CollectiveOpenSourceHardware/LibreSolarBox/batterycase/celltypes/CALB_CAM72/cam72_calb3.png

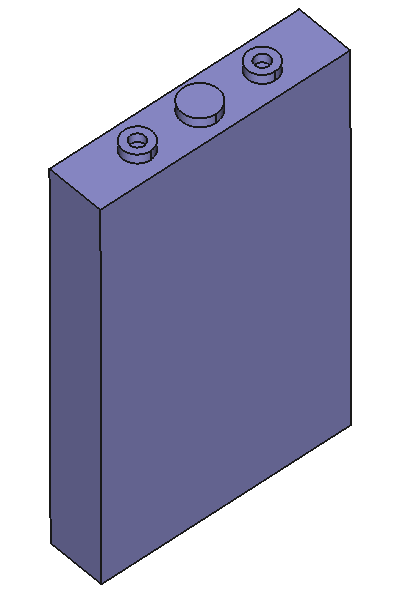
batterycase/celltypes/CALB_CAM72/cam72_calb3.png
