CollectiveOpenSourceHardware/LibreSolarBox/batterycase/celltypes/CALB_CAM72/cam72_calb3_dimensions.png

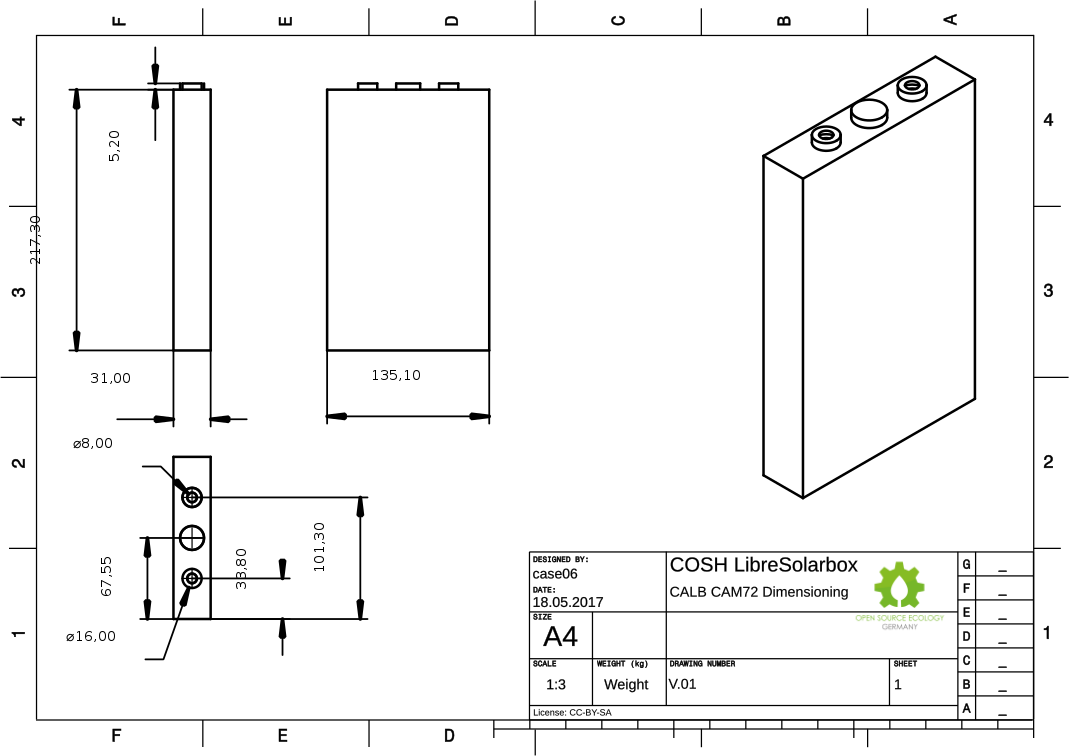
batterycase/celltypes/CALB_CAM72/cam72_calb3_dimensions.png
