CollectiveOpenSourceHardware/LibreSolarBox/batterycase/drawingtemplates/A4_LandscapeTD_cosh.png

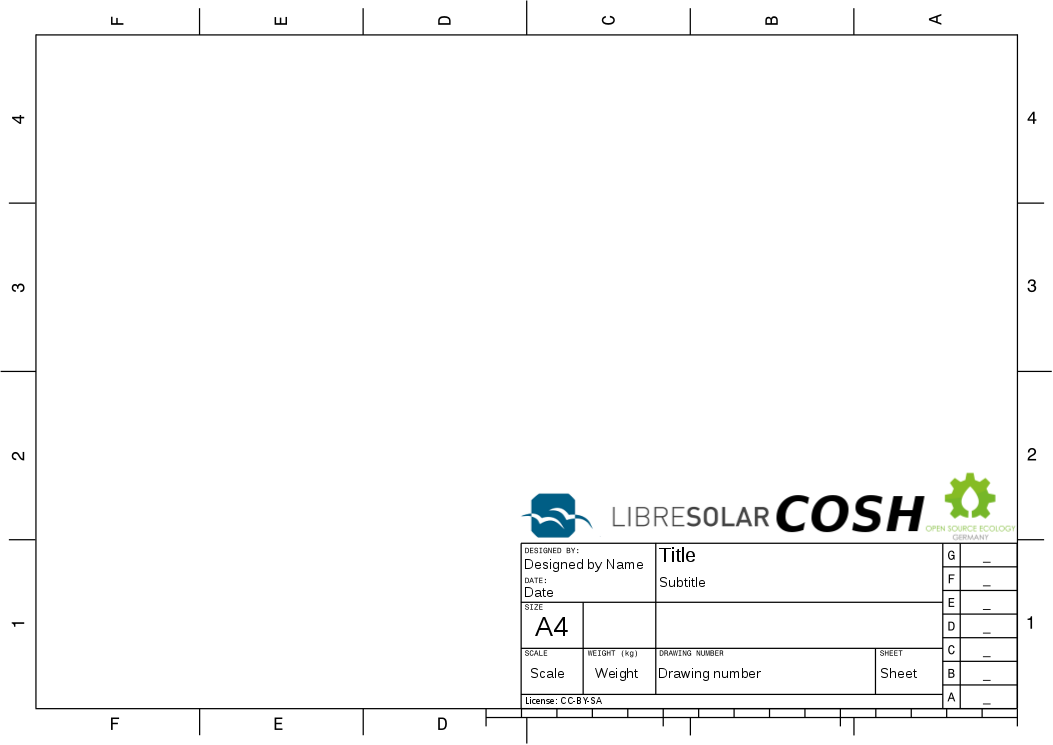
batterycase/drawingtemplates/A4_LandscapeTD_cosh.png
