CollectiveOpenSourceHardware/LibreSolarBox/boxframe/images/IMG_20170920_190103.jpg

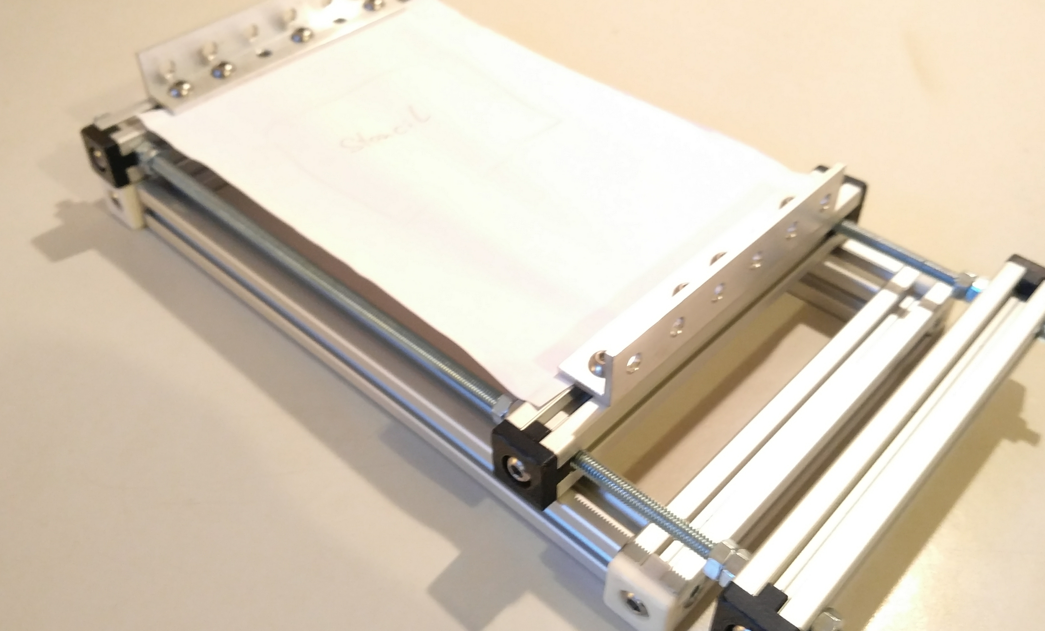
boxframe/images/IMG_20170920_190103.jpg
