CollectiveOpenSourceHardware/LibreSolarBox/boxframe/images/IMG_20170920_190120.jpg

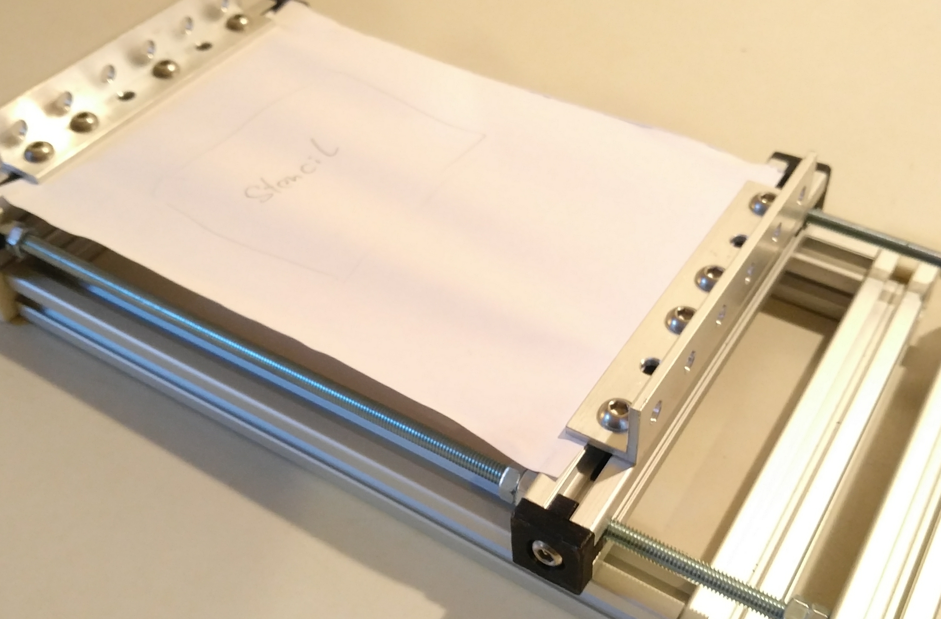
boxframe/images/IMG_20170920_190120.jpg
