CollectiveOpenSourceHardware/LibreSolarBox/boxframe/images/IMG_20170920_190156.jpg

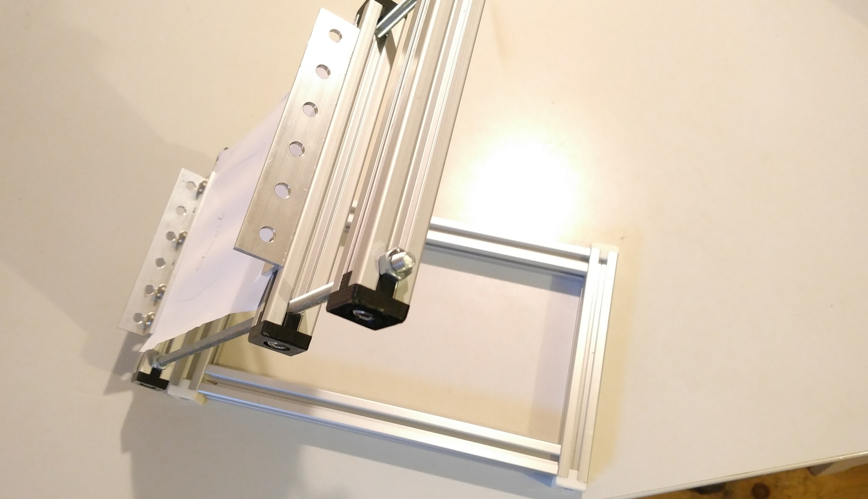
boxframe/images/IMG_20170920_190156.jpg
