CollectiveOpenSourceHardware/LibreSolarBox/boxframe/images/IMG_20170920_190223.jpg

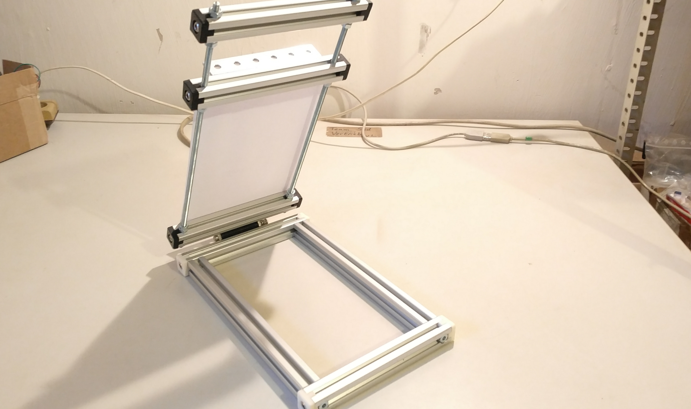
boxframe/images/IMG_20170920_190223.jpg
