CollectiveOpenSourceHardware/LibreSolarBox/boxframe/images/IMG_20170920_190235.jpg

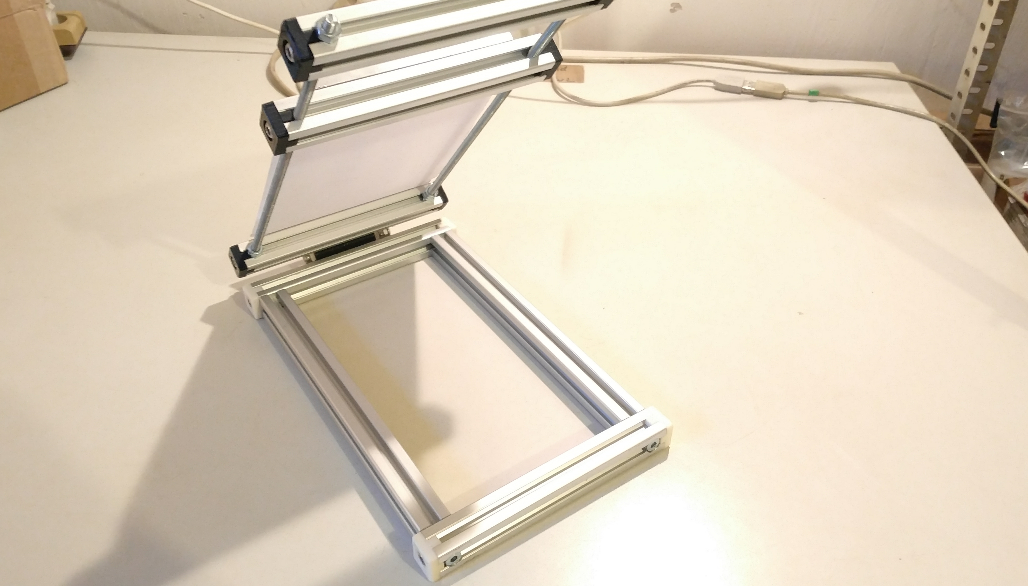
boxframe/images/IMG_20170920_190235.jpg
