CollectiveOpenSourceHardware/LibreSolarBox/boxframe/images/IMG_20170920_190249.jpg

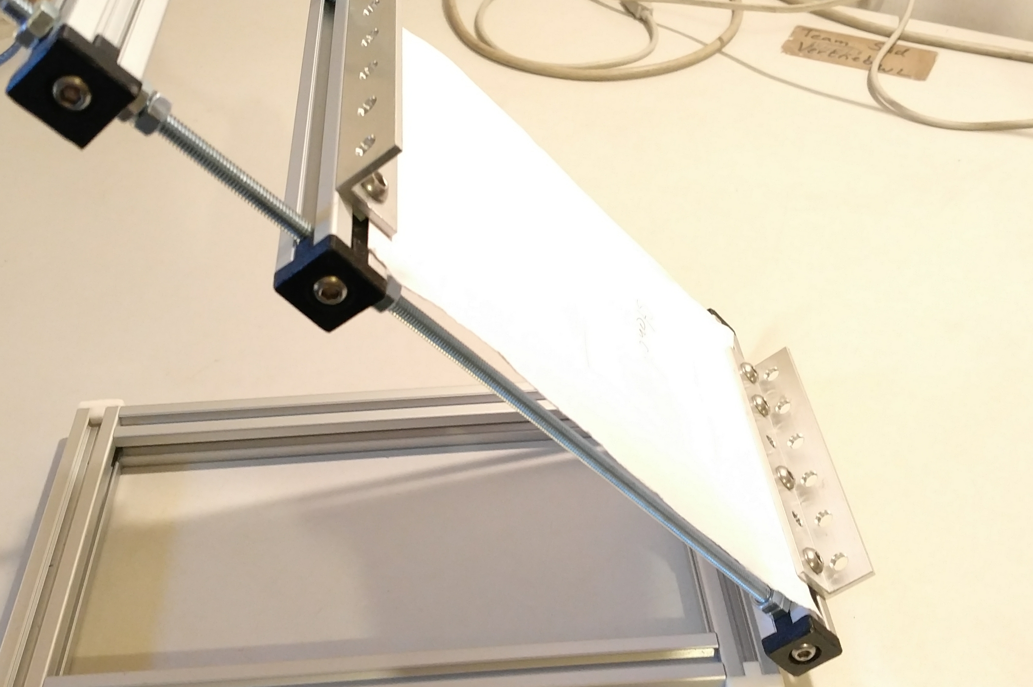
boxframe/images/IMG_20170920_190249.jpg
