CollectiveOpenSourceHardware/LibreSolarBox/boxframe/images/IMG_20170920_190312.jpg

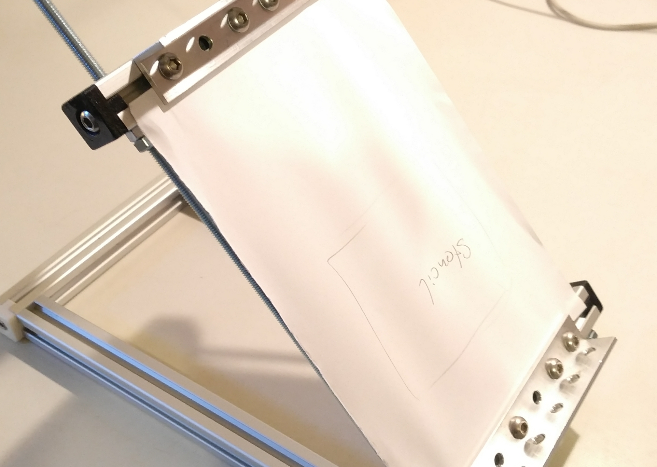
boxframe/images/IMG_20170920_190312.jpg
