CollectiveOpenSourceHardware/LibreSolarBox/boxframe/images/IMG_20170920_190359.jpg

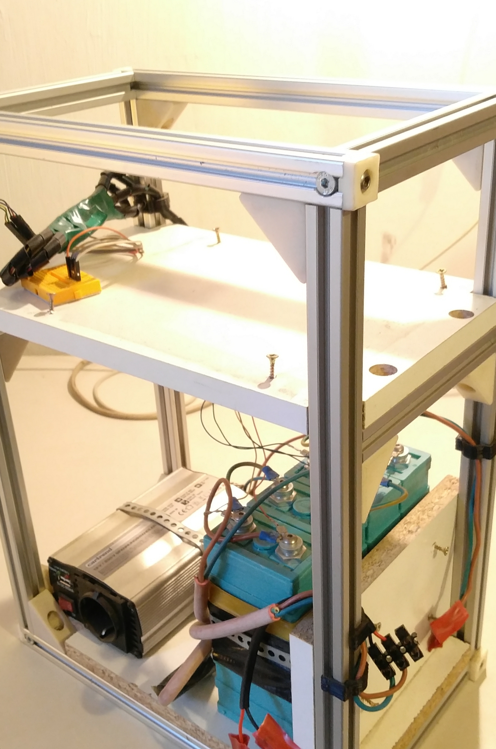
boxframe/images/IMG_20170920_190359.jpg
