CollectiveOpenSourceHardware/LibreSolarBox/boxframe/images/IMG_20170920_190408.jpg

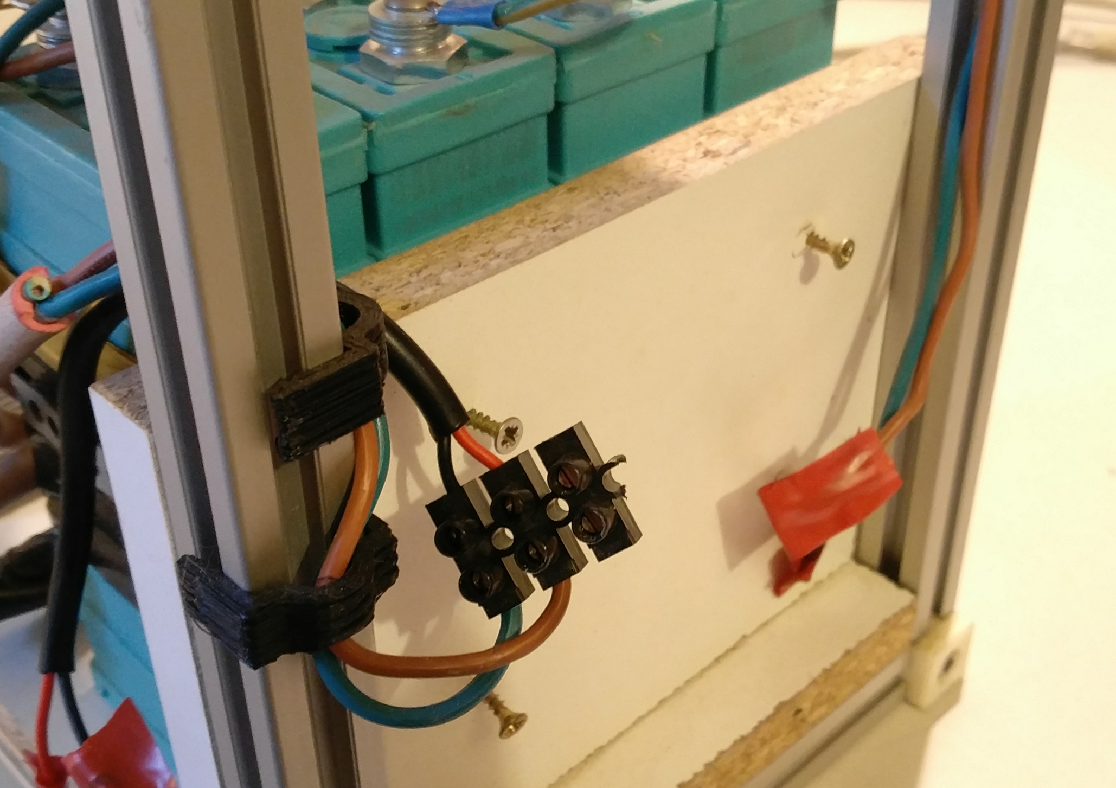
boxframe/images/IMG_20170920_190408.jpg
