CollectiveOpenSourceHardware/LibreSolarBox/boxframe/images/IMG_20170920_190428.jpg

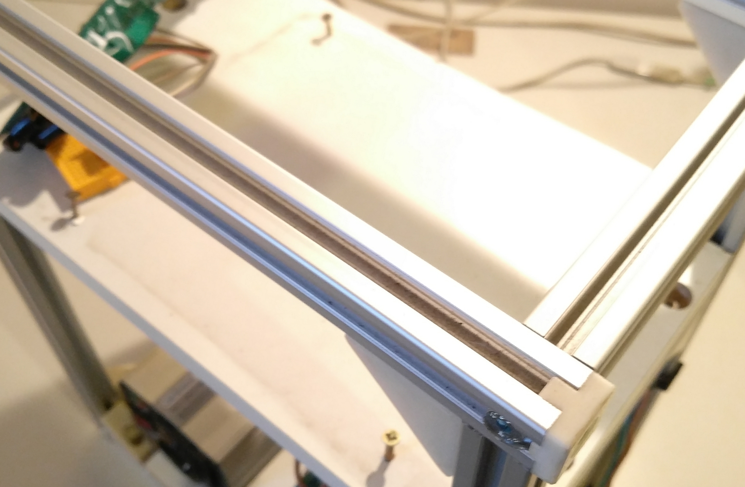
boxframe/images/IMG_20170920_190428.jpg
