CollectiveOpenSourceHardware/LibreSolarBox/boxframe/images/IMG_20170920_190441.jpg

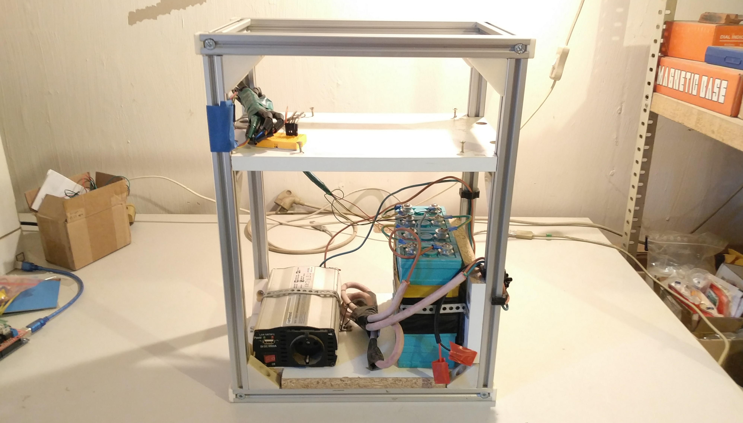
boxframe/images/IMG_20170920_190441.jpg
