CollectiveOpenSourceHardware/LibreSolarBox/boxframe/panelsupport/screw_tslot2.png

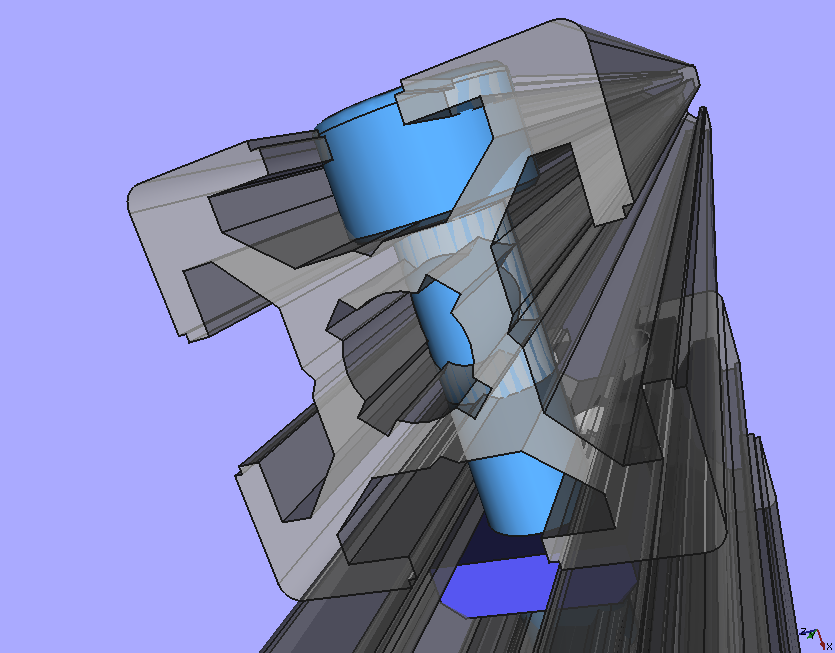
boxframe/panelsupport/screw_tslot2.png
