CollectiveOpenSourceHardware/LibreSolarBox/boxframe/panelsupport/screw_tslot3.png

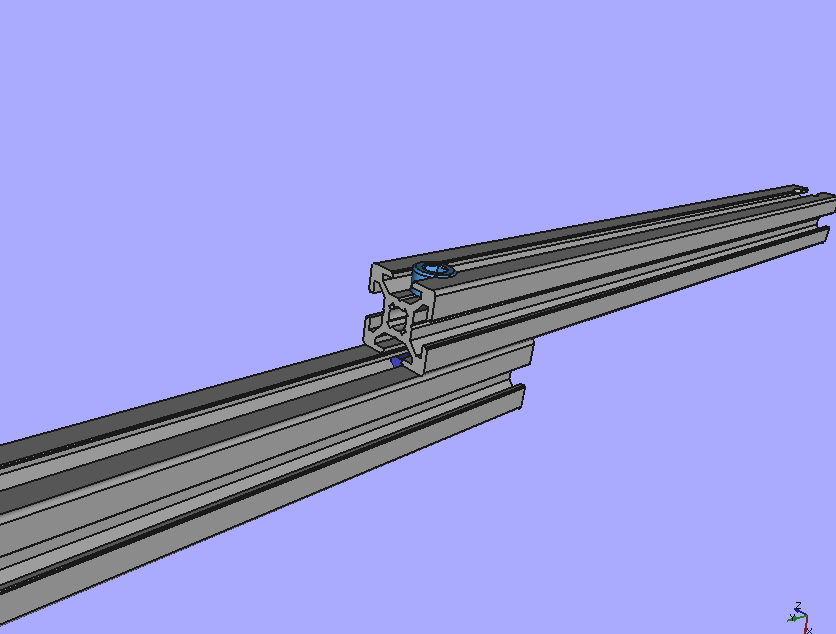
boxframe/panelsupport/screw_tslot3.png
