CollectiveOpenSourceHardware/LibreSolarBox/boxframe/panelsupport/screw_tslot.png

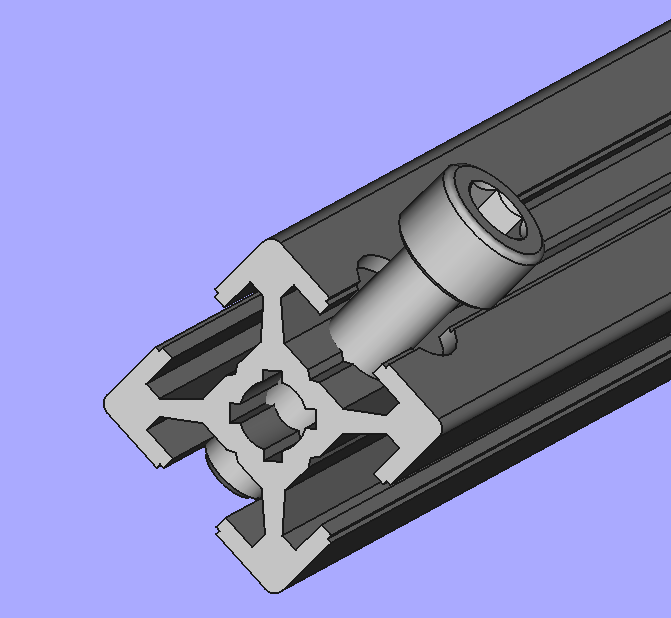
boxframe/panelsupport/screw_tslot.png
