CollectiveOpenSourceHardware/LibreSolarBox/boxframe/upkframe_v6/images/batterymount1c.png

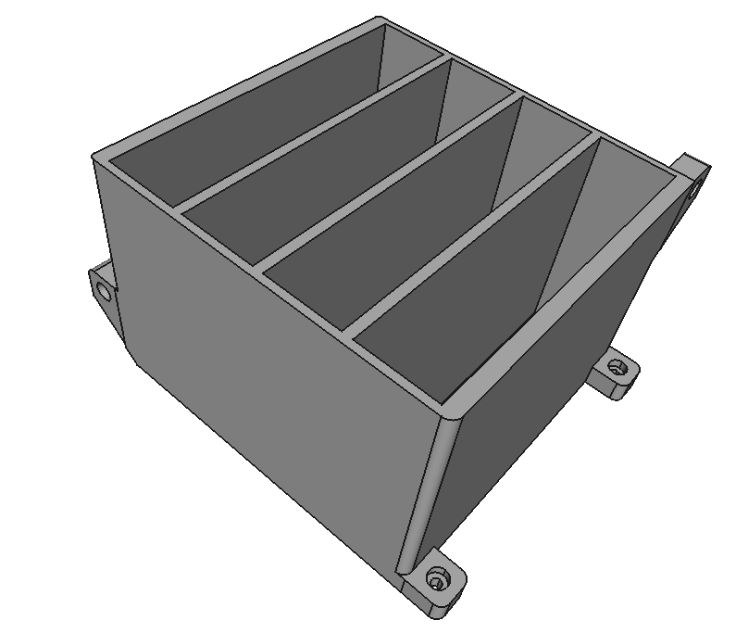
boxframe/upkframe_v6/images/batterymount1c.png
