CollectiveOpenSourceHardware/LibreSolarBox/boxframe/upkframe_v6/images/batterymount_top_0.1.PNG

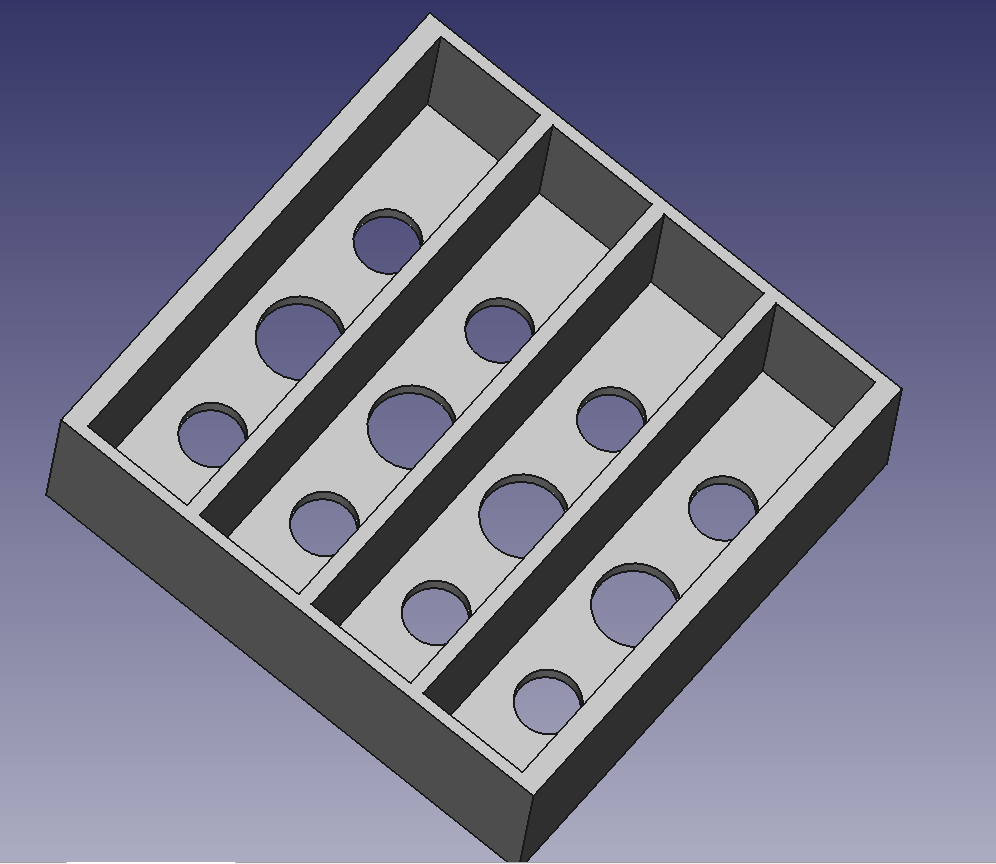
boxframe/upkframe_v6/images/batterymount_top_0.1.PNG
