CollectiveOpenSourceHardware/LibreSolarBox/boxframe/upkframe_v6/images/frontback_dim.png

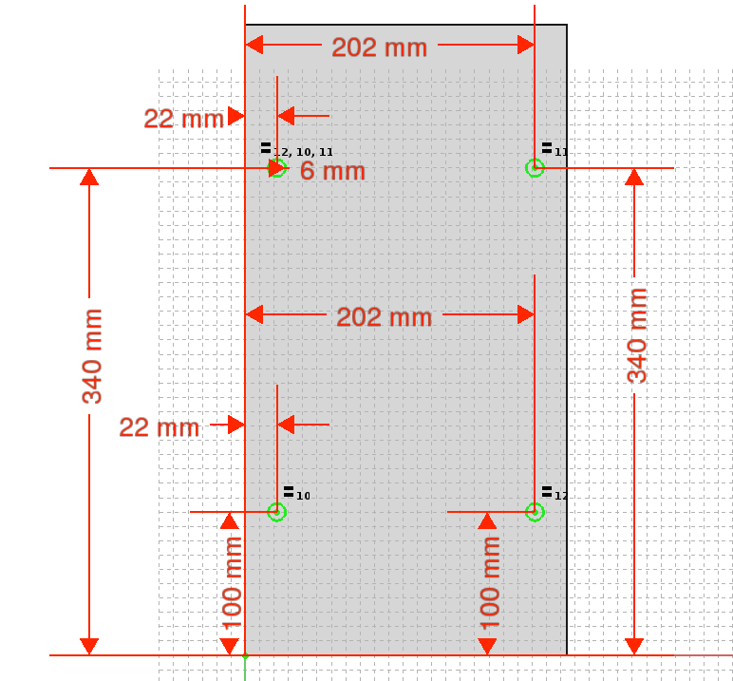
boxframe/upkframe_v6/images/frontback_dim.png
