CollectiveOpenSourceHardware/LibreSolarBox/boxframe/upkframe_v6/images/frontback_ifmount_closeup.png

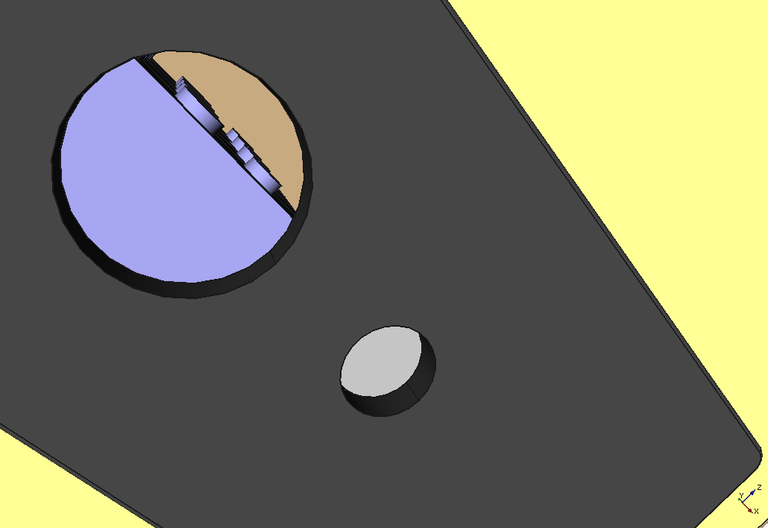
boxframe/upkframe_v6/images/frontback_ifmount_closeup.png
