CollectiveOpenSourceHardware/LibreSolarBox/boxframe/upkframe_v6/images/frontback_ifmount_front.png

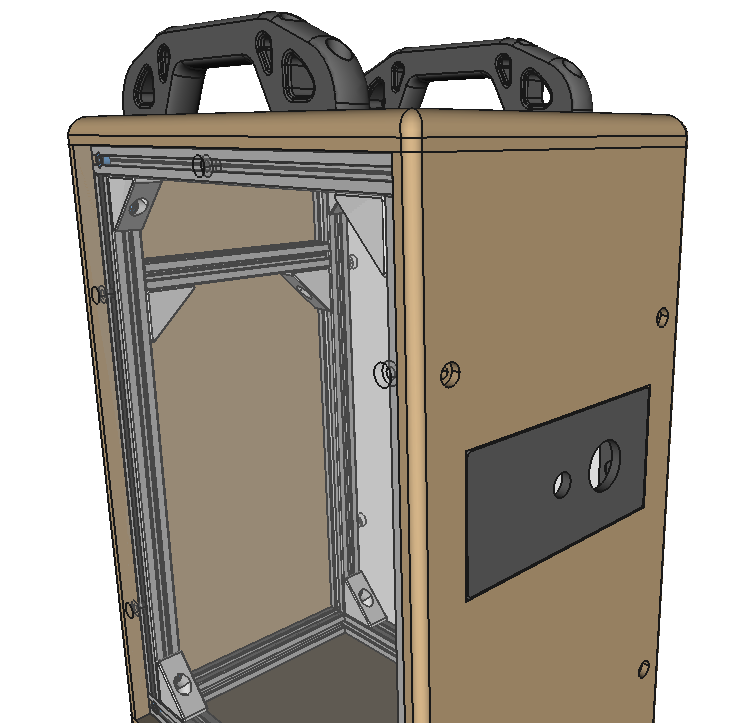
boxframe/upkframe_v6/images/frontback_ifmount_front.png
