CollectiveOpenSourceHardware/LibreSolarBox/boxframe/upkframe_v6/images/frontback_ifmount_plate.png

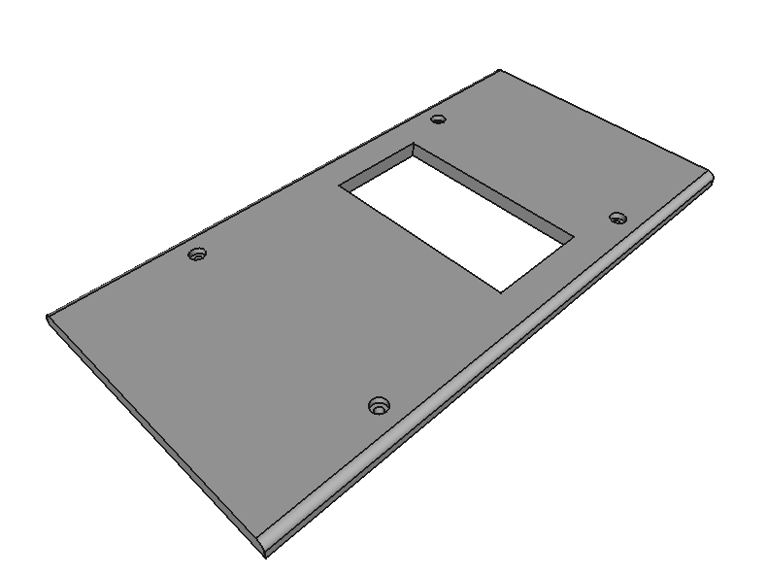
boxframe/upkframe_v6/images/frontback_ifmount_plate.png
