CollectiveOpenSourceHardware/LibreSolarBox/boxframe/upkframe_v6/images/frontbackNG2_dim.png

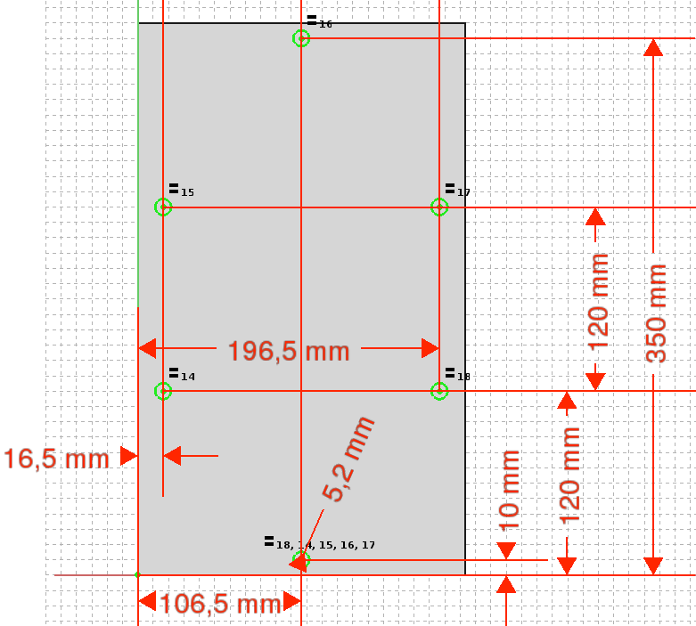
boxframe/upkframe_v6/images/frontbackNG2_dim.png
