CollectiveOpenSourceHardware/LibreSolarBox/boxframe/upkframe_v6/images/gateway_case_buttom_0.1.PNG

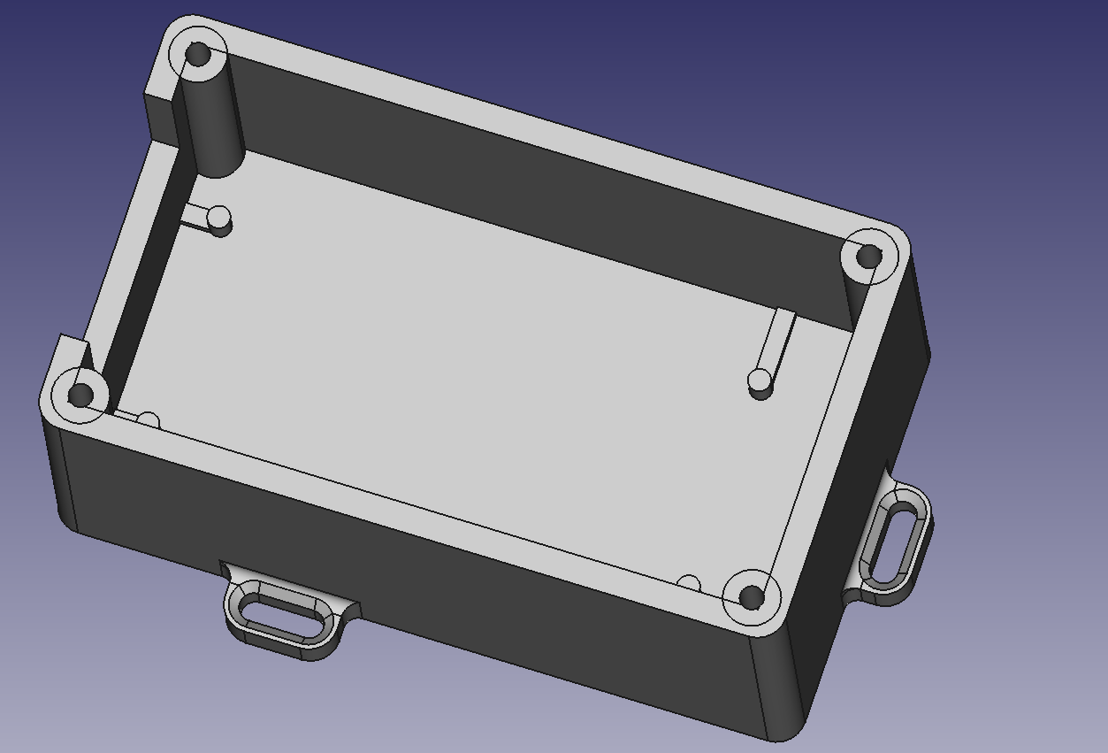
boxframe/upkframe_v6/images/gateway_case_buttom_0.1.PNG
