CollectiveOpenSourceHardware/LibreSolarBox/boxframe/upkframe_v6/images/gateway_case_top_0.1.PNG

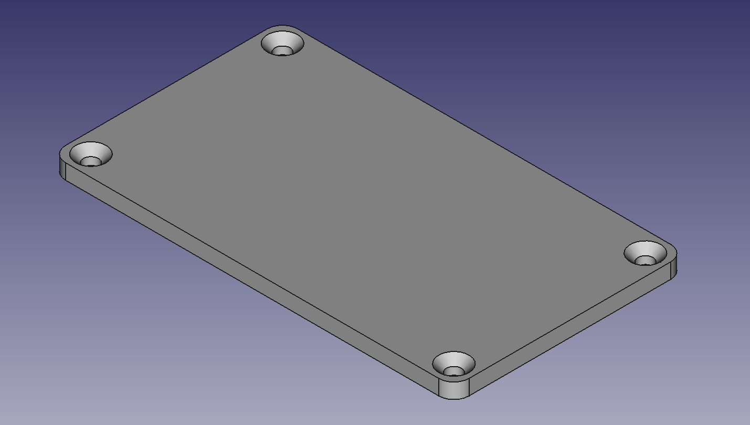
boxframe/upkframe_v6/images/gateway_case_top_0.1.PNG
