CollectiveOpenSourceHardware/LibreSolarBox/boxframe/upkframe_v6/images/ifmount1f_back_dim.png

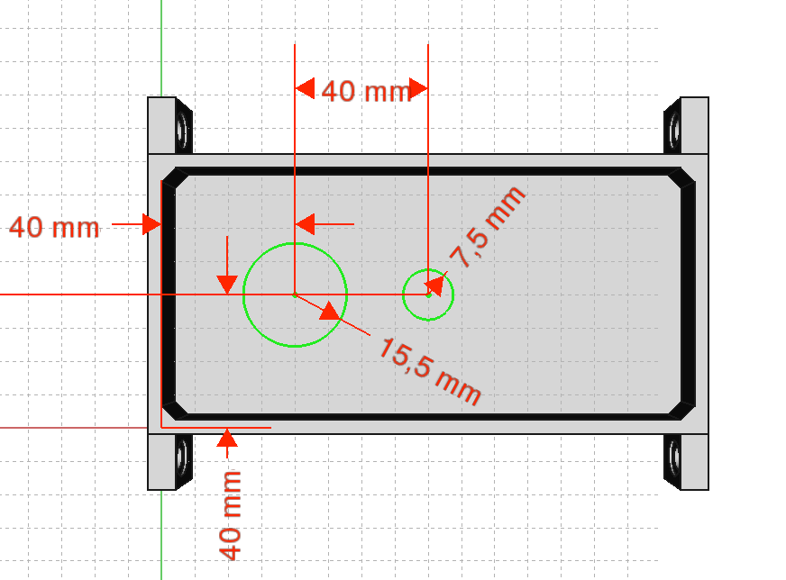
boxframe/upkframe_v6/images/ifmount1f_back_dim.png
