CollectiveOpenSourceHardware/LibreSolarBox/boxframe/upkframe_v6/images/ifmount1f_dim.png

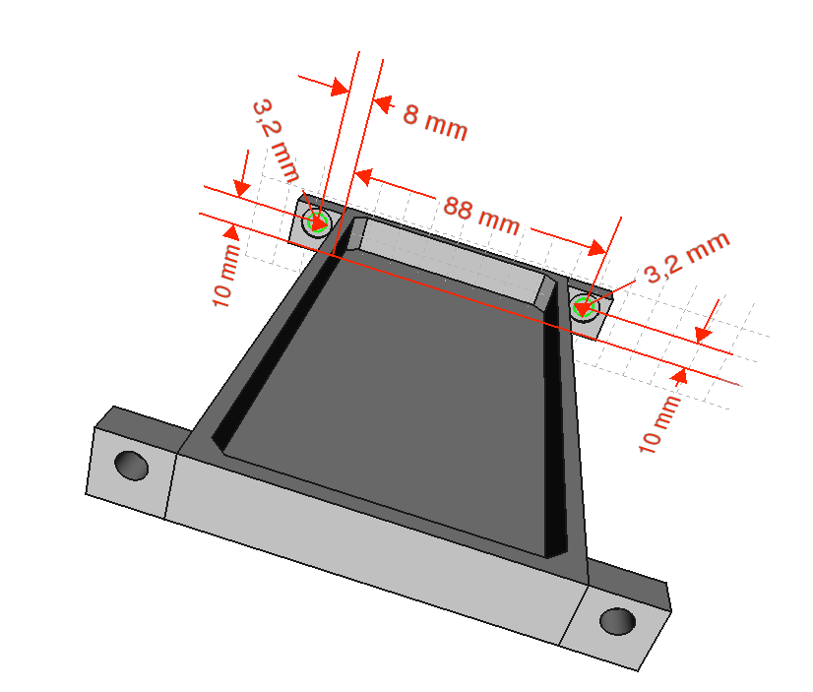
boxframe/upkframe_v6/images/ifmount1f_dim.png
