CollectiveOpenSourceHardware/LibreSolarBox/boxframe/upkframe_v6/images/ifmountNG1b.png

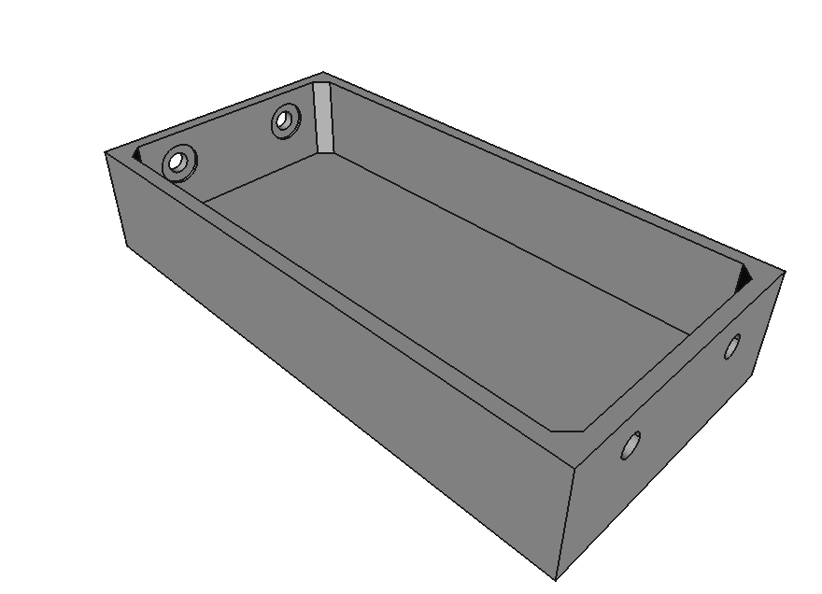
boxframe/upkframe_v6/images/ifmountNG1b.png
