CollectiveOpenSourceHardware/LibreSolarBox/boxframe/upkframe_v6/images/ifmountNG1b_front.png

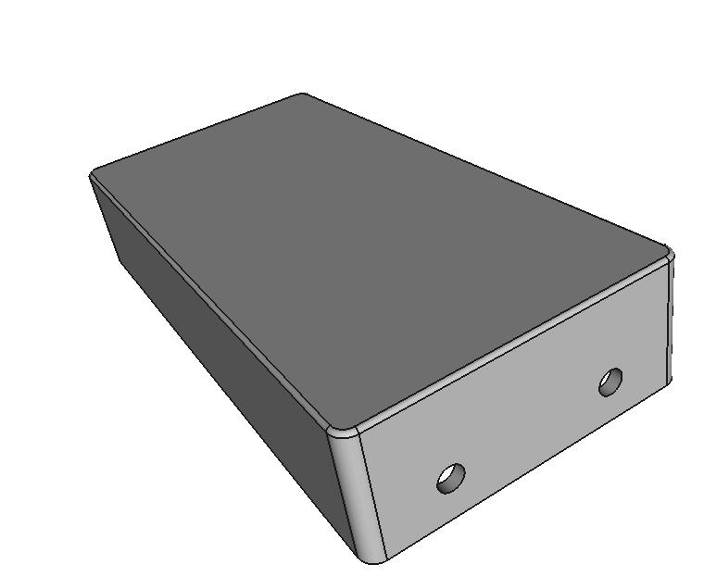
boxframe/upkframe_v6/images/ifmountNG1b_front.png
