CollectiveOpenSourceHardware/LibreSolarBox/boxframe/upkframe_v6/images/ifmountNG1c.png

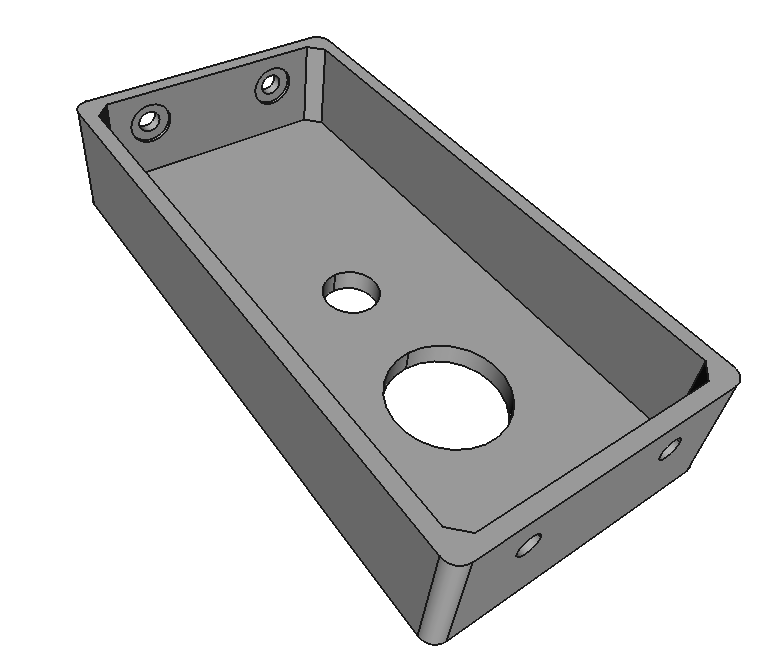
boxframe/upkframe_v6/images/ifmountNG1c.png
