CollectiveOpenSourceHardware/LibreSolarBox/boxframe/upkframe_v6/images/ifmountNG1c_front.png

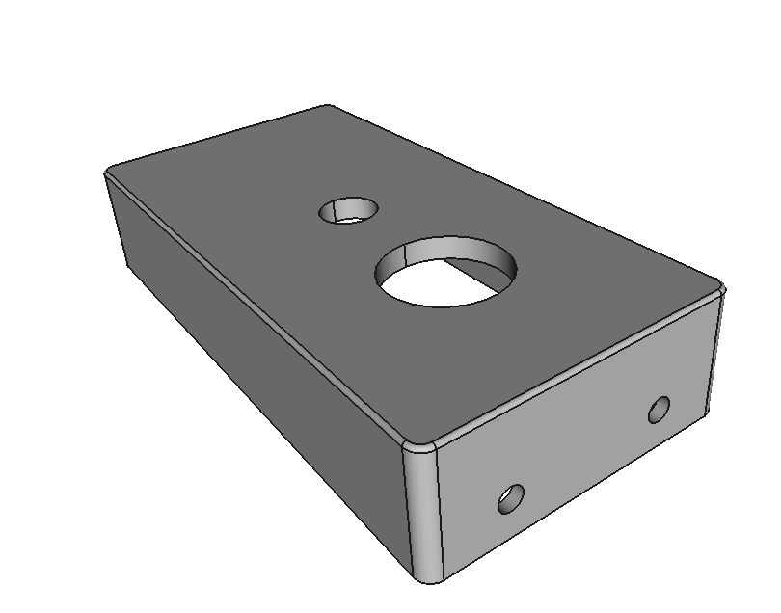
boxframe/upkframe_v6/images/ifmountNG1c_front.png
