CollectiveOpenSourceHardware/LibreSolarBox/boxframe/upkframe_v6/images/seitenwand1c.png

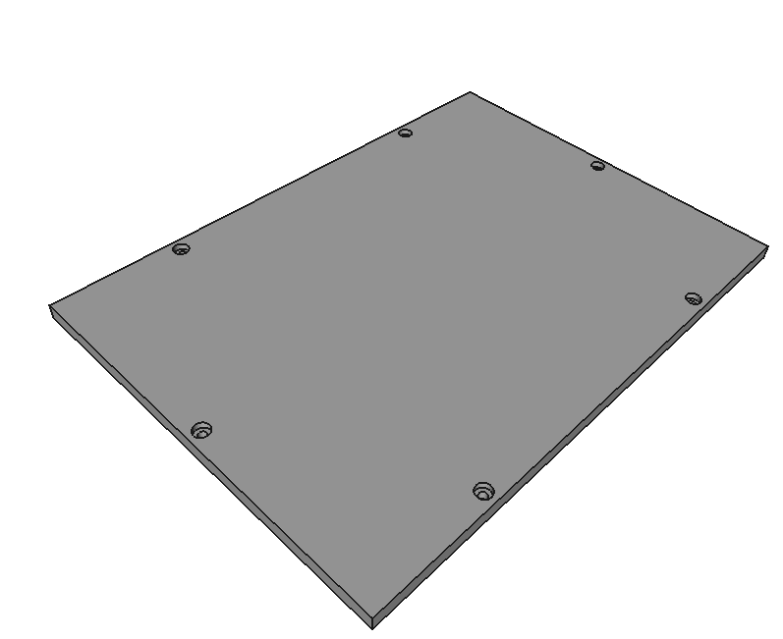
boxframe/upkframe_v6/images/seitenwand1c.png
