CollectiveOpenSourceHardware/LibreSolarBox/boxframe/upkframe_v6/images/seitenwand1c_dim.png

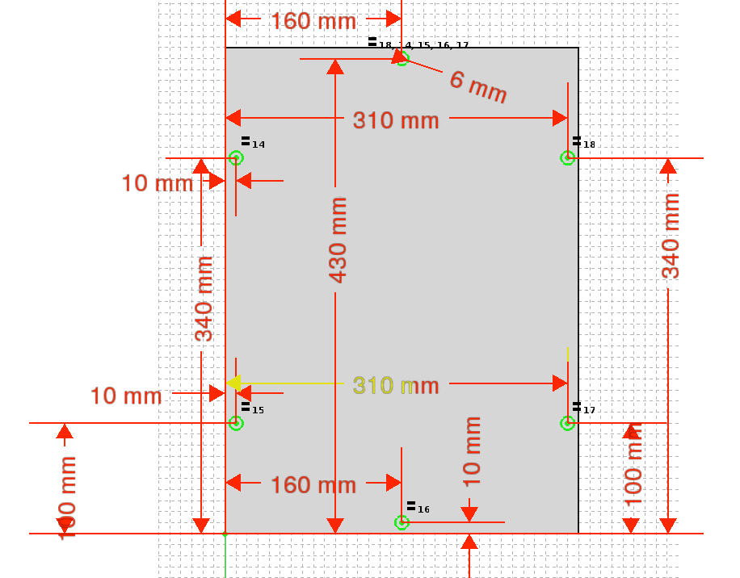
boxframe/upkframe_v6/images/seitenwand1c_dim.png
