CollectiveOpenSourceHardware/LibreSolarBox/boxframe/upkframe_v6/images/seitenwand_dim.png

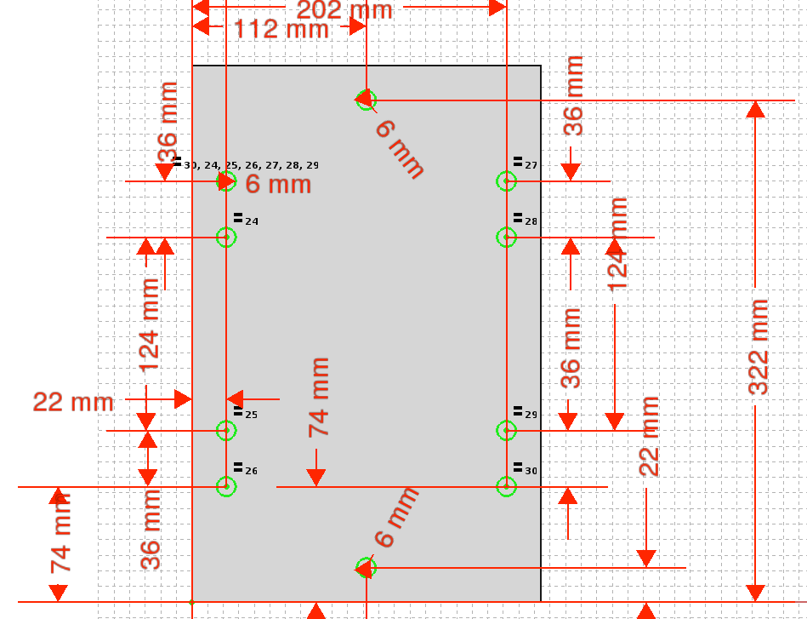
boxframe/upkframe_v6/images/seitenwand_dim.png
