CollectiveOpenSourceHardware/LibreSolarBox/boxframe/upkframe_v6/images/sideCoverNG2.png

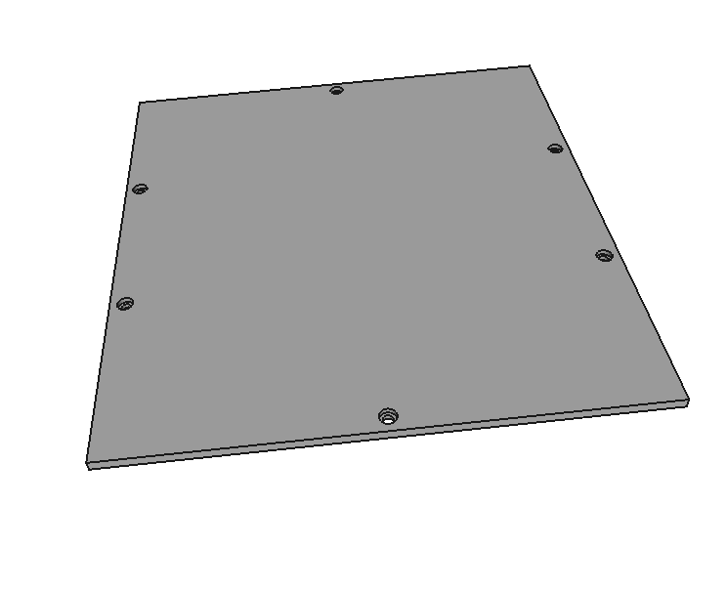
boxframe/upkframe_v6/images/sideCoverNG2.png
