CollectiveOpenSourceHardware/LibreSolarBox/boxframe/upkframe_v6/images/sideCoverNG2_dim.png

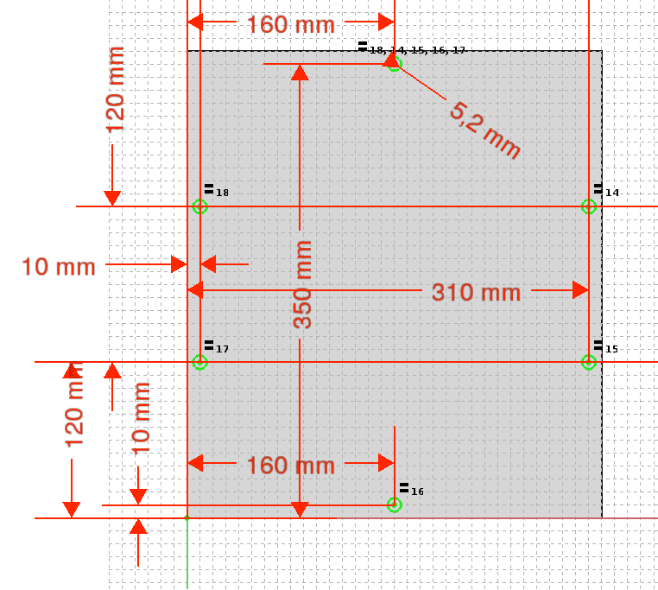
boxframe/upkframe_v6/images/sideCoverNG2_dim.png
