CollectiveOpenSourceHardware/LibreSolarBox/boxframe/upkframe_v6/images/topbottom.png

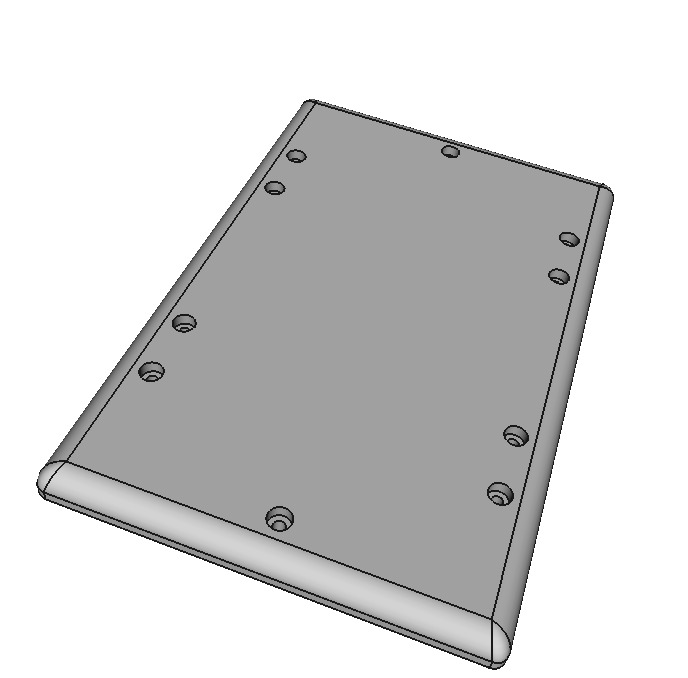
boxframe/upkframe_v6/images/topbottom.png
