CollectiveOpenSourceHardware/LibreSolarBox/boxframe/upkframe_v6/images/topbottomNG2_dim.png

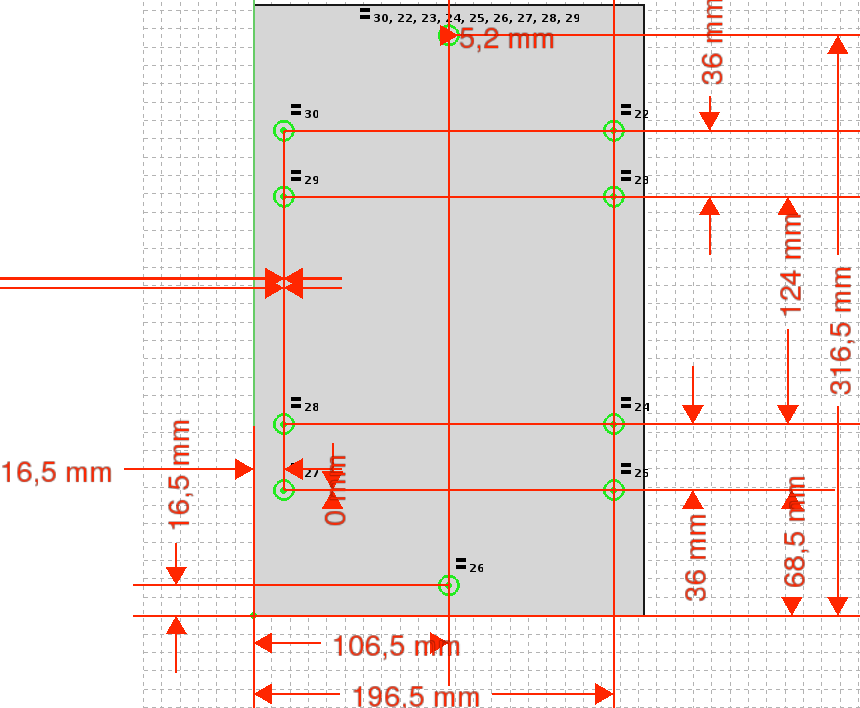
boxframe/upkframe_v6/images/topbottomNG2_dim.png
