CollectiveOpenSourceHardware/LibreSolarBox/boxframe/upkframe_v6/images/topbottomNG2b.png

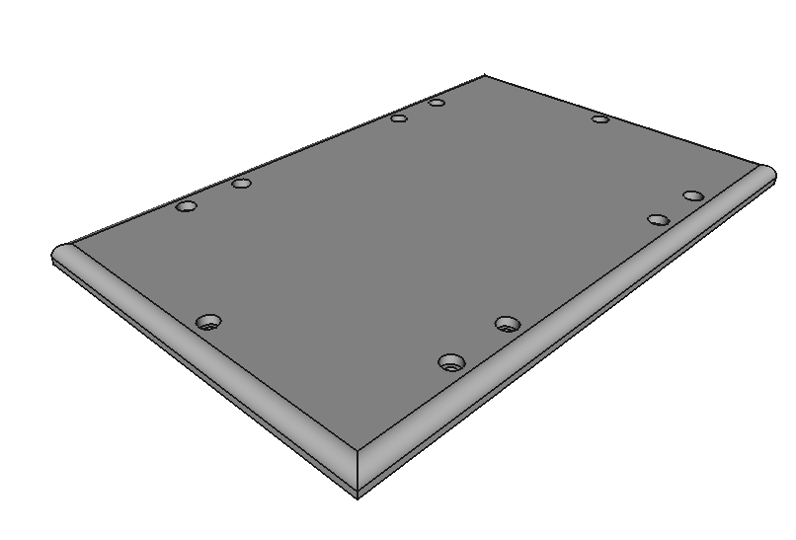
boxframe/upkframe_v6/images/topbottomNG2b.png
