CollectiveOpenSourceHardware/LibreSolarBox/boxframe/upkframe_v6/images/UPKframe5.png

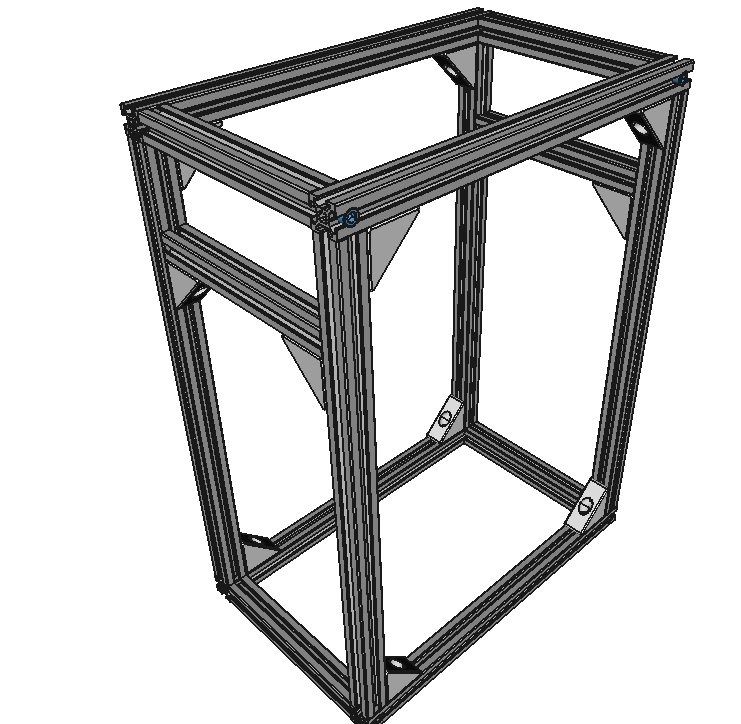
boxframe/upkframe_v6/images/UPKframe5.png
