CollectiveOpenSourceHardware/LibreSolarBox/boxframe/upkframe_v6/images/UPKframeNG1b.png

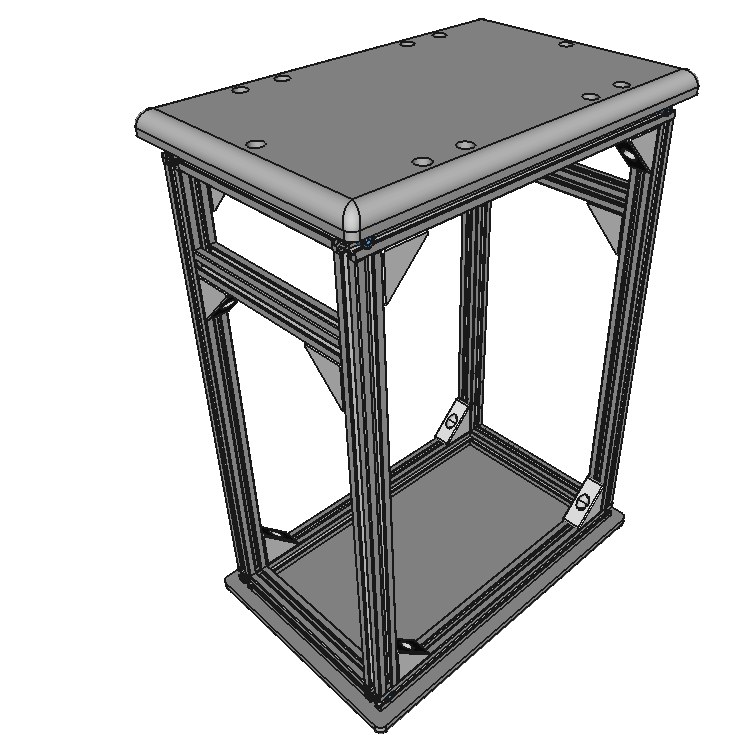
boxframe/upkframe_v6/images/UPKframeNG1b.png
