CollectiveOpenSourceHardware/LibreSolarBox/boxframe/upkframe_v6/images/UPKframeNG1c.png

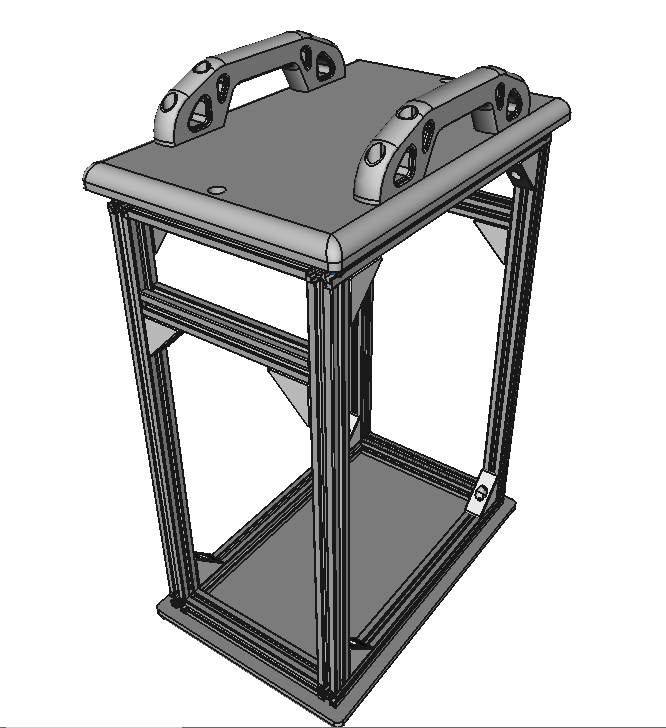
boxframe/upkframe_v6/images/UPKframeNG1c.png
