CollectiveOpenSourceHardware/LibreSolarBox/boxframe/upkframe_v6/images/UPKframeNG1e.png

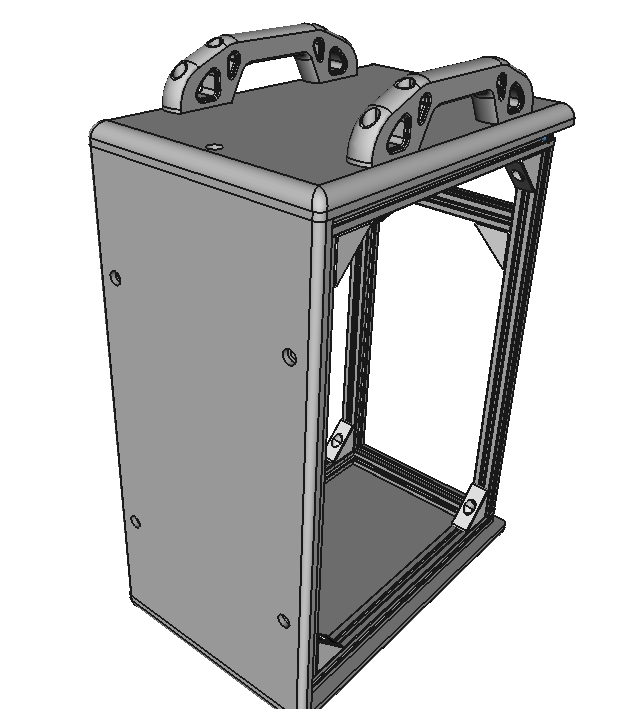
boxframe/upkframe_v6/images/UPKframeNG1e.png
