CollectiveOpenSourceHardware/LibreSolarBox/boxframe/upkframe_v6/images/UPKframeNG1e_flip.png

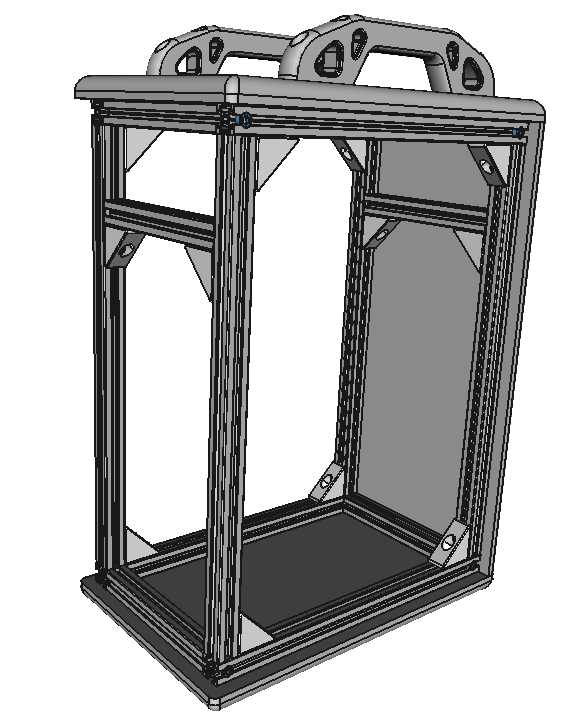
boxframe/upkframe_v6/images/UPKframeNG1e_flip.png
