CollectiveOpenSourceHardware/LibreSolarBox/boxframe/upkframe_v6/images/UPKframeNG1f.png

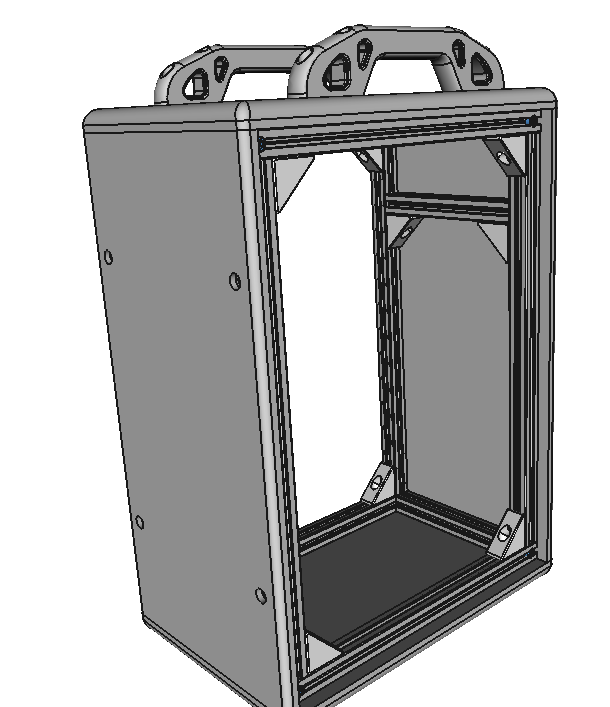
boxframe/upkframe_v6/images/UPKframeNG1f.png
