CollectiveOpenSourceHardware/LibreSolarBox/boxframe/upkframe_v6/images/UPKframeNG1f_back.png

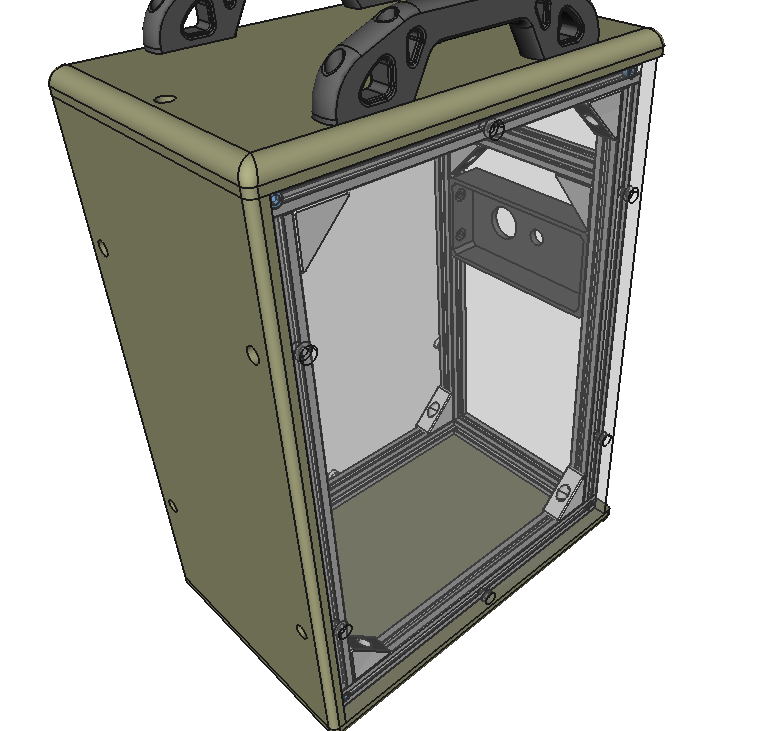
boxframe/upkframe_v6/images/UPKframeNG1f_back.png
