CollectiveOpenSourceHardware/LibreSolarBox/boxframe/upkframe_v6/images/UPKframeNG2b.png

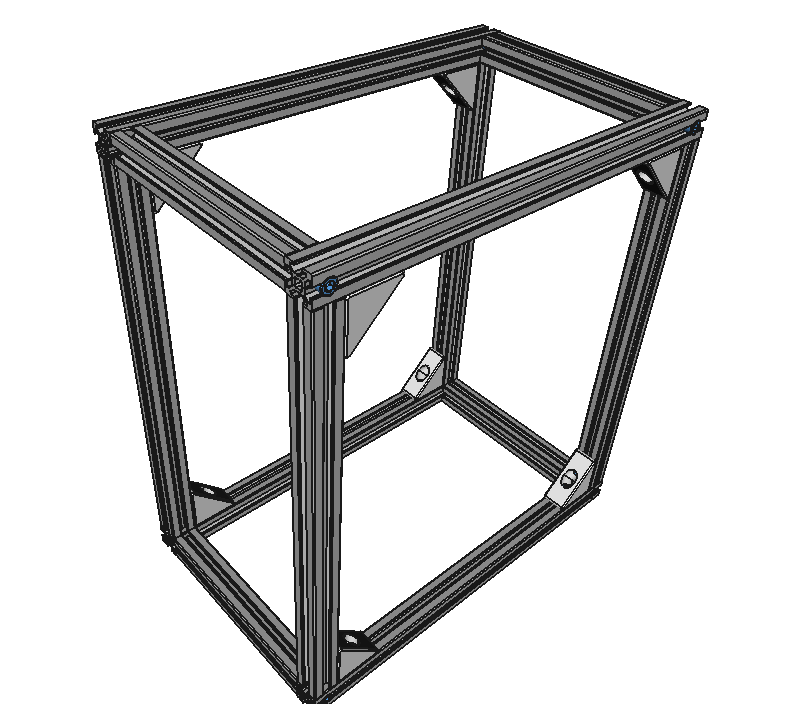
boxframe/upkframe_v6/images/UPKframeNG2b.png
