CollectiveOpenSourceHardware/LibreSolarBox/boxframe/upkframe_v6/images/UPKframeNG2d.png

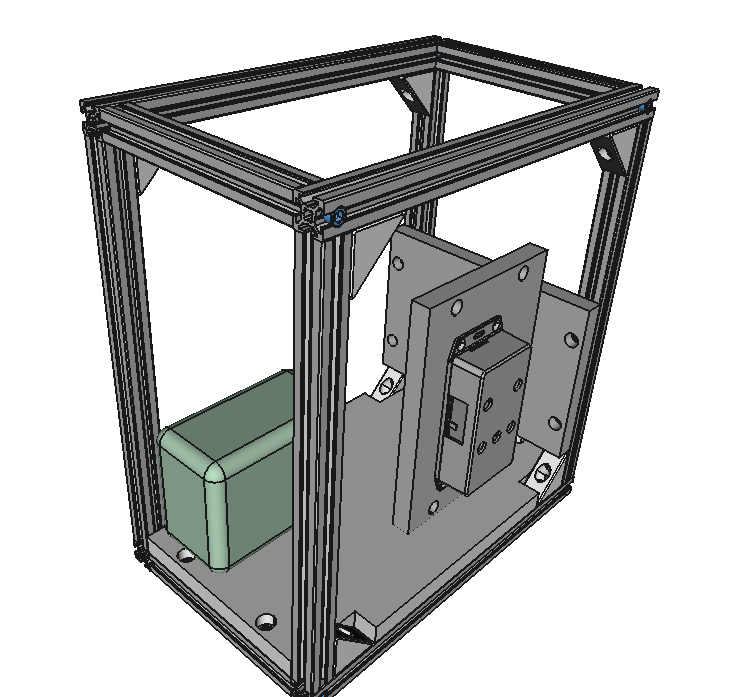
boxframe/upkframe_v6/images/UPKframeNG2d.png
