CollectiveOpenSourceHardware/LibreSolarBox/boxframe/upkframe_v6/images/UPKframeNG2e.png

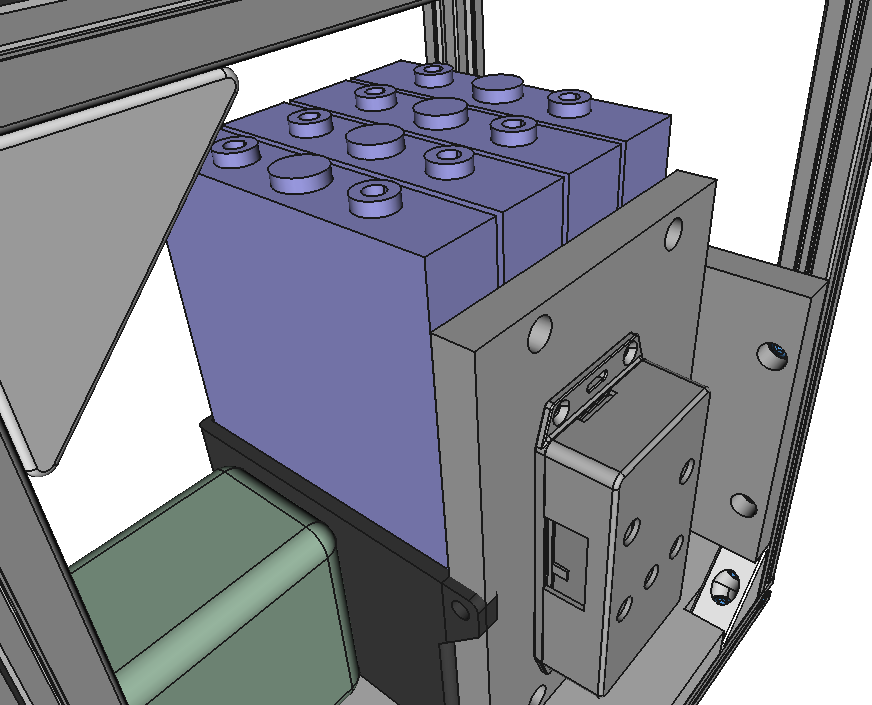
boxframe/upkframe_v6/images/UPKframeNG2e.png
