CollectiveOpenSourceHardware/LibreSolarBox/boxframe/upkframe_v6/images/UPKframeNG2e_closeup2.png

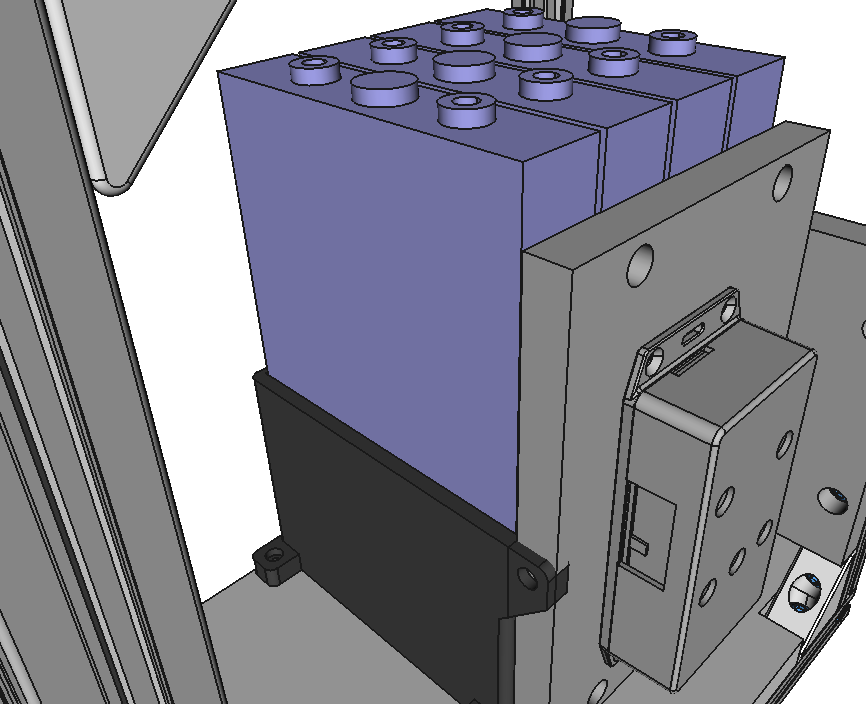
boxframe/upkframe_v6/images/UPKframeNG2e_closeup2.png
