CollectiveOpenSourceHardware/LibreSolarBox/boxframe/upkframe_v6/images/UPKframeNG2e_closeup.png

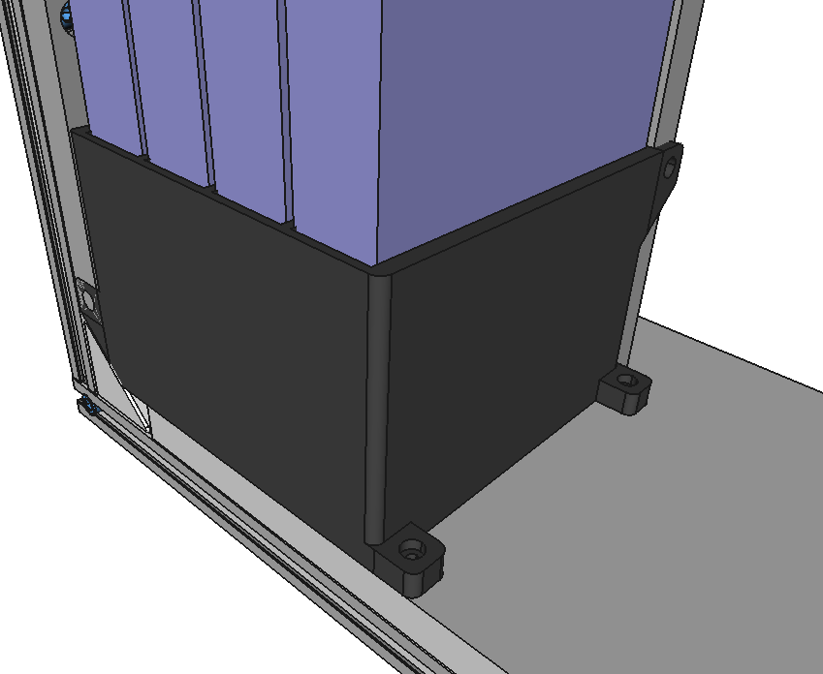
boxframe/upkframe_v6/images/UPKframeNG2e_closeup.png
