CollectiveOpenSourceHardware/LibreSolarBox/boxframe/upkframe_v6/images/UPKframeNG2h_closeup.png

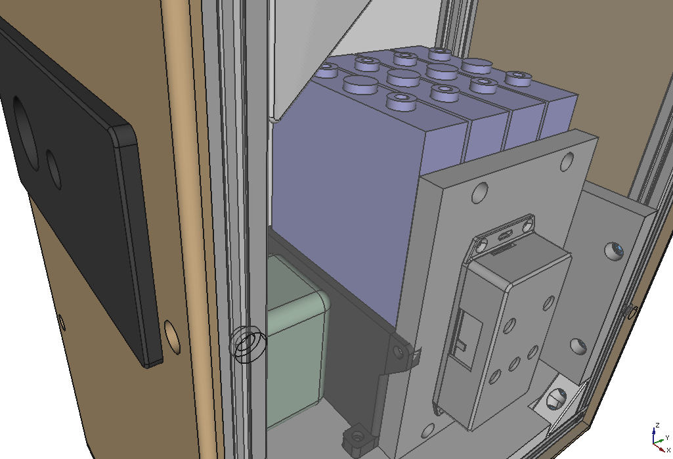
boxframe/upkframe_v6/images/UPKframeNG2h_closeup.png
