CollectiveOpenSourceHardware/LibreSolarBox/boxframe/upkframe_v6/images/UPKframeNG2j.png

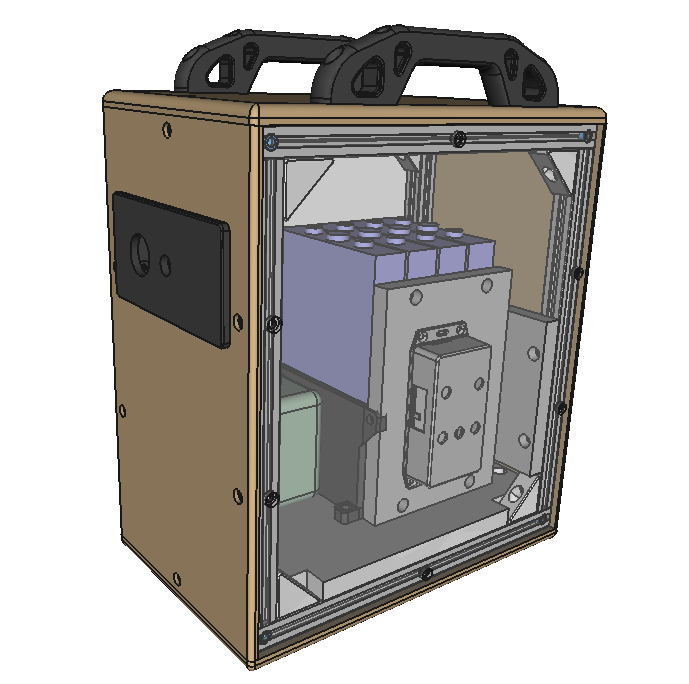
boxframe/upkframe_v6/images/UPKframeNG2j.png
