CollectiveOpenSourceHardware/LibreSolarBox/boxframe/upkframe_v6/images/UPKframeNG2j_back.png

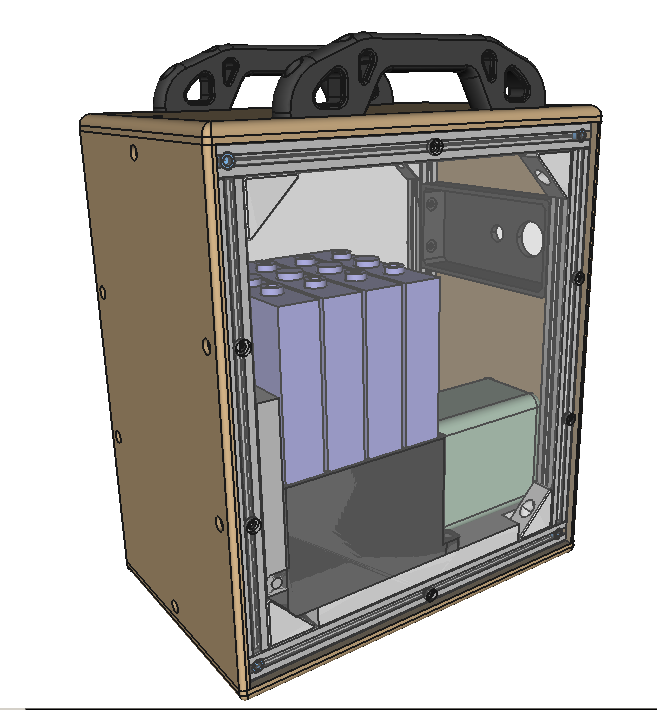
boxframe/upkframe_v6/images/UPKframeNG2j_back.png
