CollectiveOpenSourceHardware/LibreSolarBox/boxframe/upkframe_v6/images/UPKframeNGg.png

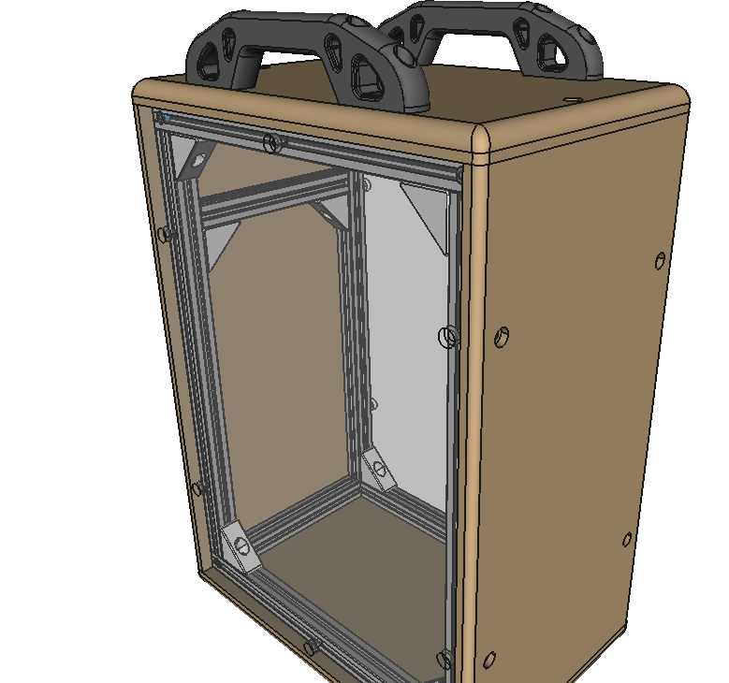
boxframe/upkframe_v6/images/UPKframeNGg.png
