CollectiveOpenSourceHardware/LibreSolarBox/boxframe/upkframe_v6/images/UPKframeNGh.png

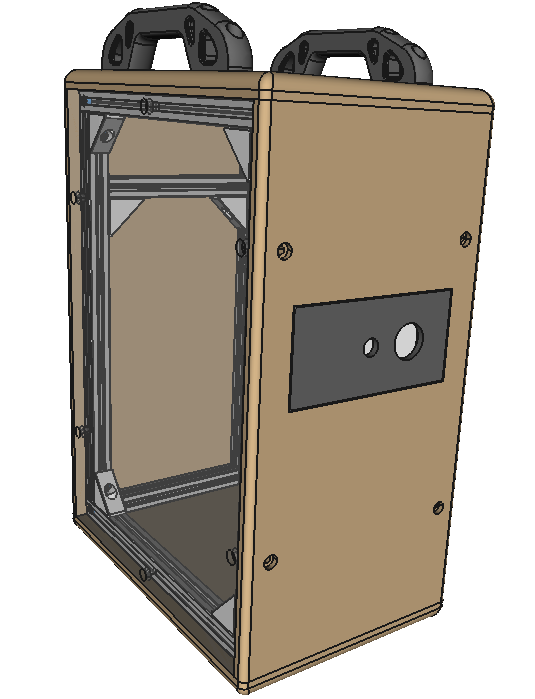
boxframe/upkframe_v6/images/UPKframeNGh.png
