CollectiveOpenSourceHardware/LibreSolarBox/boxframe/upkframe_v6/images/UPKframeNGh_closeup.png

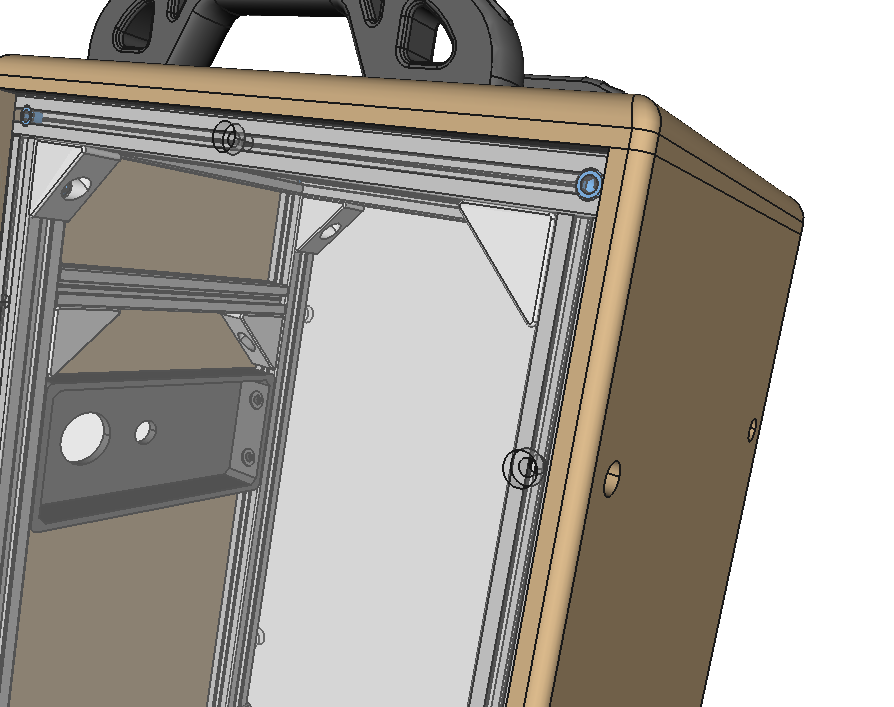
boxframe/upkframe_v6/images/UPKframeNGh_closeup.png
