CollectiveOpenSourceHardware/LibreSolarBox/boxframe/upkframe_v6/images/UPKframeNGh_noplexi.png

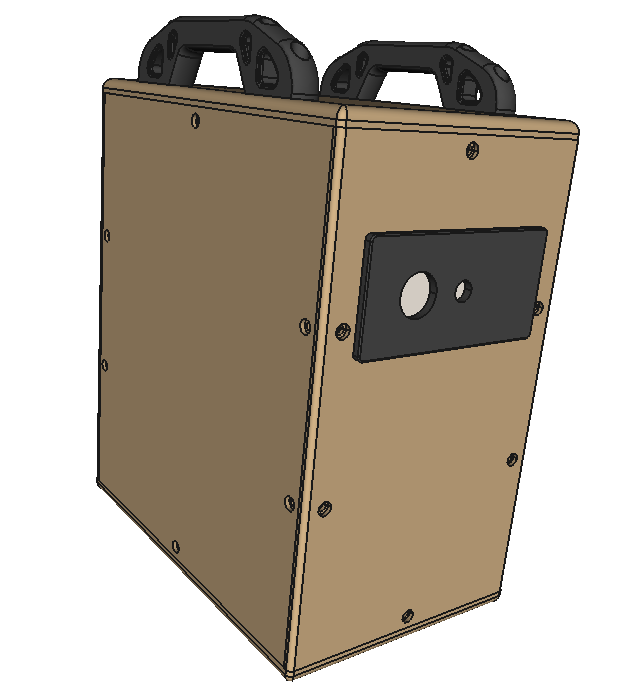
boxframe/upkframe_v6/images/UPKframeNGh_noplexi.png
