CollectiveOpenSourceHardware/LibreSolarBox/boxframe/upkframe_v6/images/UPKframeNGi.png

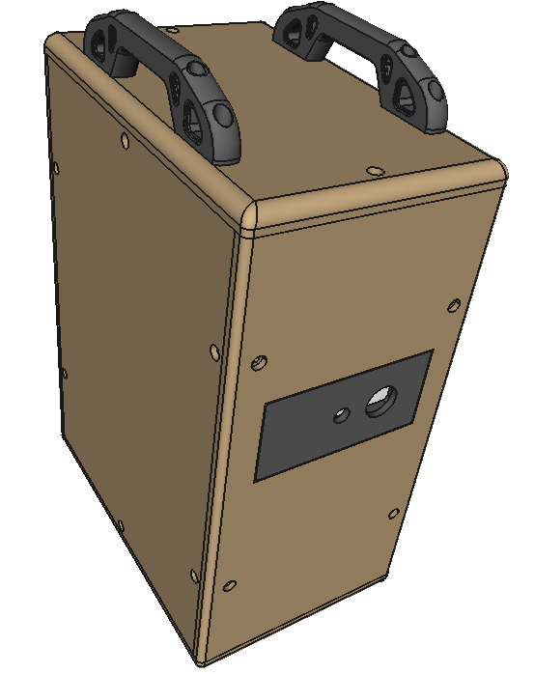
boxframe/upkframe_v6/images/UPKframeNGi.png
