CollectiveOpenSourceHardware/LibreSolarBox/Solar Box_FreeCAD Design/Battery_Case_Holder_FreeCAD_Design/Capture_Battery Case_Holder_v_4_.PNG

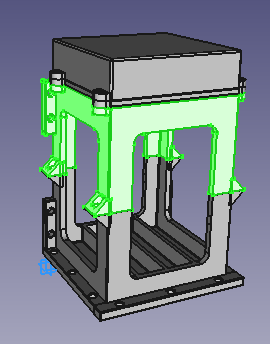
Solar Box_FreeCAD Design/Battery_Case_Holder_FreeCAD_Design/Capture_Battery Case_Holder_v_4_.PNG
