CollectiveOpenSourceHardware/LibreSolarBox/Solar Box_FreeCAD Design/Battery_Case_Holder_FreeCAD_Design/Capture_Cover_part_slot.PNG

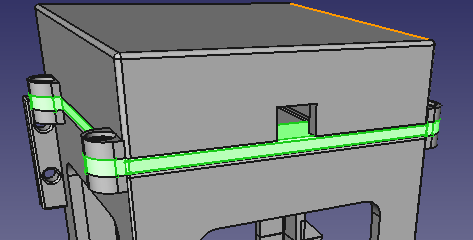
Solar Box_FreeCAD Design/Battery_Case_Holder_FreeCAD_Design/Capture_Cover_part_slot.PNG
