CollectiveOpenSourceHardware/LibreSolarBox/Solar Box_FreeCAD Design/Battery_Case_Holder_FreeCAD_Design/Capture_Lower_part.PNG

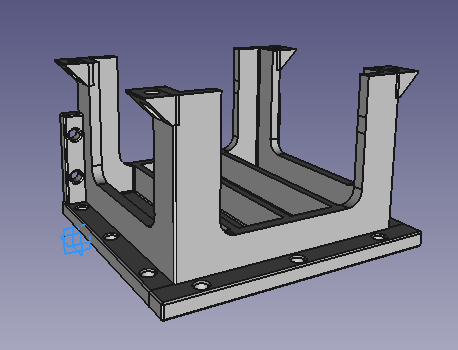
Solar Box_FreeCAD Design/Battery_Case_Holder_FreeCAD_Design/Capture_Lower_part.PNG
