CollectiveOpenSourceHardware/LibreSolarBox/Solar Box_FreeCAD Design/Solar Box v_3/solar_box_v_03_photo3.PNG

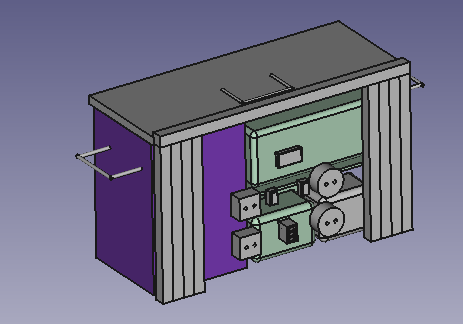
Solar Box_FreeCAD Design/Solar Box v_3/solar_box_v_03_photo3.PNG
