CollectiveOpenSourceHardware/LibreSolarBox/Solar Box_FreeCAD Design/Solar Box v_3/solar_box_v_03_photo8.PNG

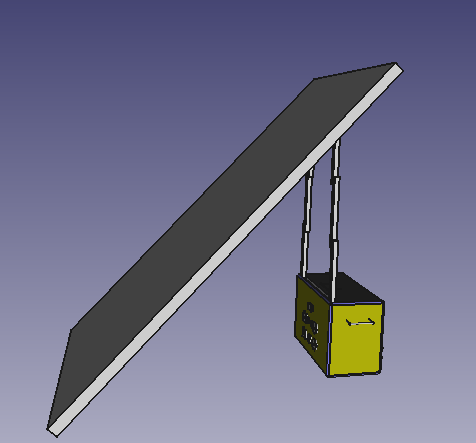
Solar Box_FreeCAD Design/Solar Box v_3/solar_box_v_03_photo8.PNG
