CollectiveOpenSourceHardware/LibreSolarBox/Solar Box_FreeCAD Design/Solar Box v_4_ boxframe/Solarbox_v_04_boxframe_photo_6.PNG

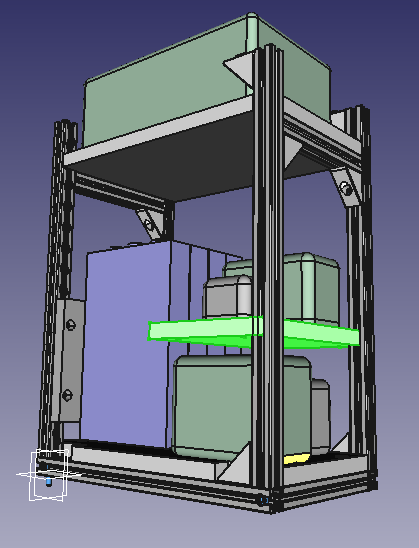
Solar Box_FreeCAD Design/Solar Box v_4_ boxframe/Solarbox_v_04_boxframe_photo_6.PNG
