CollectiveOpenSourceHardware/LibreSolarBox/upklib_v2/flachprofile/all_flatplates.png

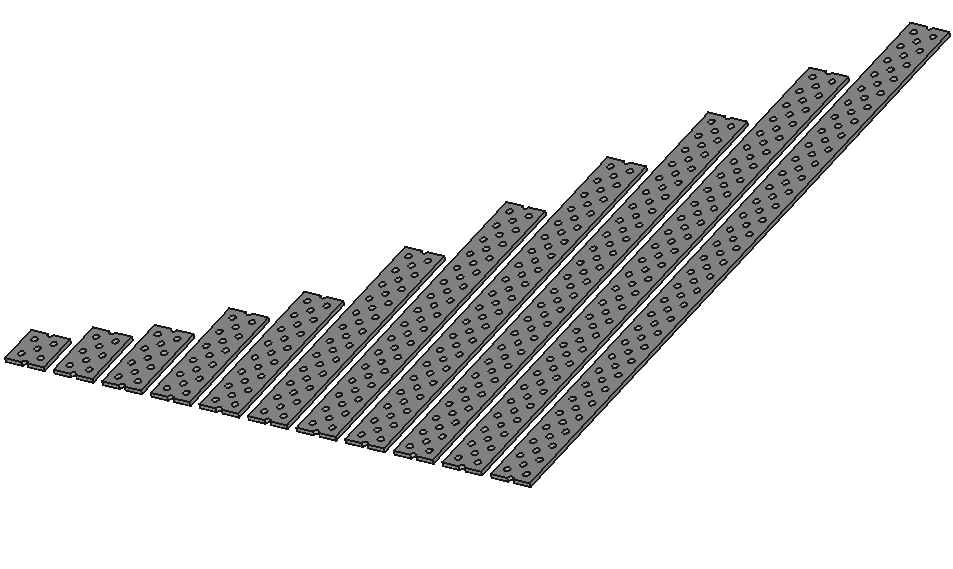
upklib_v2/flachprofile/all_flatplates.png
