CollectiveOpenSourceHardware/LibreSolarBox/upklib_v2/flachprofile/images/flatplate4.png

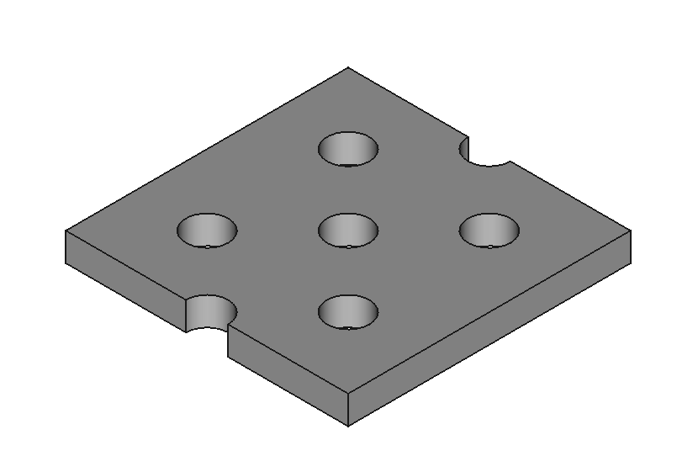
upklib_v2/flachprofile/images/flatplate4.png
