CollectiveOpenSourceHardware/LibreSolarBox/upklib_v2/flachprofile/images/flatplate6.png

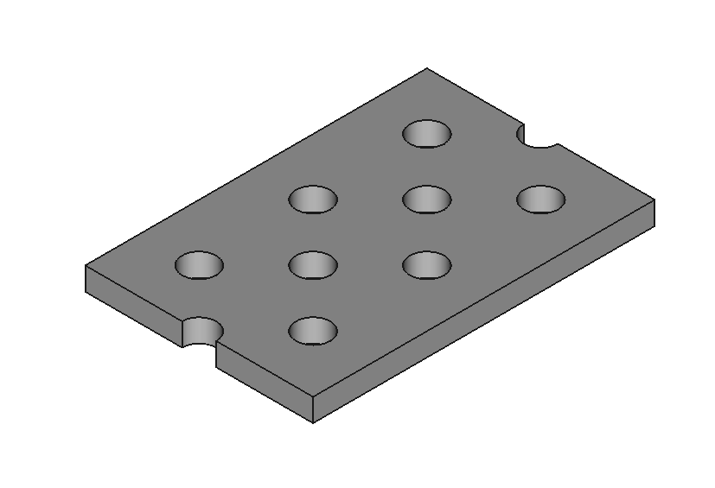
upklib_v2/flachprofile/images/flatplate6.png
