CollectiveOpenSourceHardware/LibreSolarBox/upklib_v2/flachprofile/images/flatplate8.png

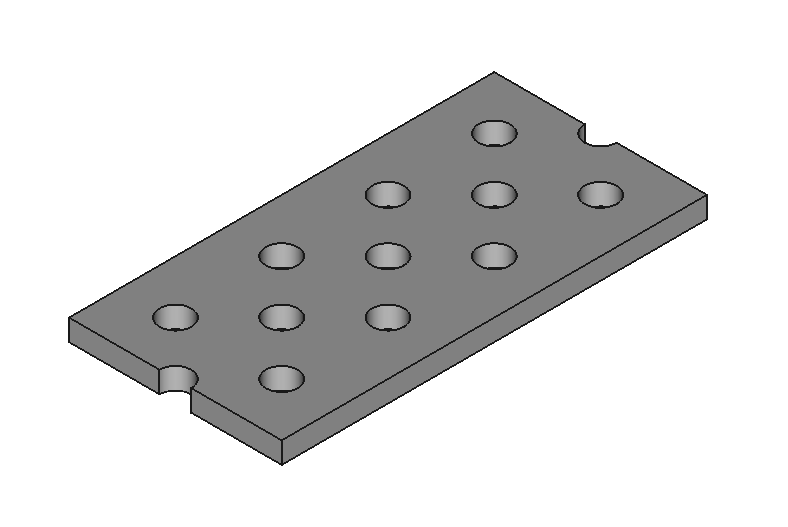
upklib_v2/flachprofile/images/flatplate8.png
