CollectiveOpenSourceHardware/LibreSolarBox/upklib_v2/flachprofile/images/flatplate12.png

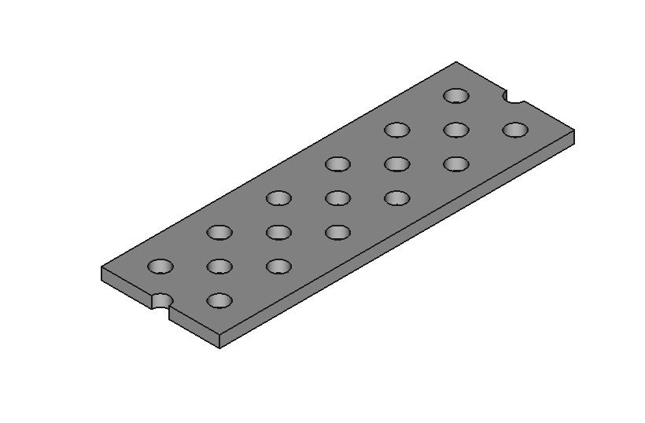
upklib_v2/flachprofile/images/flatplate12.png
