CollectiveOpenSourceHardware/LibreSolarBox/upklib_v2/flachprofile/images/flatplate16.png

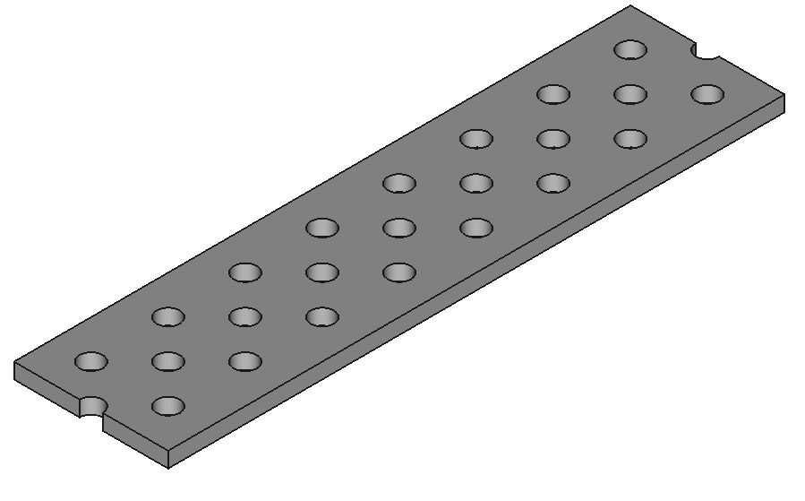
upklib_v2/flachprofile/images/flatplate16.png
