CollectiveOpenSourceHardware/LibreSolarBox/upklib_v2/flachprofile/images/flatplate24.png

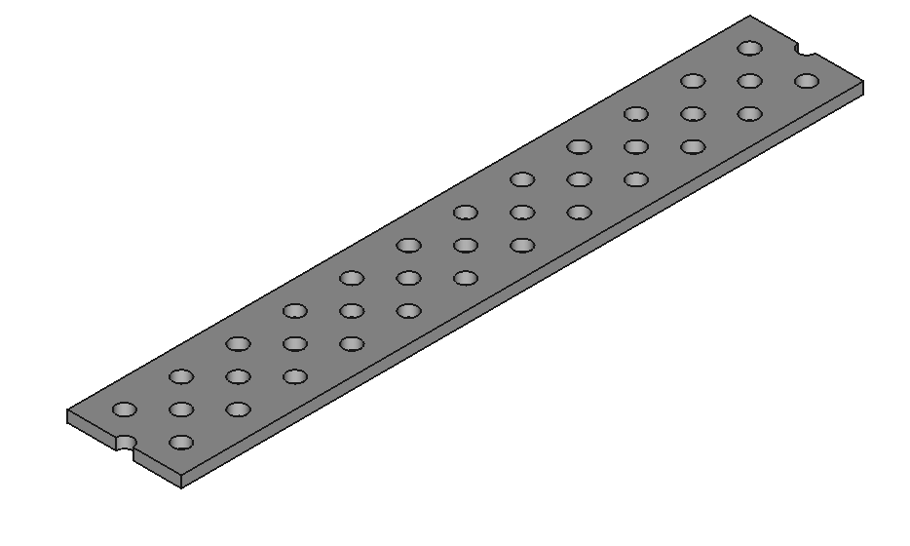
upklib_v2/flachprofile/images/flatplate24.png
