CollectiveOpenSourceHardware/LibreSolarBox/upklib_v2/flachprofile/images/flatplate32.png

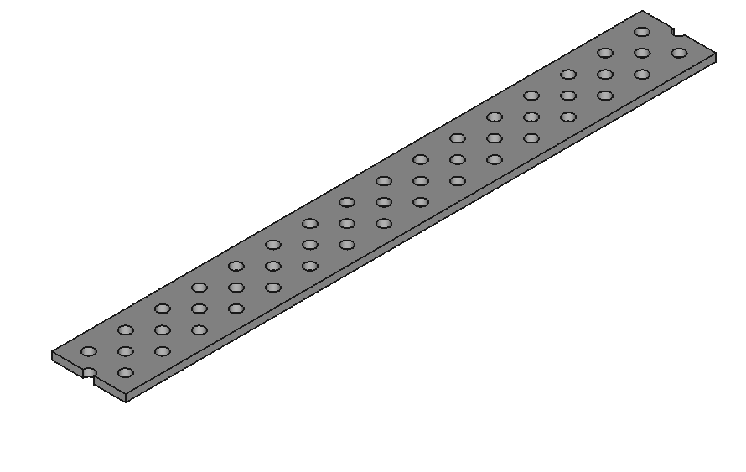
upklib_v2/flachprofile/images/flatplate32.png
