CollectiveOpenSourceHardware/LibreSolarBox/upklib_v2/flachprofile/images/flatplate56.png

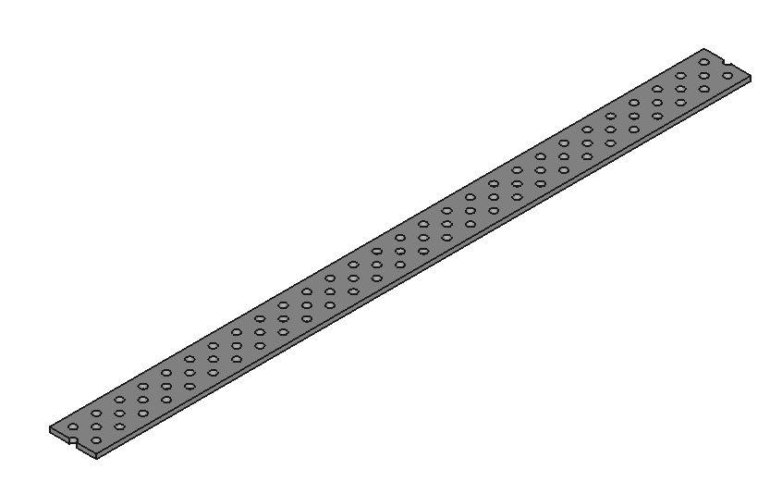
upklib_v2/flachprofile/images/flatplate56.png
