CollectiveOpenSourceHardware/LibreSolarBox/upklib_v2/flachprofile/images/flatplate64.png

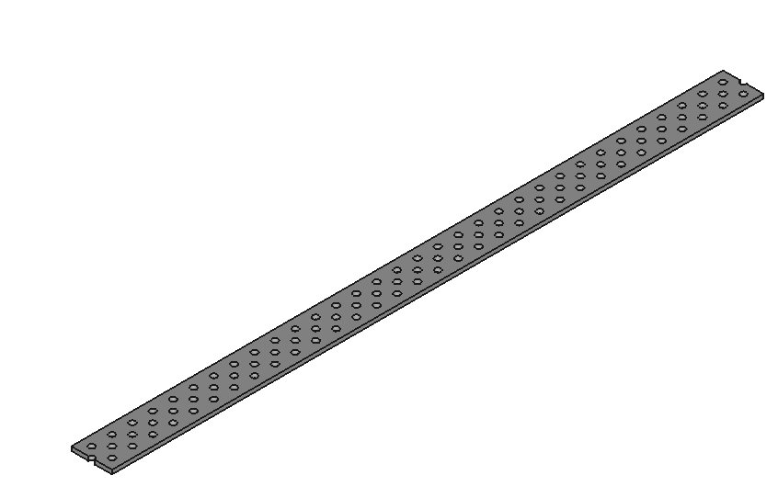
upklib_v2/flachprofile/images/flatplate64.png
