CollectiveOpenSourceHardware/LibreSolarBox/upklib_v2/frameset/images/Dreieck1h.png

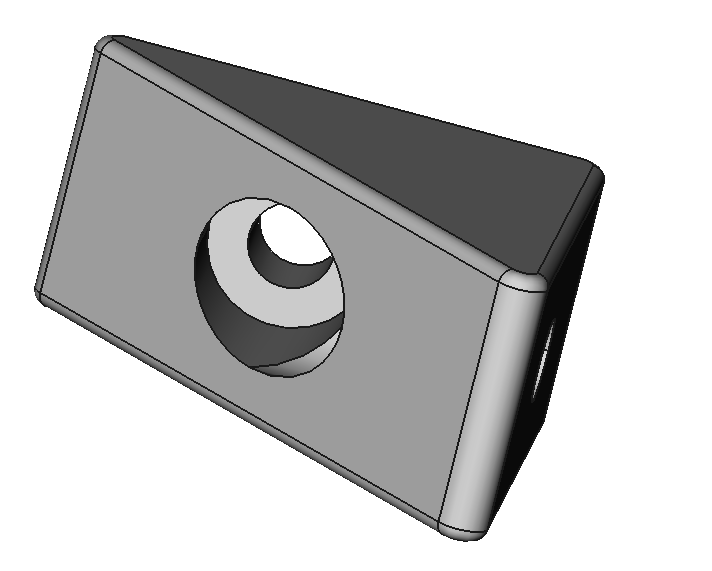
upklib_v2/frameset/images/Dreieck1h.png
