CollectiveOpenSourceHardware/LibreSolarBox/upklib_v2/frameset/images/endkappe1d.png

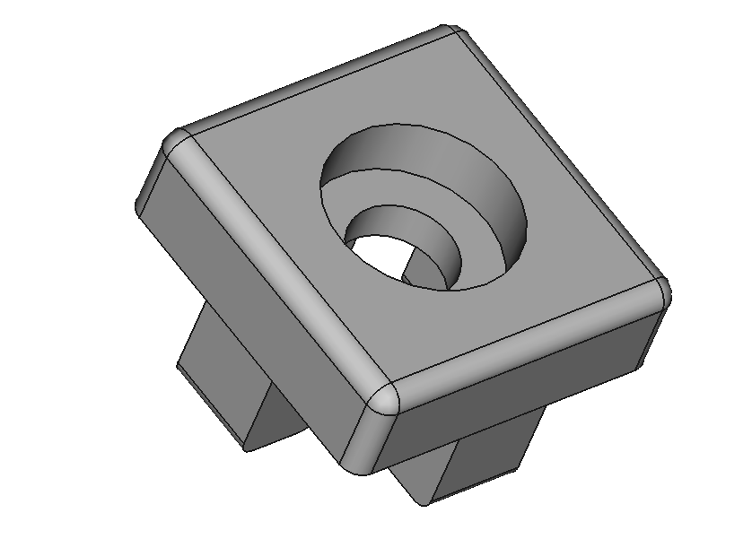
upklib_v2/frameset/images/endkappe1d.png
