CollectiveOpenSourceHardware/LibreSolarBox/upklib_v2/frameset/images/Myhinge5c.png

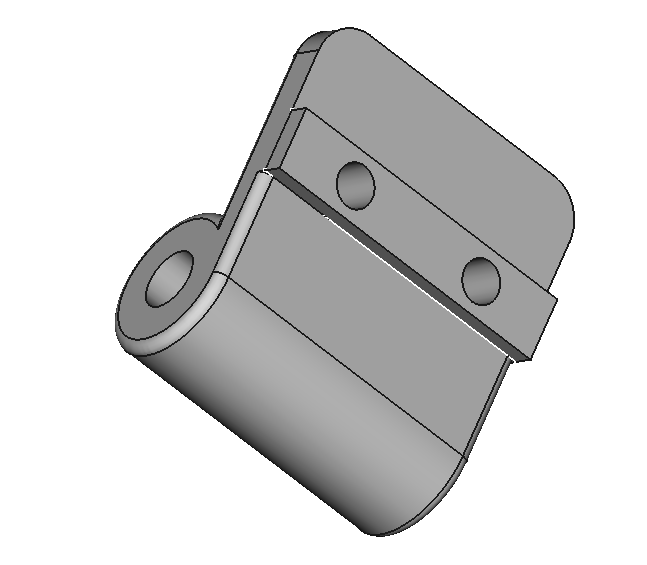
upklib_v2/frameset/images/Myhinge5c.png
