CollectiveOpenSourceHardware/LibreSolarBox/upklib_v2/frameset/images/Shell_3dcorner8g_side.png

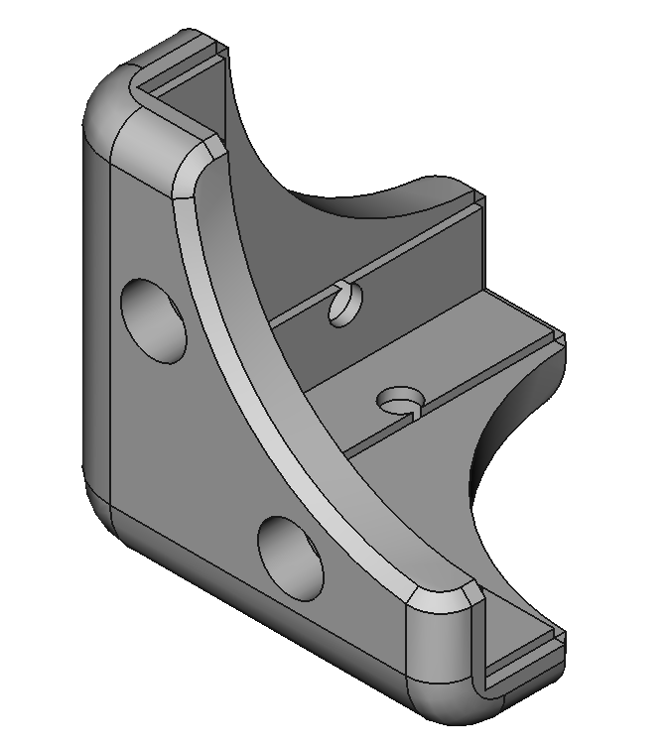
upklib_v2/frameset/images/Shell_3dcorner8g_side.png
