CollectiveOpenSourceHardware/LibreSolarBox/upklib_v2/frameset/images/Shell_corner10n_xrot.png

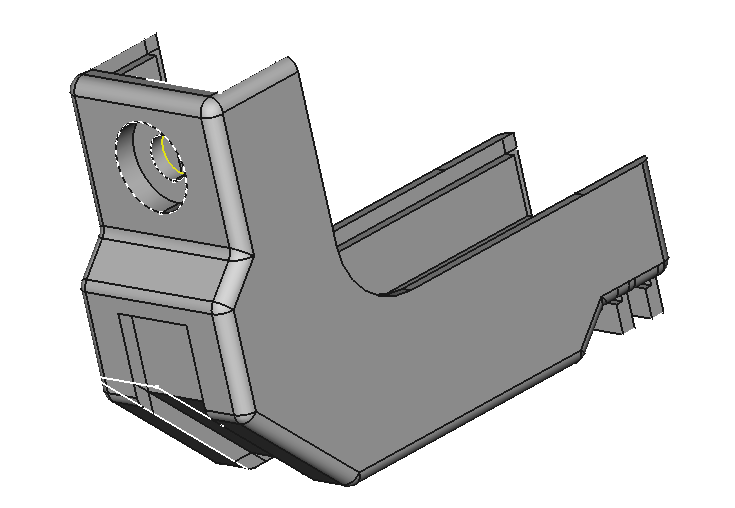
upklib_v2/frameset/images/Shell_corner10n_xrot.png
