CollectiveOpenSourceHardware/LibreSolarBox/upklib_v2/lineardrive/images/gt2pulley.png

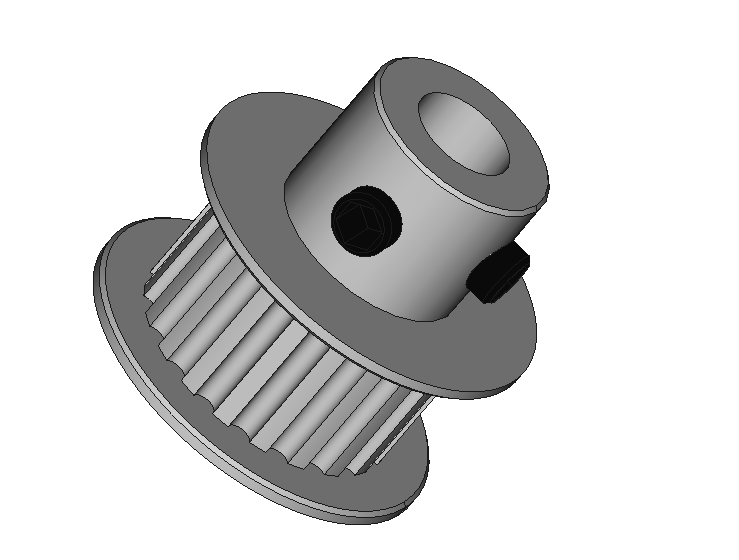
upklib_v2/lineardrive/images/gt2pulley.png
