CollectiveOpenSourceHardware/LibreSolarBox/upklib_v2/schraubenmuttern/images/m6nut.png

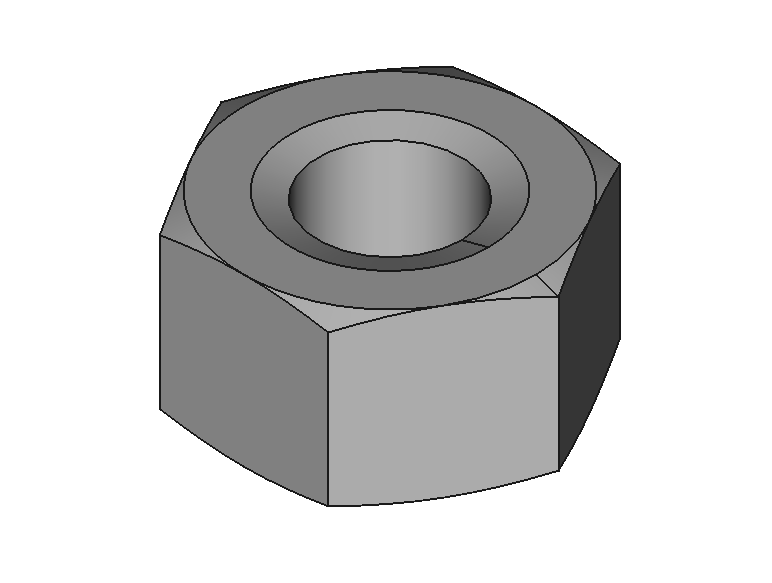
upklib_v2/schraubenmuttern/images/m6nut.png
