CollectiveOpenSourceHardware/LibreSolarBox/upklib_v2/schraubenmuttern/images/m6nutplate.png

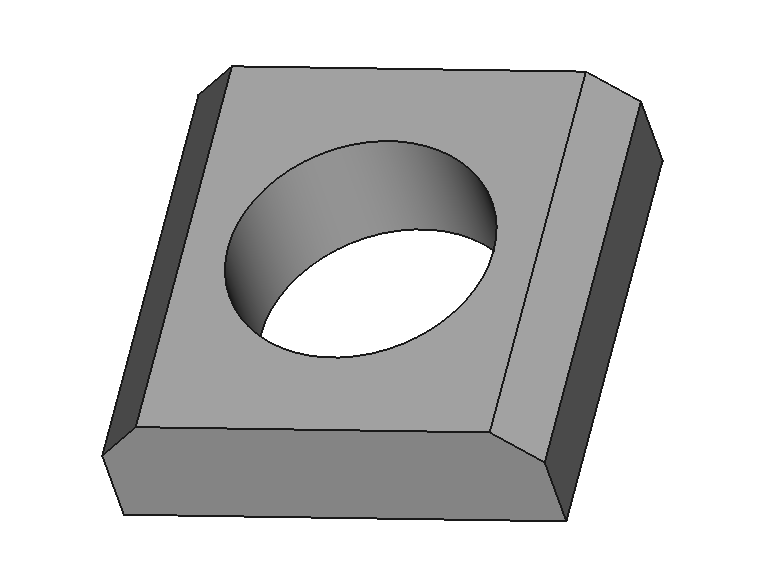
upklib_v2/schraubenmuttern/images/m6nutplate.png
