CollectiveOpenSourceHardware/LibreSolarBox/upklib_v2/schraubenmuttern/images/m6x8.png

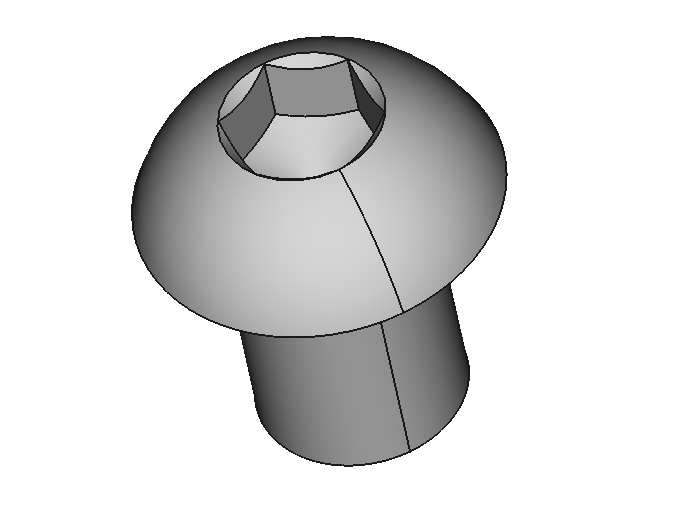
upklib_v2/schraubenmuttern/images/m6x8.png
