CollectiveOpenSourceHardware/LibreSolarBox/upklib_v2/schraubenmuttern/images/m6x12.png

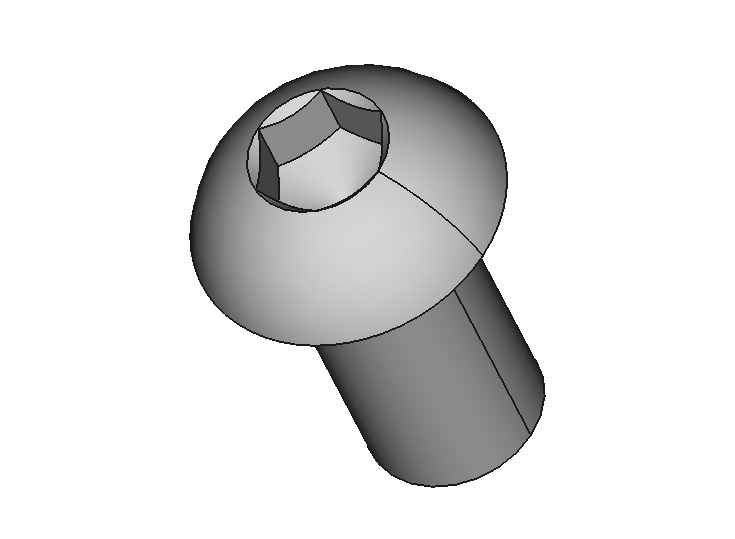
upklib_v2/schraubenmuttern/images/m6x12.png
