CollectiveOpenSourceHardware/LibreSolarBox/upklib_v2/schraubenmuttern/images/m6x16.png

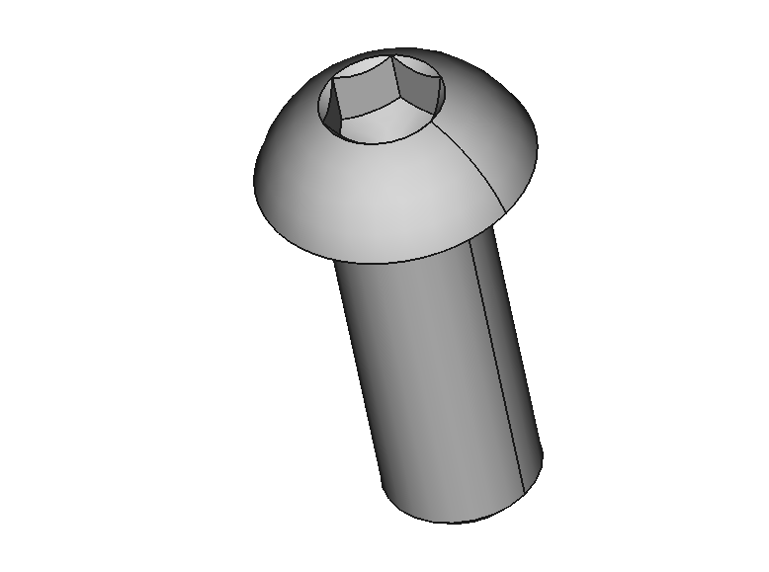
upklib_v2/schraubenmuttern/images/m6x16.png
