CollectiveOpenSourceHardware/LibreSolarBox/upklib_v2/schraubenmuttern/images/m6x20.png

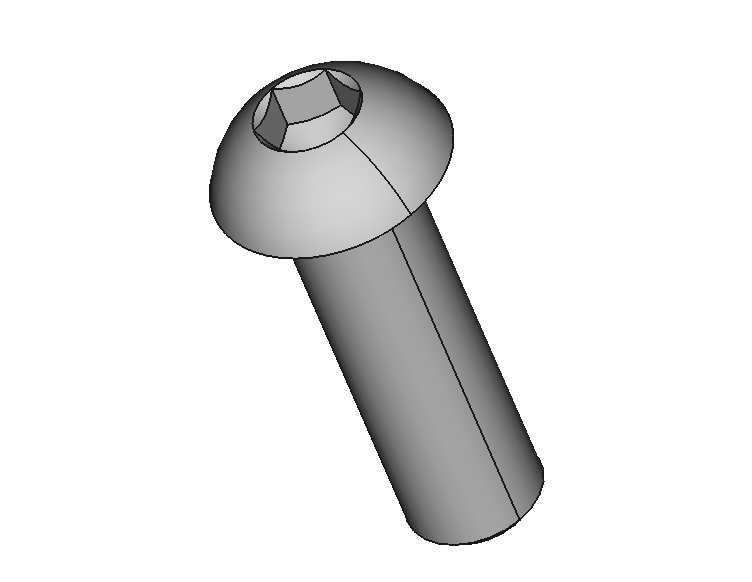
upklib_v2/schraubenmuttern/images/m6x20.png
