CollectiveOpenSourceHardware/LibreSolarBox/upklib_v2/schraubenmuttern/images/m6x25cyl.png

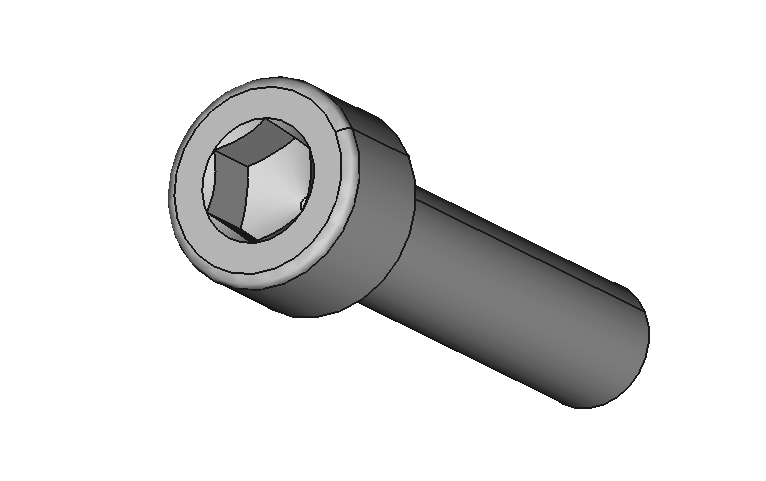
upklib_v2/schraubenmuttern/images/m6x25cyl.png
