CollectiveOpenSourceHardware/LibreSolarBox/upklib_v2/schraubenmuttern/images/wash6.4x12x1.6.png

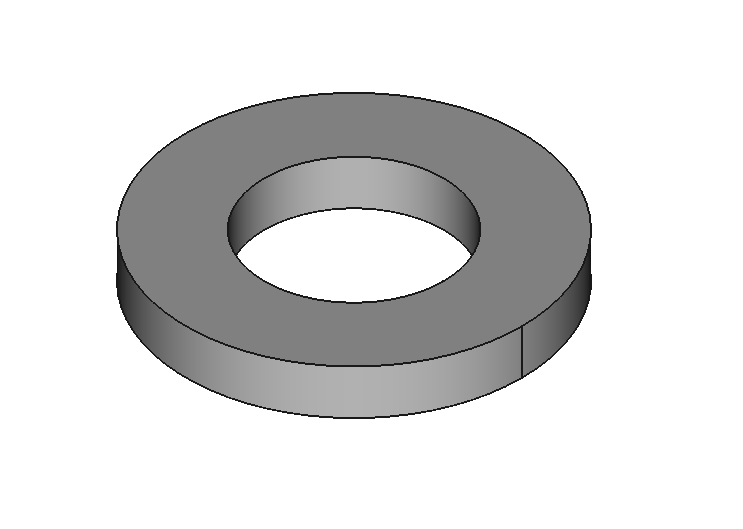
upklib_v2/schraubenmuttern/images/wash6.4x12x1.6.png
