CollectiveOpenSourceHardware/LibreSolarBox/upklib_v2/tslotprofile/pics/tslot4.png

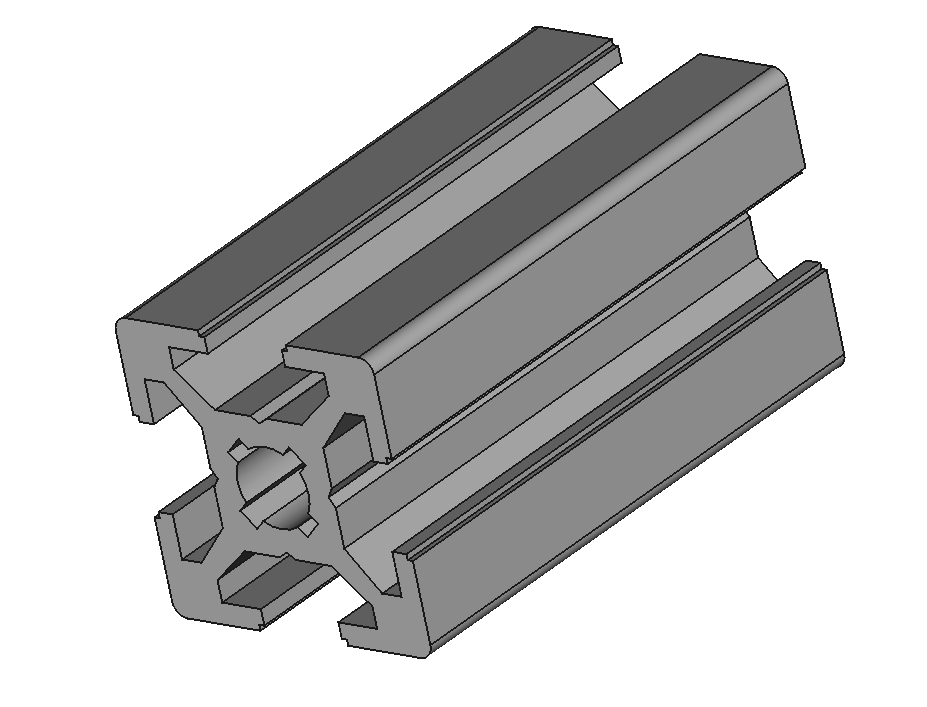
upklib_v2/tslotprofile/pics/tslot4.png
