CollectiveOpenSourceHardware/LibreSolarBox/upklib_v2/tslotprofile/pics/tslot4con.png

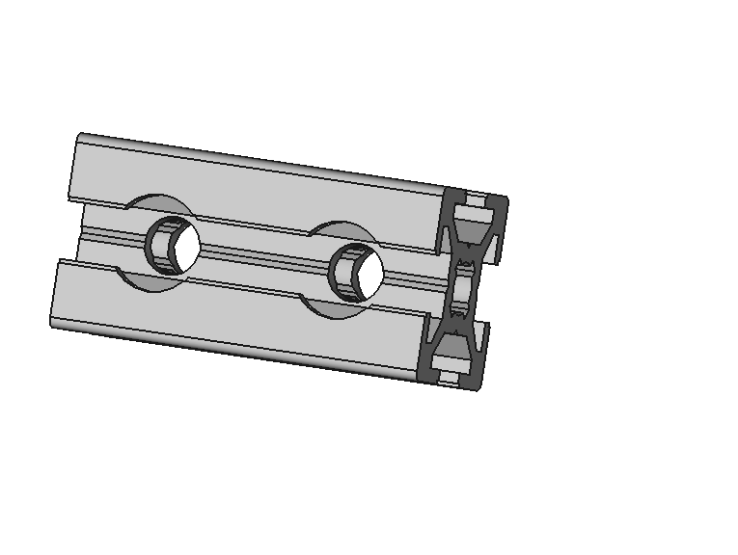
upklib_v2/tslotprofile/pics/tslot4con.png
