CollectiveOpenSourceHardware/LibreSolarBox/upklib_v2/tslotprofile/pics/tslot6.png

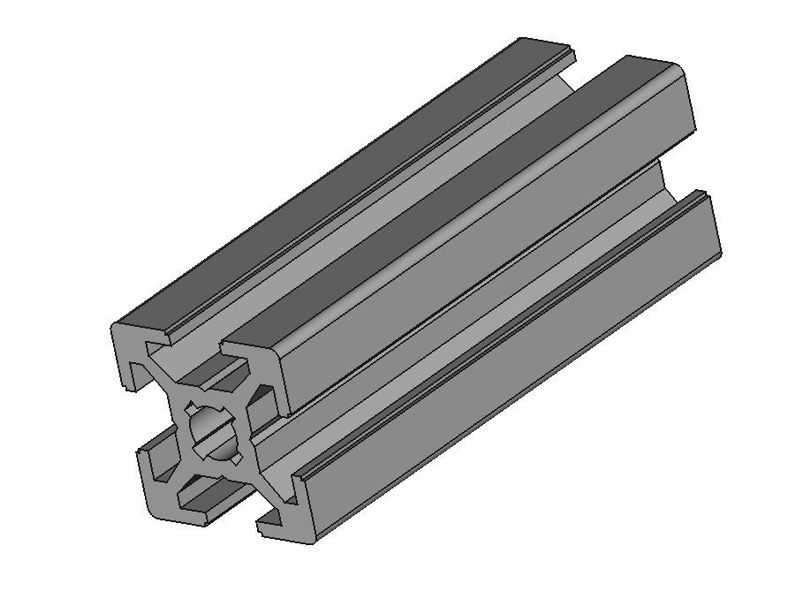
upklib_v2/tslotprofile/pics/tslot6.png
