CollectiveOpenSourceHardware/LibreSolarBox/upklib_v2/tslotprofile/pics/tslot6con.png

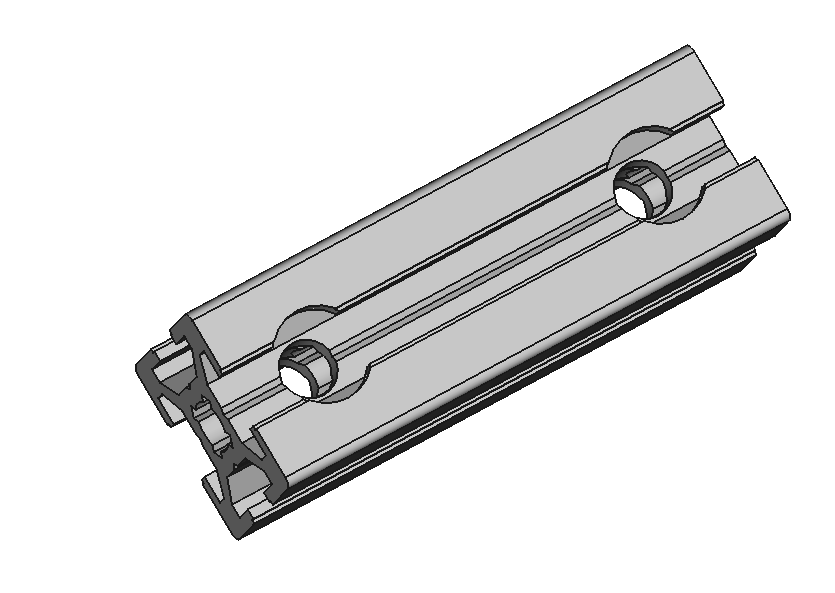
upklib_v2/tslotprofile/pics/tslot6con.png
