CollectiveOpenSourceHardware/LibreSolarBox/upklib_v2/tslotprofile/pics/tslot8.png

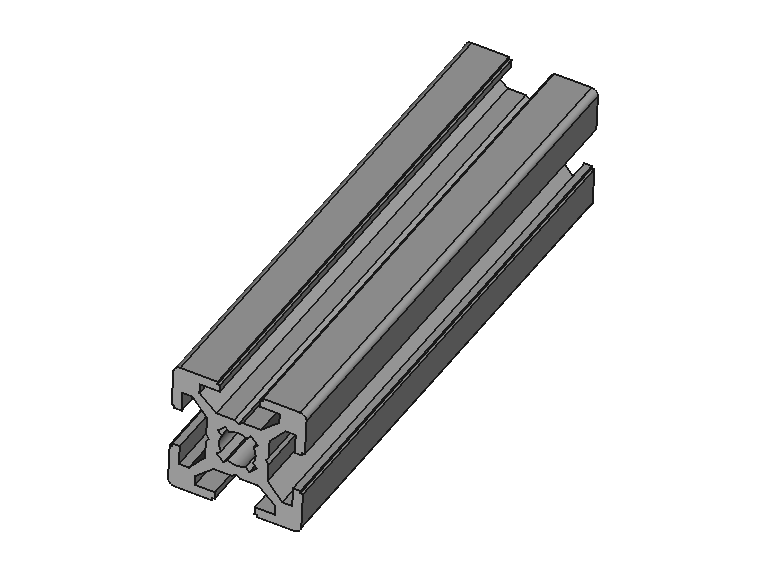
upklib_v2/tslotprofile/pics/tslot8.png
