CollectiveOpenSourceHardware/LibreSolarBox/upklib_v2/tslotprofile/pics/tslot8con.png

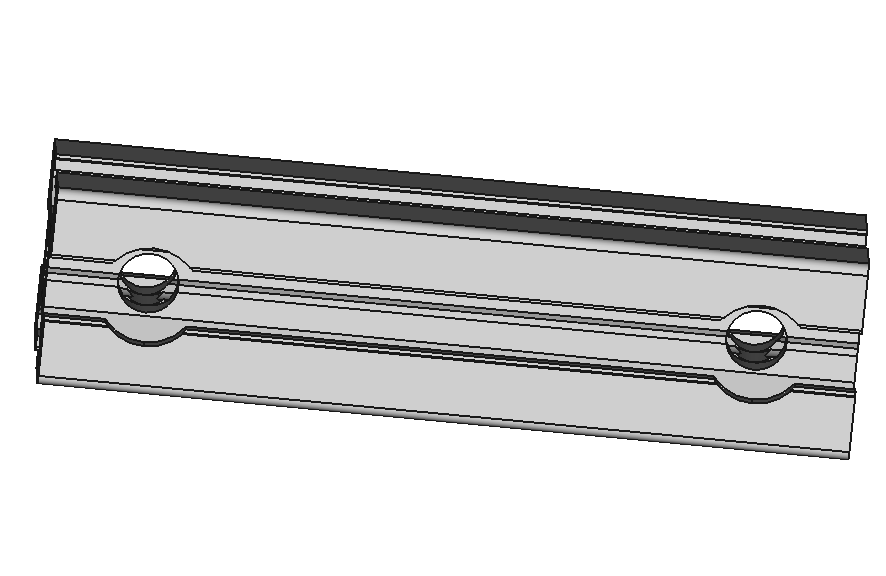
upklib_v2/tslotprofile/pics/tslot8con.png
