CollectiveOpenSourceHardware/LibreSolarBox/upklib_v2/tslotprofile/pics/tslot12.png

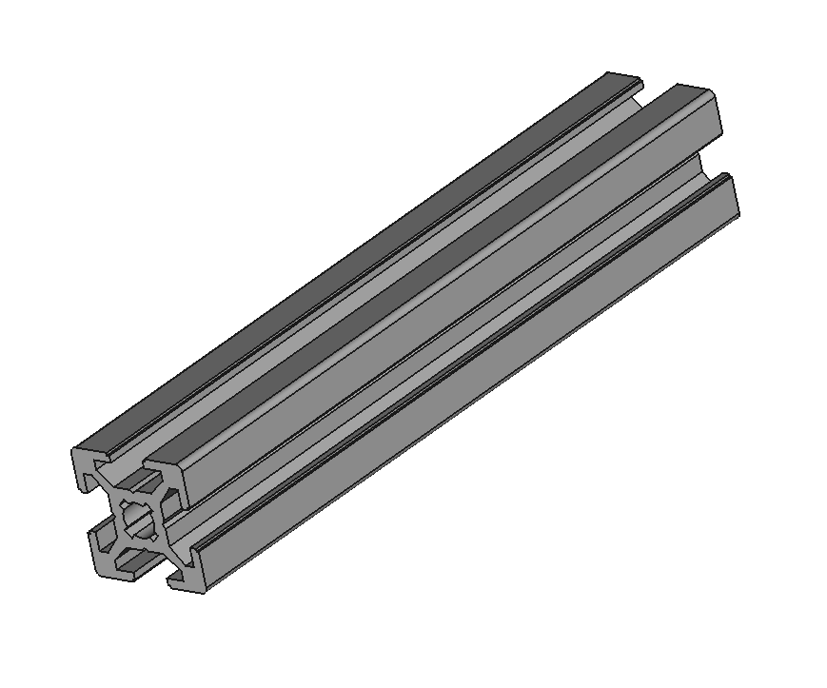
upklib_v2/tslotprofile/pics/tslot12.png
