CollectiveOpenSourceHardware/LibreSolarBox/upklib_v2/tslotprofile/pics/tslot12con.png

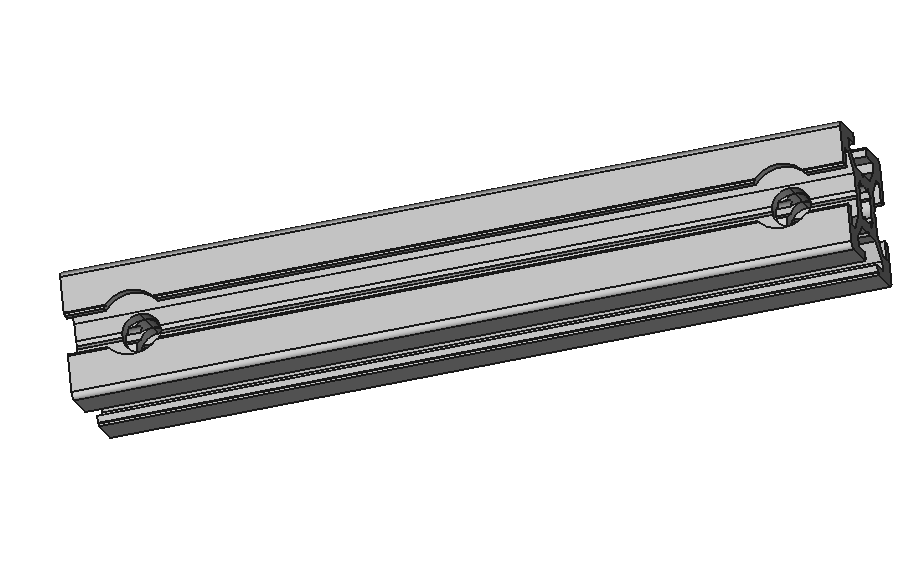
upklib_v2/tslotprofile/pics/tslot12con.png
