CollectiveOpenSourceHardware/LibreSolarBox/upklib_v2/tslotprofile/pics/tslot16con.png

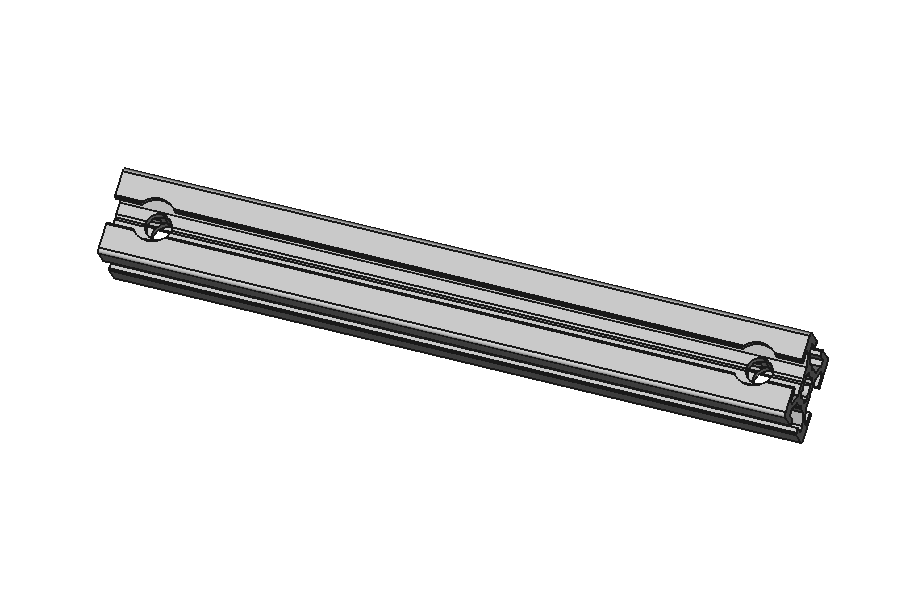
upklib_v2/tslotprofile/pics/tslot16con.png
