CollectiveOpenSourceHardware/LibreSolarBox/upklib_v2/tslotprofile/pics/tslot24.png

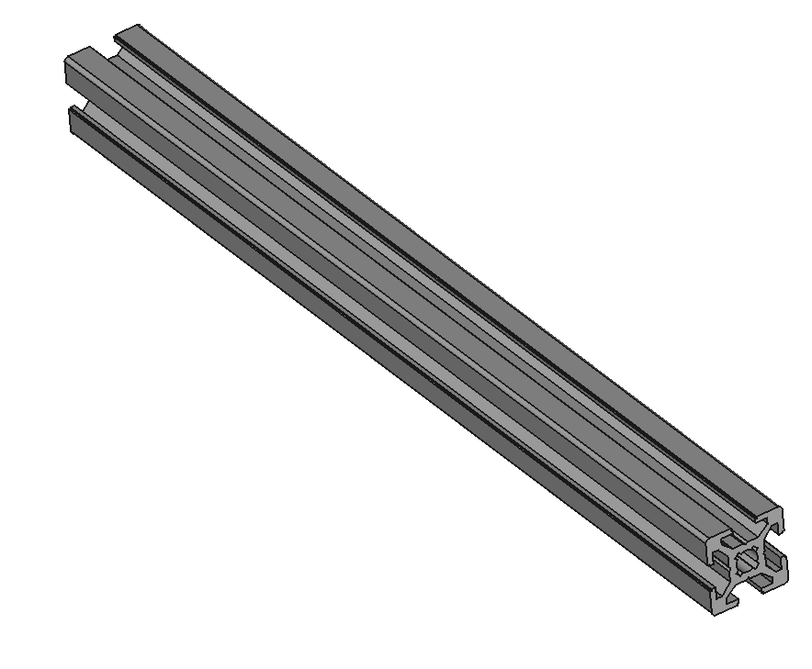
upklib_v2/tslotprofile/pics/tslot24.png
