CollectiveOpenSourceHardware/LibreSolarBox/upklib_v2/tslotprofile/pics/tslot24con.png

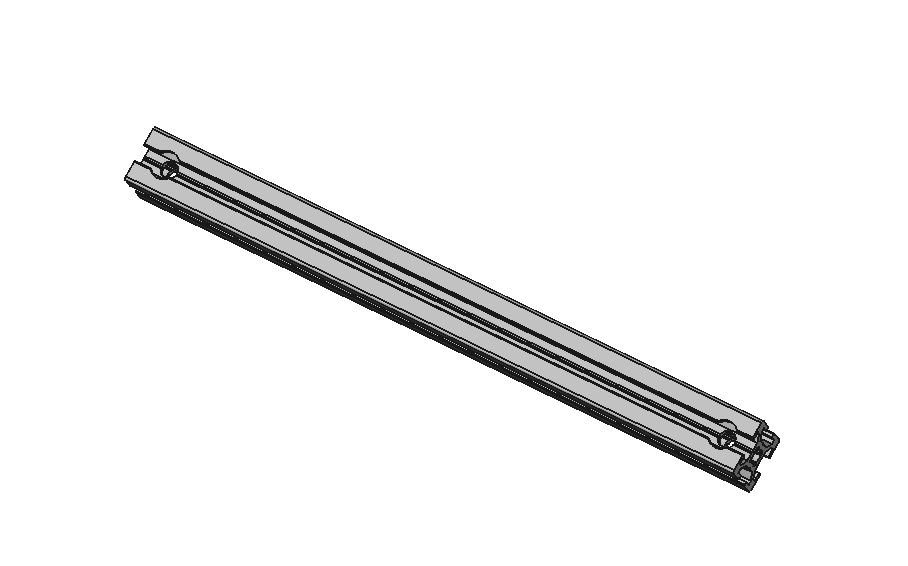
upklib_v2/tslotprofile/pics/tslot24con.png
