CollectiveOpenSourceHardware/LibreSolarBox/upklib_v2/tslotprofile/pics/tslot32con.png

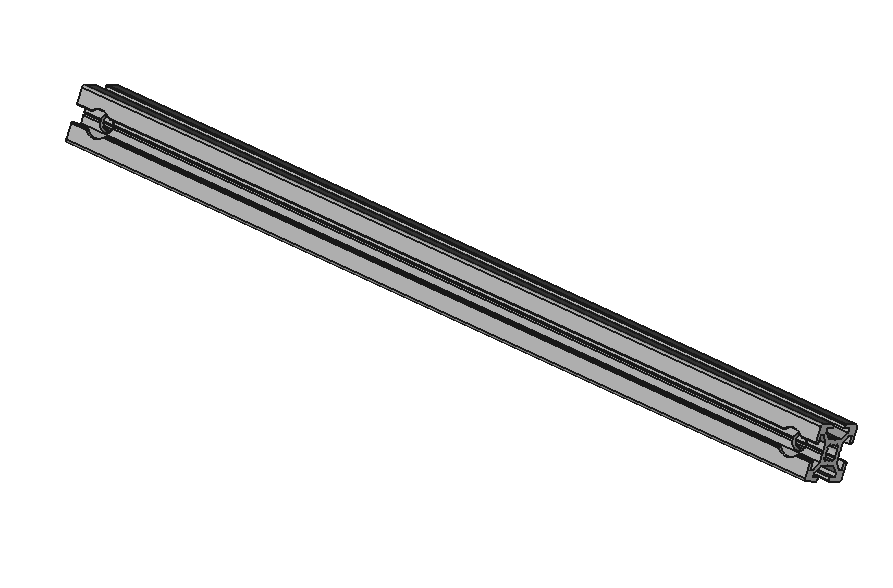
upklib_v2/tslotprofile/pics/tslot32con.png
