CollectiveOpenSourceHardware/LibreSolarBox/upklib_v2/tslotprofile/pics/tslot40con.png

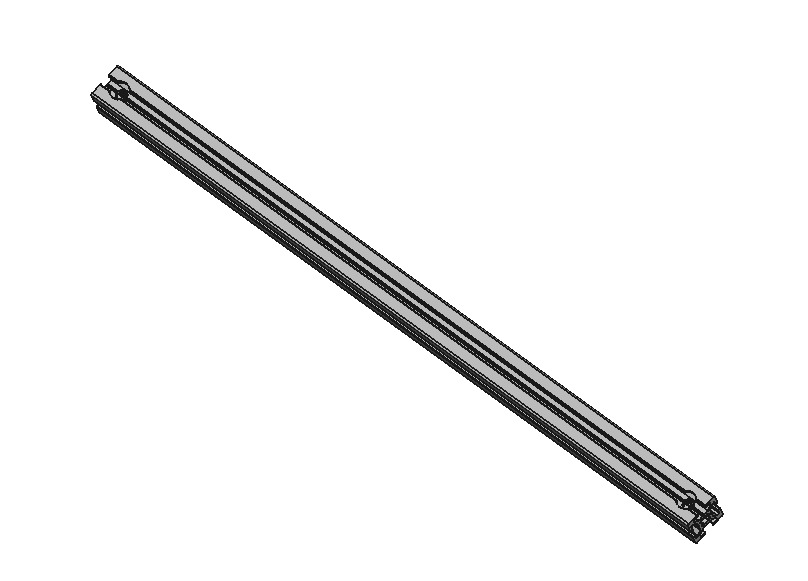
upklib_v2/tslotprofile/pics/tslot40con.png
