CollectiveOpenSourceHardware/LibreSolarBox/upklib_v2/tslotprofile/pics/tslot64.png

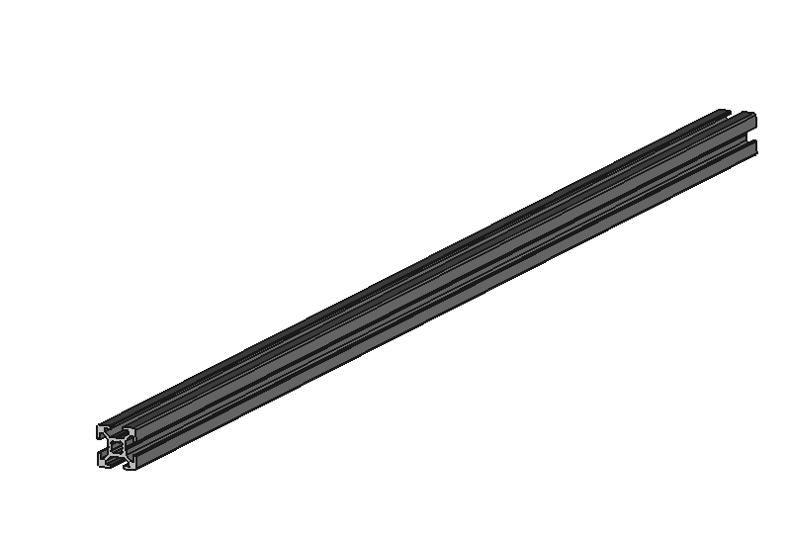
upklib_v2/tslotprofile/pics/tslot64.png
