CollectiveOpenSourceHardware/LibreSolarBox/upklib_v2/verbinder/images/lcon.png

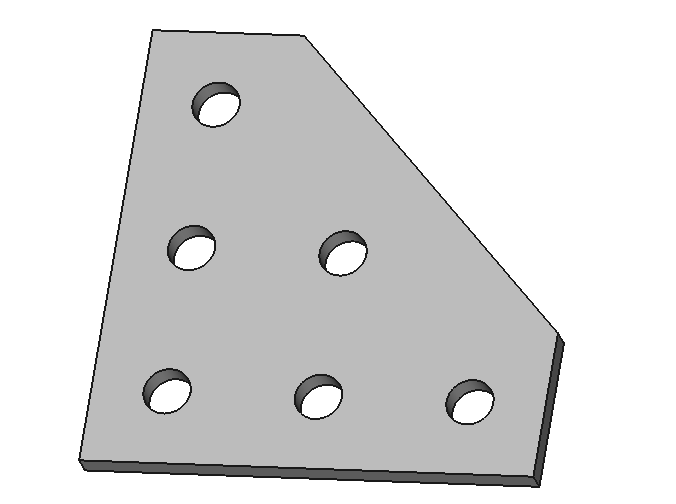
upklib_v2/verbinder/images/lcon.png
