CollectiveOpenSourceHardware/LibreSolarBox/upklib_v2/verbinder/images/tcon.png

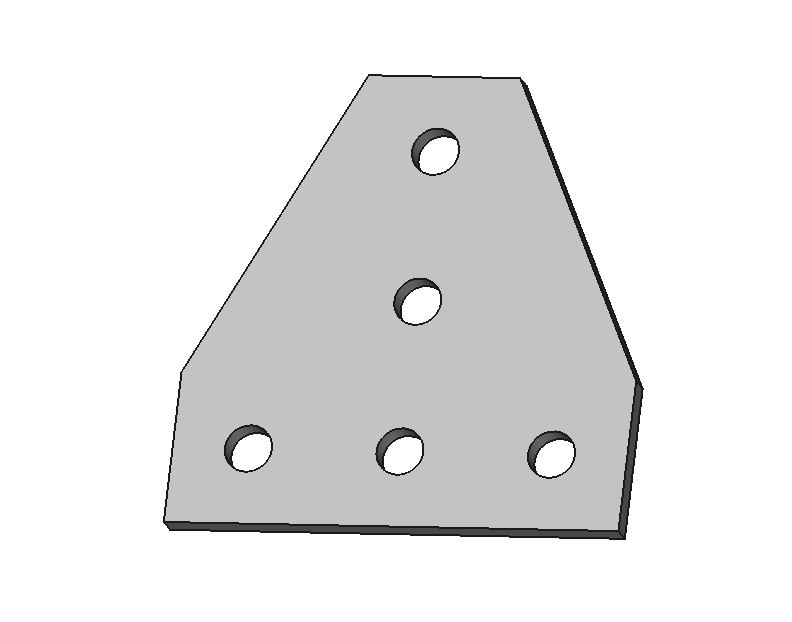
upklib_v2/verbinder/images/tcon.png
