CollectiveOpenSourceHardware/LibreSolarBox/upklib_v2/winkel/images/all_angles.png

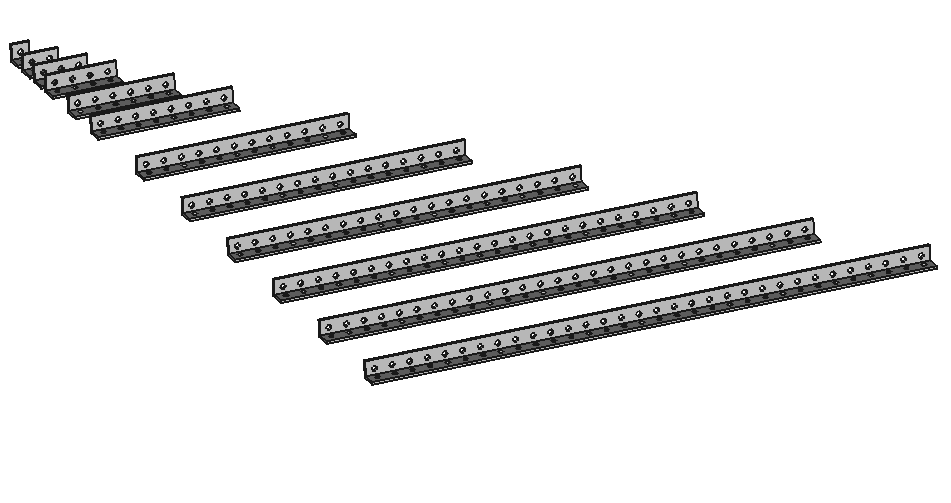
upklib_v2/winkel/images/all_angles.png
