CollectiveOpenSourceHardware/LibreSolarBox/upklib_v2/winkel/images/angle2.png

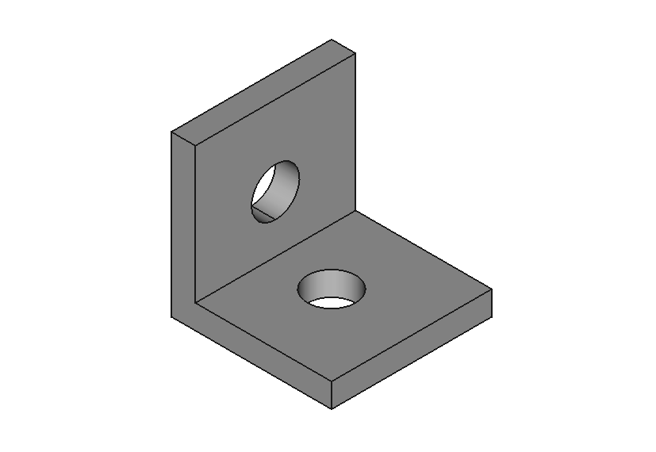
upklib_v2/winkel/images/angle2.png
