CollectiveOpenSourceHardware/LibreSolarBox/upklib_v2/winkel/images/angle4.png

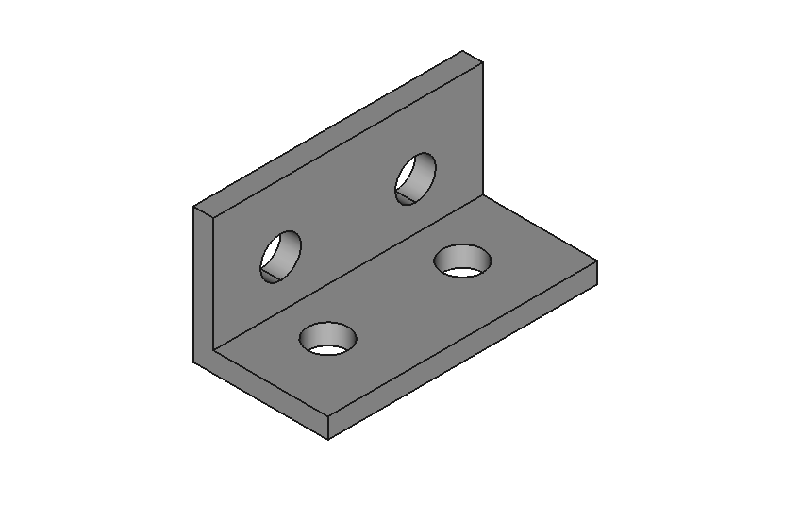
upklib_v2/winkel/images/angle4.png
