CollectiveOpenSourceHardware/LibreSolarBox/upklib_v2/winkel/images/angle6.png

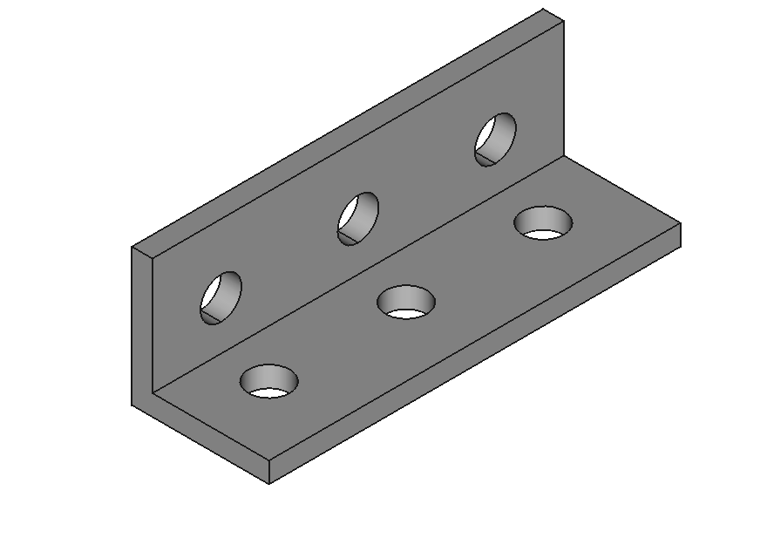
upklib_v2/winkel/images/angle6.png
