CollectiveOpenSourceHardware/LibreSolarBox/upklib_v2/winkel/images/angle8.png

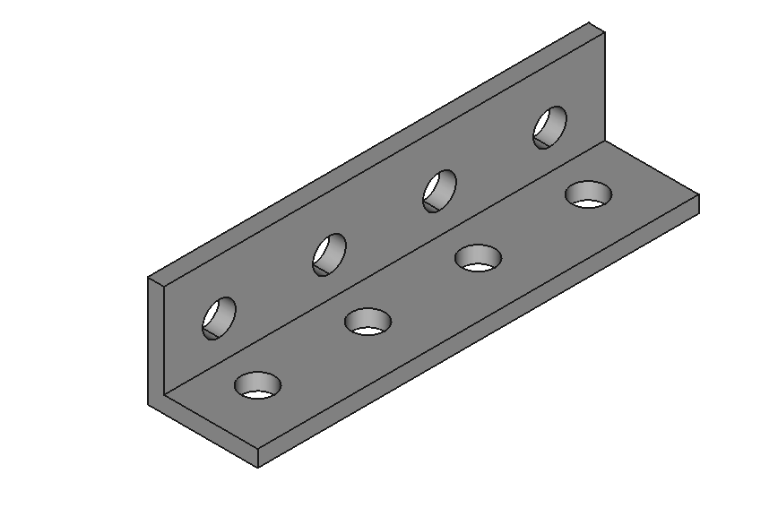
upklib_v2/winkel/images/angle8.png
