CollectiveOpenSourceHardware/LibreSolarBox/upklib_v2/winkel/images/angle12.png

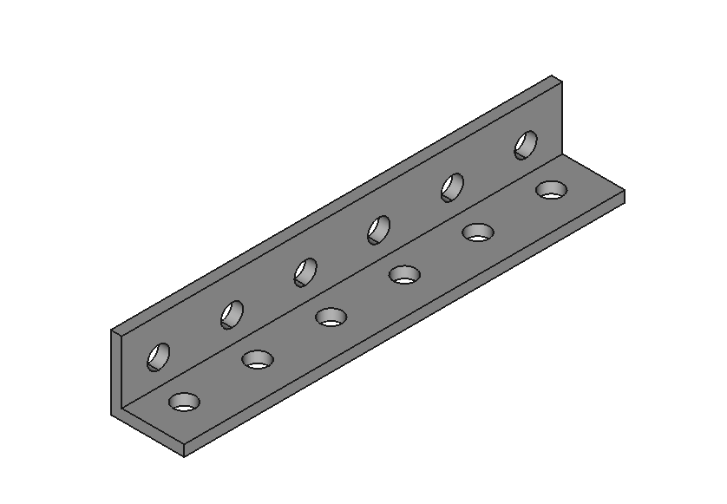
upklib_v2/winkel/images/angle12.png
