CollectiveOpenSourceHardware/LibreSolarBox/upklib_v2/winkel/images/angle24.png

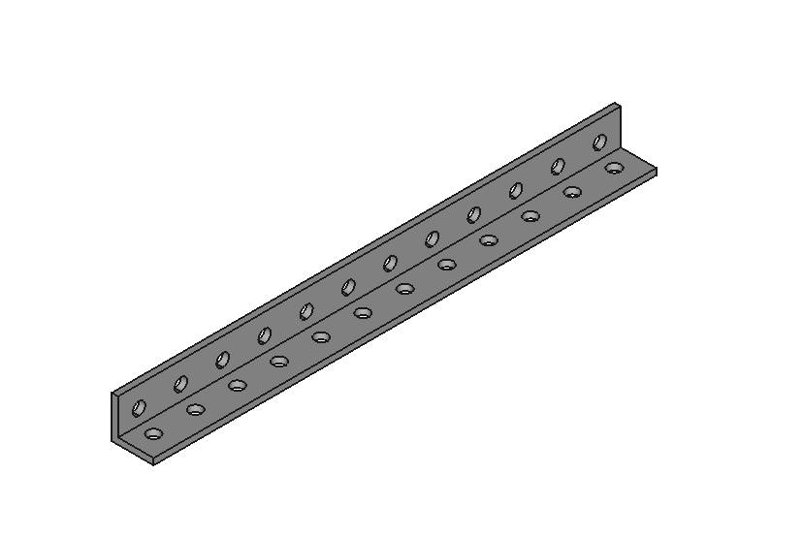
upklib_v2/winkel/images/angle24.png
