CollectiveOpenSourceHardware/LibreSolarBox/upklib_v2/winkel/images/angle32.png

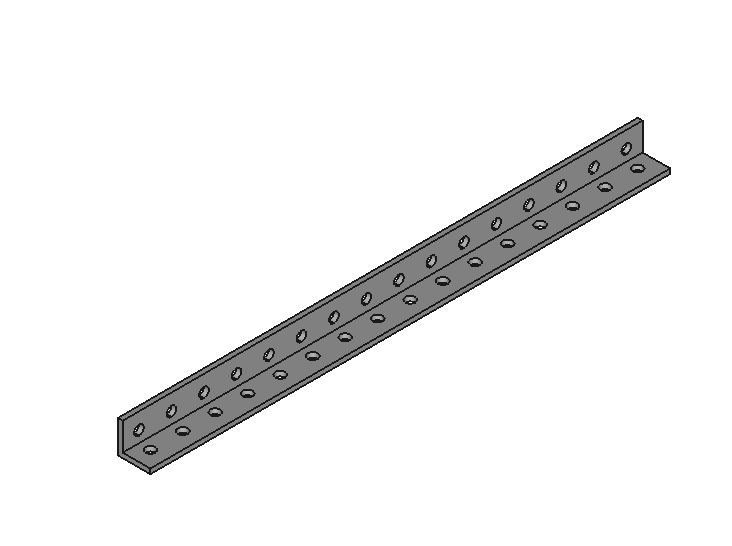
upklib_v2/winkel/images/angle32.png
