CollectiveOpenSourceHardware/LibreSolarBox/upklib_v2/winkel/images/angle48.png

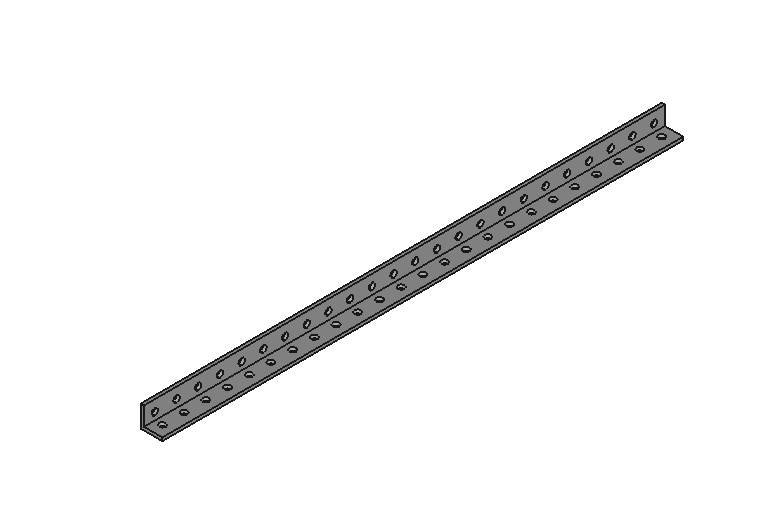
upklib_v2/winkel/images/angle48.png
