CollectiveOpenSourceHardware/LibreSolarBox/upklib_v2/frameset/3dprint-stls/shell_corner10n_xrot_x1.02.stl

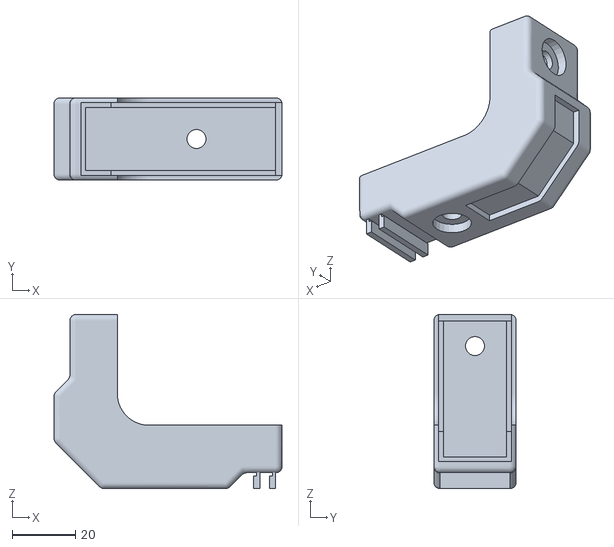
[picture p152: CAD file, 2017-09-25]
upklib_v2/frameset/3dprint-stls/shell_corner10n_xrot_x1.02.stl
72.0 x 26.0 x 55.0
