CollectiveOpenSourceHardware/LibreSolarBox/upklib_v2/frameset/shell_3dcorner8g.fcstd

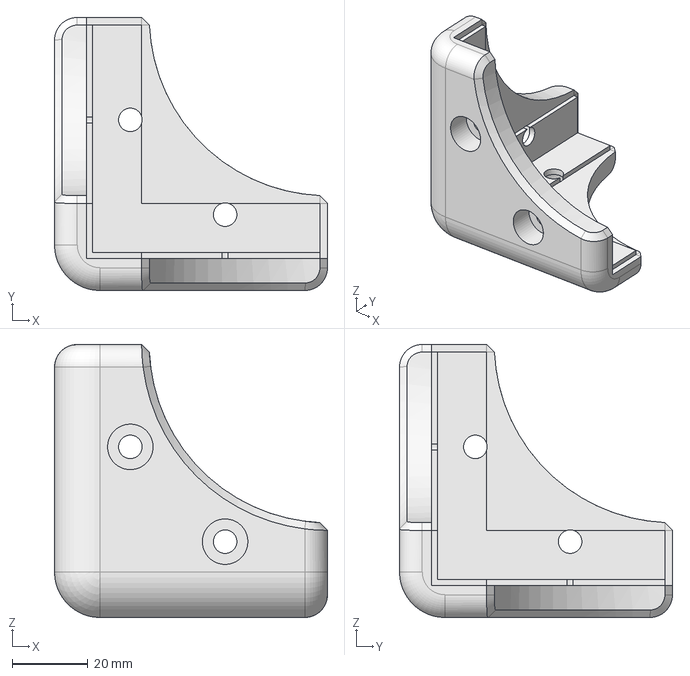
[picture p153: CAD file, 2017-09-25]
upklib_v2/frameset/shell_3dcorner8g.fcstd
72.0 x 72.0 x 72.0 mm
