CollectiveOpenSourceHardware/LibreSolarBox/upklib_v2/lineardrive/gt2pulley.fcstd

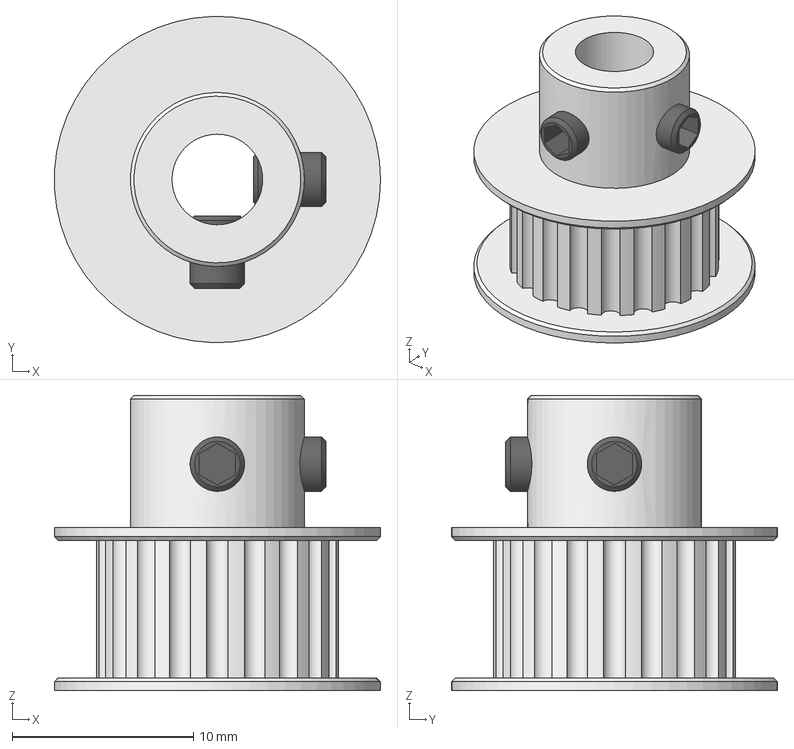
[picture p154: CAD file, 2017-09-25]
upklib_v2/lineardrive/gt2pulley.fcstd
18.0 x 18.0 x 16.3 mm
PoleaGT2
TornilloM3
TornilloM3-2
