CollectiveOpenSourceHardware/LibreSolarBox/upklib_v2/slider/universalaxis_belt/idlerSide_8mm_rods_v02.FCStd

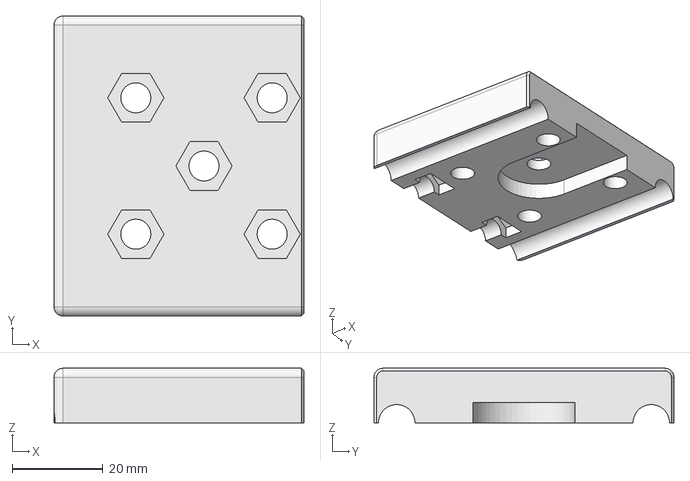
[picture p155: CAD file, 2017-10-14]
upklib_v2/slider/universalaxis_belt/idlerSide_8mm_rods_v02.FCStd
55.0 x 66.0 x 12.0 mm
