CollectiveOpenSourceHardware/LibreSolarBox/upklib_v2/tslotprofile/tslot12.fcstd

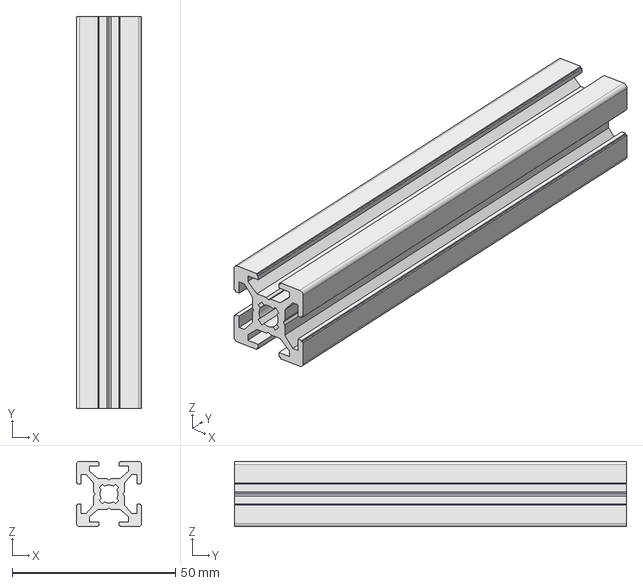
[picture p156: CAD file, 2017-09-25]
upklib_v2/tslotprofile/tslot12.fcstd
20.0 x 120.0 x 20.0 mm
