CollectiveOpenSourceHardware/LibreSolarBox/upklib_v2/verbinder/tcon.fcstd

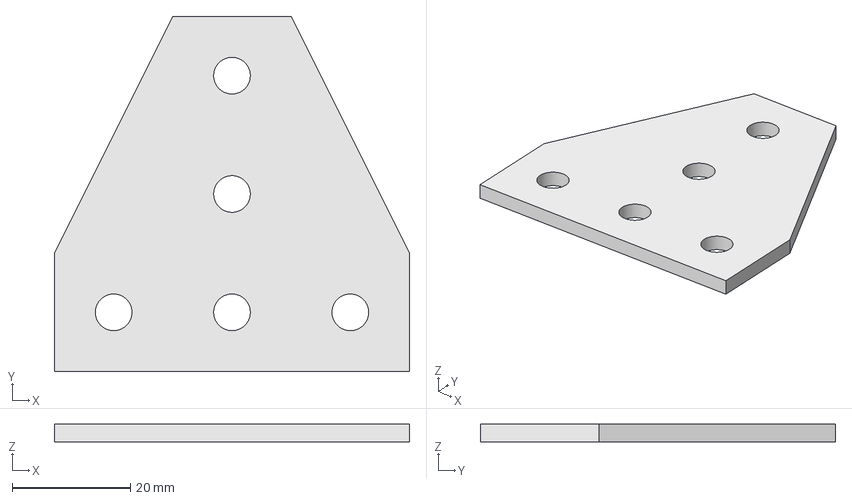
[picture p157: CAD file, 2017-09-25]
upklib_v2/verbinder/tcon.fcstd
60.0 x 60.0 x 3.00 mm
