CollectiveOpenSourceHardware/LibreSolarBox/upklib_v2/winkel/all_angles.fcstd

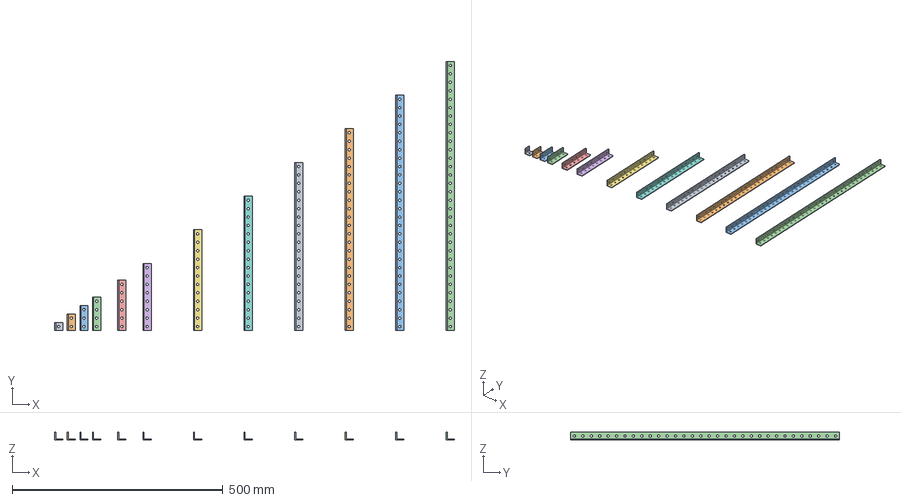
[picture p158: CAD file, 2017-09-25]
upklib_v2/winkel/all_angles.fcstd
950.0 x 640.0 x 20.0 mm
upk_angle20
upk_angle40
upk_angle60
upk_angle80
upk_angle120
upk_angle160
upk_angle240
upk_angle320
upk_angle400
upk_angle480
upk_angle560
upk_angle640
