CollectiveOpenSourceHardware/LibreSolarBox/boxframe/buildinstructional/upper_frame/upperframe1.fcstd

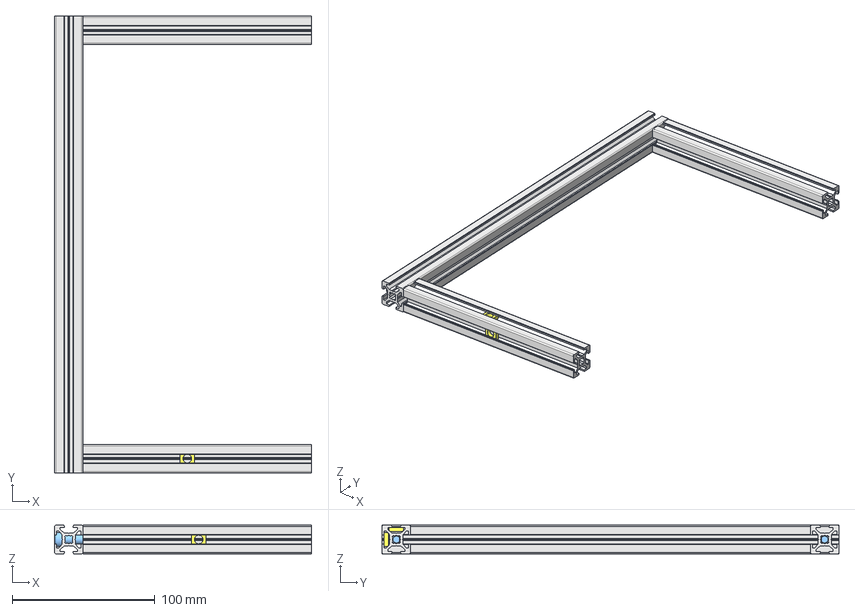
[picture p161: CAD file, 2018-08-25]
boxframe/buildinstructional/upper_frame/upperframe1.fcstd
180.0 x 320.0 x 20.0 mm
tslot32con001
tslot041
tslot16_002
M6x25-Screw007
M6x25-Screw008
m6nutplate020
m6nutplate021
