CollectiveOpenSourceHardware/LibreSolarBox/boxframe/buildinstructional/upright/upright4b.fcstd

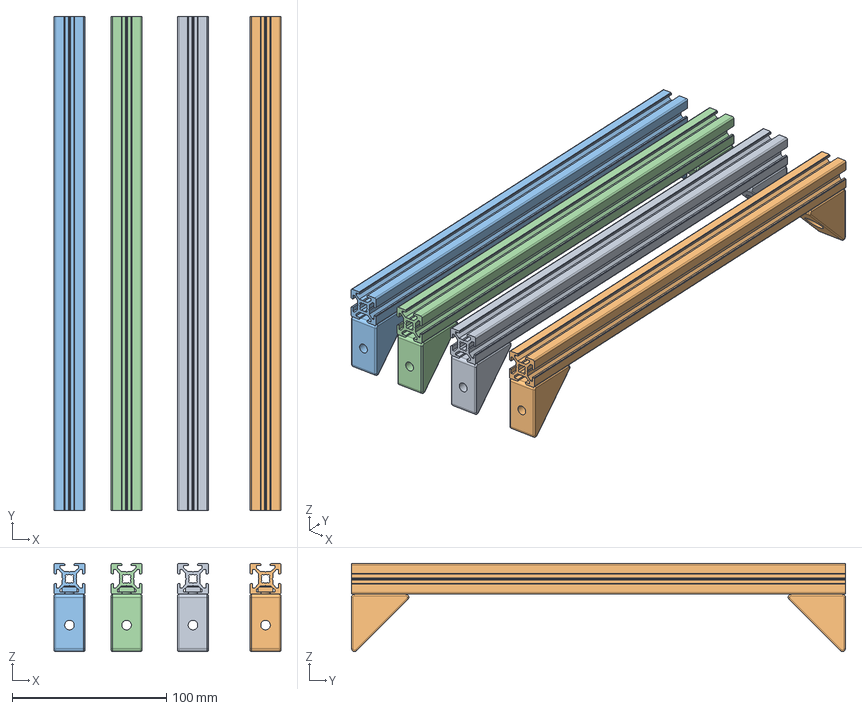
[picture p162: CAD file, 2018-08-25]
boxframe/buildinstructional/upright/upright4b.fcstd
147.0 x 320.0 x 57.2 mm
