CollectiveOpenSourceHardware/LibreSolarBox/upklib_v2/flachprofile/flatplate40.fcstd

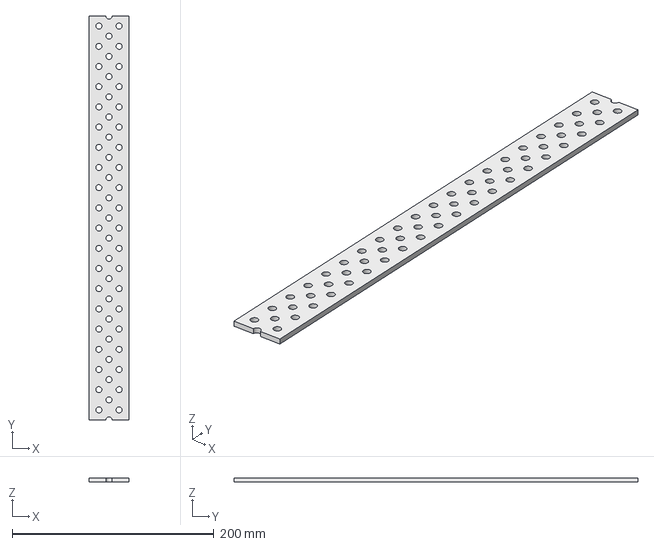
[picture p164: CAD file, 2017-09-25]
upklib_v2/flachprofile/flatplate40.fcstd
40.0 x 400.0 x 4.00 mm
