CollectiveOpenSourceHardware/LibreSolarBox/upklib_v2/frameset/3dprint-stls/myhinge5c_rotx.stl

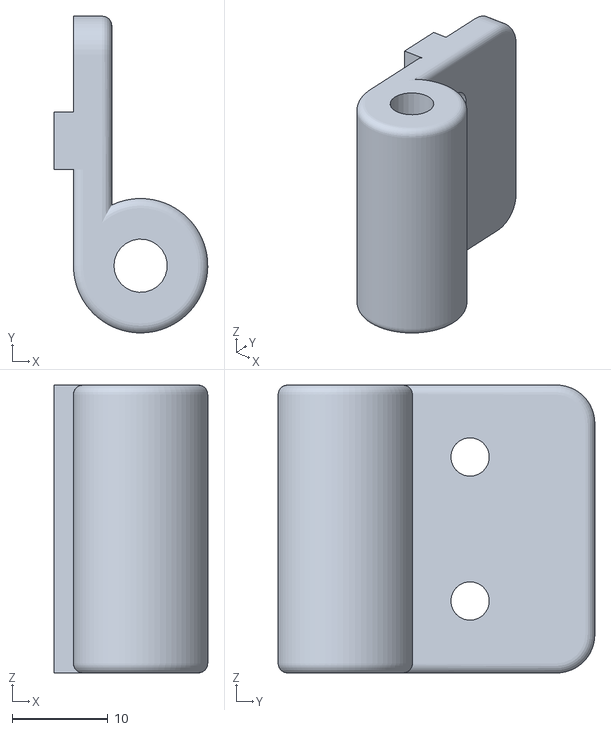
[picture p165: CAD file, 2017-09-25]
upklib_v2/frameset/3dprint-stls/myhinge5c_rotx.stl
16.0 x 33.0 x 30.0
