CollectiveOpenSourceHardware/LibreSolarBox/upklib_v2/frameset/dreieck1h.fcstd

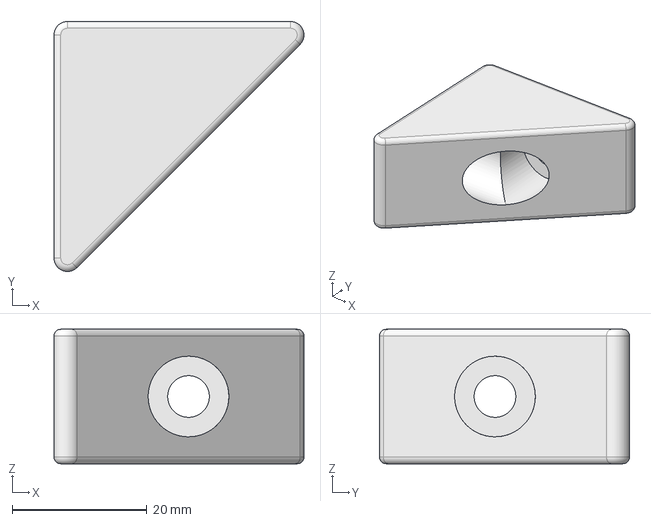
[picture p166: CAD file, 2017-09-25]
upklib_v2/frameset/dreieck1h.fcstd
37.2 x 37.2 x 20.0 mm
