CollectiveOpenSourceHardware/LibreSolarBox/upklib_v2/schraubenmuttern/m6nut.fcstd

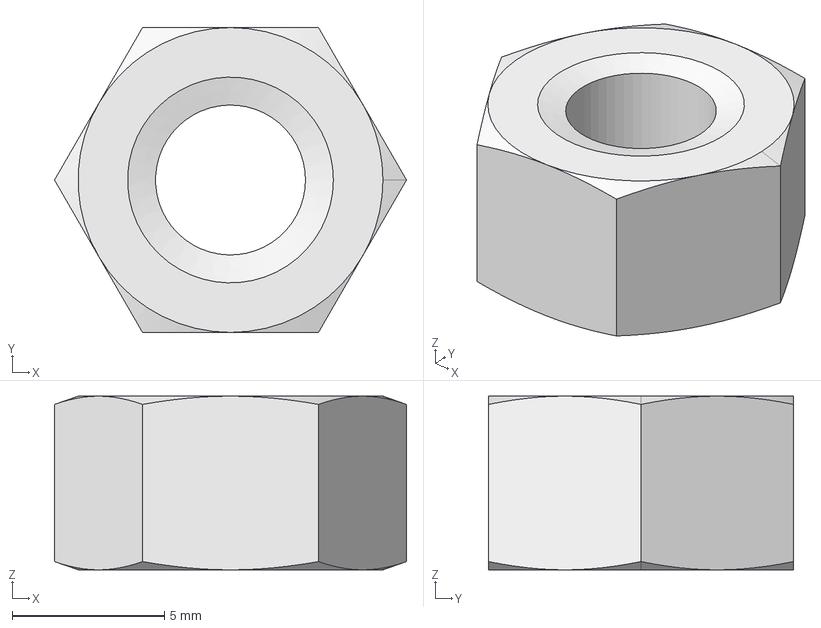
[picture p167: CAD file, 2017-09-25]
upklib_v2/schraubenmuttern/m6nut.fcstd
11.5 x 10.0 x 5.70 mm
