CollectiveOpenSourceHardware/LibreSolarBox/upklib_v2/slider/universalaxis_belt/motorSide_8mm_rods_v02.FCStd

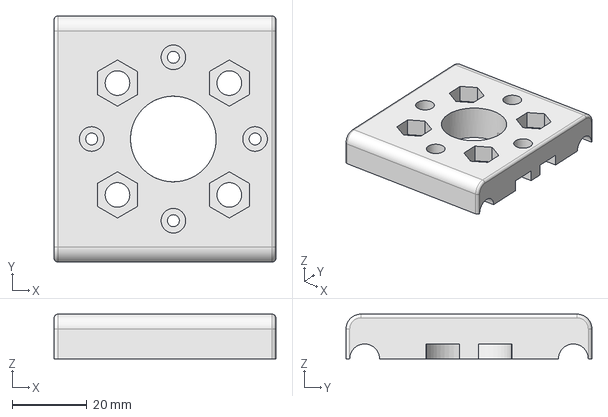
[picture p168: CAD file, 2017-10-14]
upklib_v2/slider/universalaxis_belt/motorSide_8mm_rods_v02.FCStd
59.5 x 66.0 x 12.0 mm
