CollectiveOpenSourceHardware/LibreSolarBox/upklib_v2/winkel/angle40.fcstd

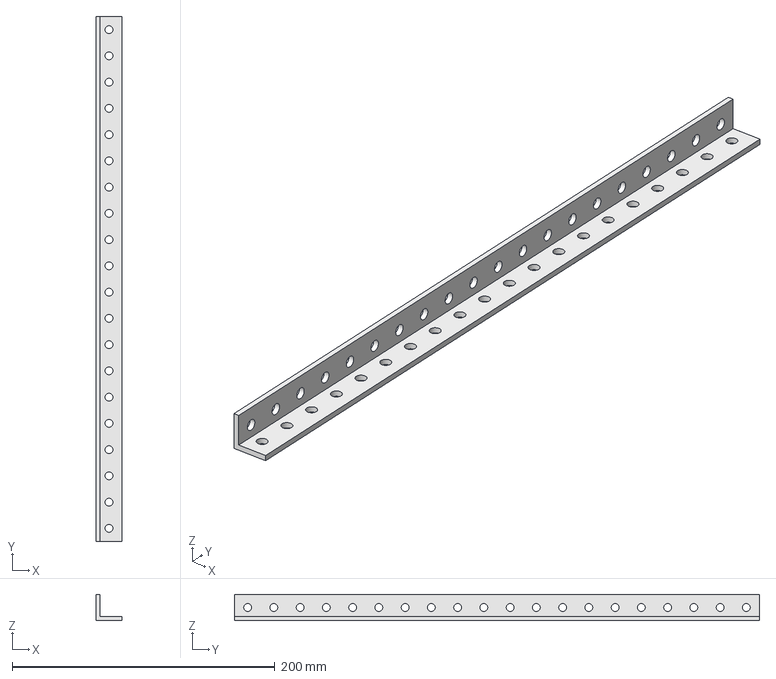
[picture p170: CAD file, 2017-09-25]
upklib_v2/winkel/angle40.fcstd
20.0 x 400.0 x 20.0 mm
