CollectiveOpenSourceHardware/LibreSolarBox/boxframe/buildinstructional/upright/upright2.fcstd

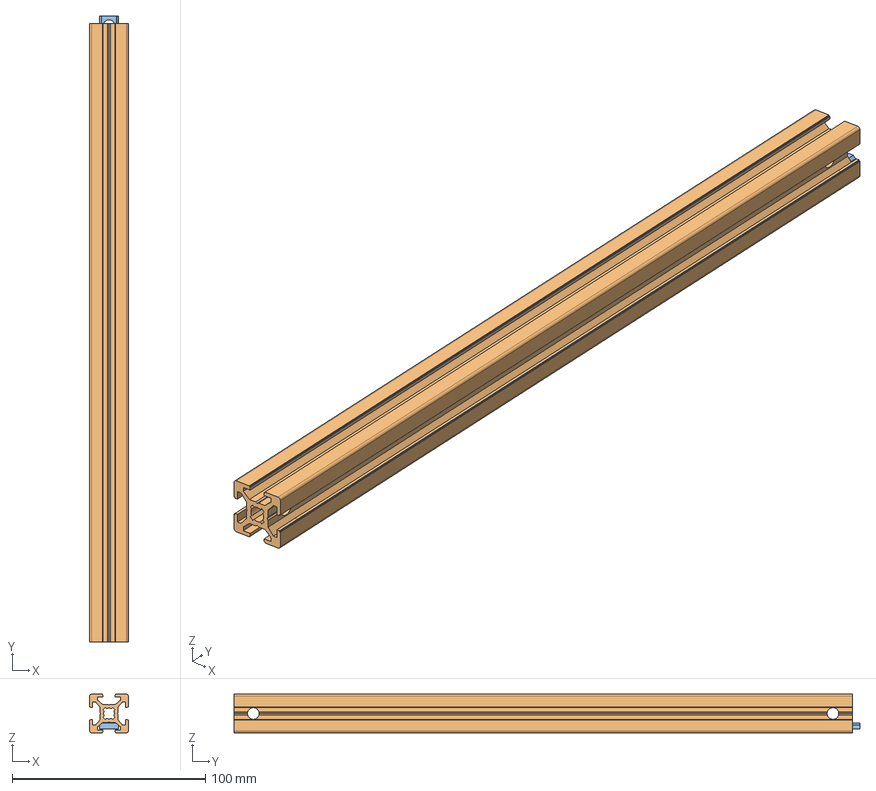
[picture p173: CAD file, 2018-08-25]
boxframe/buildinstructional/upright/upright2.fcstd
20.0 x 324.0 x 20.0 mm
m6nutplate
