CollectiveOpenSourceHardware/LibreSolarBox/upklib_v2/flachprofile/all_flatplates.fcstd

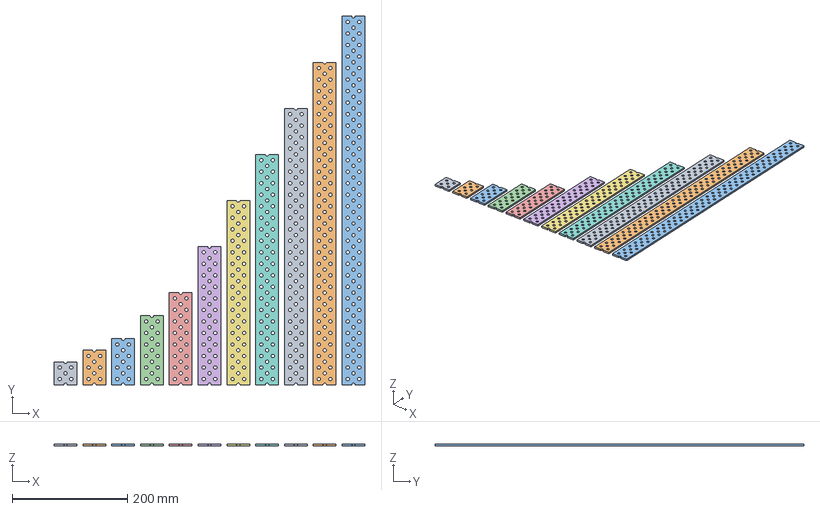
[picture p175: CAD file, 2017-09-25]
upklib_v2/flachprofile/all_flatplates.fcstd
540.0 x 640.0 x 4.00 mm
upk_flatplate40
upk_flatplate60
upk_flatplate80
upk_flatplate120
upk_flatplate160
upk_flatplate240
upk_flatplate320
upk_flatplate400
upk_flatplate480
upk_flatplate560
upk_flatplate640
