CollectiveOpenSourceHardware/LibreSolarBox/upklib_v2/frameset/myhinge5c.fcstd

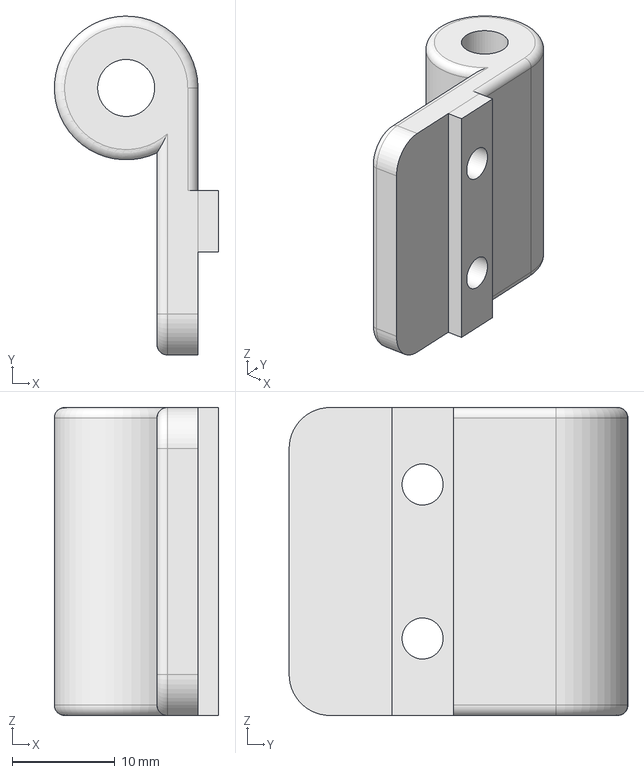
[picture p176: CAD file, 2017-09-25]
upklib_v2/frameset/myhinge5c.fcstd
16.0 x 33.0 x 30.0 mm
