CollectiveOpenSourceHardware/LibreSolarBox/upklib_v2/slider/universalaxis_belt/carriage_8mm_rods_v02.FCStd

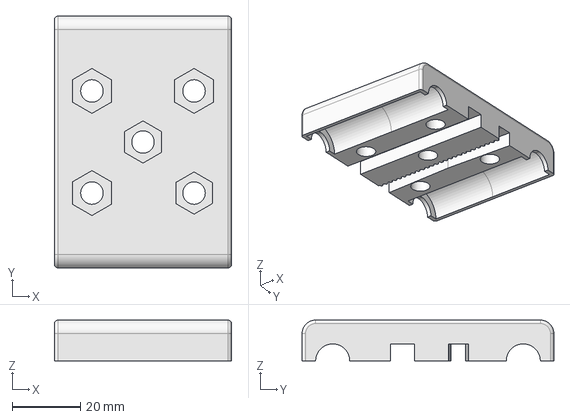
[picture p177: CAD file, 2017-10-14]
upklib_v2/slider/universalaxis_belt/carriage_8mm_rods_v02.FCStd
52.0 x 74.0 x 12.0 mm
