CollectiveOpenSourceHardware/LibreSolarBox/upklib_v2/winkel/angle6.fcstd

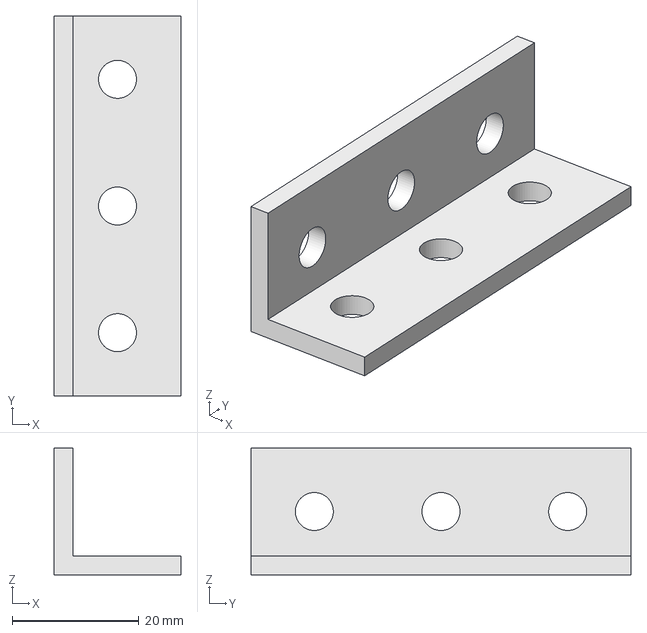
[picture p179: CAD file, 2017-09-25]
upklib_v2/winkel/angle6.fcstd
20.0 x 60.0 x 20.0 mm
