CollectiveOpenSourceHardware/LibreSolarBox/boxframe/buildinstructional/innerplates/innerplate3.fcstd

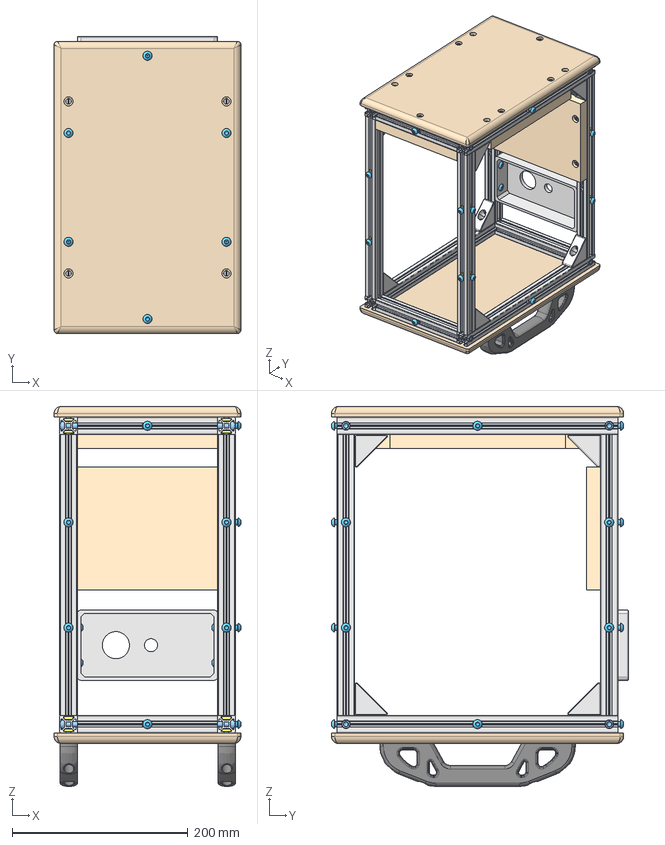
[picture p180: CAD file, 2018-08-29]
boxframe/buildinstructional/innerplates/innerplate3.fcstd
213.0 x 338.5 x 433.0 mm
tslot32con
tslot16
tslot16_001
tslot32con_001
M6x25-Screw
M6x25-Screw004
M6x25-Screw005
M6x25-Screw006
tslot32con001
tslot041
tslot16_002
tslot32con_002
M6x25-Screw012
M6x25-Screw015
M6x25-Screw017
M6x25-Screw016
m6nutplate020uf
m6nutplate021lf
m6nutplate022lf
m6nutplate023lf
m6nutplate024lf
m6nutplate025lf
m6nutplate026lf
m6nutplate027lf
m6nutplate028uf
m6nutplate029uf
m6nutplate030lf
m6nutplate031lf
m6nutplate032uf
m6nutplate033lf
m6nutplate023
upright4
m6nutplate025uf001
m6nutplate022uf001
m6nutplate031lf001
M6x12-Screw022
upright005
m6nutplate031lf002
M6x12-Screw025
upright006
m6nutplate031lf003
M6x12-Screw028
upright007
m6nutplate031lf004
M6x12-Screw031
m6nutplatesidecover
m6nutplatesidecover001
m6nutplatesidecover002
m6nutplatesidecover003
m6nutplatesidecover004
m6nutplatesidecover005
m6nutplatesidecover006
m6nutplatesidecover007
m6nutplatefrontcover
m6nutplatefrontcover001
m6nutplatefrontcover002
m6nutplatefrontcover003
m6nutplatefrontcover004
m6nutplatefrontcover005
m6nutplatefrontcover006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
