CollectiveOpenSourceHardware/LibreSolarBox/boxframe/buildinstructional/upright/upright3_ex.fcstd

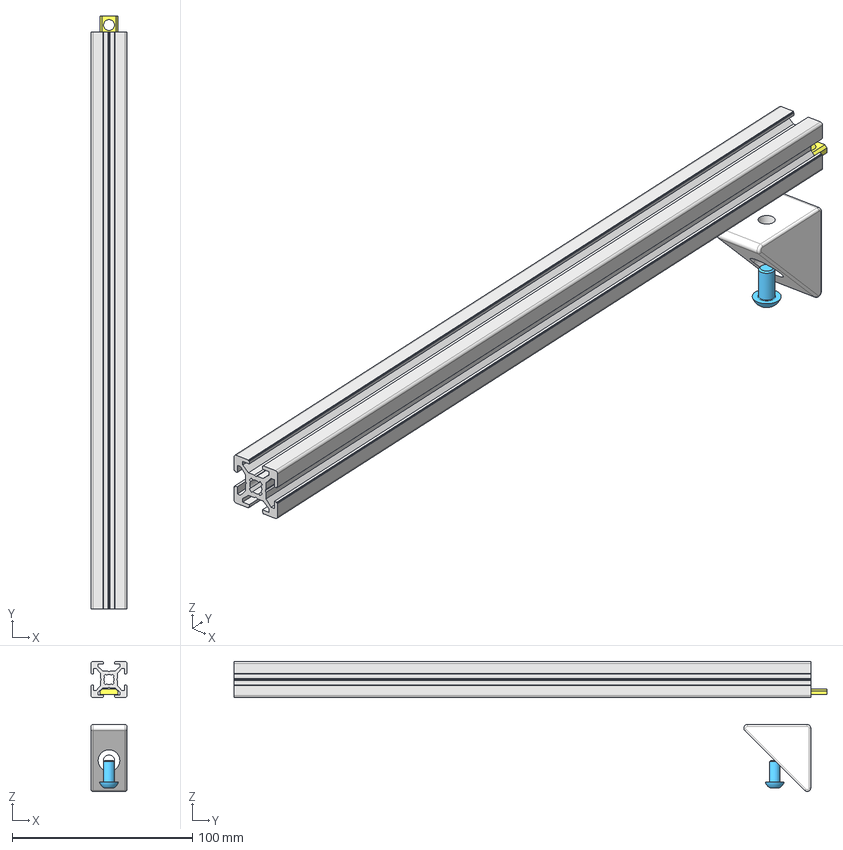
[picture p182: CAD file, 2018-08-25]
boxframe/buildinstructional/upright/upright3_ex.fcstd
20.0 x 329.0 x 72.2 mm
tslot32
m6nutplate
M6x12-Screw001
RAcorner
