CollectiveOpenSourceHardware/LibreSolarBox/boxframe/upkframe_v6/topbottomNG2b.fcstd

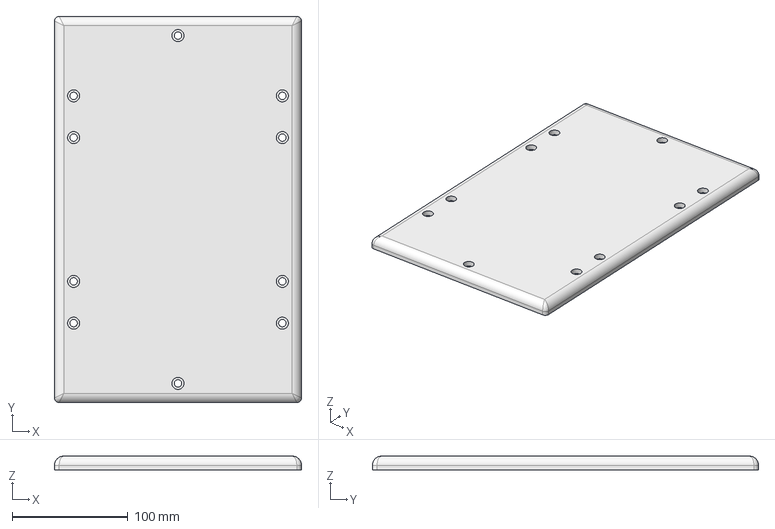
[picture p183: CAD file, 2018-02-01]
boxframe/upkframe_v6/topbottomNG2b.fcstd
213.0 x 333.0 x 12.0 mm
