CollectiveOpenSourceHardware/LibreSolarBox/upklib_v2/flachprofile/flatplate32.fcstd

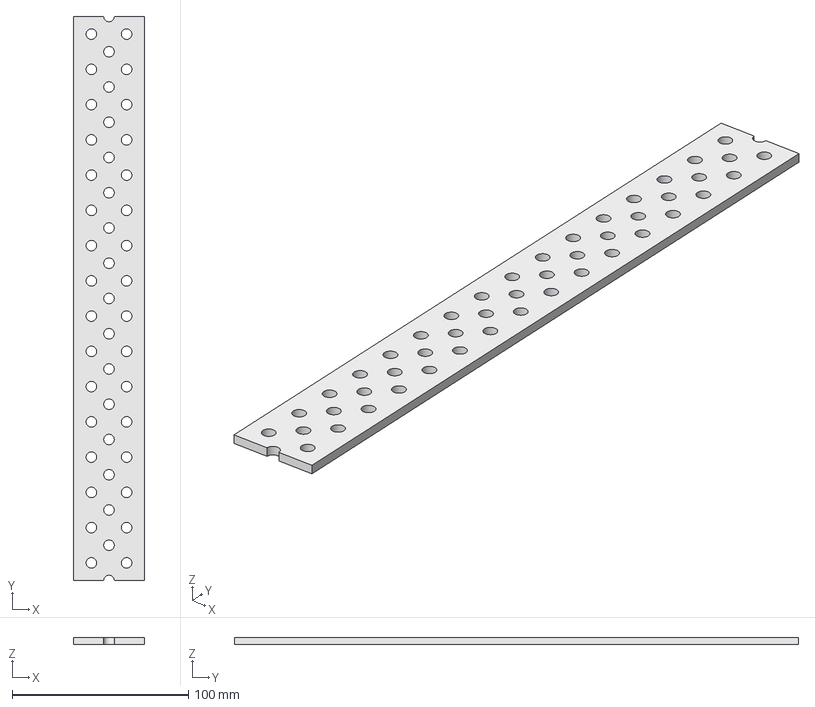
[picture p184: CAD file, 2017-09-25]
upklib_v2/flachprofile/flatplate32.fcstd
40.0 x 320.0 x 4.00 mm
