CollectiveOpenSourceHardware/LibreSolarBox/upklib_v2/frameset/endkappe1d.fcstd

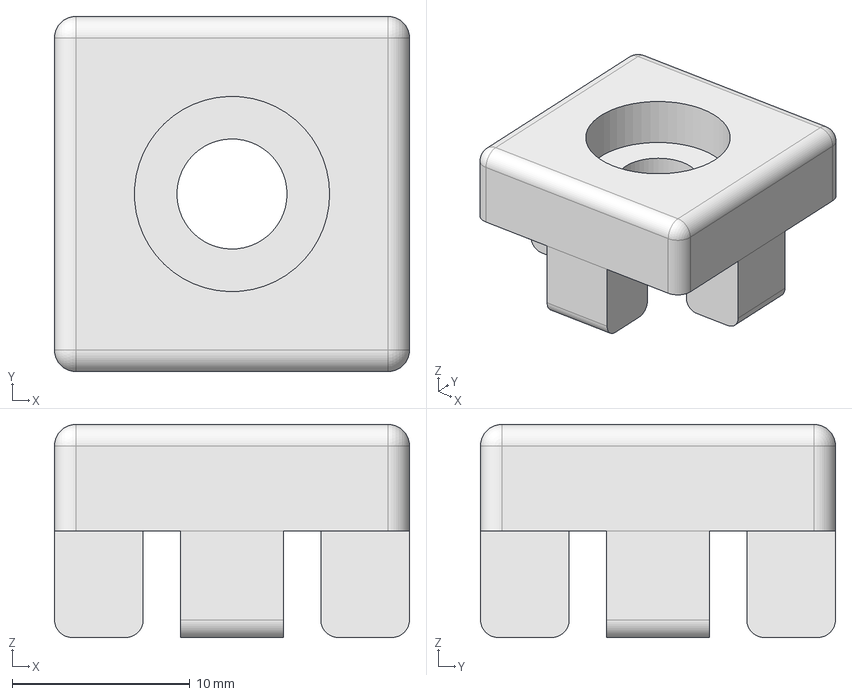
[picture p185: CAD file, 2017-09-25]
upklib_v2/frameset/endkappe1d.fcstd
20.0 x 20.0 x 12.0 mm
