CollectiveOpenSourceHardware/LibreSolarBox/upklib_v2/tslotprofile/tslot12con.fcstd

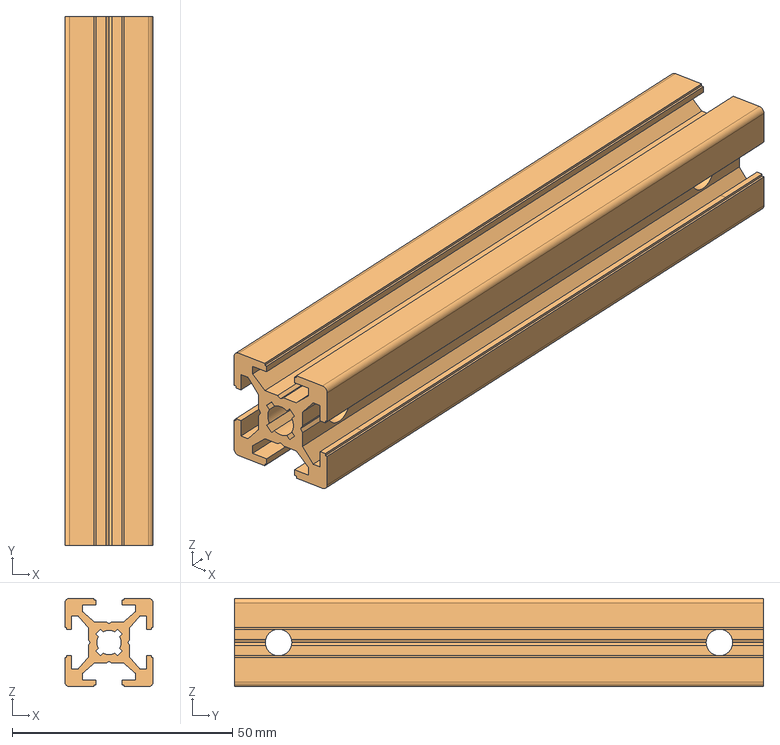
[picture p186: CAD file, 2017-09-25]
upklib_v2/tslotprofile/tslot12con.fcstd
20.0 x 120.0 x 20.0 mm
