CollectiveOpenSourceHardware/LibreSolarBox/boxframe/buildinstructional/upright/upright1.fcstd

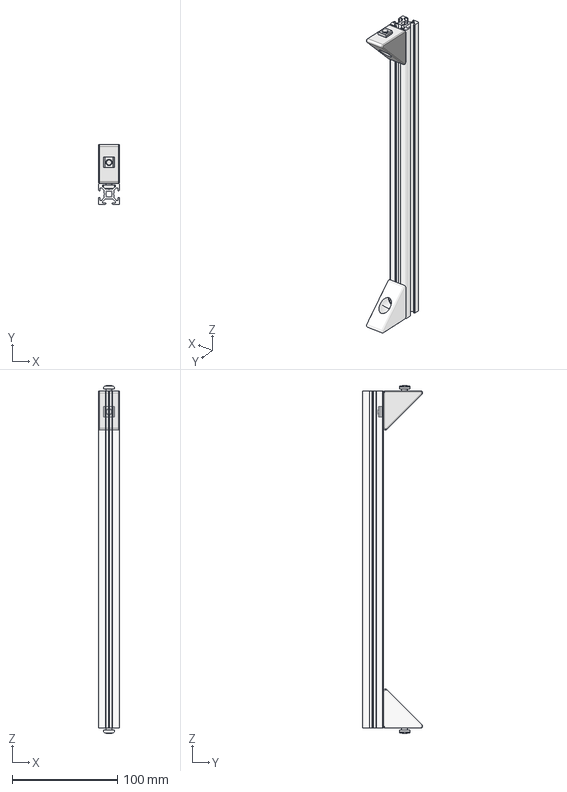
[picture p189: CAD file, 2018-08-25]
boxframe/buildinstructional/upright/upright1.fcstd
20.0 x 57.2 x 330.0 mm
tslot32_001
