CollectiveOpenSourceHardware/LibreSolarBox/boxframe/upkframe_v6/topbottomNG2.fcstd

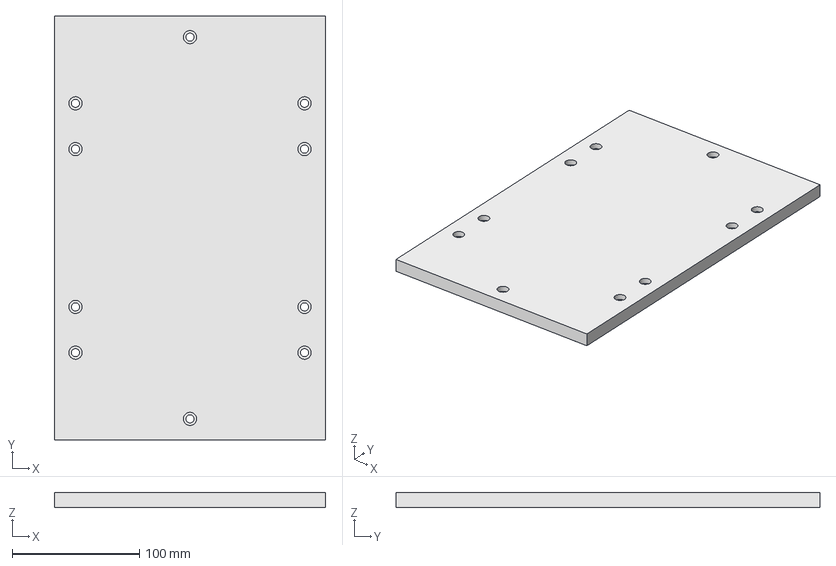
[picture p190: CAD file, 2018-02-01]
boxframe/upkframe_v6/topbottomNG2.fcstd
213.0 x 333.0 x 12.0 mm
