CollectiveOpenSourceHardware/LibreSolarBox/upklib_v2/flachprofile/flatplate6.fcstd

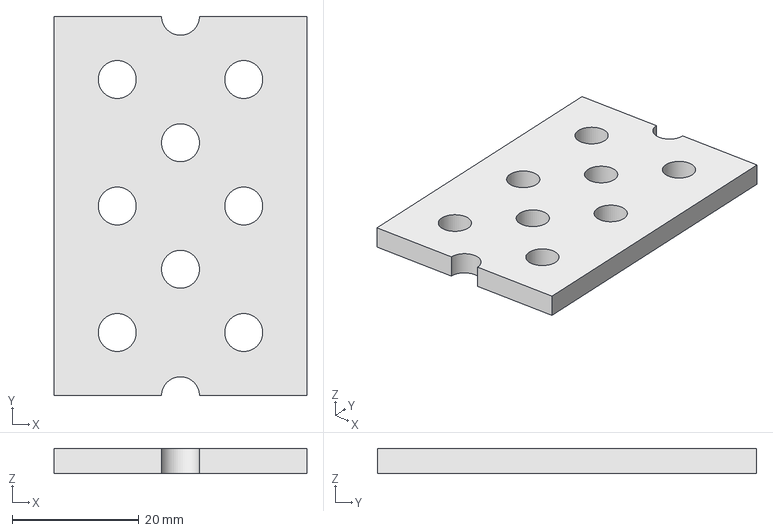
[picture p191: CAD file, 2017-09-25]
upklib_v2/flachprofile/flatplate6.fcstd
40.0 x 60.0 x 4.00 mm
