CollectiveOpenSourceHardware/LibreSolarBox/upklib_v2/schraubenmuttern/wash6.4x12x1.6.fcstd

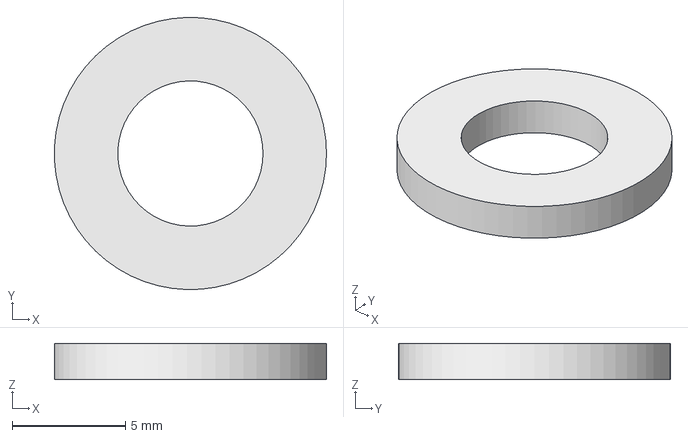
[picture p192: CAD file, 2017-09-25]
upklib_v2/schraubenmuttern/wash6.4x12x1.6.fcstd
12.0 x 12.0 x 1.60 mm
