CollectiveOpenSourceHardware/LibreSolarBox/upklib_v2/tslotprofile/tslot6con.fcstd

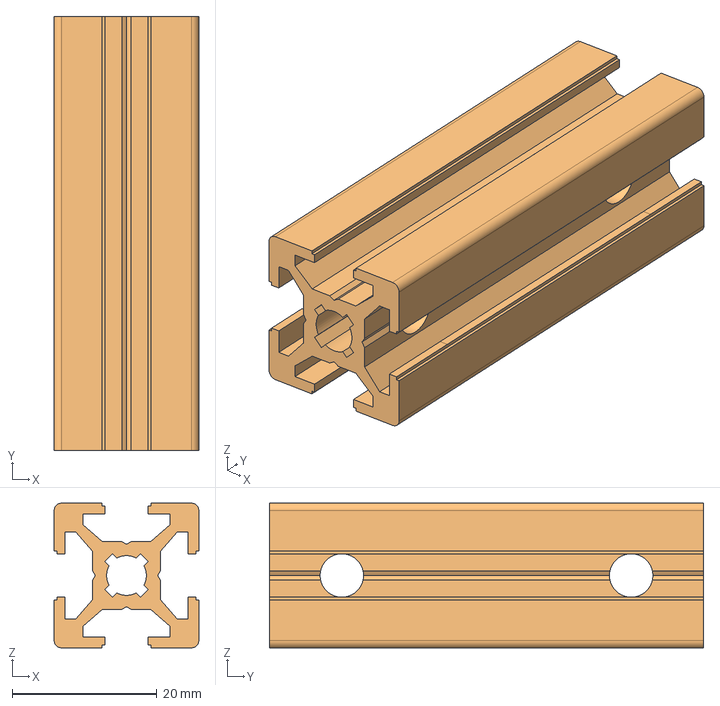
[picture p193: CAD file, 2017-09-25]
upklib_v2/tslotprofile/tslot6con.fcstd
20.0 x 60.0 x 20.0 mm
