CollectiveOpenSourceHardware/LibreSolarBox/upklib_v2/winkel/angle8.fcstd

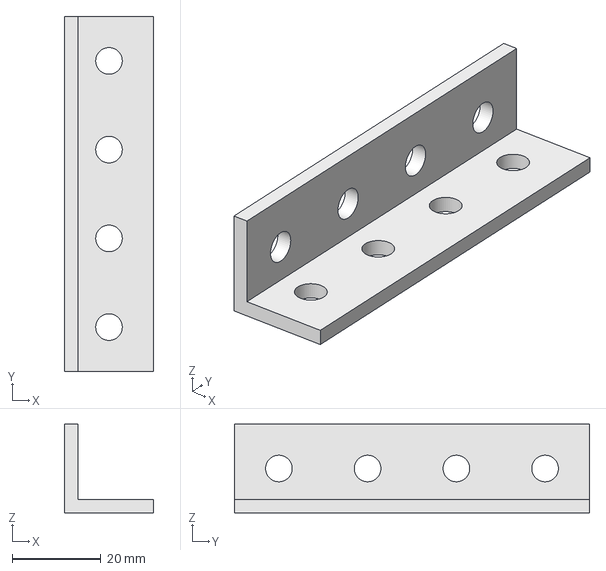
[picture p194: CAD file, 2017-09-25]
upklib_v2/winkel/angle8.fcstd
20.0 x 80.0 x 20.0 mm
