CollectiveOpenSourceHardware/LibreSolarBox/boxframe/buildinstructional/rawframe/rawframe3.fcstd

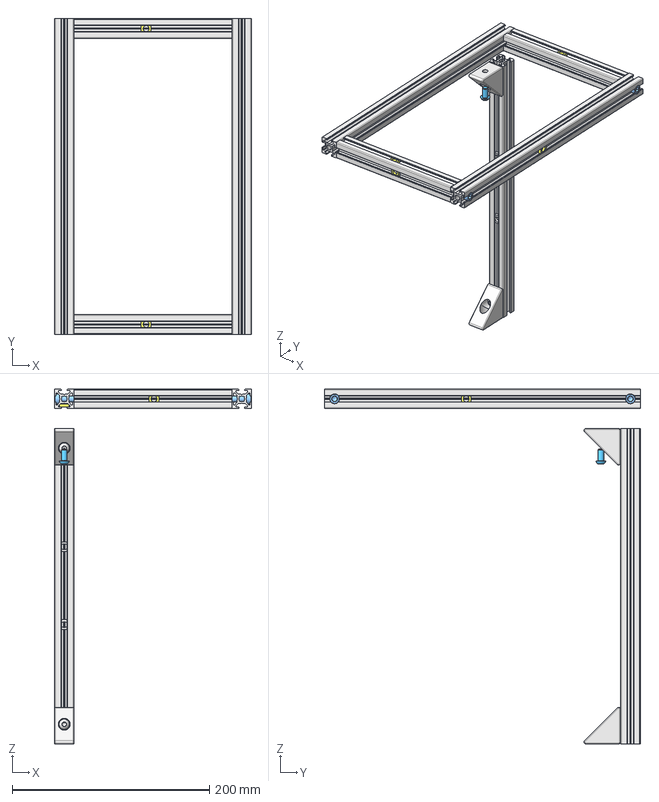
[picture p197: CAD file, 2018-08-25]
boxframe/buildinstructional/rawframe/rawframe3.fcstd
200.0 x 320.0 x 360.0 mm
tslot32con001
tslot041
tslot16_002
tslot32con_002
M6x25-Screw012
M6x25-Screw015
M6x25-Screw017
M6x25-Screw016
m6nutplate021lf
m6nutplate022lf
m6nutplate023lf
m6nutplate024lf
m6nutplate025lf
m6nutplate026lf
m6nutplate027lf
m6nutplate030lf
m6nutplate031lf
m6nutplate033lf
upright4
m6nutplate031lf001
M6x12-Screw022
