CollectiveOpenSourceHardware/LibreSolarBox/boxframe/buildinstructional/upright/upright4.fcstd

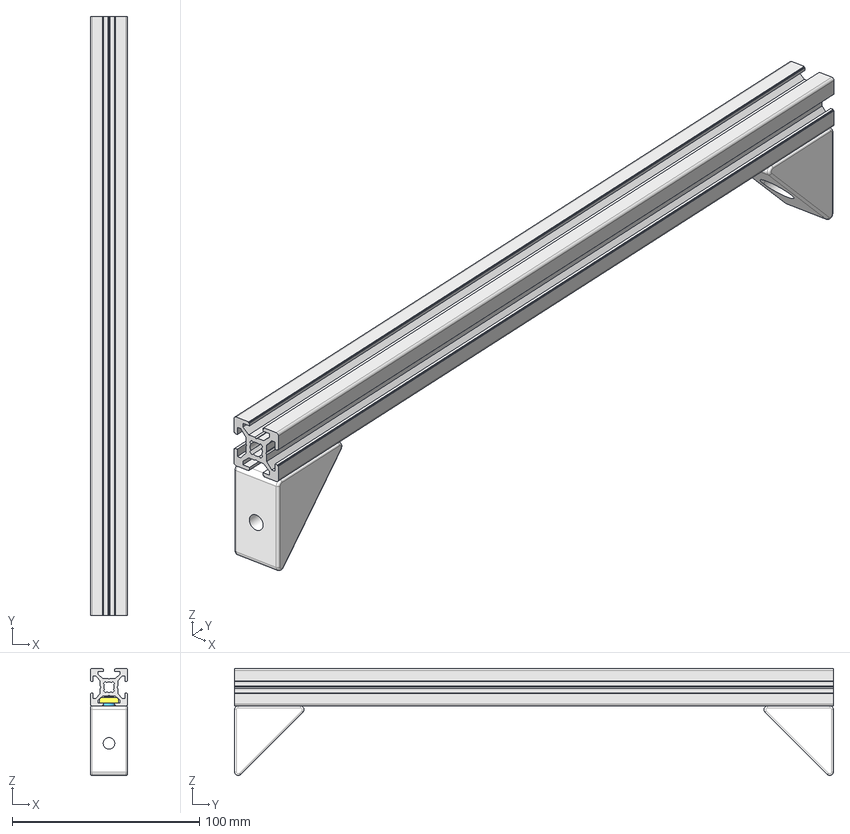
[picture p198: CAD file, 2018-08-25]
boxframe/buildinstructional/upright/upright4.fcstd
20.0 x 320.0 x 57.2 mm
tslot32
m6nutplate
M6x12-Screw001
RAcorner
m6nutplate001
M6x12-Screw002
RAcorner001
m6nutplate002
m6nutplate003
