CollectiveOpenSourceHardware/LibreSolarBox/boxframe/upkframe_v6/UPKframeNG2j.fcstd

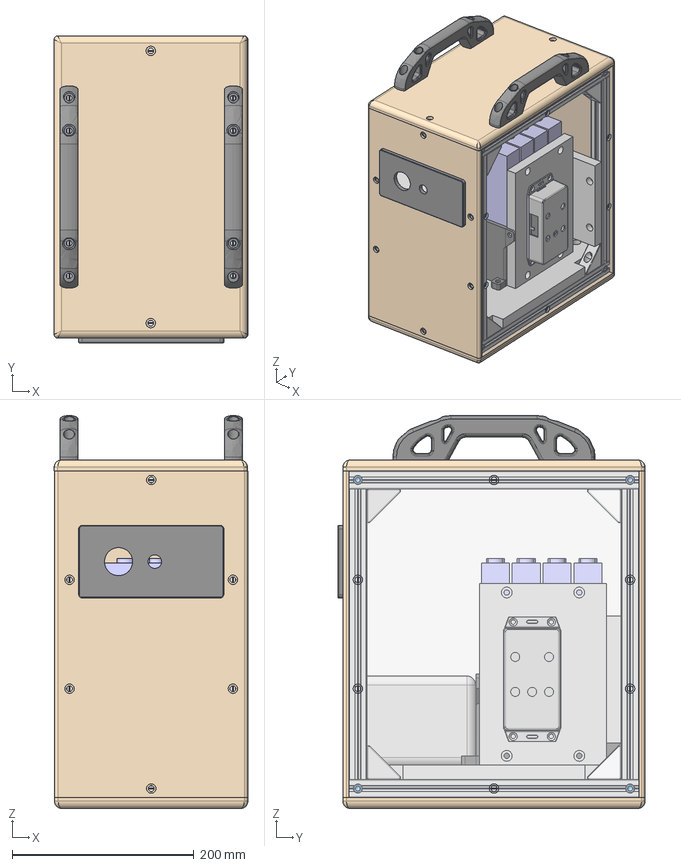
[picture p199: CAD file, 2018-02-01]
boxframe/upkframe_v6/UPKframeNG2j.fcstd
213.5 x 338.5 x 433.0 mm
tslot32con
tslot16
tslot16_001
tslot32con_001
M6x25-Screw
M6x25-Screw004
M6x25-Screw005
M6x25-Screw006
tslot32con001
tslot041
tslot16_002
tslot32con_002
M6x25-Screw007
M6x25-Screw008
M6x25-Screw009
M6x25-Screw010
m6nutplate002
M6x12-Screw002
M6x12-Screw003
m6nutplate003
m6nutplate
M6x12-Screw
M6x12-Screw001
m6nutplate001
m6nutplate004
M6x12-Screw004
M6x12-Screw005
m6nutplate005
m6nutplate006
M6x12-Screw006
M6x12-Screw007
m6nutplate007
tslot32
tslot32_001
tslot32_002
tslot32_003
front_plate
bottom_plate
MPPT
1591XXBF LID
bms-cover
bmsmounting_plate
batterymount
cam72
cam72_001
cam72_002
cam72_003
frontCover
topCover
bottomCover
sideCover
sideCover001
handle
handle001
backCover_ifmount
ifmount
