CollectiveOpenSourceHardware/LibreSolarBox/upklib_v2/flachprofile/flatplate12.fcstd

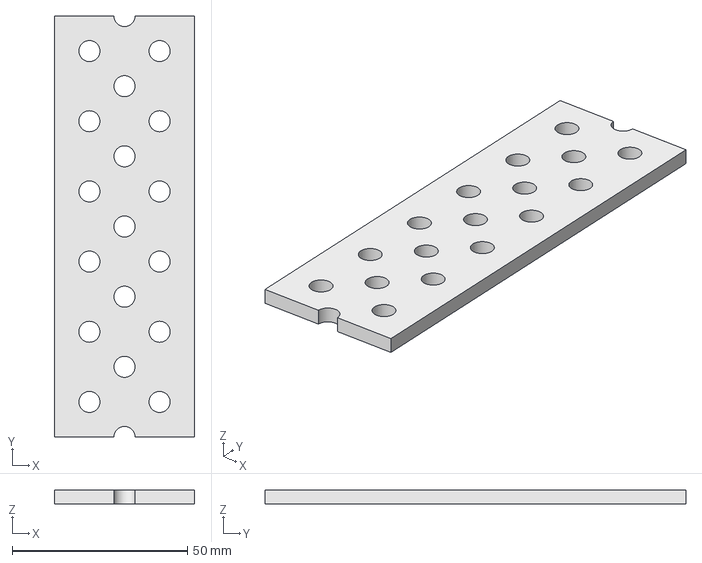
[picture p200: CAD file, 2017-09-25]
upklib_v2/flachprofile/flatplate12.fcstd
40.0 x 120.0 x 4.00 mm
