CollectiveOpenSourceHardware/LibreSolarBox/upklib_v2/tslotprofile/tslot16con.fcstd

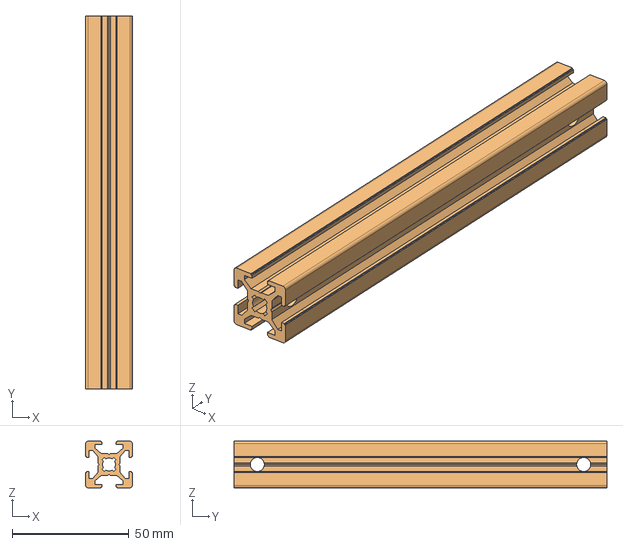
[picture p201: CAD file, 2017-09-25]
upklib_v2/tslotprofile/tslot16con.fcstd
20.0 x 160.0 x 20.0 mm
