CollectiveOpenSourceHardware/LibreSolarBox/upklib_v2/winkel/angle64.fcstd

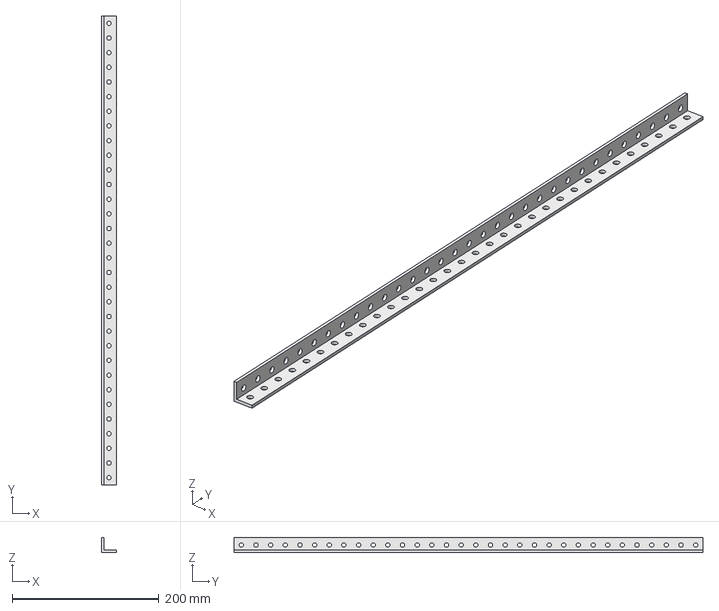
[picture p202: CAD file, 2017-09-25]
upklib_v2/winkel/angle64.fcstd
20.0 x 640.0 x 20.0 mm
