CollectiveOpenSourceHardware/LibreSolarBox/boxframe/buildinstructional/upright/upright3.fcstd

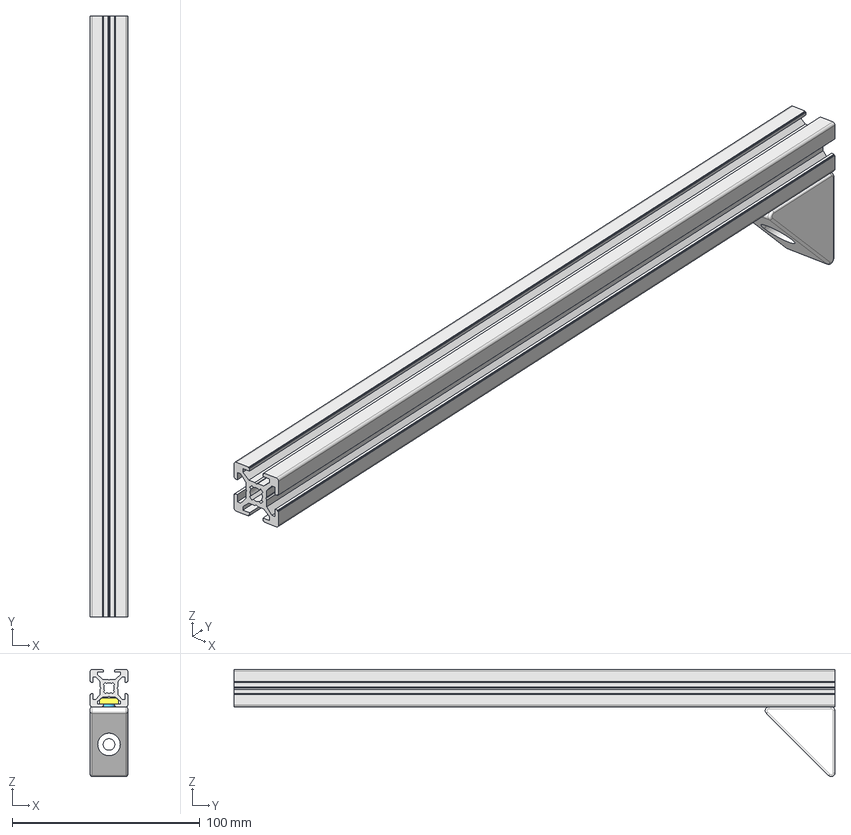
[picture p204: CAD file, 2018-08-25]
boxframe/buildinstructional/upright/upright3.fcstd
20.0 x 320.0 x 57.2 mm
tslot32
m6nutplate
M6x12-Screw001
RAcorner
