CollectiveOpenSourceHardware/LibreSolarBox/boxframe/upkframe_v6/sideCoverNG2.fcstd

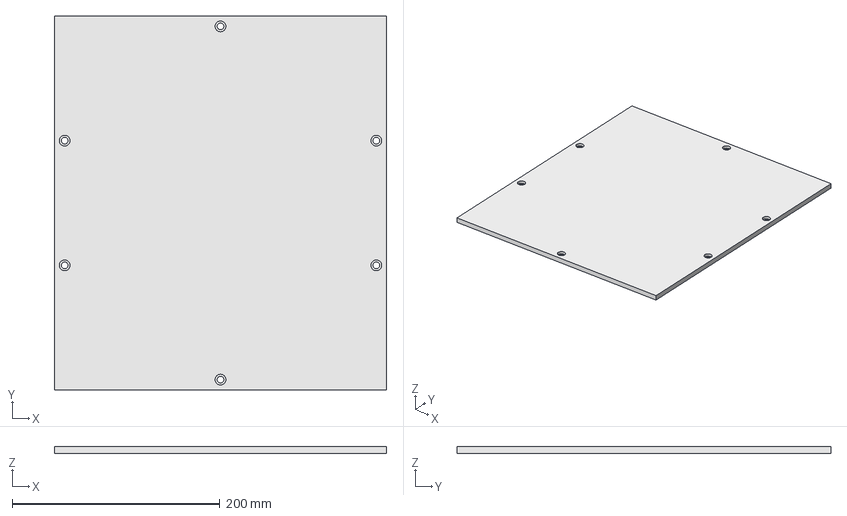
[picture p205: CAD file, 2018-02-01]
boxframe/upkframe_v6/sideCoverNG2.fcstd
320.0 x 360.0 x 6.50 mm
