CollectiveOpenSourceHardware/LibreSolarBox/upklib_v2/flachprofile/flatplate24.fcstd

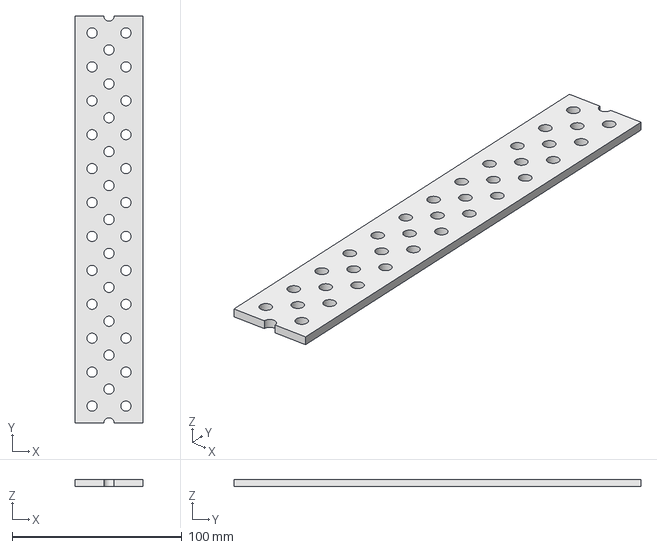
[picture p206: CAD file, 2017-09-25]
upklib_v2/flachprofile/flatplate24.fcstd
40.0 x 240.0 x 4.00 mm
