CollectiveOpenSourceHardware/LibreSolarBox/upklib_v2/tslotprofile/tslot24con.fcstd

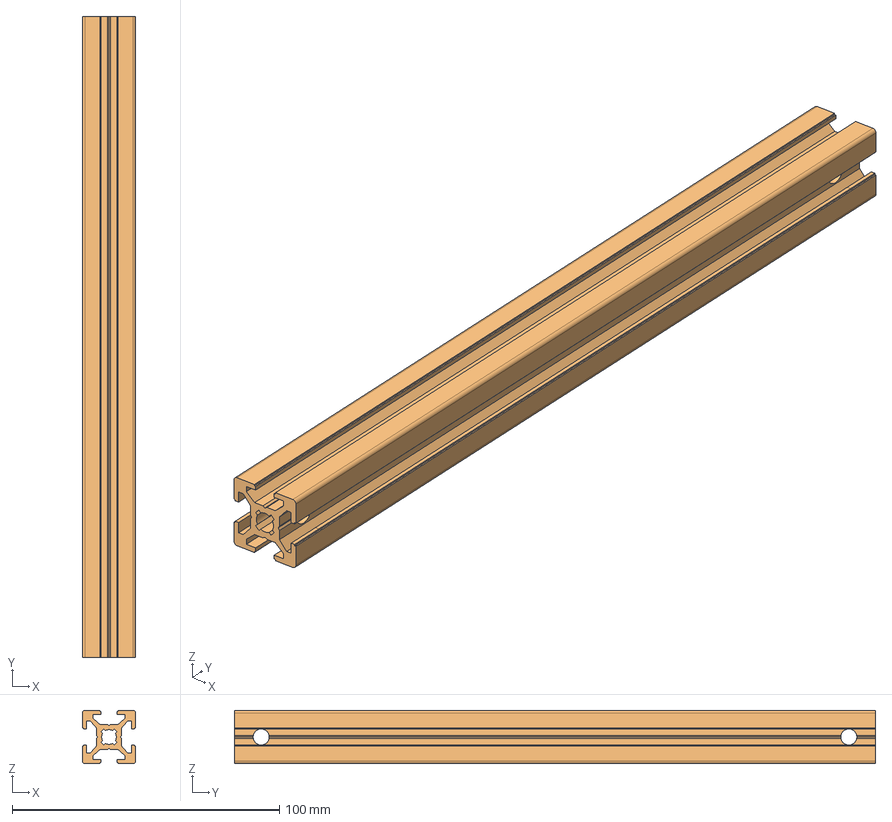
[picture p207: CAD file, 2017-09-25]
upklib_v2/tslotprofile/tslot24con.fcstd
20.0 x 240.0 x 20.0 mm
