CollectiveOpenSourceHardware/LibreSolarBox/upklib_v2/winkel/angle16.fcstd

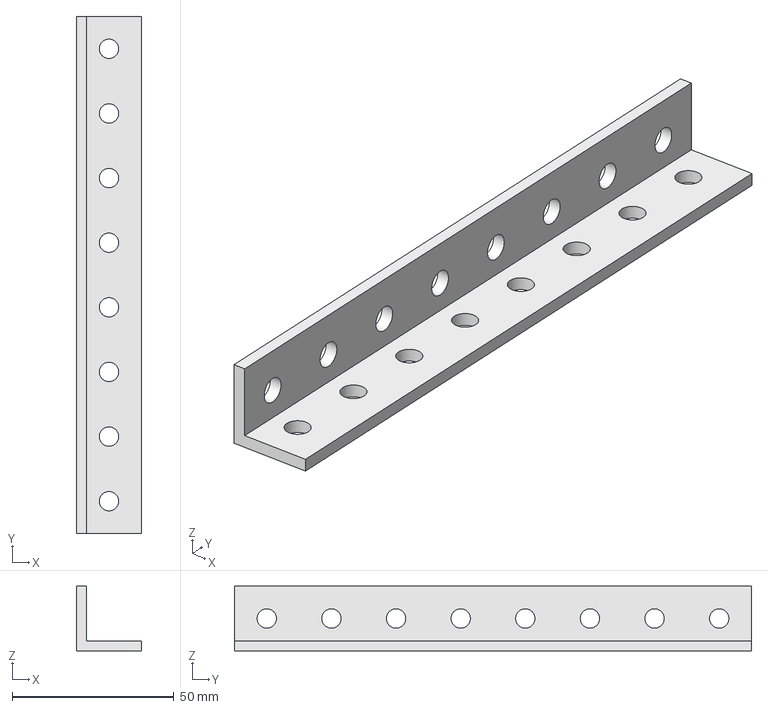
[picture p208: CAD file, 2017-09-25]
upklib_v2/winkel/angle16.fcstd
20.0 x 160.0 x 20.0 mm
