CollectiveOpenSourceHardware/LibreSolarBox/boxframe/upkframe_v6/frontbackNG2c_ifmount.fcstd

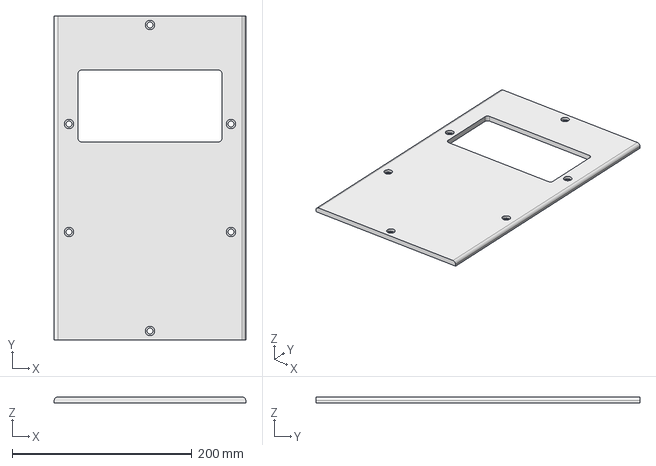
[picture p210: CAD file, 2018-02-01]
boxframe/upkframe_v6/frontbackNG2c_ifmount.fcstd
213.0 x 360.0 x 6.50 mm
