CollectiveOpenSourceHardware/LibreSolarBox/upklib_v2/flachprofile/flatplate56.fcstd

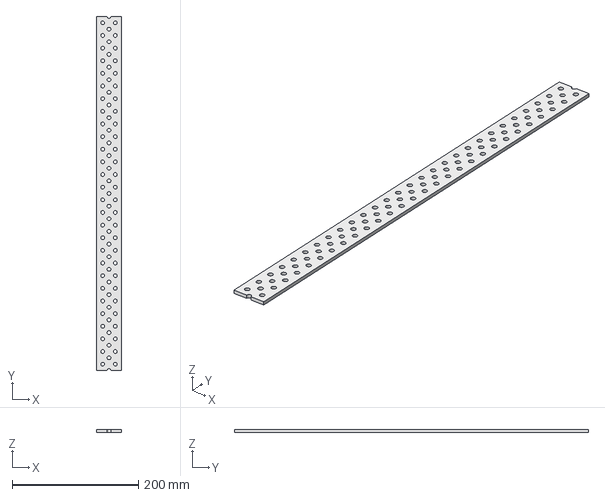
[picture p211: CAD file, 2017-09-25]
upklib_v2/flachprofile/flatplate56.fcstd
40.0 x 560.0 x 4.00 mm
