CollectiveOpenSourceHardware/LibreSolarBox/upklib_v2/winkel/angle56.fcstd

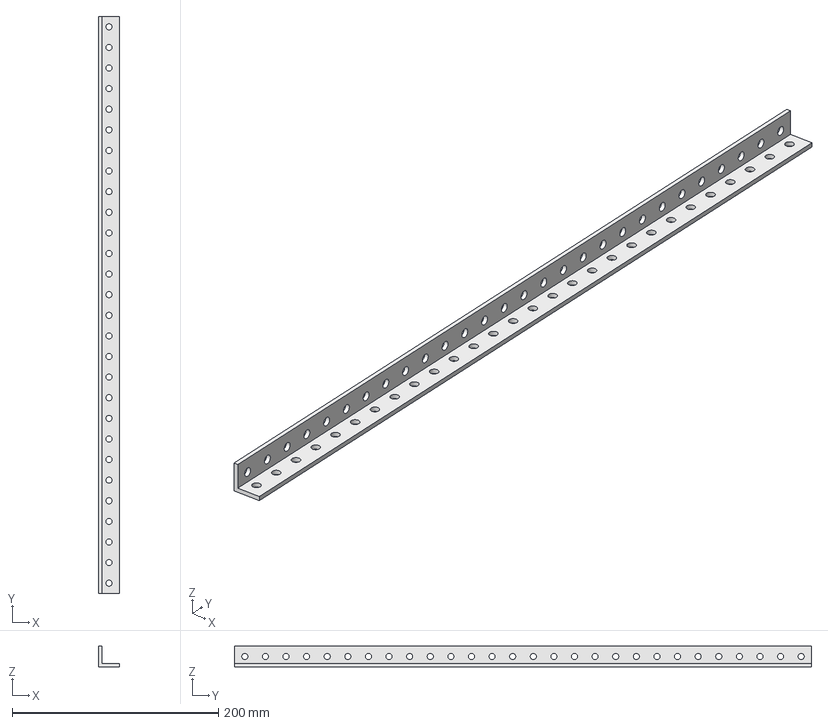
[picture p213: CAD file, 2017-09-25]
upklib_v2/winkel/angle56.fcstd
20.0 x 560.0 x 20.0 mm
