CollectiveOpenSourceHardware/LibreSolarBox/upklib_v2/flachprofile/flatplate8.fcstd

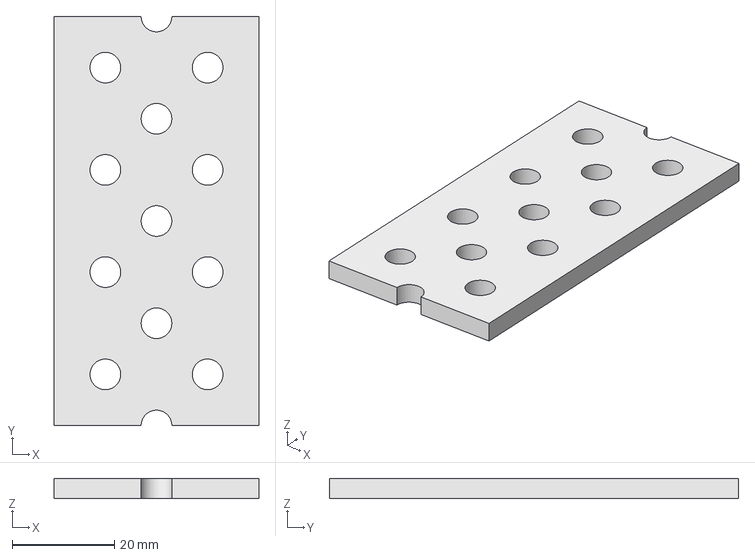
[picture p216: CAD file, 2017-09-25]
upklib_v2/flachprofile/flatplate8.fcstd
40.0 x 80.0 x 4.00 mm
