CollectiveOpenSourceHardware/LibreSolarBox/upklib_v2/schraubenmuttern/m6nutplate.fcstd

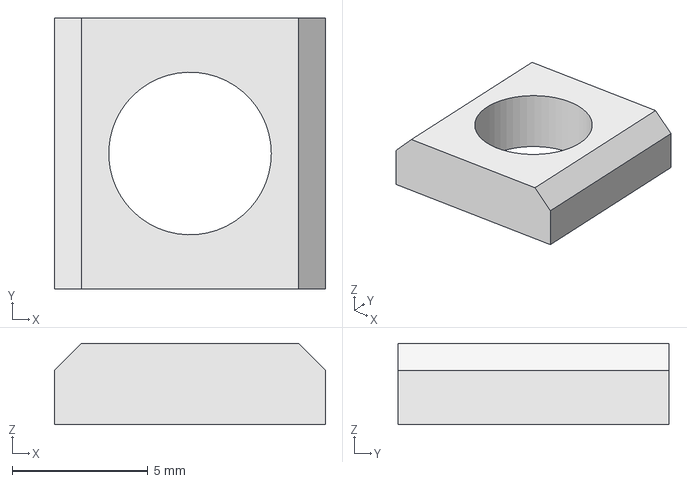
[picture p217: CAD file, 2017-09-25]
upklib_v2/schraubenmuttern/m6nutplate.fcstd
10.0 x 10.0 x 3.00 mm
