CollectiveOpenSourceHardware/LibreSolarBox/upklib_v2/winkel/angle32.fcstd

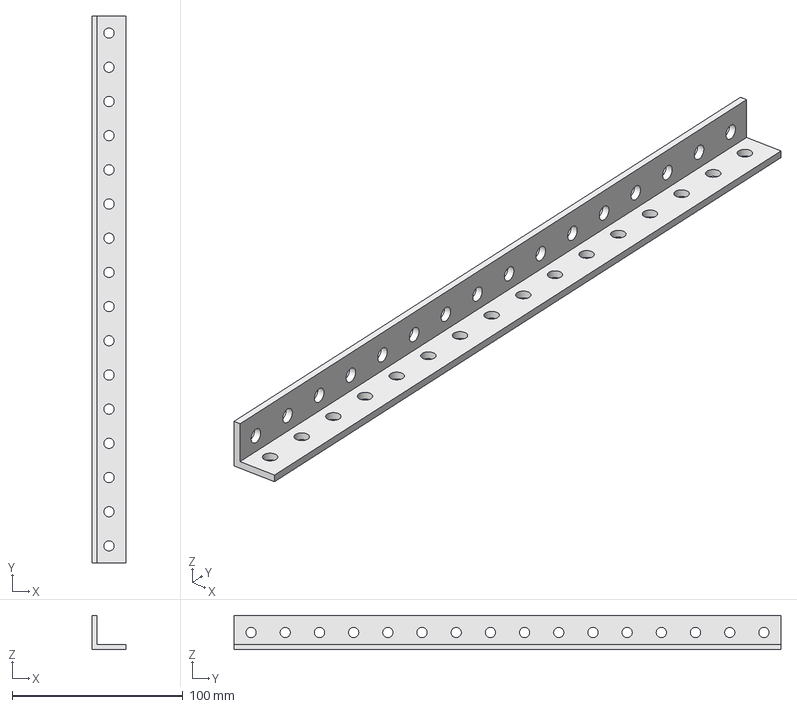
[picture p219: CAD file, 2017-09-25]
upklib_v2/winkel/angle32.fcstd
20.0 x 320.0 x 20.0 mm
