CollectiveOpenSourceHardware/LibreSolarBox/upklib_v2/flachprofile/flatplate4.fcstd

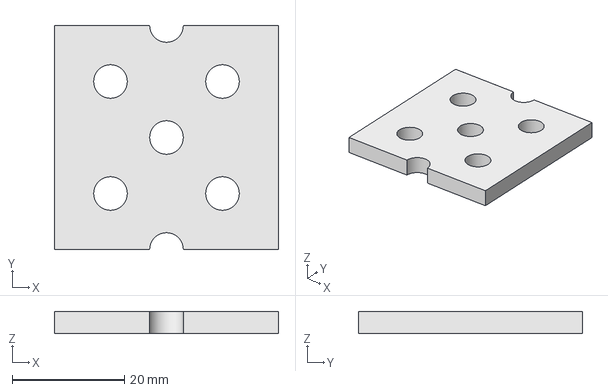
[picture p221: CAD file, 2017-09-25]
upklib_v2/flachprofile/flatplate4.fcstd
40.0 x 40.0 x 4.00 mm
