CollectiveOpenSourceHardware/LibreSolarBox/upklib_v2/winkel/angle2.fcstd

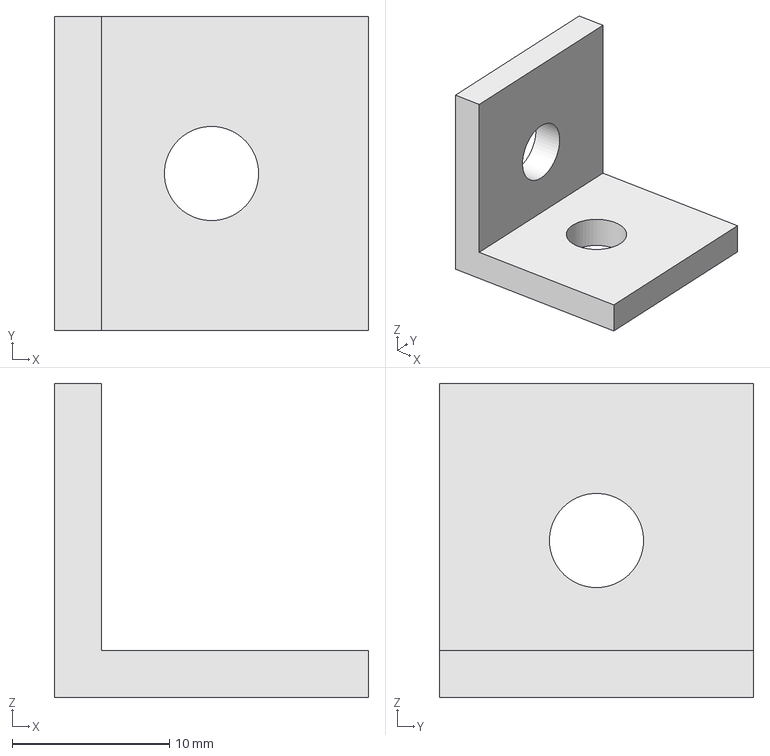
[picture p223: CAD file, 2017-09-25]
upklib_v2/winkel/angle2.fcstd
20.0 x 20.0 x 20.0 mm
