CollectiveOpenSourceHardware/LibreSolarBox/upklib_v2/flachprofile/flatplate16.fcstd

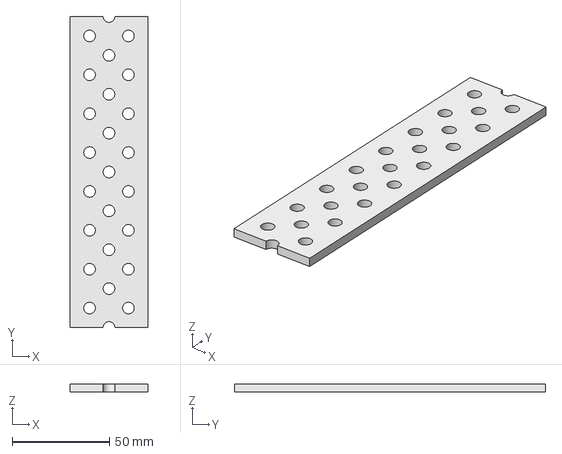
[picture p225: CAD file, 2017-09-25]
upklib_v2/flachprofile/flatplate16.fcstd
40.0 x 160.0 x 4.00 mm
