CollectiveOpenSourceHardware/LibreSolarBox/upklib_v2/winkel/angle48.fcstd

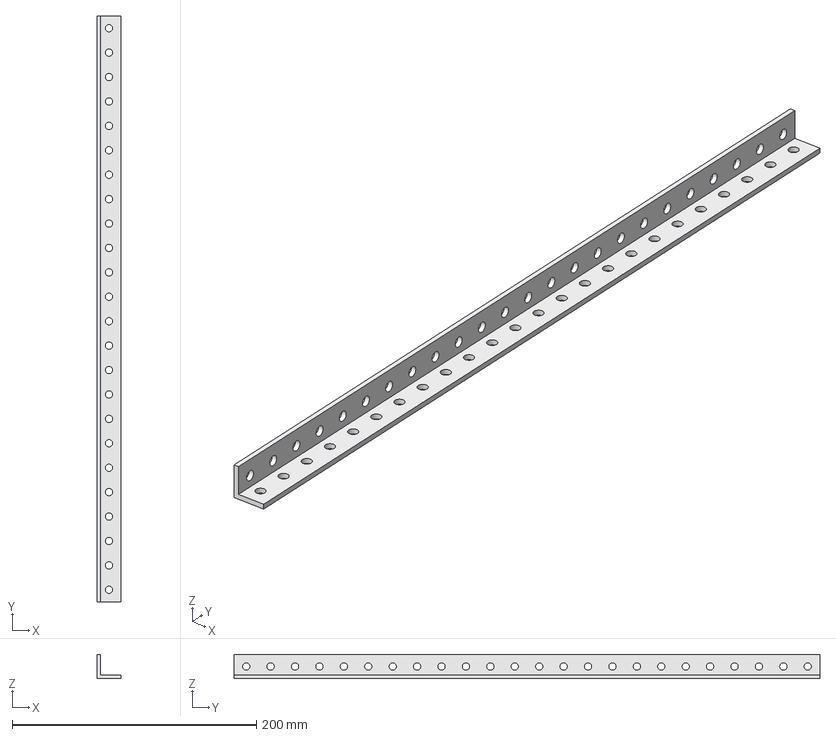
[picture p226: CAD file, 2017-09-25]
upklib_v2/winkel/angle48.fcstd
20.0 x 480.0 x 20.0 mm
