CollectiveOpenSourceHardware/LibreSolarBox/upklib_v2/flachprofile/flatplate48.fcstd

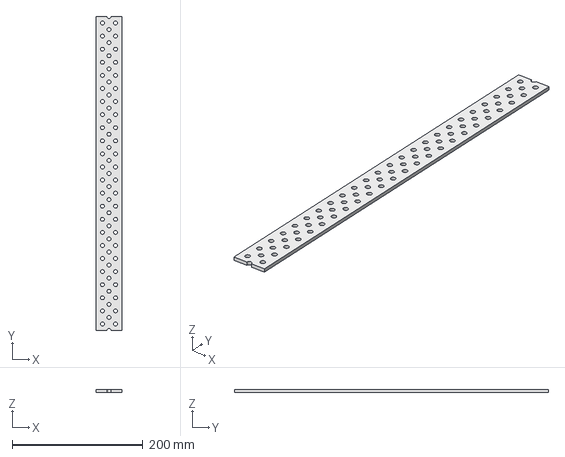
[picture p227: CAD file, 2017-09-25]
upklib_v2/flachprofile/flatplate48.fcstd
40.0 x 480.0 x 4.00 mm
