CollectiveOpenSourceHardware/LibreSolarBox/upklib_v2/tslotprofile/tslot56.fcstd

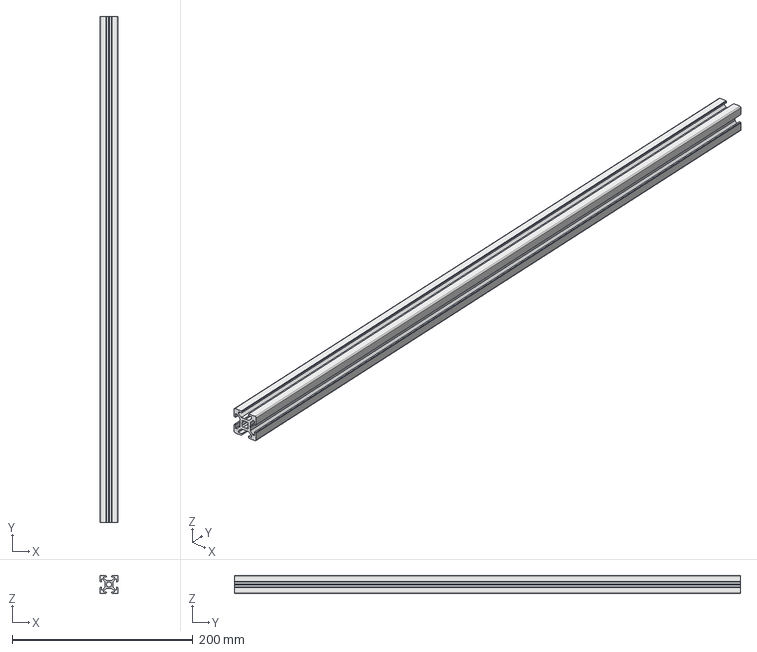
[picture p228: CAD file, 2017-09-25]
upklib_v2/tslotprofile/tslot56.fcstd
20.0 x 560.0 x 20.0 mm
