CollectiveOpenSourceHardware/LibreSolarBox/upklib_v2/winkel/angle4.fcstd

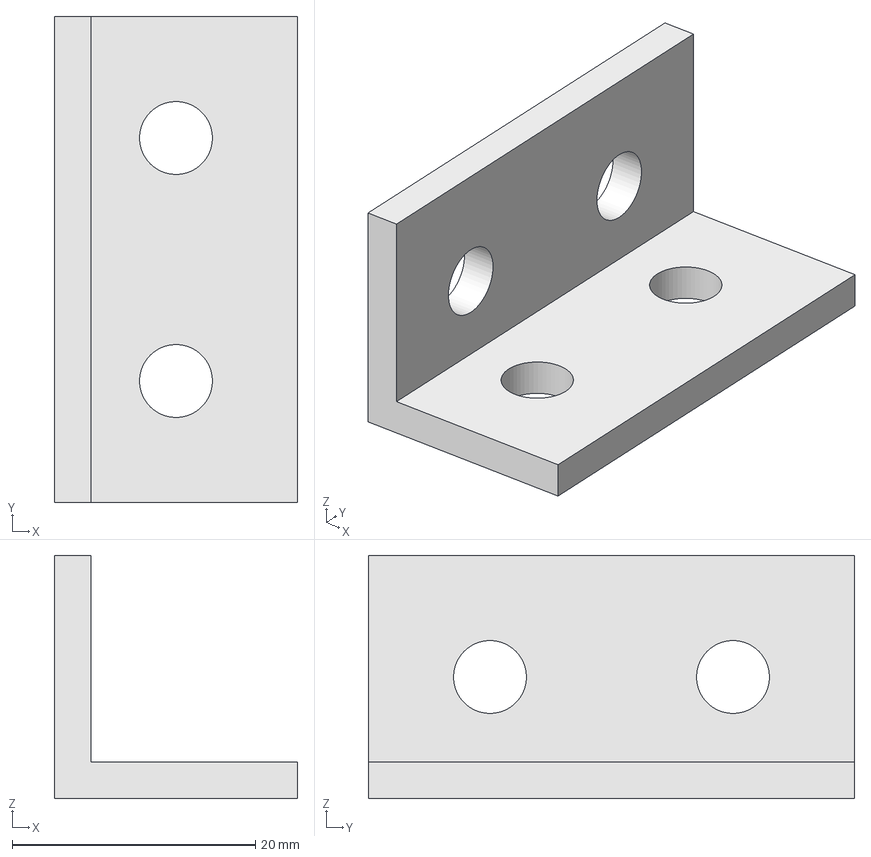
[picture p229: CAD file, 2017-09-25]
upklib_v2/winkel/angle4.fcstd
20.0 x 40.0 x 20.0 mm
