CollectiveOpenSourceHardware/LibreSolarBox/upklib_v2/tslotprofile/tslot8.fcstd

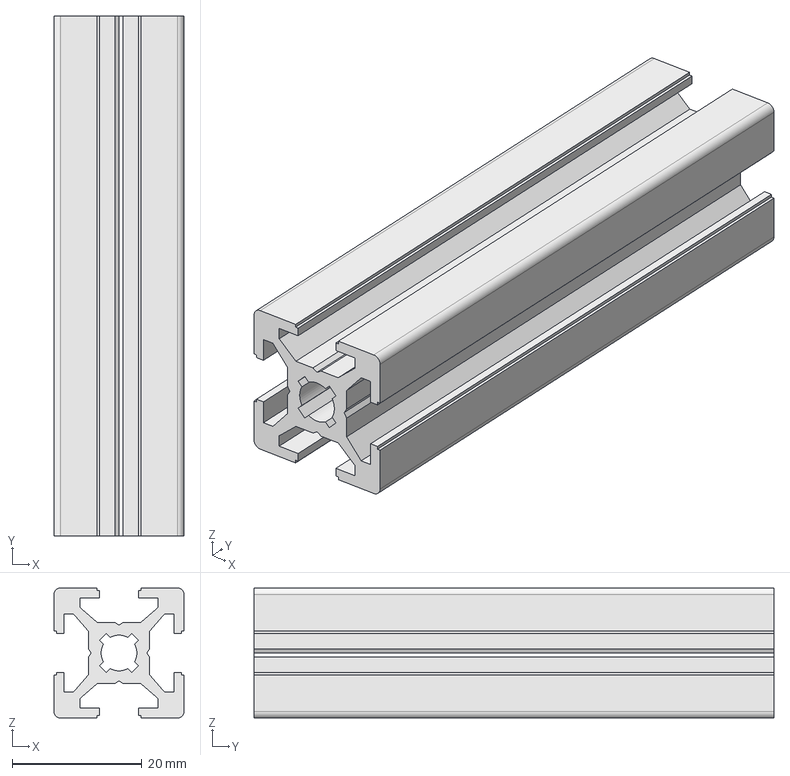
[picture p230: CAD file, 2017-09-25]
upklib_v2/tslotprofile/tslot8.fcstd
20.0 x 80.0 x 20.0 mm
