CollectiveOpenSourceHardware/LibreSolarBox/upklib_v2/winkel/angle24.fcstd

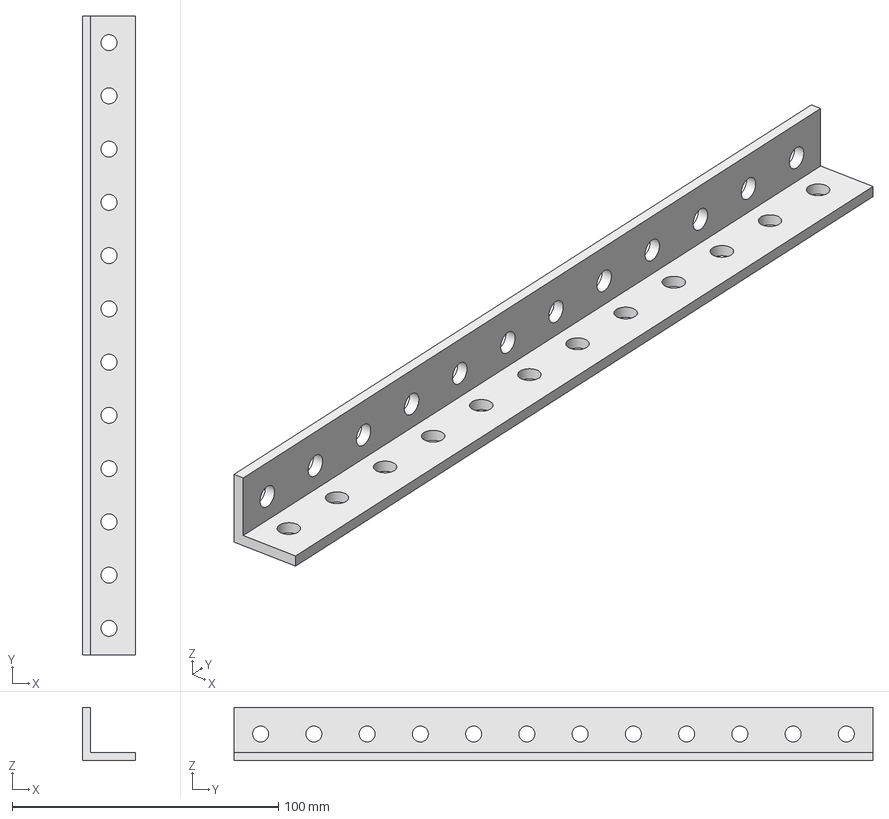
[picture p231: CAD file, 2017-09-25]
upklib_v2/winkel/angle24.fcstd
20.0 x 240.0 x 20.0 mm
