CollectiveOpenSourceHardware/LibreSolarBox/boxframe/upkframe_v6/gateway_case_botom_0.1.FCStd

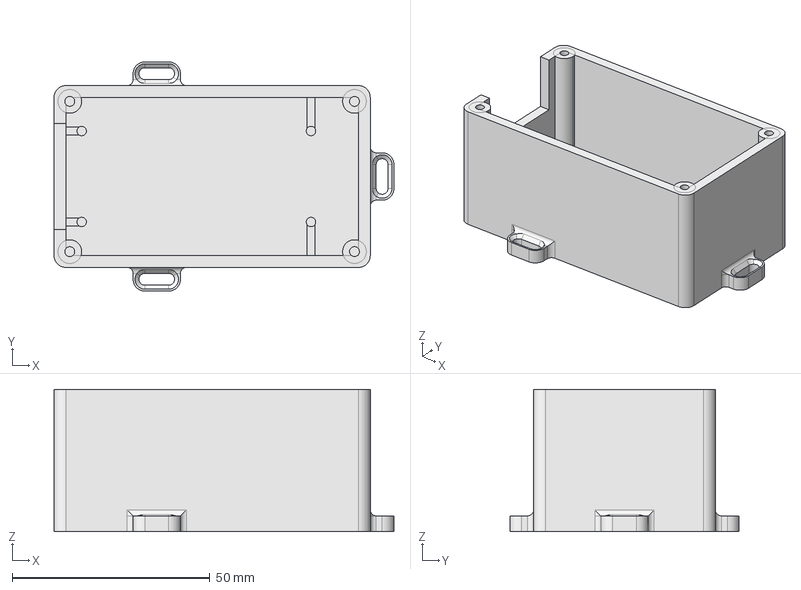
[picture p232: CAD file, 2018-01-25]
boxframe/upkframe_v6/gateway_case_botom_0.1.FCStd
86.0 x 58.0 x 36.0 mm
