CollectiveOpenSourceHardware/LibreSolarBox/boxframe/upkframe_v6/gateway_case_top_0.1.FCStd

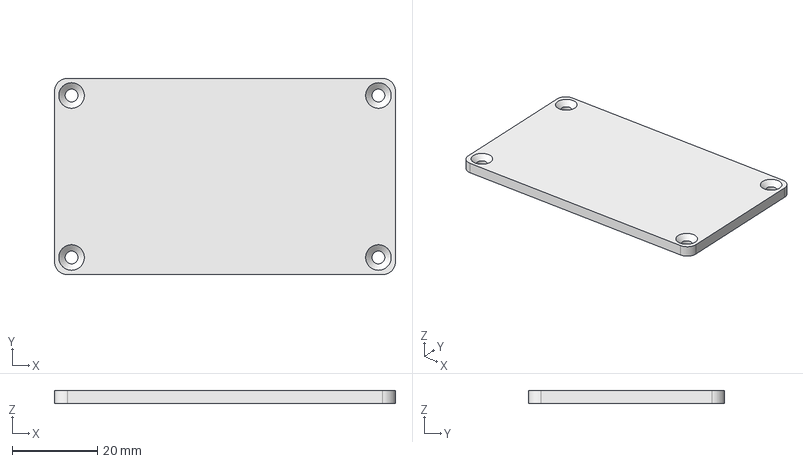
[picture p233: CAD file, 2018-01-25]
boxframe/upkframe_v6/gateway_case_top_0.1.FCStd
80.0 x 46.0 x 3.00 mm
