CollectiveOpenSourceHardware/LibreSolarBox/boxframe/upkframe_v6/batterymount_top.FCStd

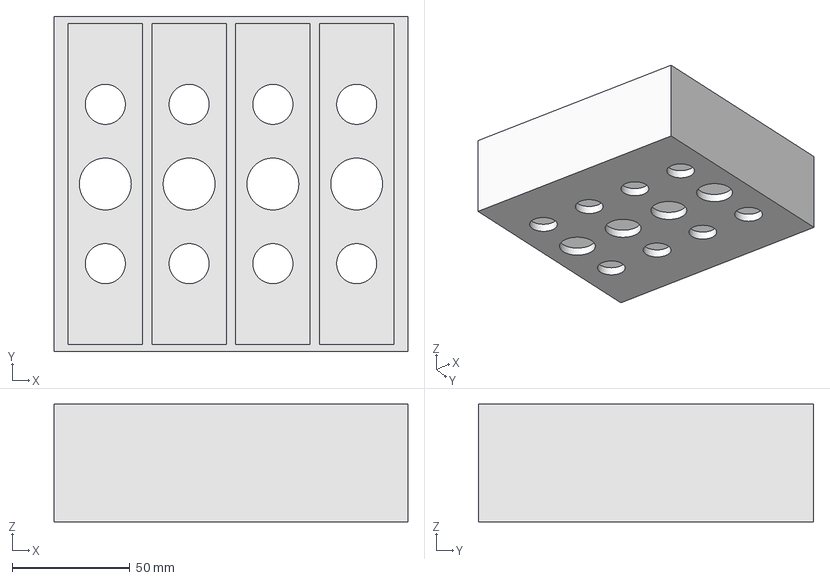
[picture p235: CAD file, 2018-01-25]
boxframe/upkframe_v6/batterymount_top.FCStd
150.0 x 142.0 x 50.0 mm
