CollectiveOpenSourceHardware/LibreSolarBox/upklib_v2/tslotprofile/tslot4con.fcstd

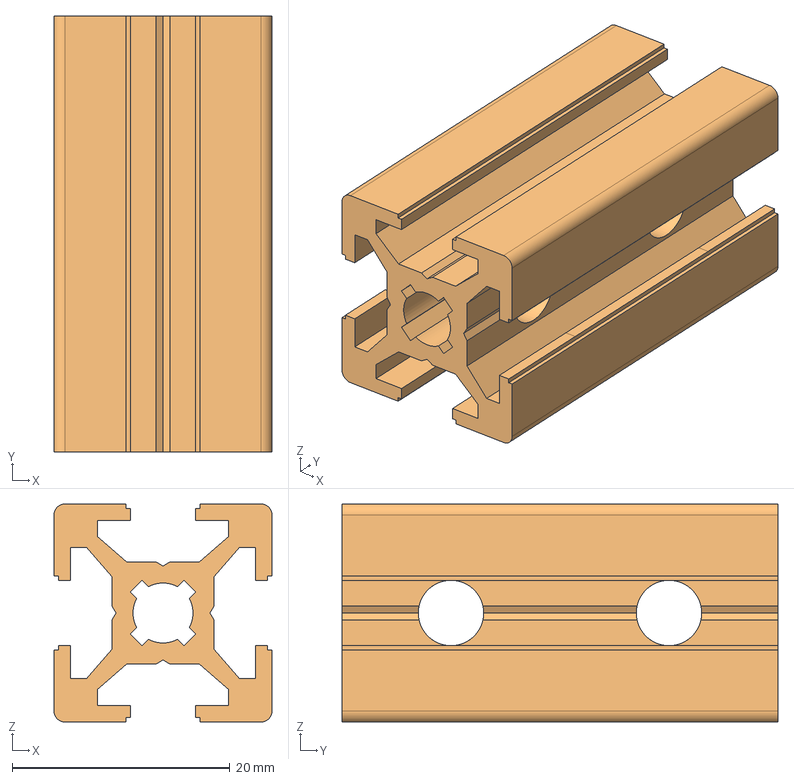
[picture p236: CAD file, 2017-09-25]
upklib_v2/tslotprofile/tslot4con.fcstd
20.0 x 40.0 x 20.0 mm
