CollectiveOpenSourceHardware/LibreSolarBox/boxframe/upkframe_v6/batterymount1b.fcstd

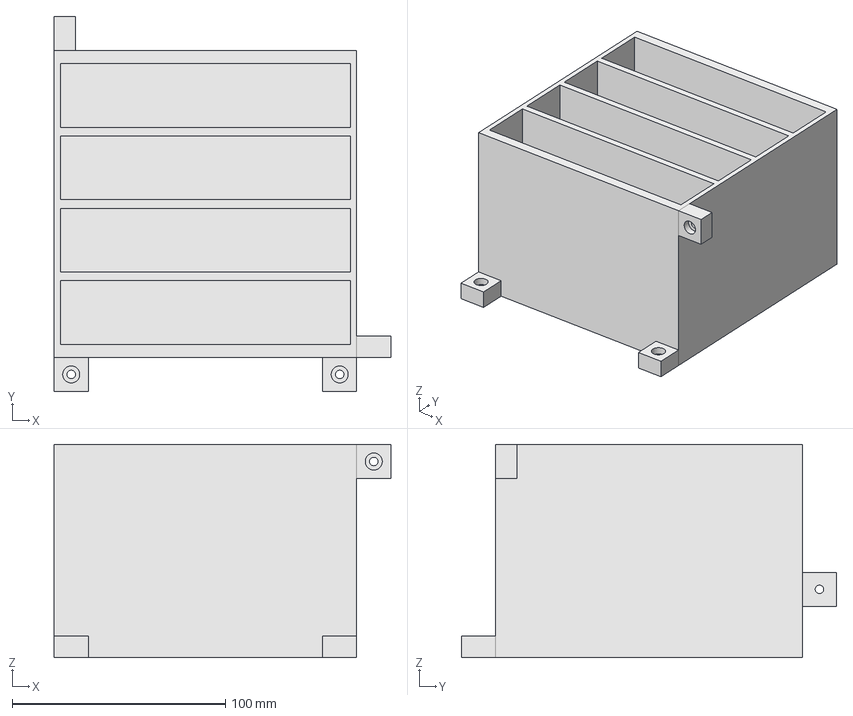
[picture p237: CAD file, 2018-01-15]
boxframe/upkframe_v6/batterymount1b.fcstd
158.0 x 176.0 x 100.0 mm
