CollectiveOpenSourceHardware/LibreSolarBox/upklib_v2/tslotprofile/tslot6.fcstd

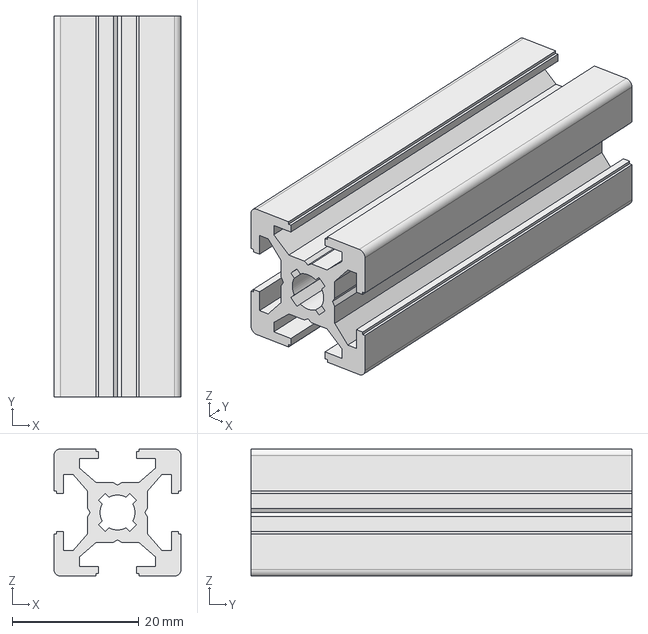
[picture p238: CAD file, 2017-09-25]
upklib_v2/tslotprofile/tslot6.fcstd
20.0 x 60.0 x 20.0 mm
