CollectiveOpenSourceHardware/LibreSolarBox/upklib_v2/tslotprofile/tslot40.fcstd

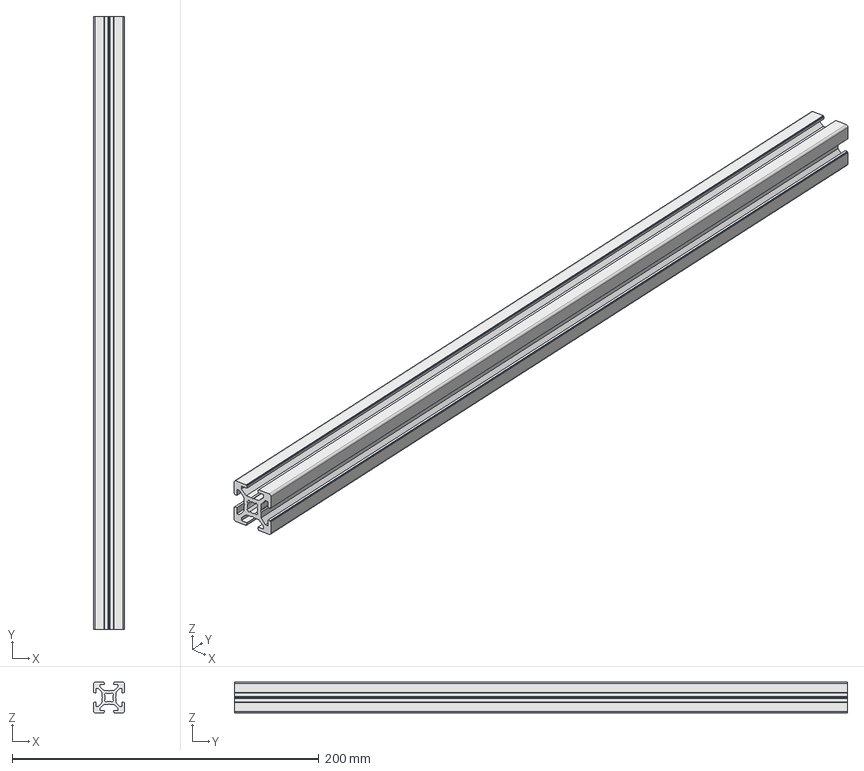
[picture p241: CAD file, 2017-09-25]
upklib_v2/tslotprofile/tslot40.fcstd
20.0 x 400.0 x 20.0 mm
