CollectiveOpenSourceHardware/LibreSolarBox/boxframe/upkframe_v6/batterymount.fcstd

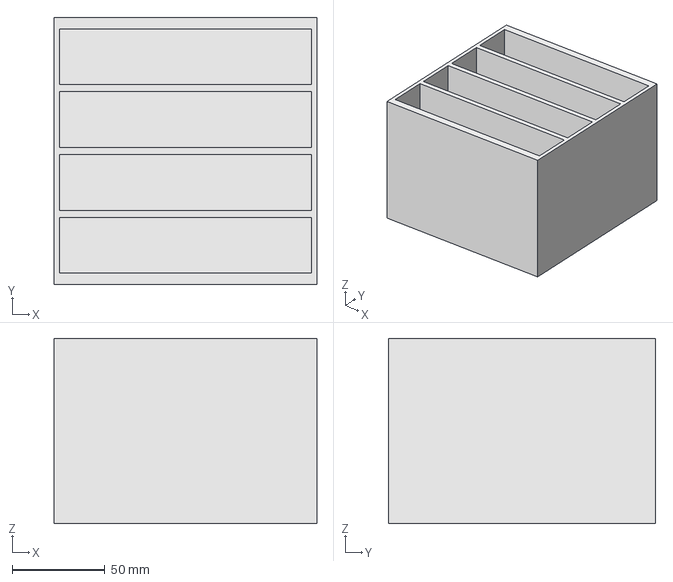
[picture p246: CAD file, 2018-01-15]
boxframe/upkframe_v6/batterymount.fcstd
142.0 x 144.0 x 100.0 mm
