CollectiveOpenSourceHardware/LibreSolarBox/upklib_v2/tslotprofile/tslot40con.fcstd

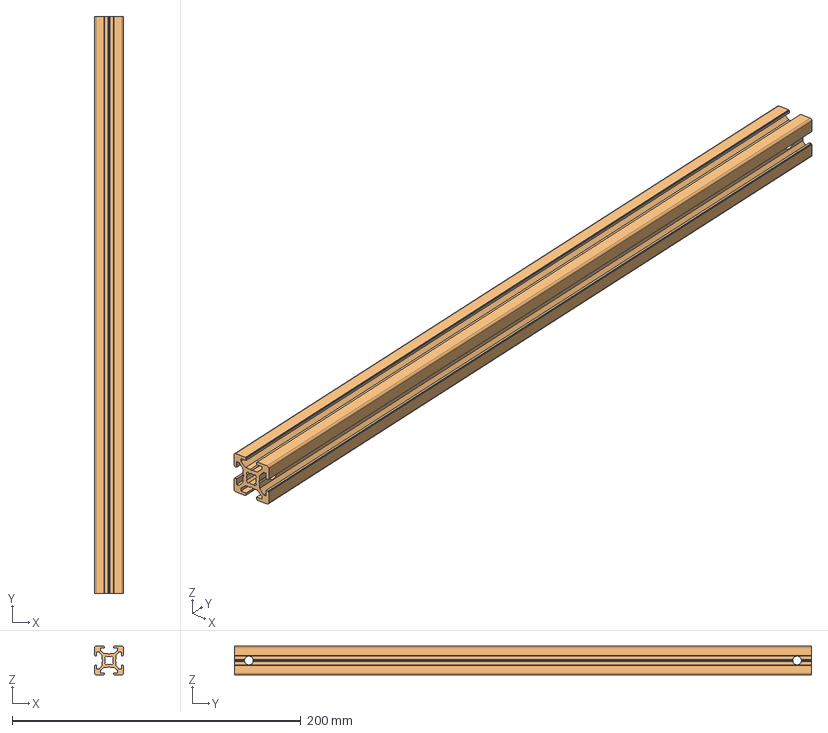
[picture p247: CAD file, 2017-09-25]
upklib_v2/tslotprofile/tslot40con.fcstd
20.0 x 400.0 x 20.0 mm
