CollectiveOpenSourceHardware/LibreSolarBox/boxframe/upkframe_v6/topbottom1b.fcstd

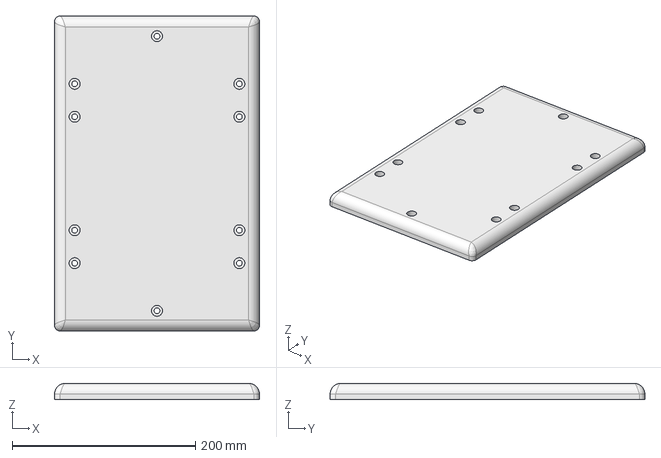
[picture p248: CAD file, 2018-01-10]
boxframe/upkframe_v6/topbottom1b.fcstd
224.0 x 344.0 x 18.0 mm
