CollectiveOpenSourceHardware/LibreSolarBox/boxframe/upkframe_v6/frontback.fcstd

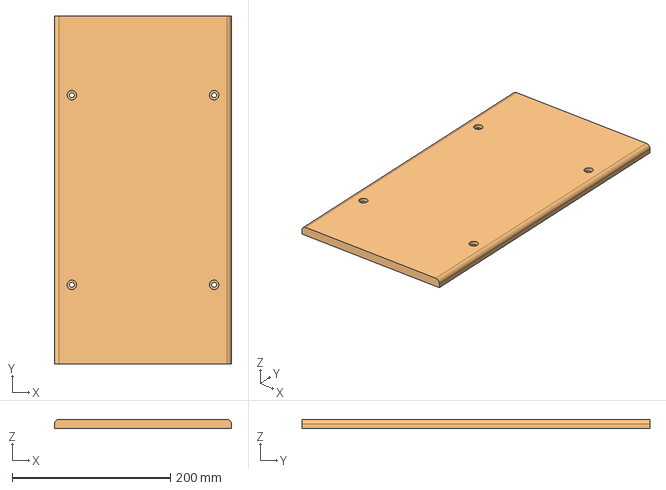
[picture p249: CAD file, 2018-01-10]
boxframe/upkframe_v6/frontback.fcstd
224.0 x 440.0 x 12.0 mm
