CollectiveOpenSourceHardware/LibreSolarBox/boxframe/upkframe_v6/ifmountNG_lashes.fcstd

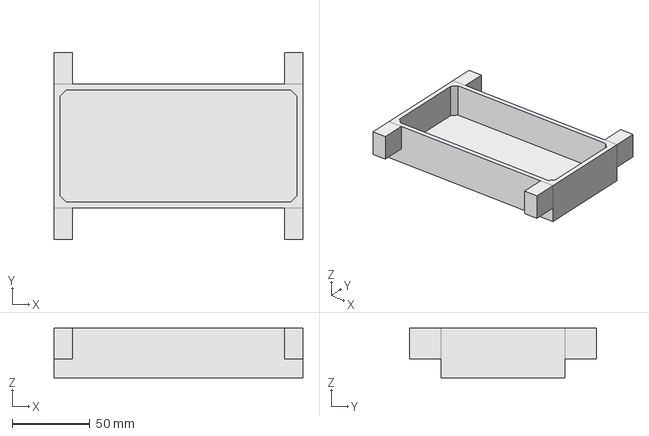
[picture p250: CAD file, 2018-01-10]
boxframe/upkframe_v6/ifmountNG_lashes.fcstd
160.0 x 120.0 x 32.0 mm
