CollectiveOpenSourceHardware/LibreSolarBox/boxframe/upkframe_v6/ifmountNG1c.fcstd

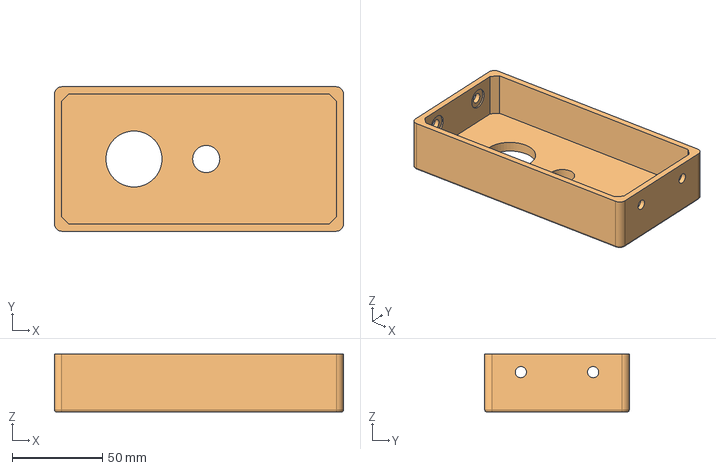
[picture p251: CAD file, 2018-01-10]
boxframe/upkframe_v6/ifmountNG1c.fcstd
160.0 x 80.0 x 32.0 mm
ifmountNG
