CollectiveOpenSourceHardware/LibreSolarBox/boxframe/upkframe_v6/seitenwand1c.fcstd

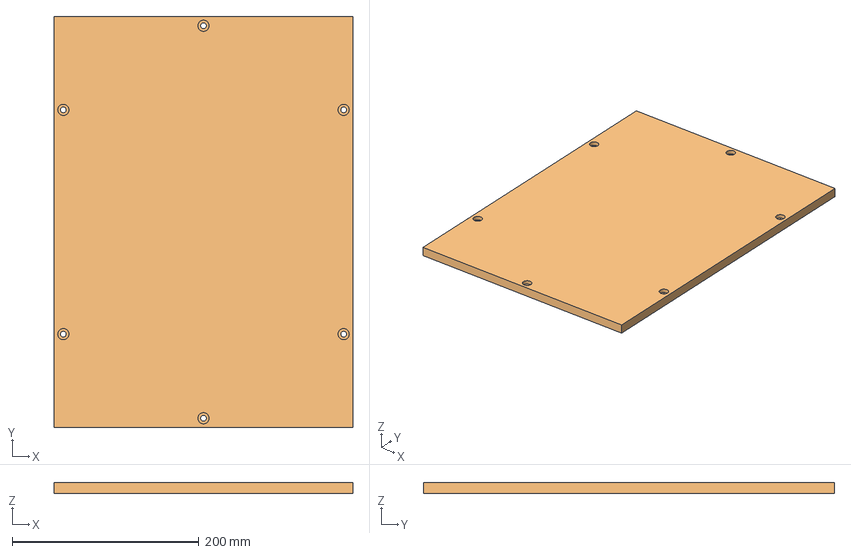
[picture p252: CAD file, 2018-01-10]
boxframe/upkframe_v6/seitenwand1c.fcstd
320.0 x 440.0 x 12.0 mm
seitenwand
