CollectiveOpenSourceHardware/LibreSolarBox/boxframe/upkframe_v6/boxhandle1j.fcstd

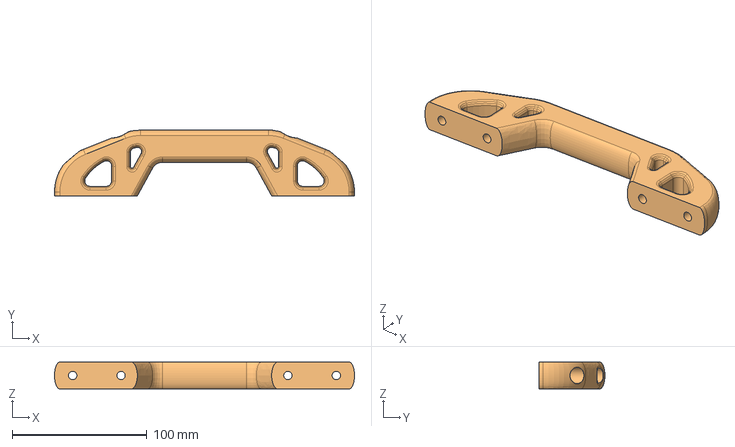
[picture p253: CAD file, 2018-01-10]
boxframe/upkframe_v6/boxhandle1j.fcstd
223.0 x 49.0 x 20.0 mm
