CollectiveOpenSourceHardware/LibreSolarBox/boxframe/upkframe_v6/UPKframeNG1f.fcstd

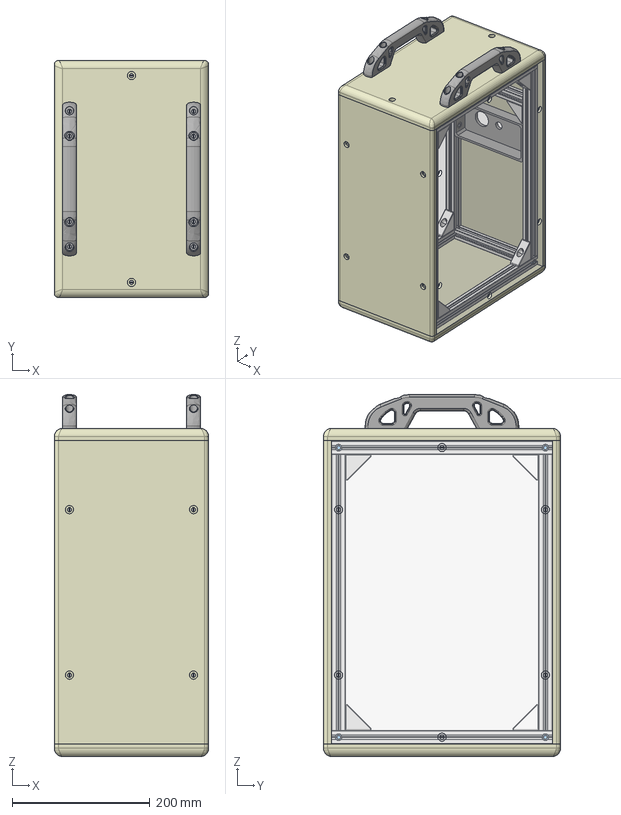
[picture p254: CAD file, 2018-01-10]
boxframe/upkframe_v6/UPKframeNG1f.fcstd
224.0 x 344.0 x 525.1 mm
tslot40
tslot32con
tslot16
tslot16_001
tslot32con_001
M6x25-Screw
M6x25-Screw004
M6x25-Screw005
M6x25-Screw006
tslot32con001
tslot041
tslot16_002
tslot32con_002
M6x25-Screw007
M6x25-Screw008
M6x25-Screw009
M6x25-Screw010
tslot042
tslot043
tslot044
m6nutplate
M6x12-Screw
M6x12-Screw001
m6nutplate001
m6nutplate002
M6x12-Screw002
M6x12-Screw003
m6nutplate003
m6nutplate004
M6x12-Screw004
M6x12-Screw005
m6nutplate005
m6nutplate006
M6x12-Screw006
M6x12-Screw007
m6nutplate007
m6nutplate008
M6x12-Screw008
M6x12-Screw009
m6nutplate009
tslot16_across
tslot16_across001
topplate
topplate001
boxhandle
boxhandle001
frontplate
seitenwand
seitenwand001
ifmountNG
frontback_if2
