CollectiveOpenSourceHardware/LibreSolarBox/boxframe/buildinstructional/cover/cov1.png

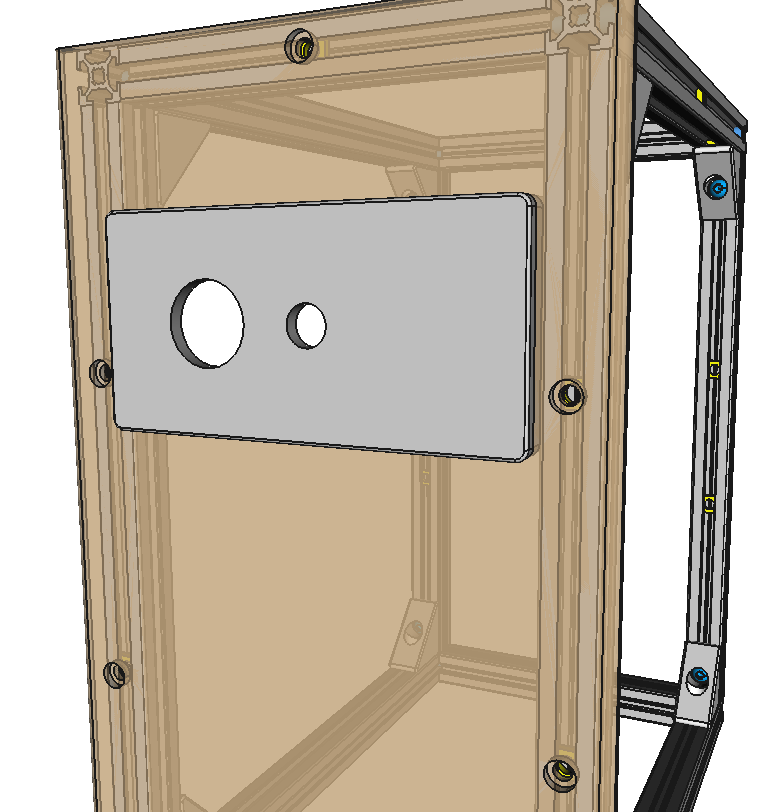
boxframe/buildinstructional/cover/cov1.png
