CollectiveOpenSourceHardware/LibreSolarBox/boxframe/buildinstructional/cover/cov2.png

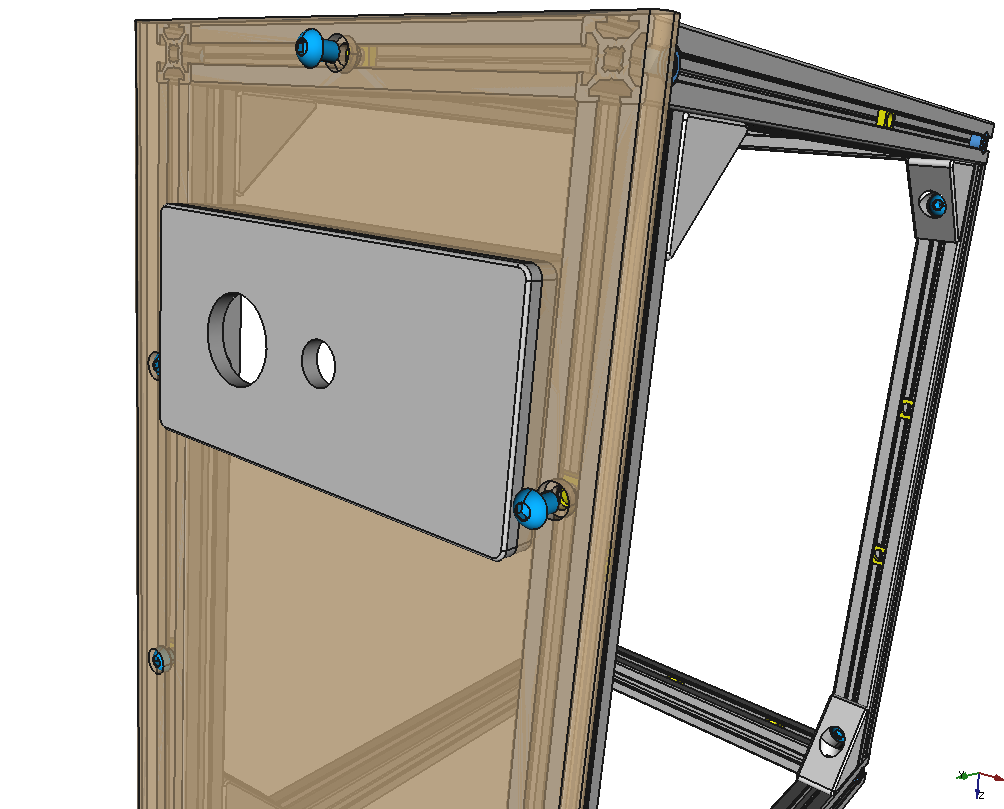
boxframe/buildinstructional/cover/cov2.png
