CollectiveOpenSourceHardware/LibreSolarBox/boxframe/buildinstructional/cover/cov3.png

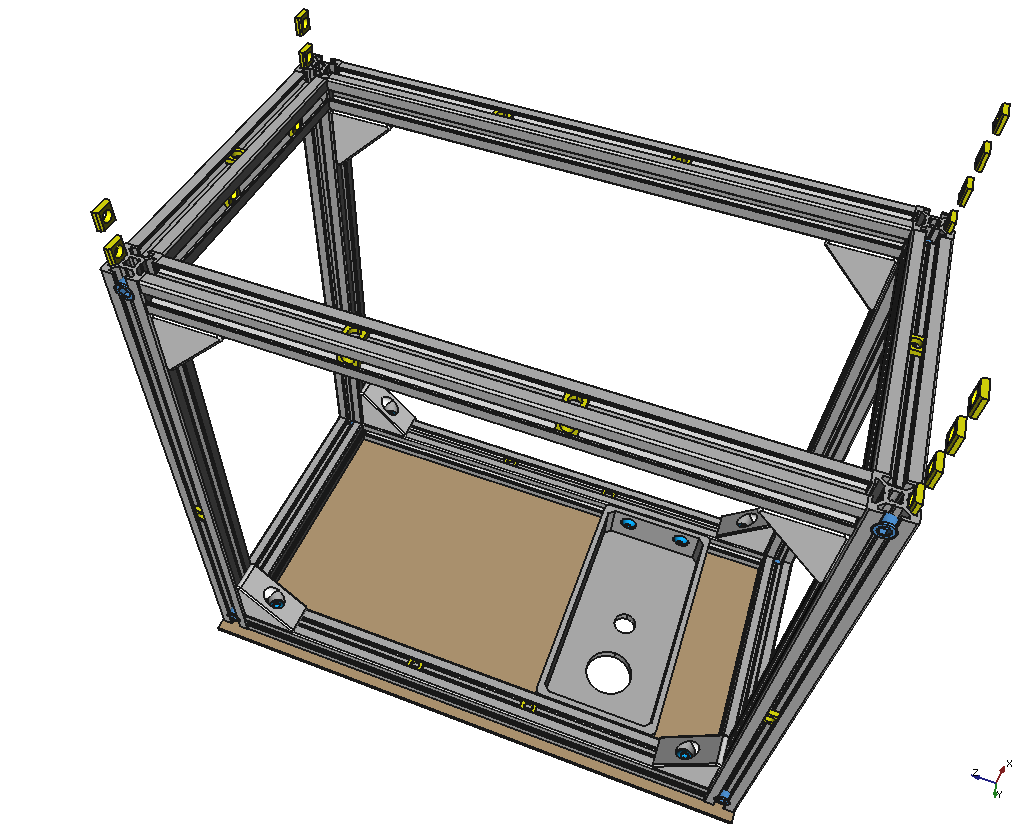
boxframe/buildinstructional/cover/cov3.png
