CollectiveOpenSourceHardware/LibreSolarBox/boxframe/buildinstructional/cover/cov4.png

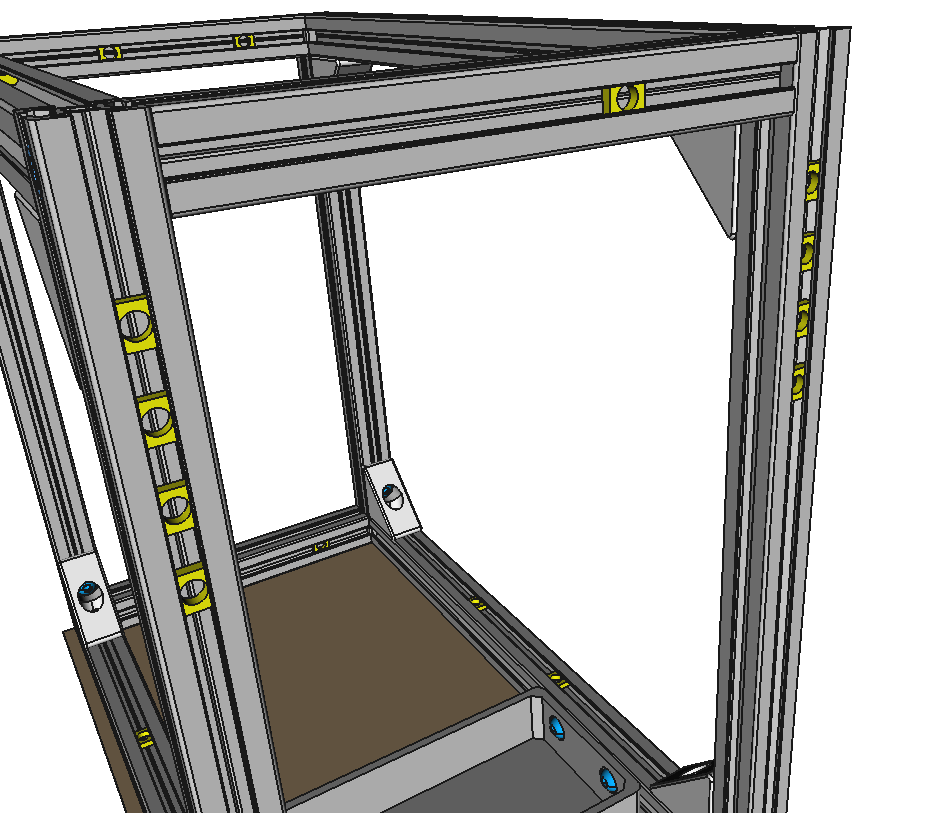
boxframe/buildinstructional/cover/cov4.png
