CollectiveOpenSourceHardware/LibreSolarBox/boxframe/buildinstructional/cover/cov5.png

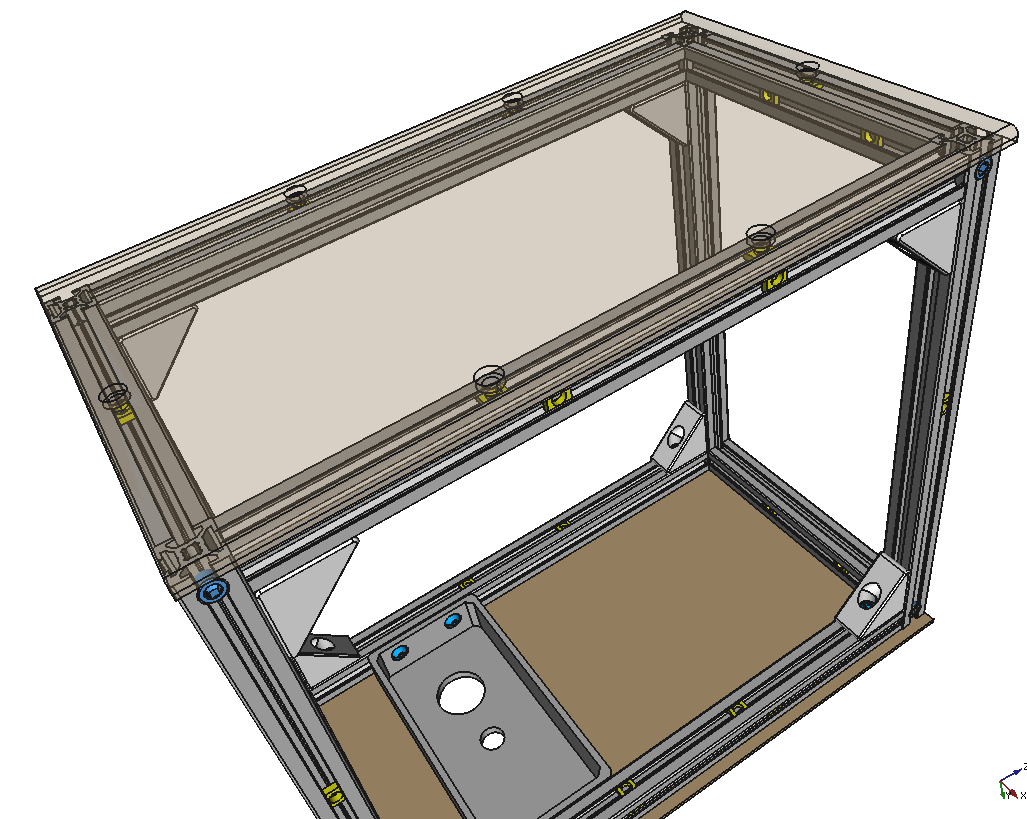
boxframe/buildinstructional/cover/cov5.png
