CollectiveOpenSourceHardware/LibreSolarBox/boxframe/buildinstructional/cover/cov6.png

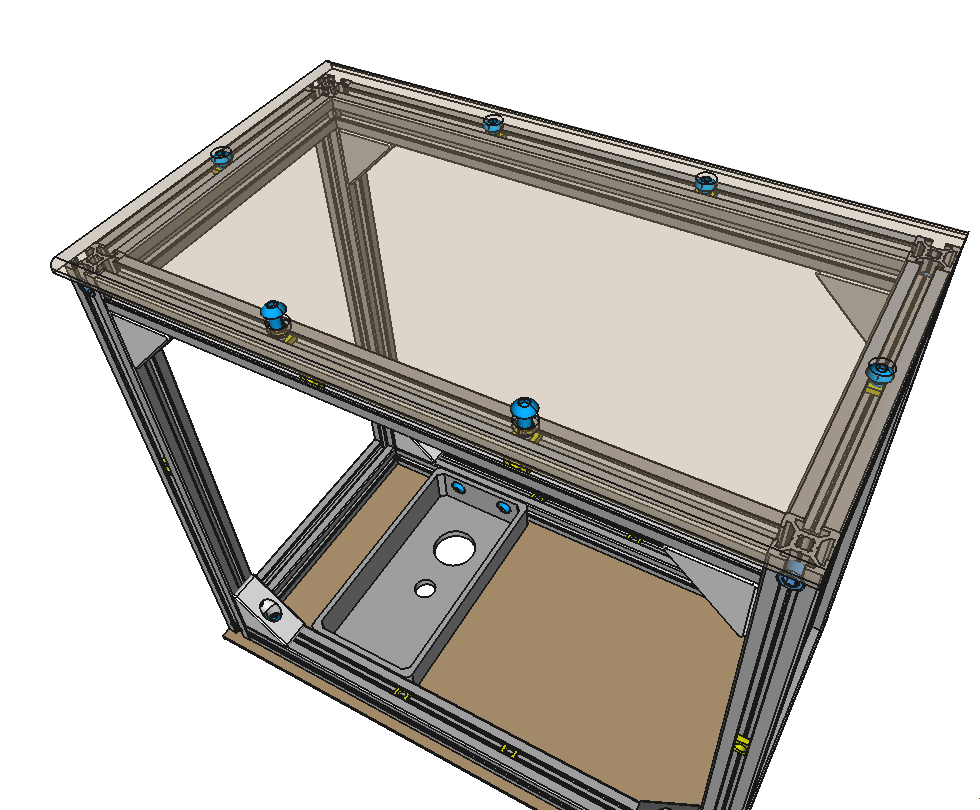
boxframe/buildinstructional/cover/cov6.png
