CollectiveOpenSourceHardware/LibreSolarBox/boxframe/buildinstructional/cover/cov7.png

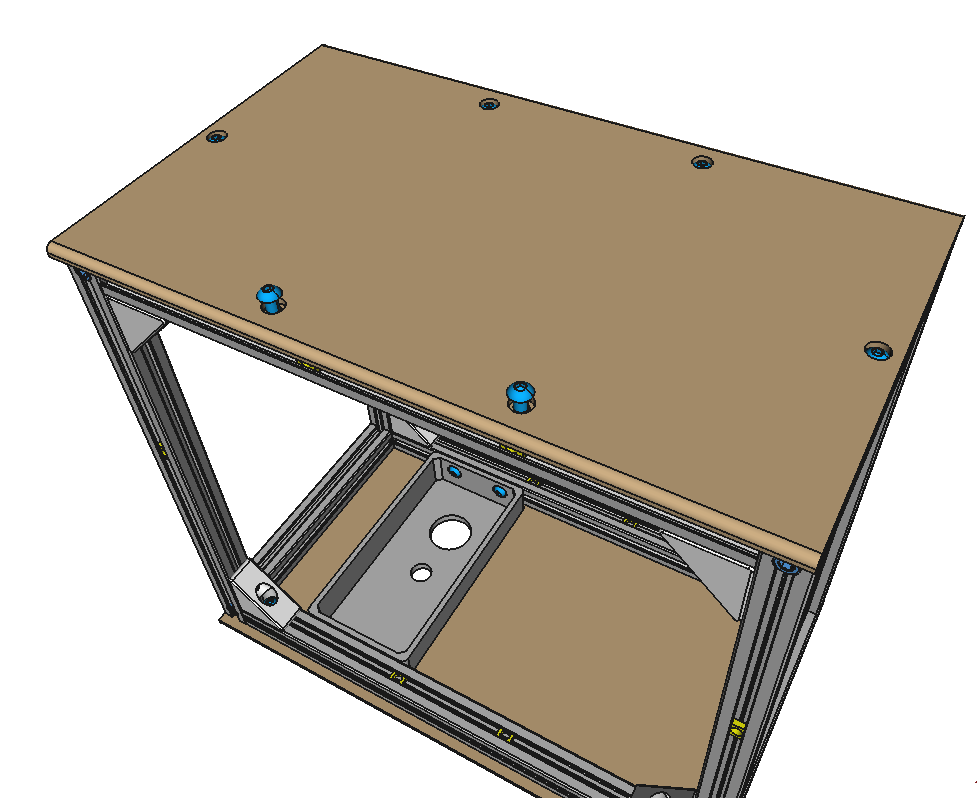
boxframe/buildinstructional/cover/cov7.png
