CollectiveOpenSourceHardware/LibreSolarBox/boxframe/buildinstructional/cover/cov9.png

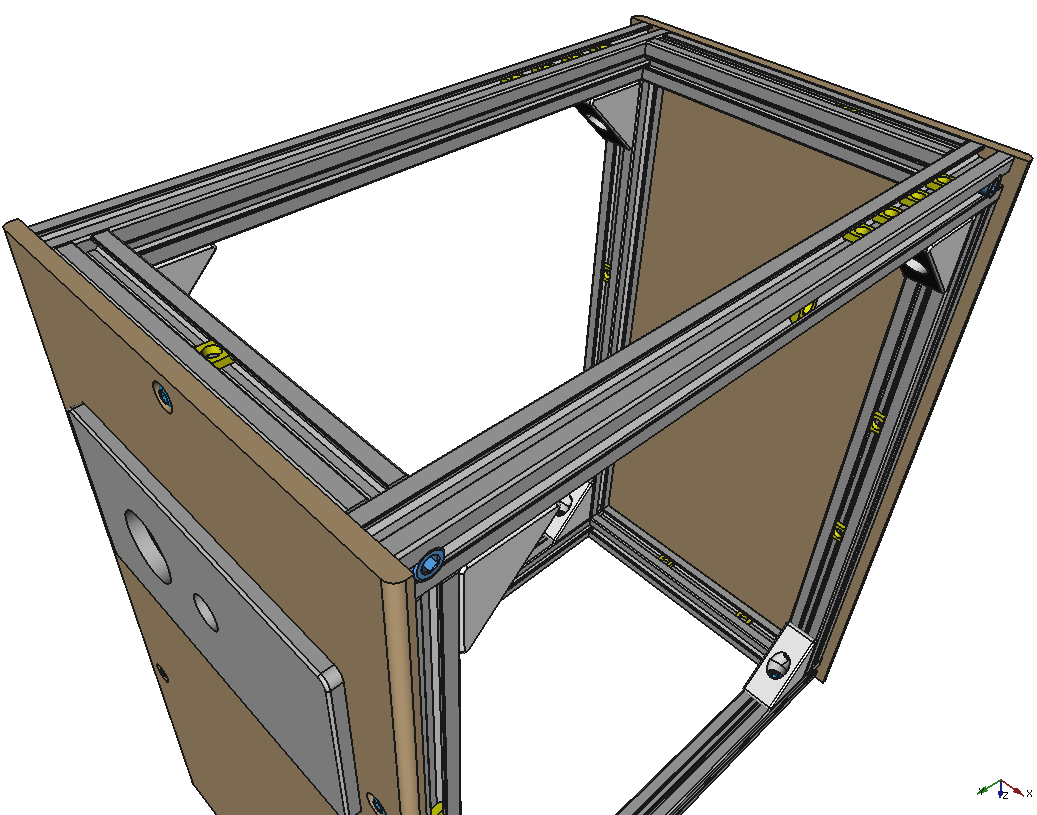
boxframe/buildinstructional/cover/cov9.png
