CollectiveOpenSourceHardware/LibreSolarBox/boxframe/buildinstructional/cover/cov10.png

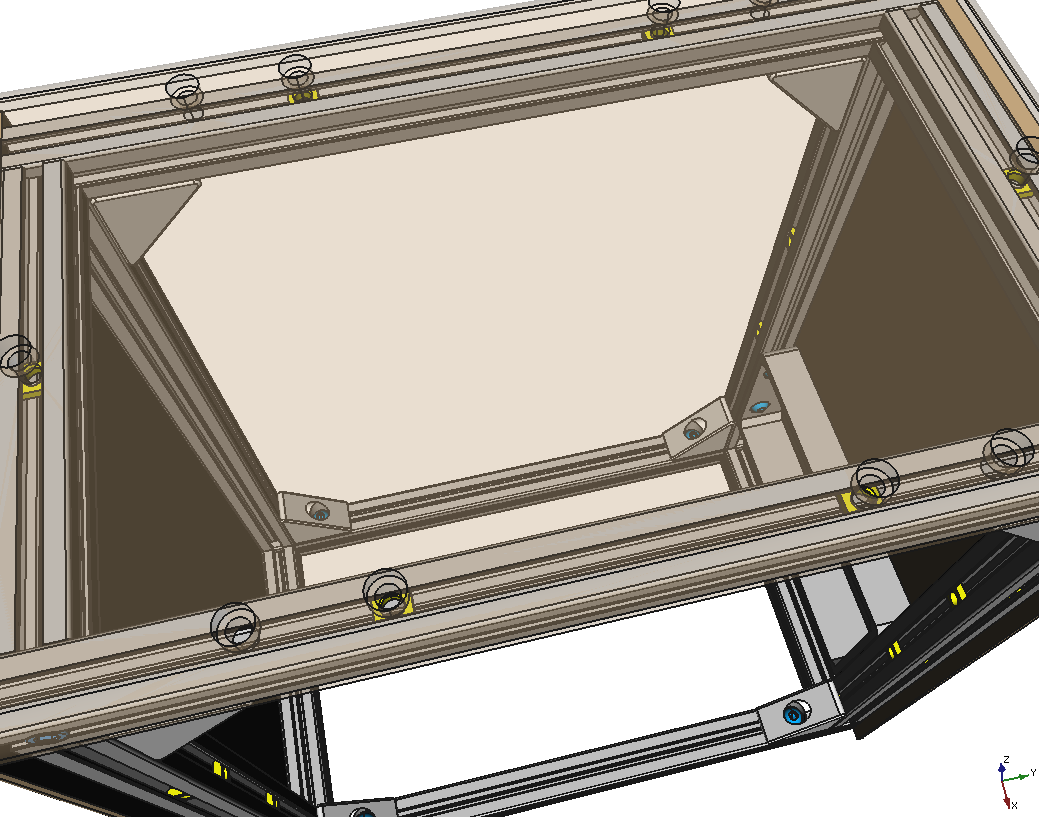
boxframe/buildinstructional/cover/cov10.png
