CollectiveOpenSourceHardware/LibreSolarBox/boxframe/buildinstructional/cover/cov11.png

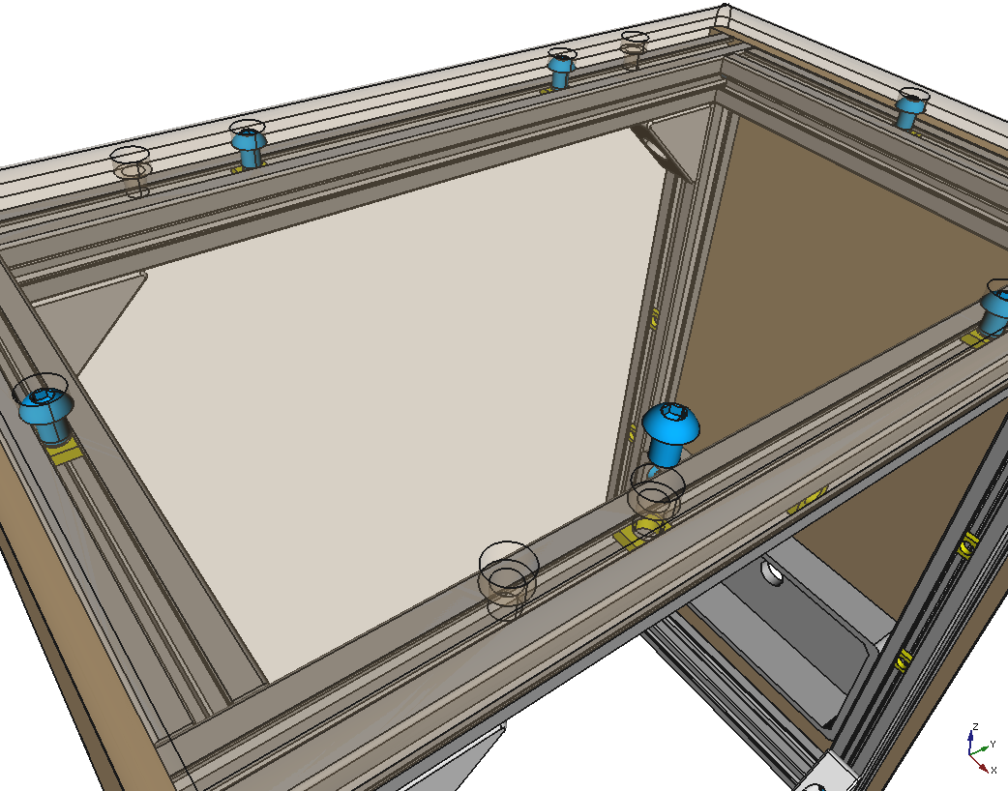
boxframe/buildinstructional/cover/cov11.png
