CollectiveOpenSourceHardware/LibreSolarBox/boxframe/buildinstructional/cover/cov11b.png

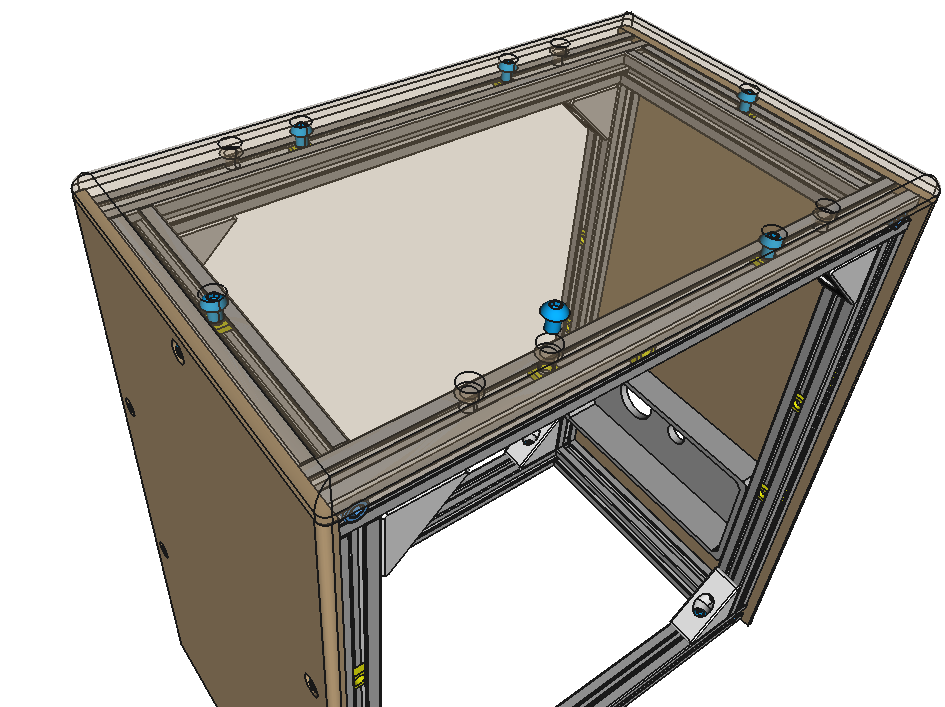
boxframe/buildinstructional/cover/cov11b.png
