CollectiveOpenSourceHardware/LibreSolarBox/boxframe/buildinstructional/cover/cov11c.png

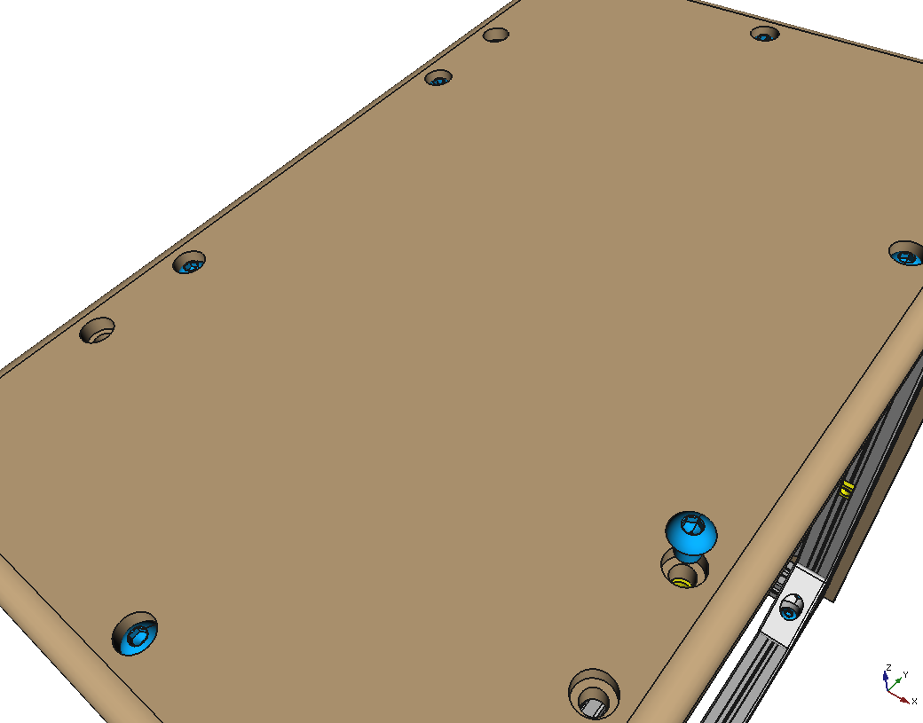
boxframe/buildinstructional/cover/cov11c.png
