CollectiveOpenSourceHardware/LibreSolarBox/boxframe/buildinstructional/cover/cov12.png

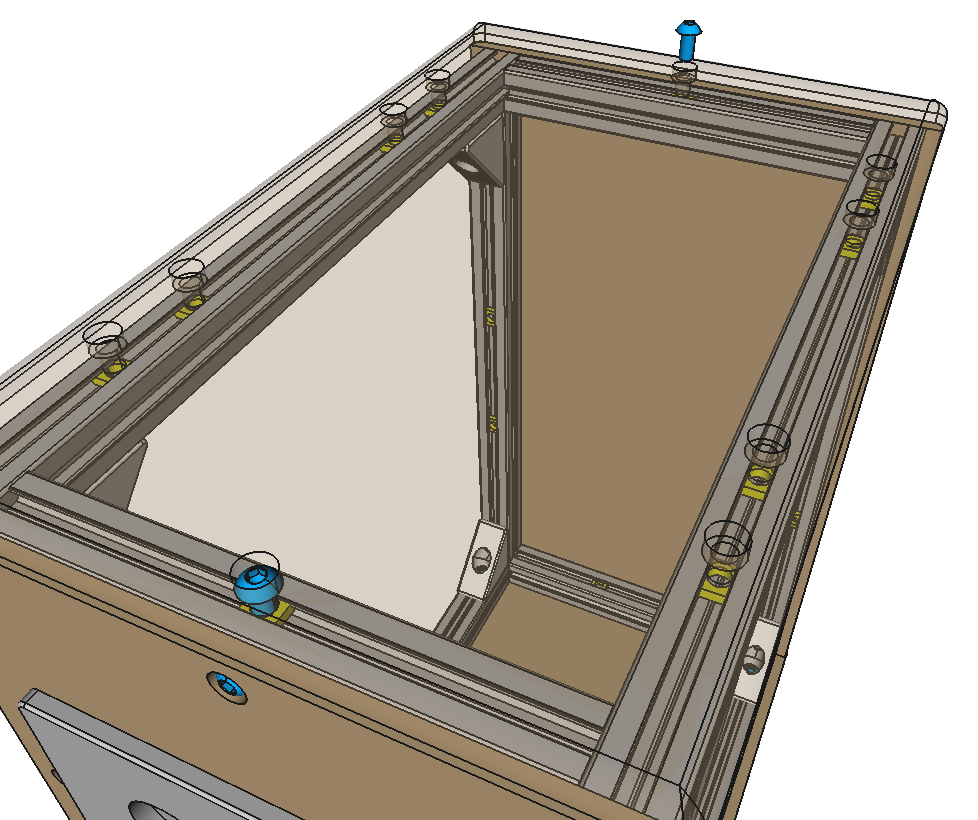
boxframe/buildinstructional/cover/cov12.png
