CollectiveOpenSourceHardware/LibreSolarBox/boxframe/buildinstructional/cover/cov13.png

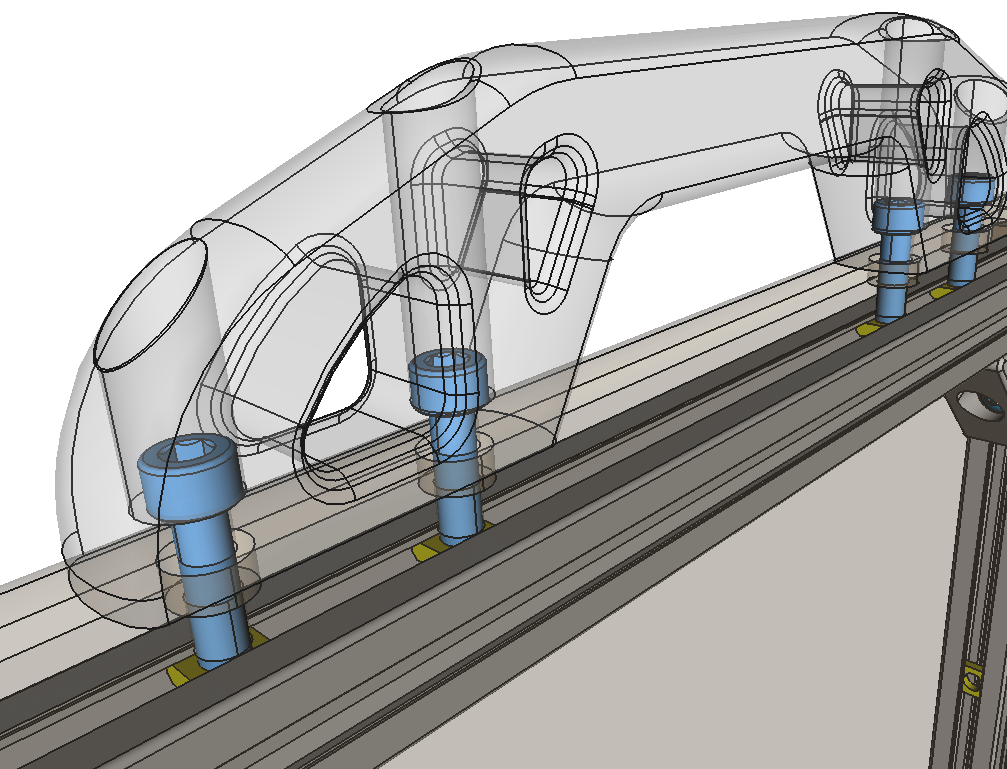
boxframe/buildinstructional/cover/cov13.png
