CollectiveOpenSourceHardware/LibreSolarBox/boxframe/buildinstructional/cover/cov14.png

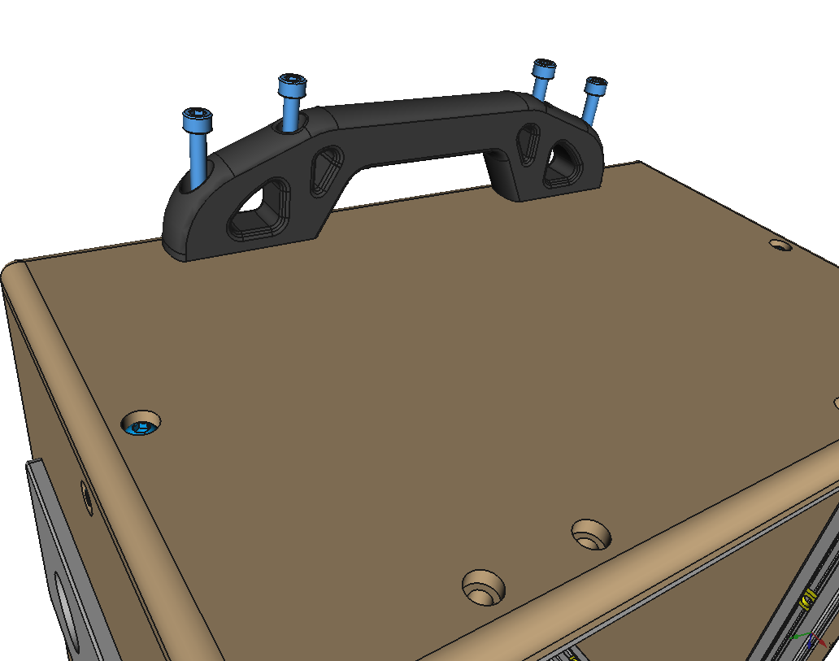
boxframe/buildinstructional/cover/cov14.png
