CollectiveOpenSourceHardware/LibreSolarBox/boxframe/buildinstructional/cover/cov15.png

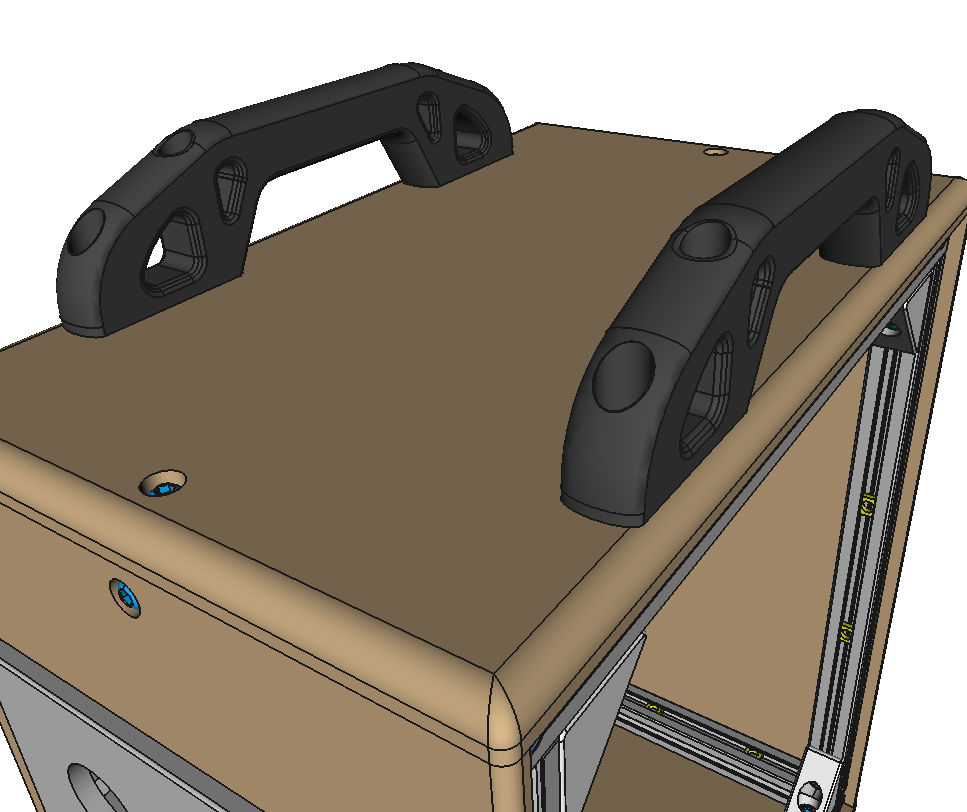
boxframe/buildinstructional/cover/cov15.png
