CollectiveOpenSourceHardware/LibreSolarBox/boxframe/buildinstructional/cover/cov15c.png

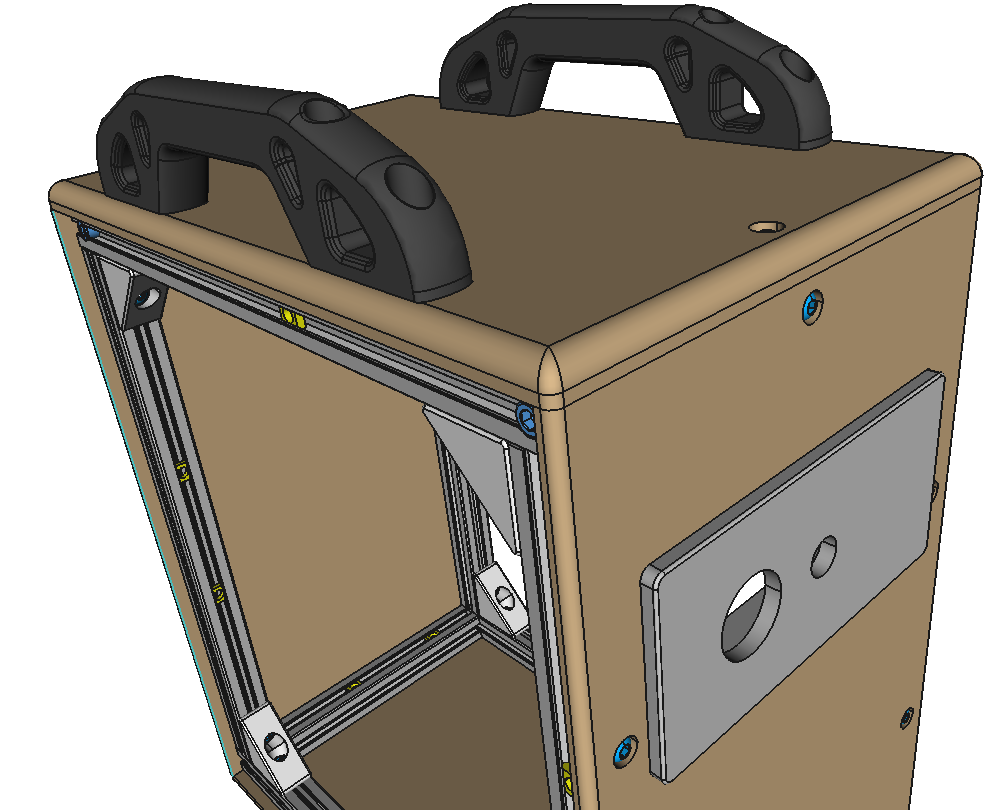
boxframe/buildinstructional/cover/cov15c.png
