CollectiveOpenSourceHardware/LibreSolarBox/boxframe/buildinstructional/cover/cov16.png

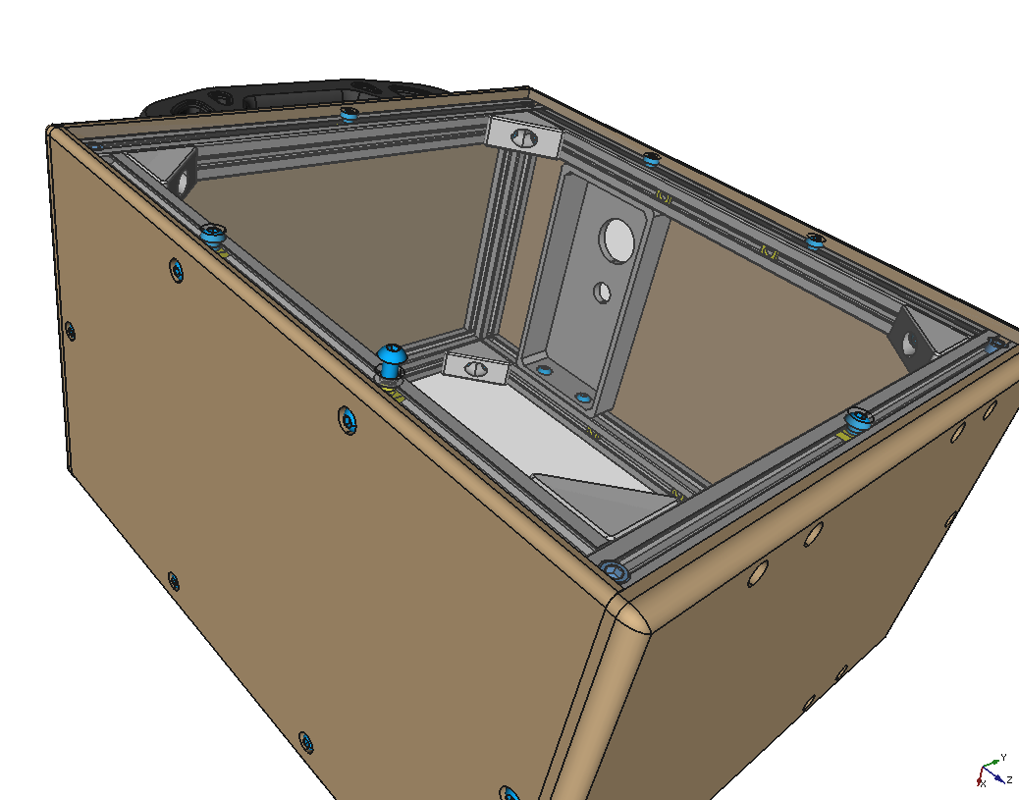
boxframe/buildinstructional/cover/cov16.png
