CollectiveOpenSourceHardware/LibreSolarBox/boxframe/buildinstructional/ifmountframe/ifmount1.png

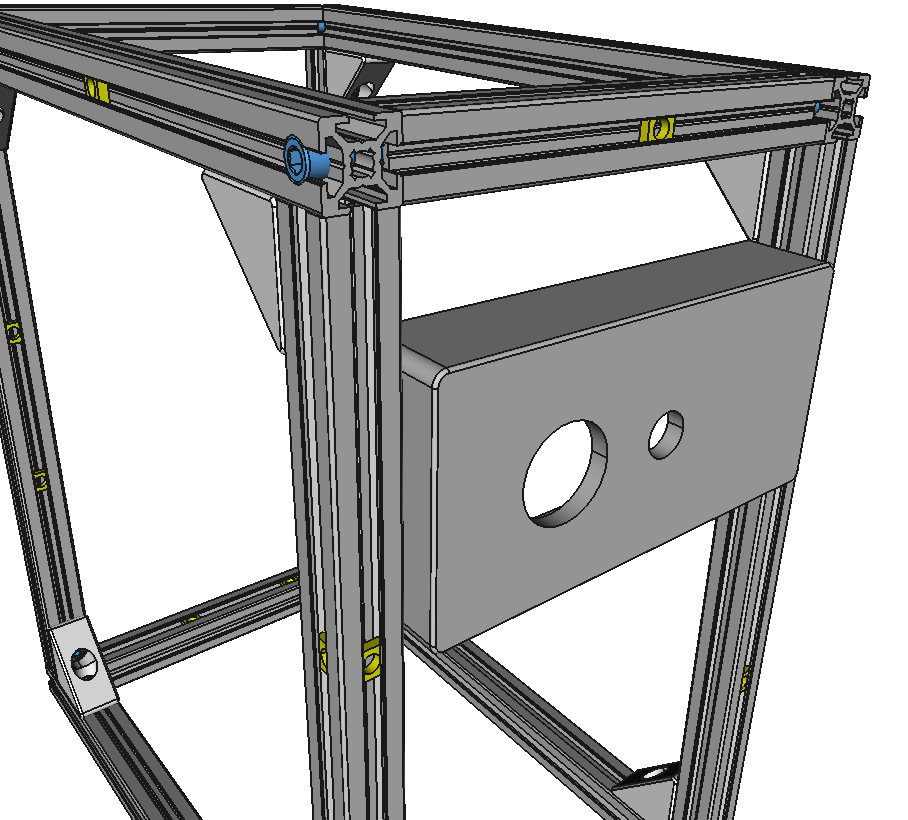
boxframe/buildinstructional/ifmountframe/ifmount1.png
