CollectiveOpenSourceHardware/LibreSolarBox/boxframe/buildinstructional/ifmountframe/ifmount2.png

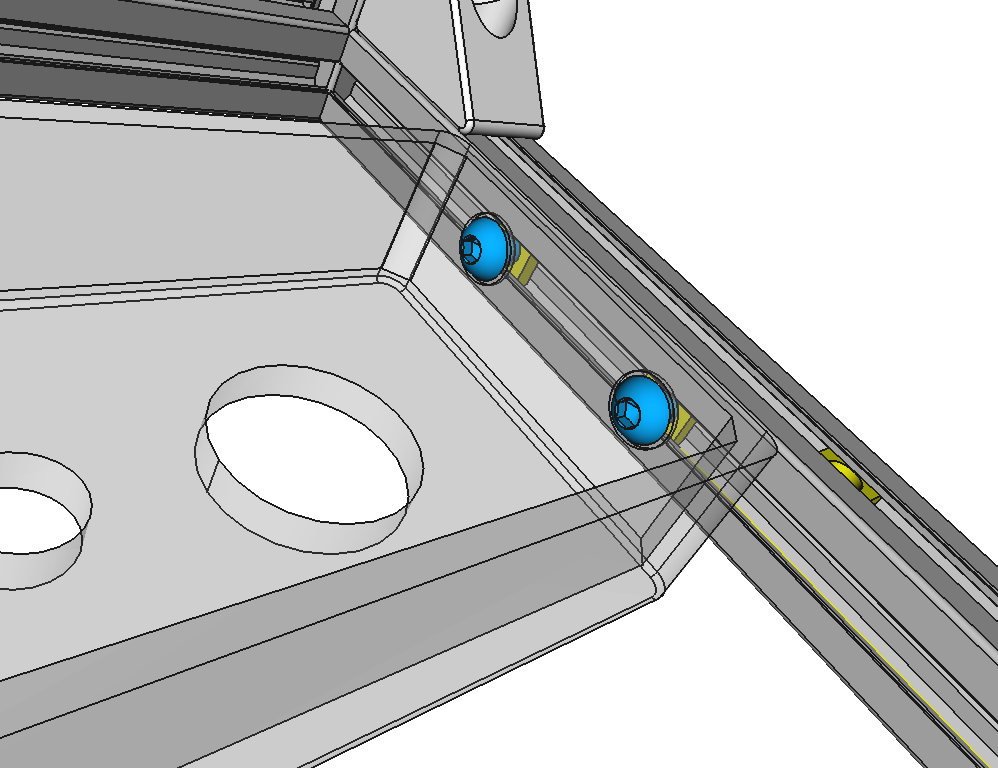
boxframe/buildinstructional/ifmountframe/ifmount2.png
