CollectiveOpenSourceHardware/LibreSolarBox/boxframe/buildinstructional/ifmountframe/ifmount3.png

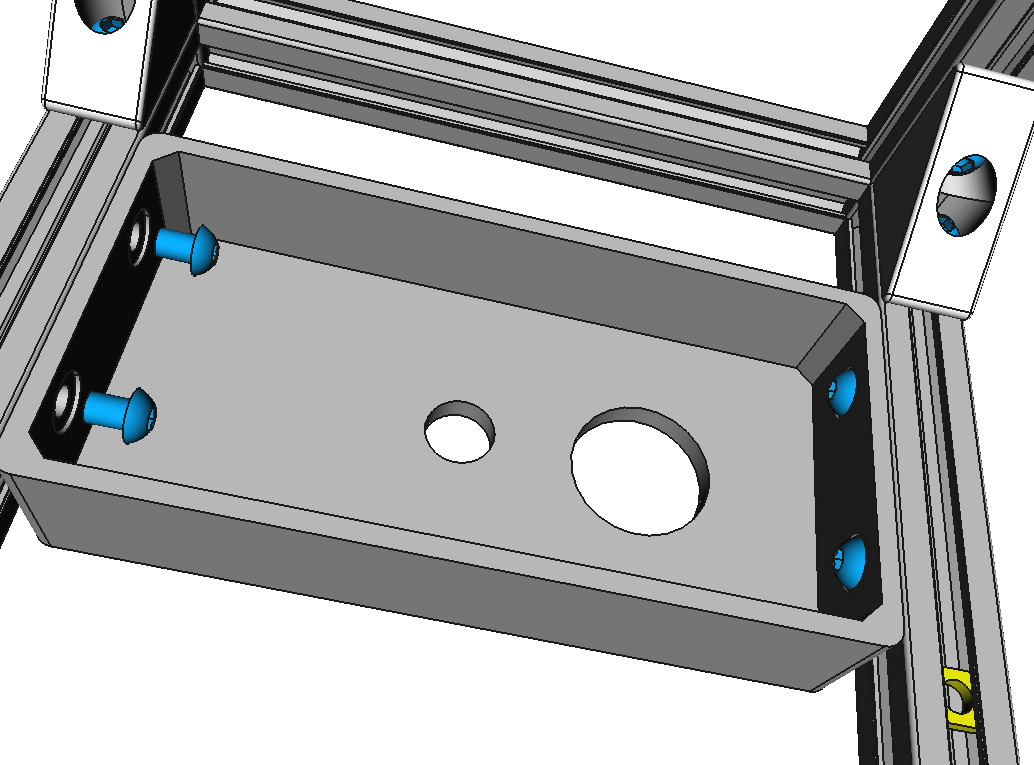
boxframe/buildinstructional/ifmountframe/ifmount3.png
