CollectiveOpenSourceHardware/LibreSolarBox/boxframe/buildinstructional/innerplates/bottom1.png

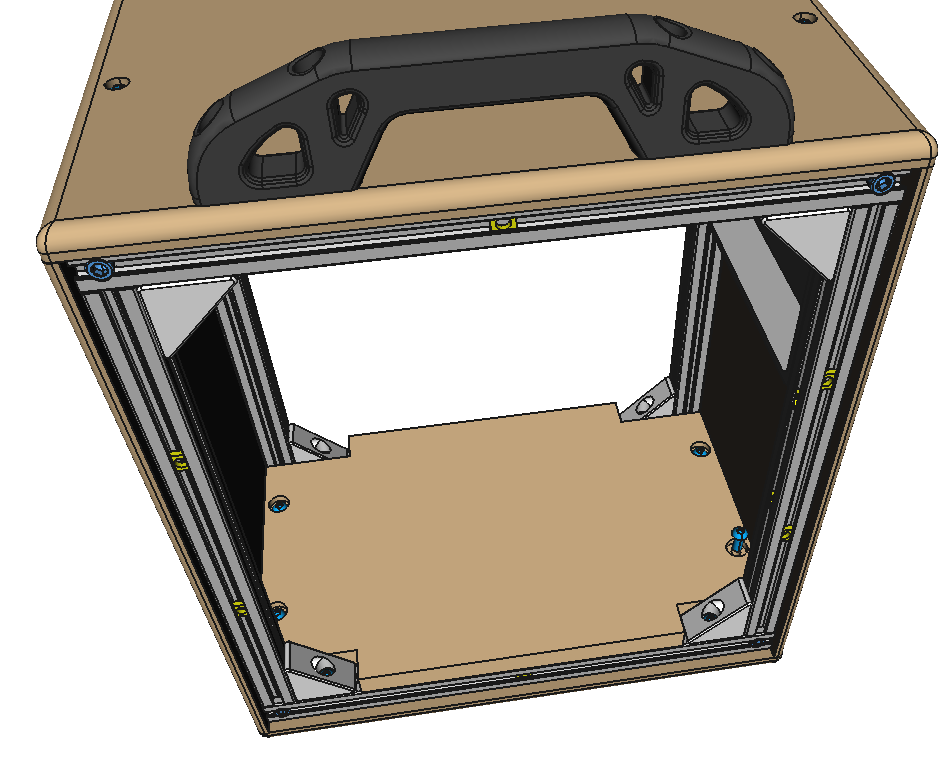
boxframe/buildinstructional/innerplates/bottom1.png
