CollectiveOpenSourceHardware/LibreSolarBox/boxframe/buildinstructional/innerplates/bottom1b.png

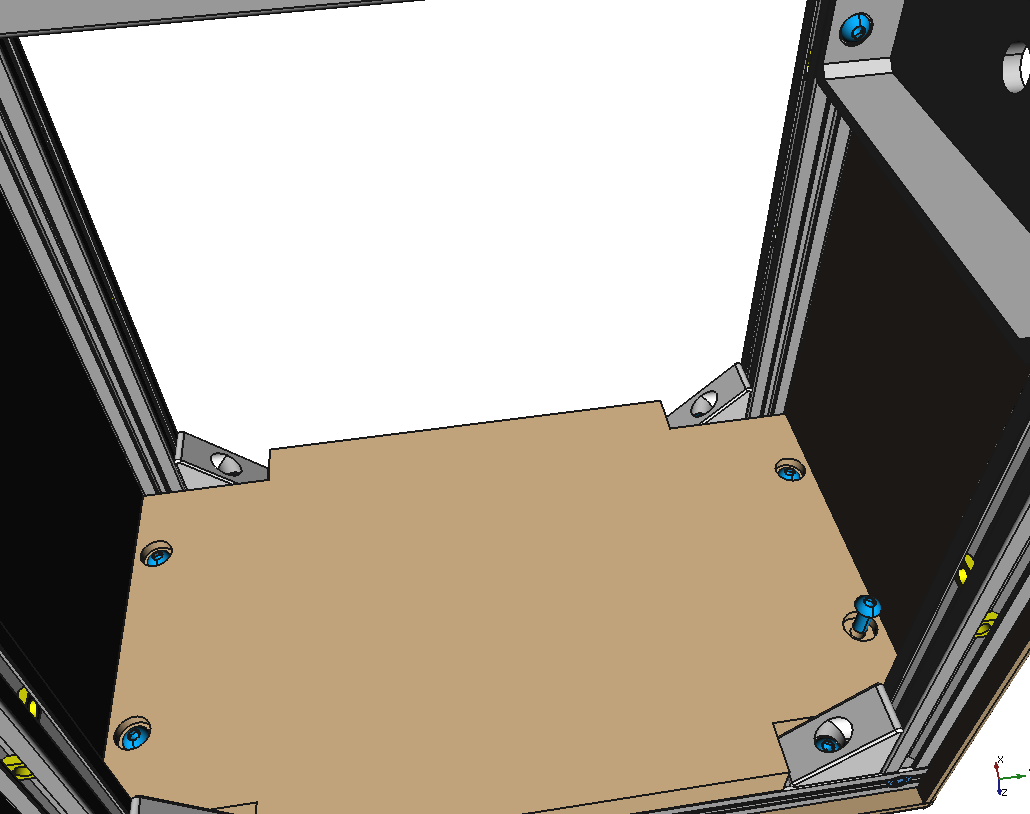
boxframe/buildinstructional/innerplates/bottom1b.png
