CollectiveOpenSourceHardware/LibreSolarBox/boxframe/buildinstructional/innerplates/front1.png

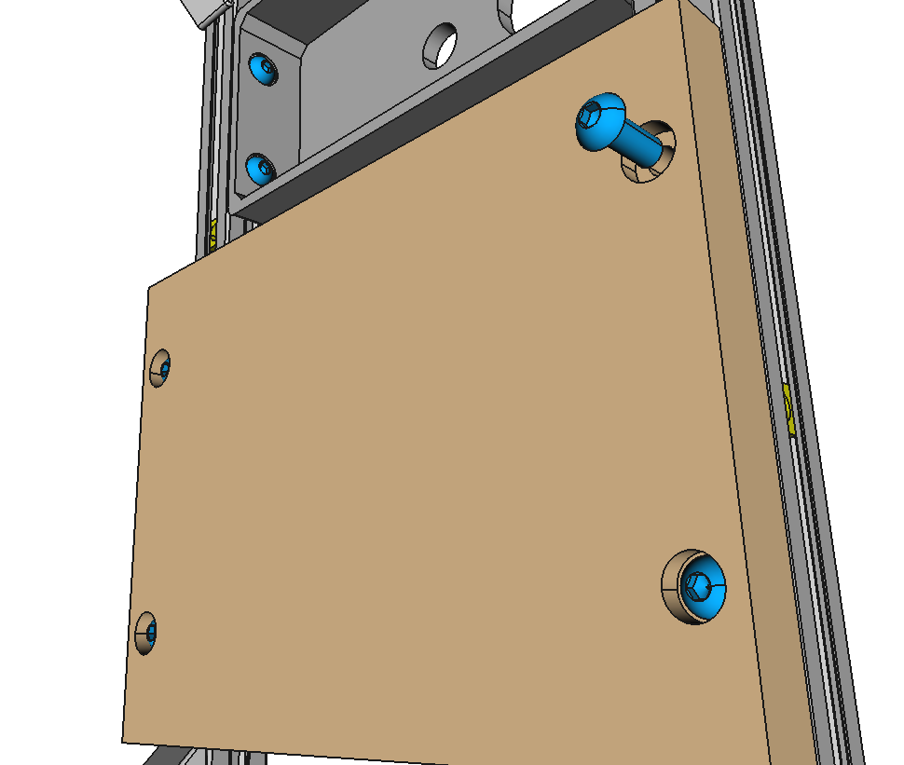
boxframe/buildinstructional/innerplates/front1.png
