CollectiveOpenSourceHardware/LibreSolarBox/boxframe/buildinstructional/innerplates/front2.png

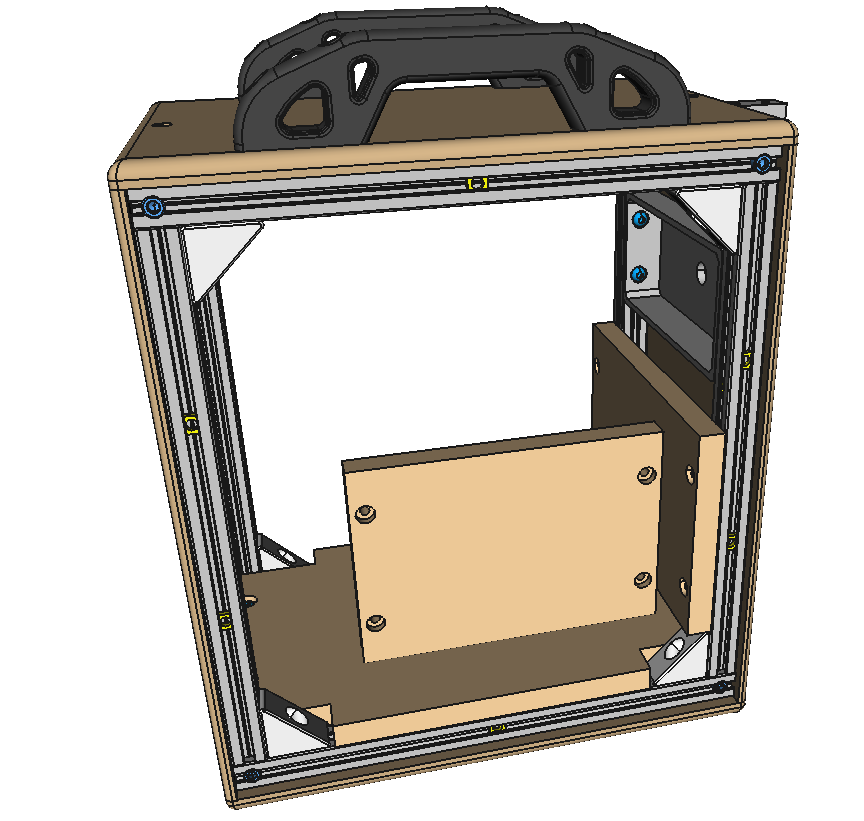
boxframe/buildinstructional/innerplates/front2.png
