CollectiveOpenSourceHardware/LibreSolarBox/boxframe/buildinstructional/innerplates/front3.png

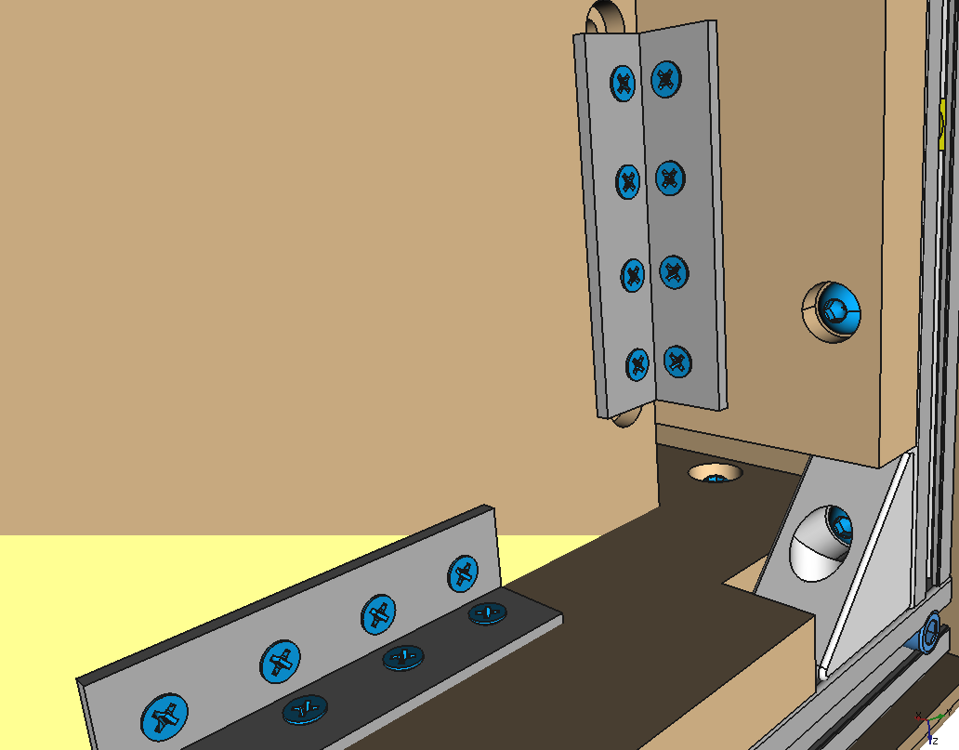
boxframe/buildinstructional/innerplates/front3.png
