CollectiveOpenSourceHardware/LibreSolarBox/boxframe/buildinstructional/innerplates/front4.png

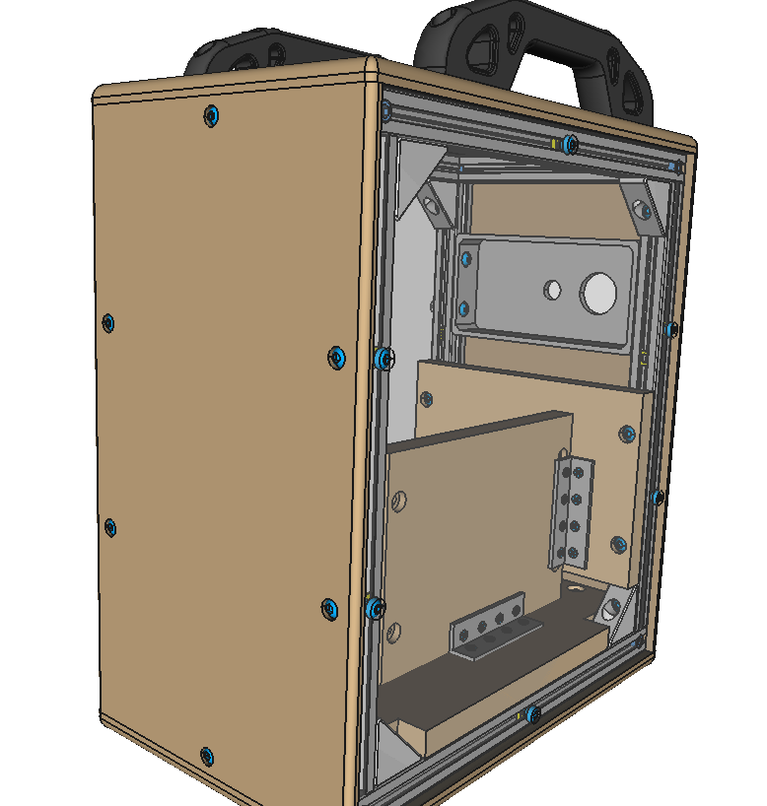
boxframe/buildinstructional/innerplates/front4.png
