CollectiveOpenSourceHardware/LibreSolarBox/boxframe/buildinstructional/innerplates/front4c.png

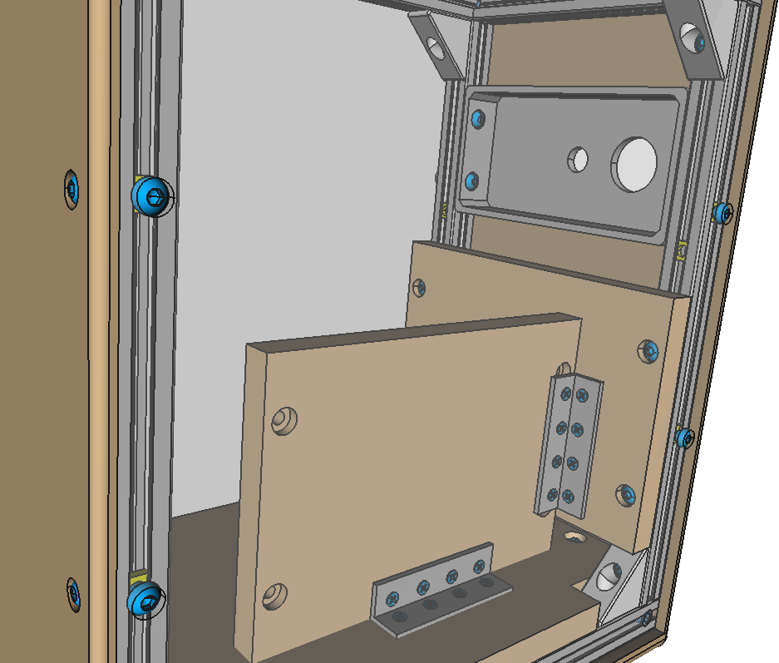
boxframe/buildinstructional/innerplates/front4c.png
