CollectiveOpenSourceHardware/LibreSolarBox/boxframe/buildinstructional/lower_frame/lframe1.png

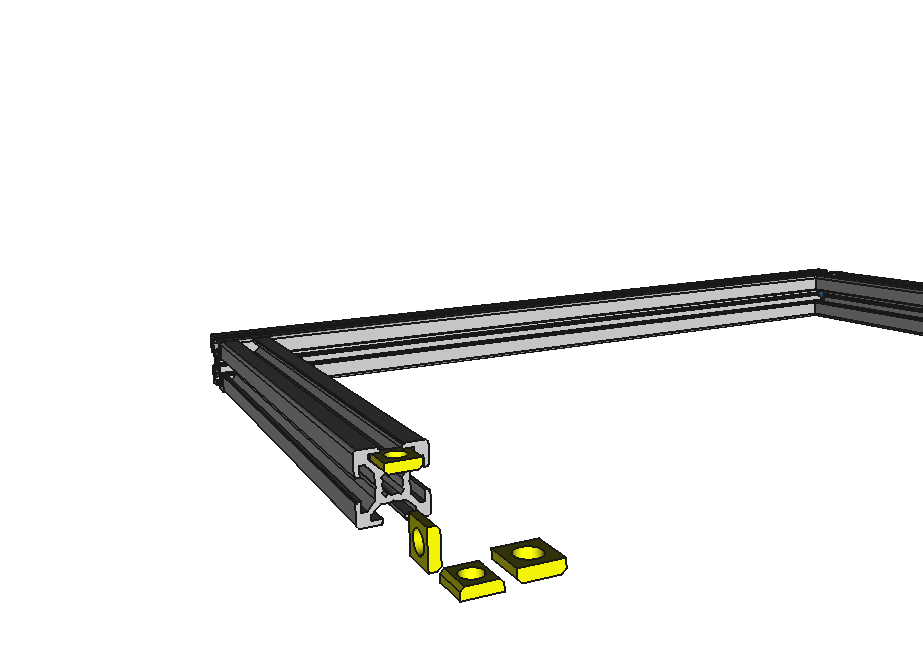
boxframe/buildinstructional/lower_frame/lframe1.png
