CollectiveOpenSourceHardware/LibreSolarBox/boxframe/buildinstructional/lower_frame/lframe2.png

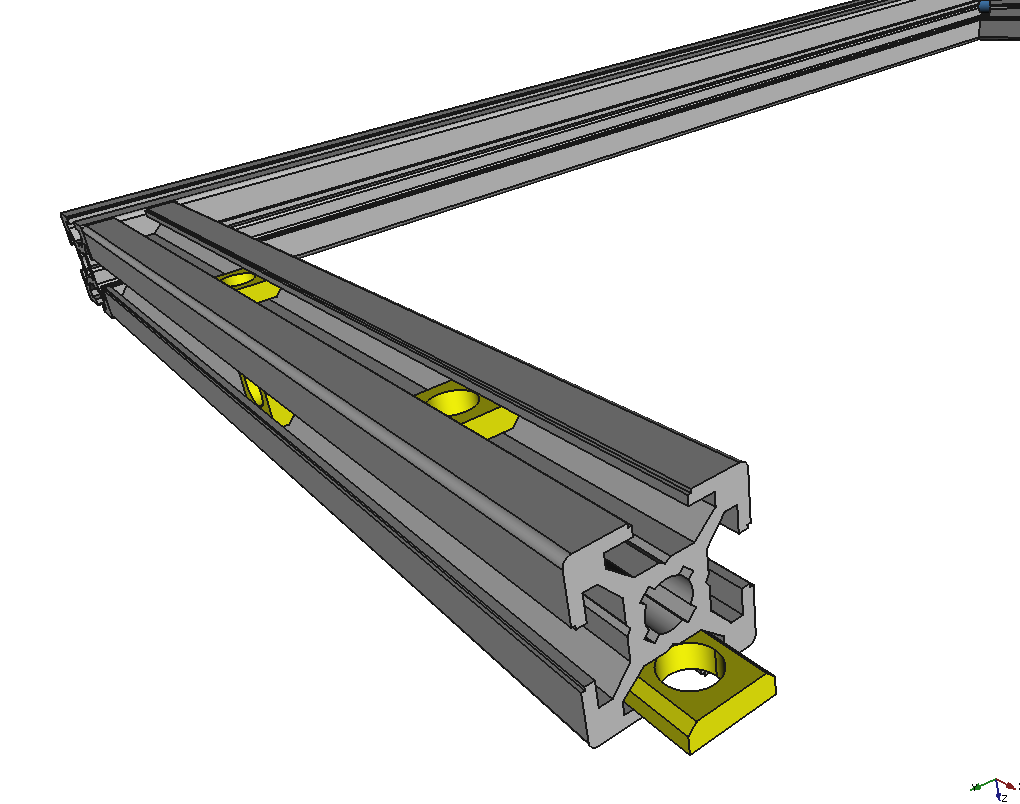
boxframe/buildinstructional/lower_frame/lframe2.png
