CollectiveOpenSourceHardware/LibreSolarBox/boxframe/buildinstructional/lower_frame/lframe3.png

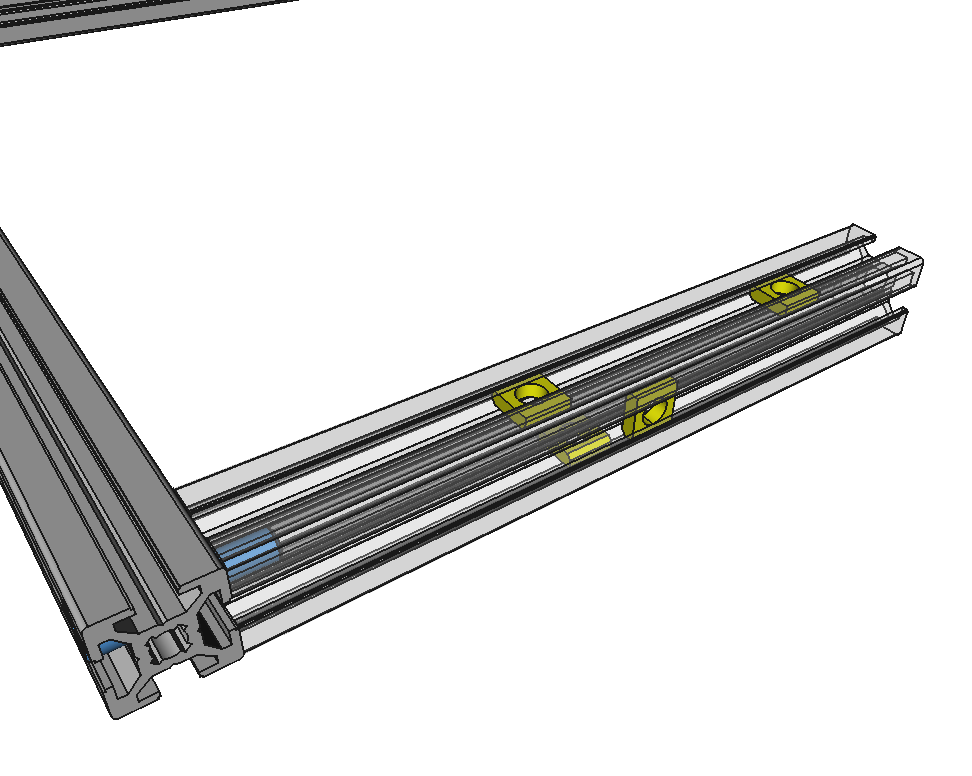
boxframe/buildinstructional/lower_frame/lframe3.png
