CollectiveOpenSourceHardware/LibreSolarBox/boxframe/buildinstructional/lower_frame/lframe4.png

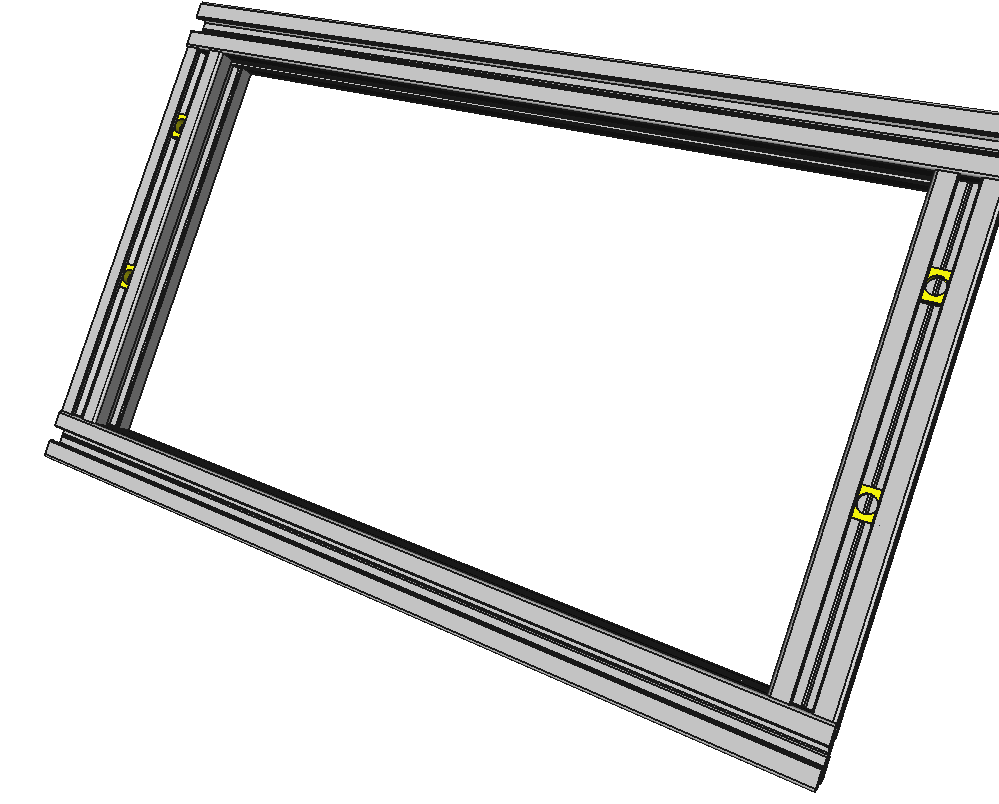
boxframe/buildinstructional/lower_frame/lframe4.png
