CollectiveOpenSourceHardware/LibreSolarBox/boxframe/buildinstructional/rawframe/junction1.png

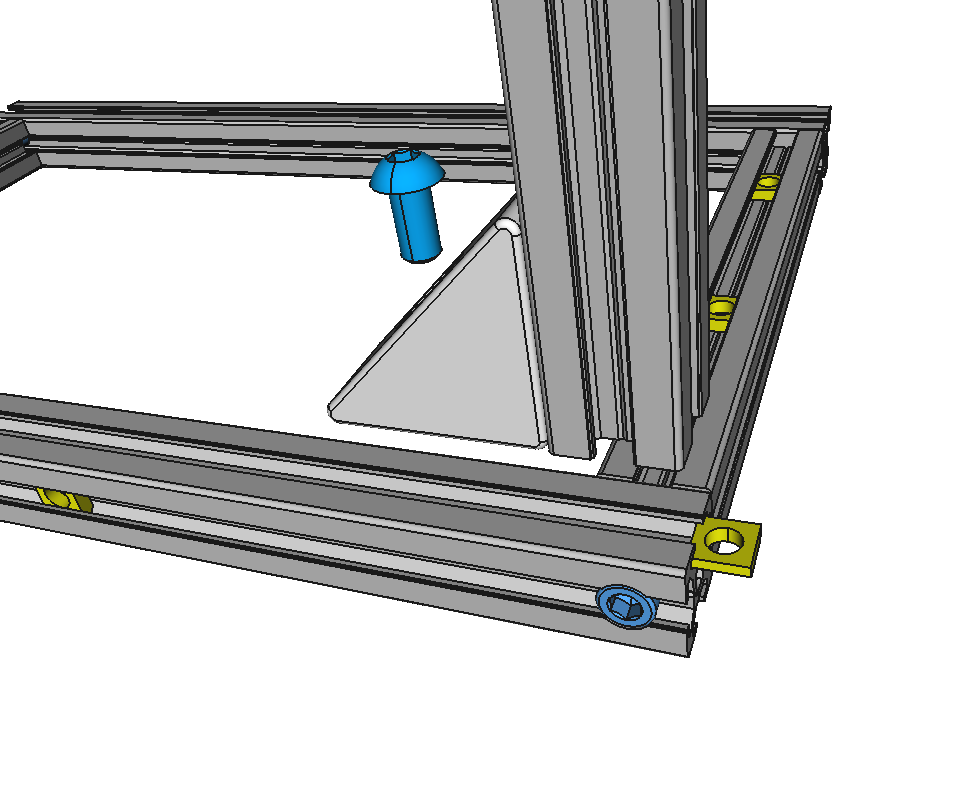
boxframe/buildinstructional/rawframe/junction1.png
