CollectiveOpenSourceHardware/LibreSolarBox/boxframe/buildinstructional/rawframe/junction2.png

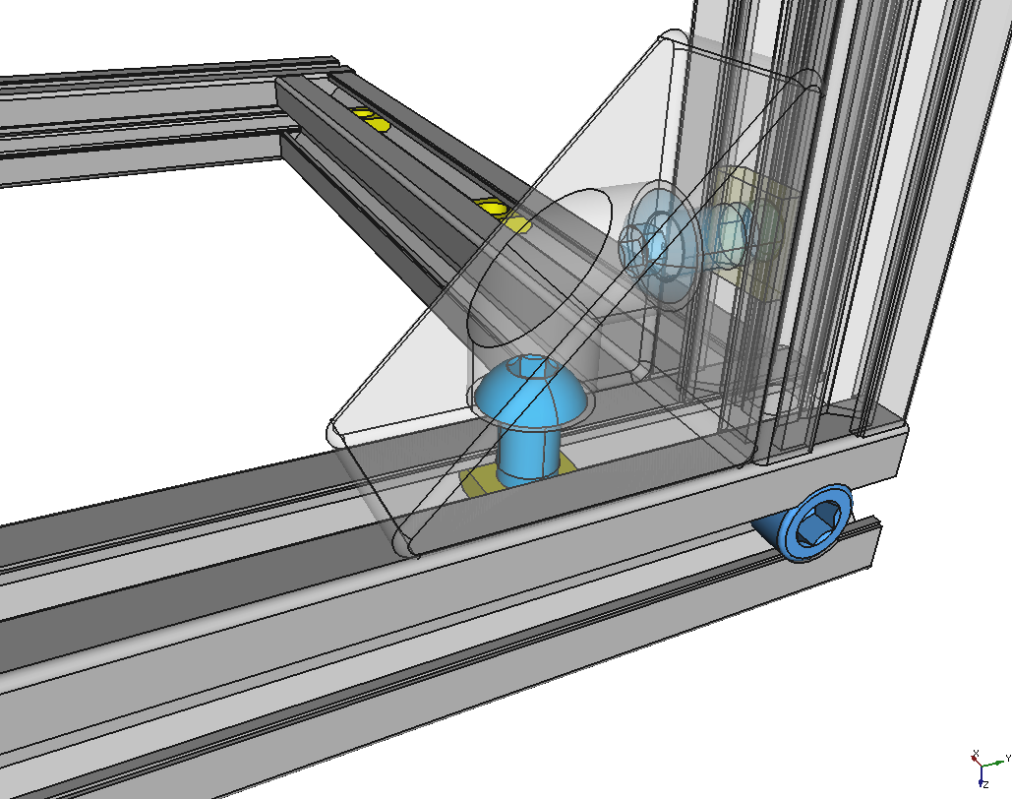
boxframe/buildinstructional/rawframe/junction2.png
