CollectiveOpenSourceHardware/LibreSolarBox/boxframe/buildinstructional/rawframe/junction3.png

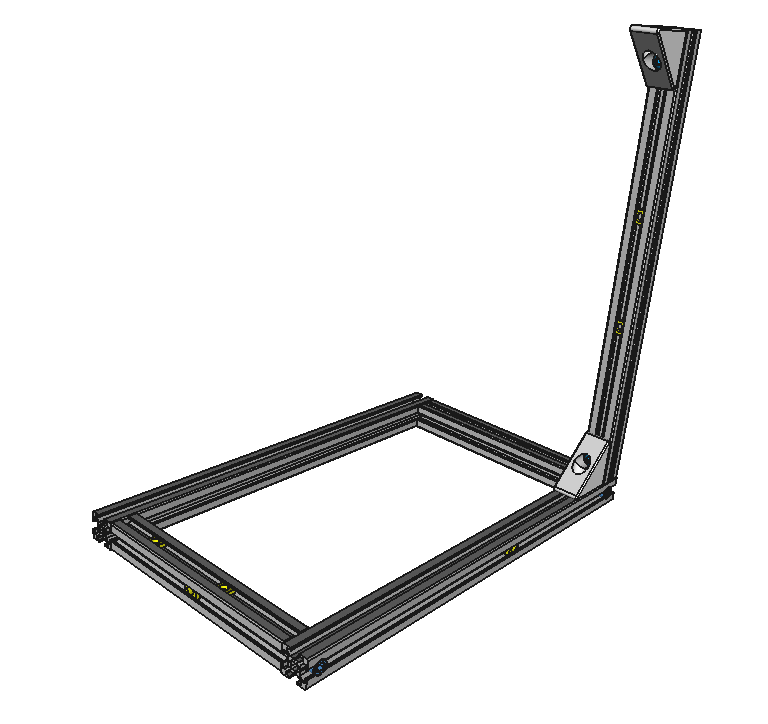
boxframe/buildinstructional/rawframe/junction3.png
