CollectiveOpenSourceHardware/LibreSolarBox/boxframe/buildinstructional/rawframe/junction4.png

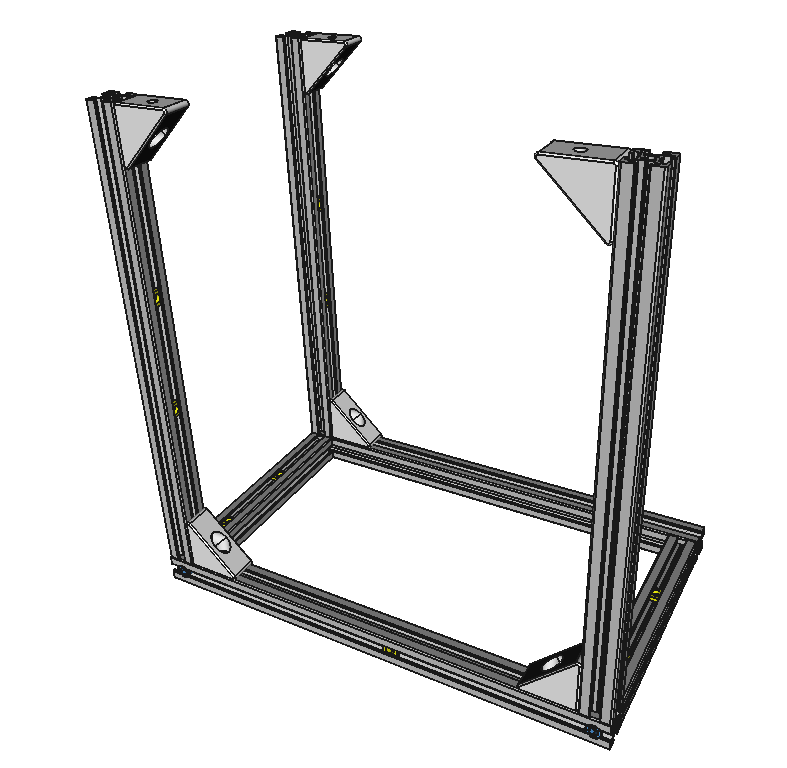
boxframe/buildinstructional/rawframe/junction4.png
