CollectiveOpenSourceHardware/LibreSolarBox/boxframe/buildinstructional/rawframe/junction5.png

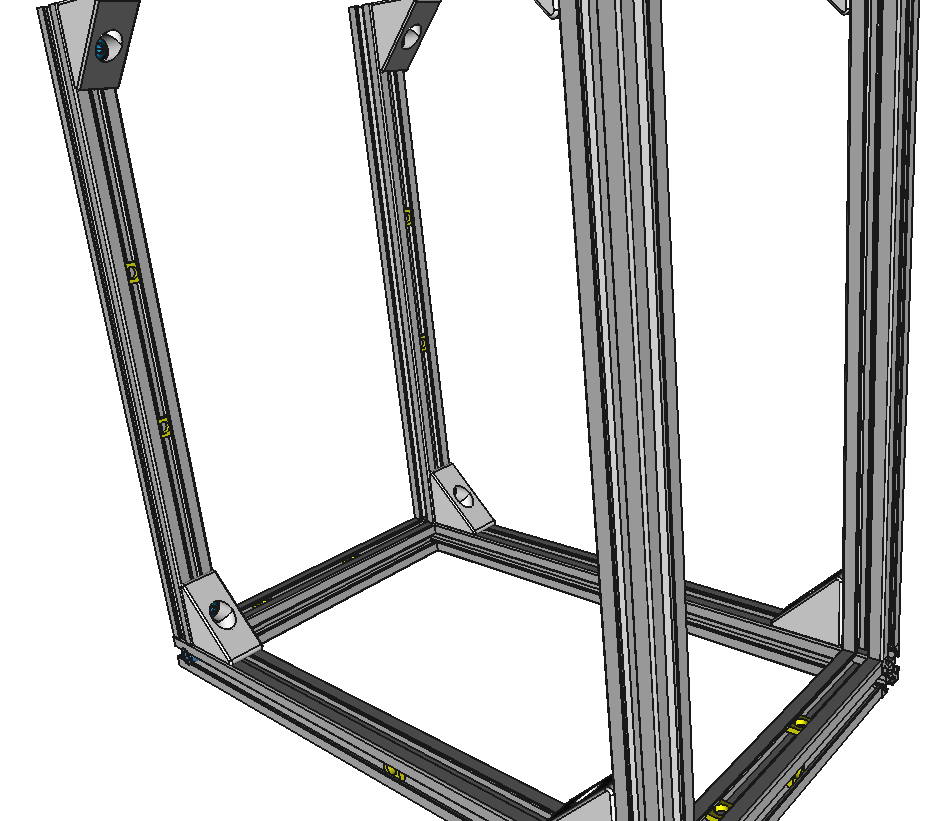
boxframe/buildinstructional/rawframe/junction5.png
