CollectiveOpenSourceHardware/LibreSolarBox/boxframe/buildinstructional/rawframe/junction6.png

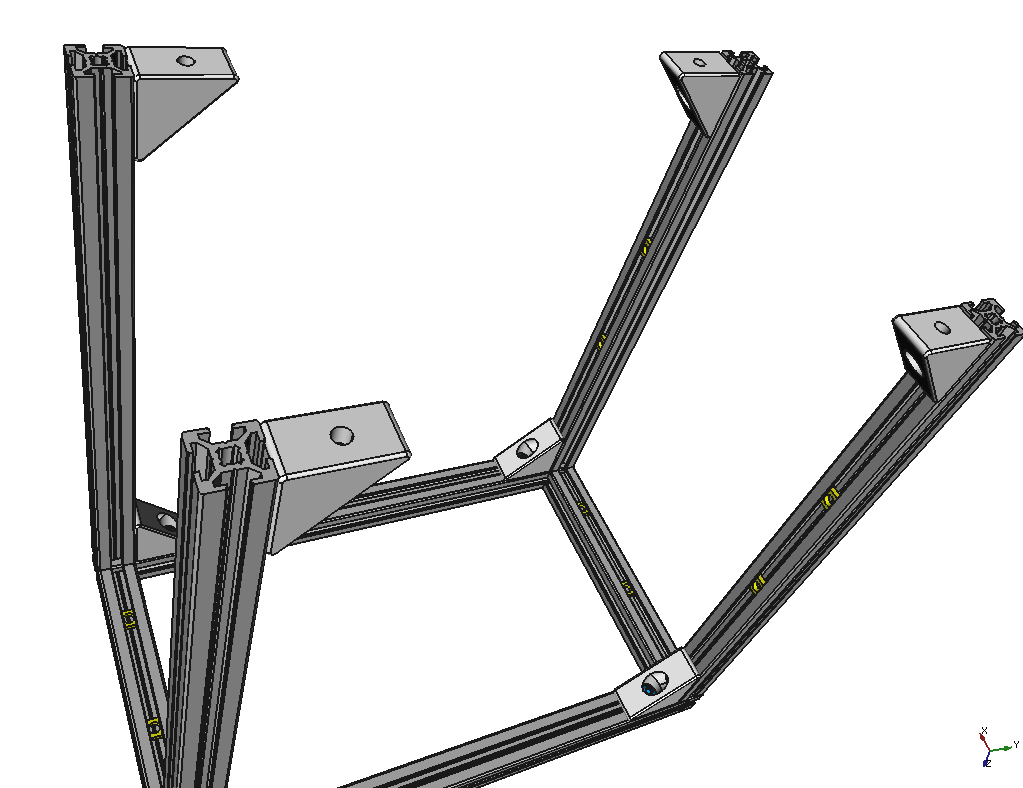
boxframe/buildinstructional/rawframe/junction6.png
