CollectiveOpenSourceHardware/LibreSolarBox/boxframe/buildinstructional/rawframe/junction7.png

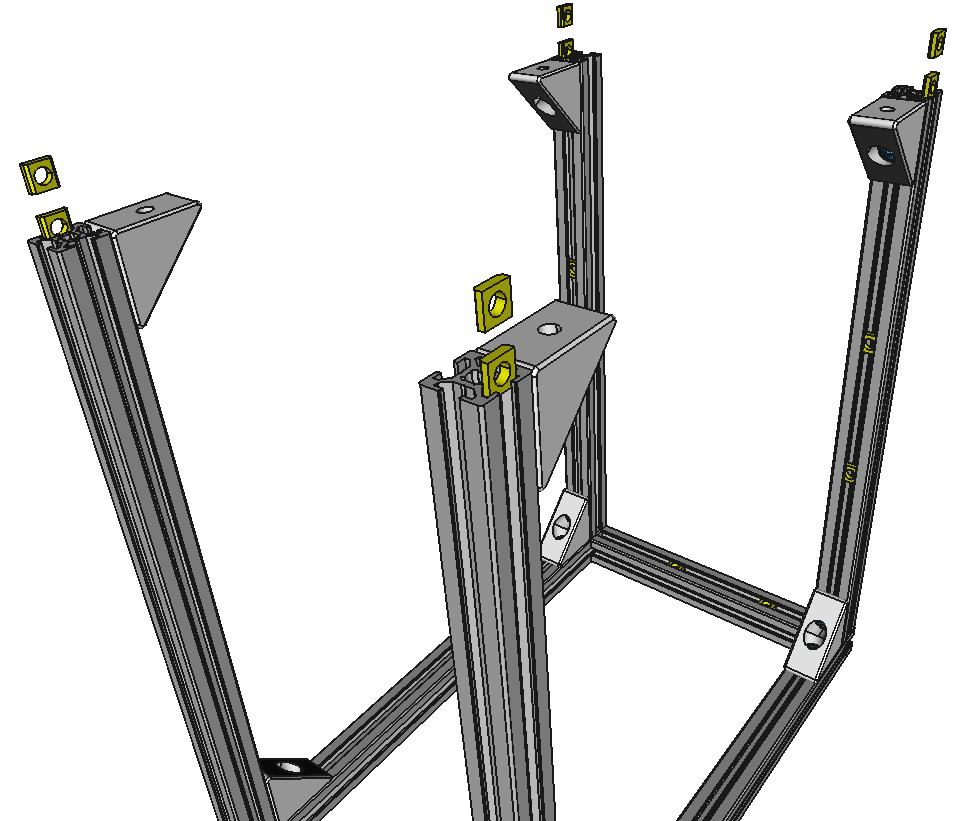
boxframe/buildinstructional/rawframe/junction7.png
