CollectiveOpenSourceHardware/LibreSolarBox/boxframe/buildinstructional/rawframe/junction8.png

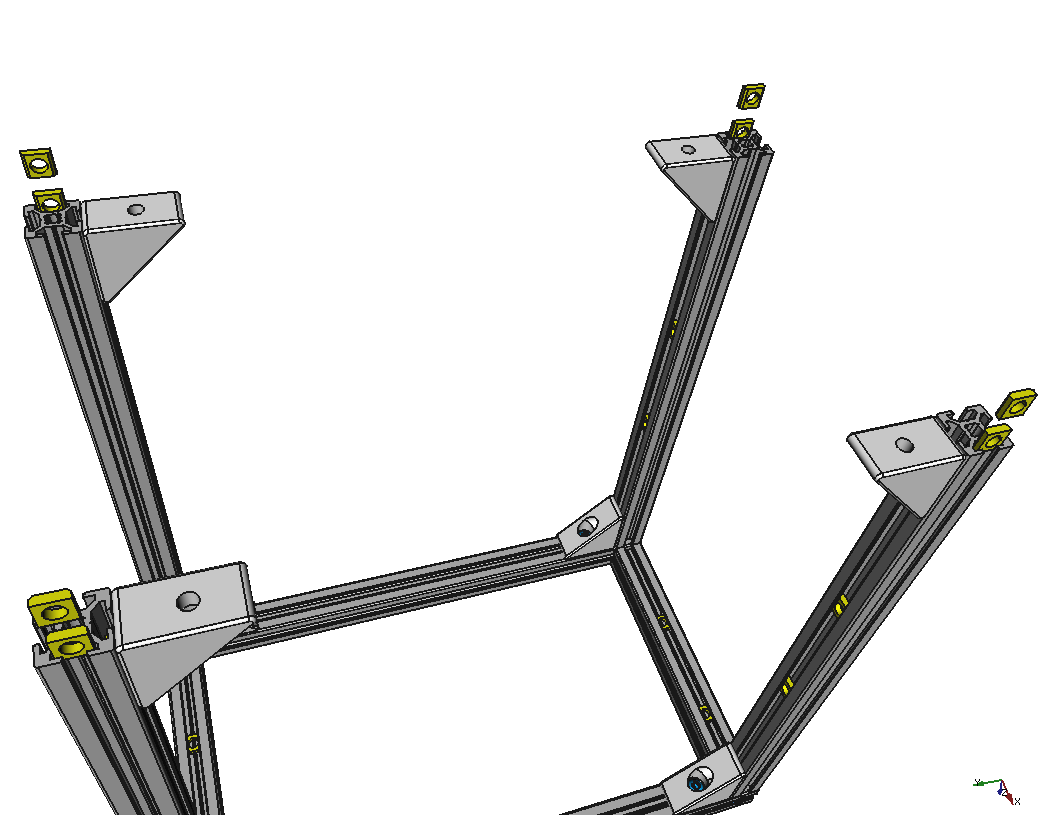
boxframe/buildinstructional/rawframe/junction8.png
