CollectiveOpenSourceHardware/LibreSolarBox/boxframe/buildinstructional/rawframe/junction9.png

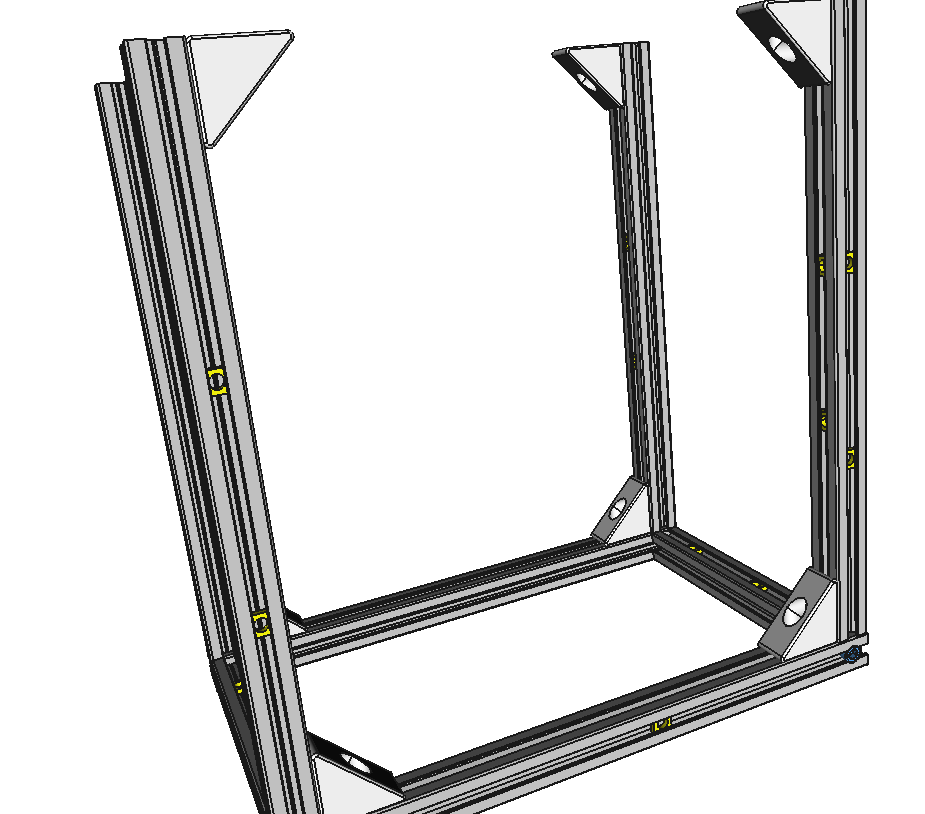
boxframe/buildinstructional/rawframe/junction9.png
