CollectiveOpenSourceHardware/LibreSolarBox/boxframe/buildinstructional/rawframe/junction10.png

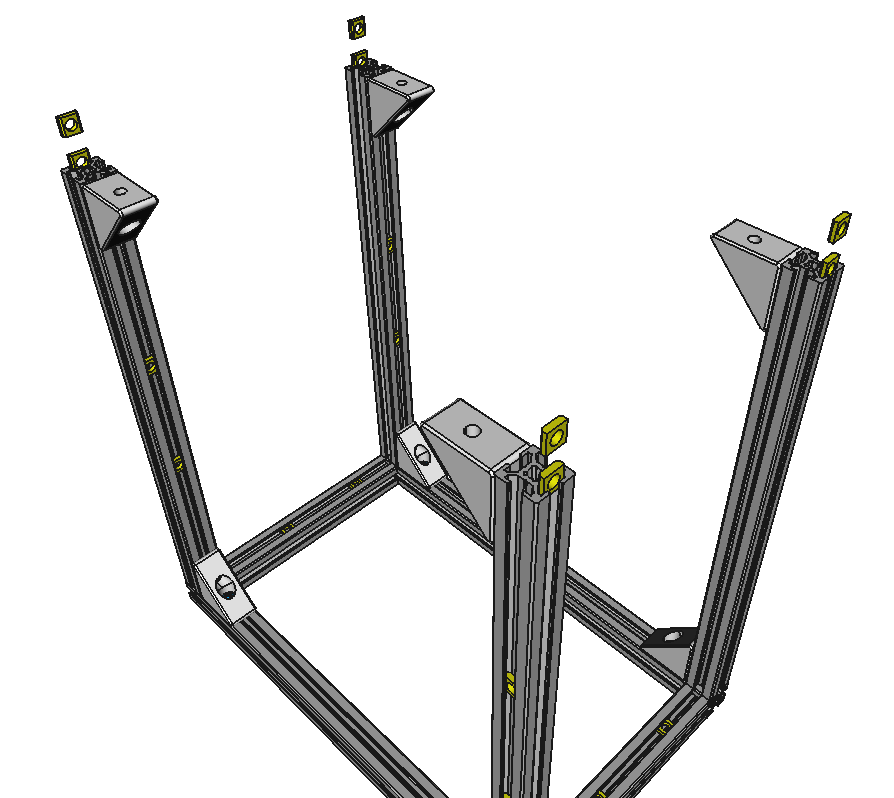
boxframe/buildinstructional/rawframe/junction10.png
