CollectiveOpenSourceHardware/LibreSolarBox/boxframe/buildinstructional/rawframe/junction11.png

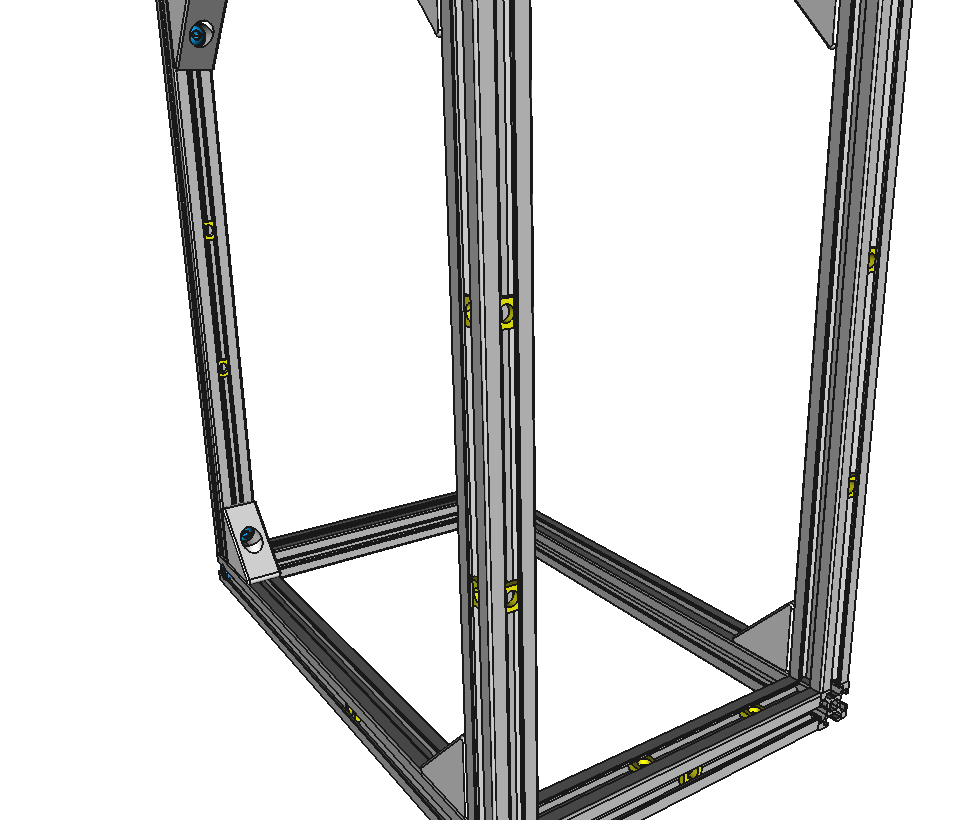
boxframe/buildinstructional/rawframe/junction11.png
