CollectiveOpenSourceHardware/LibreSolarBox/boxframe/buildinstructional/rawframe/junction12.png

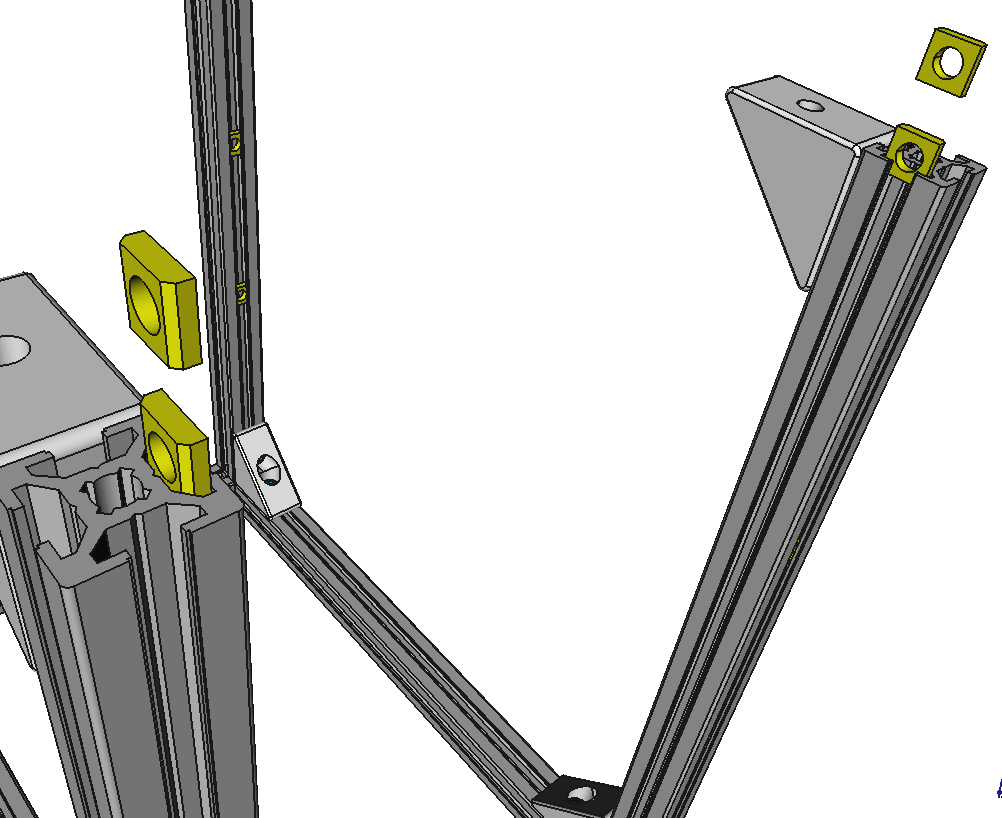
boxframe/buildinstructional/rawframe/junction12.png
