CollectiveOpenSourceHardware/LibreSolarBox/boxframe/buildinstructional/rawframe/junction14.png

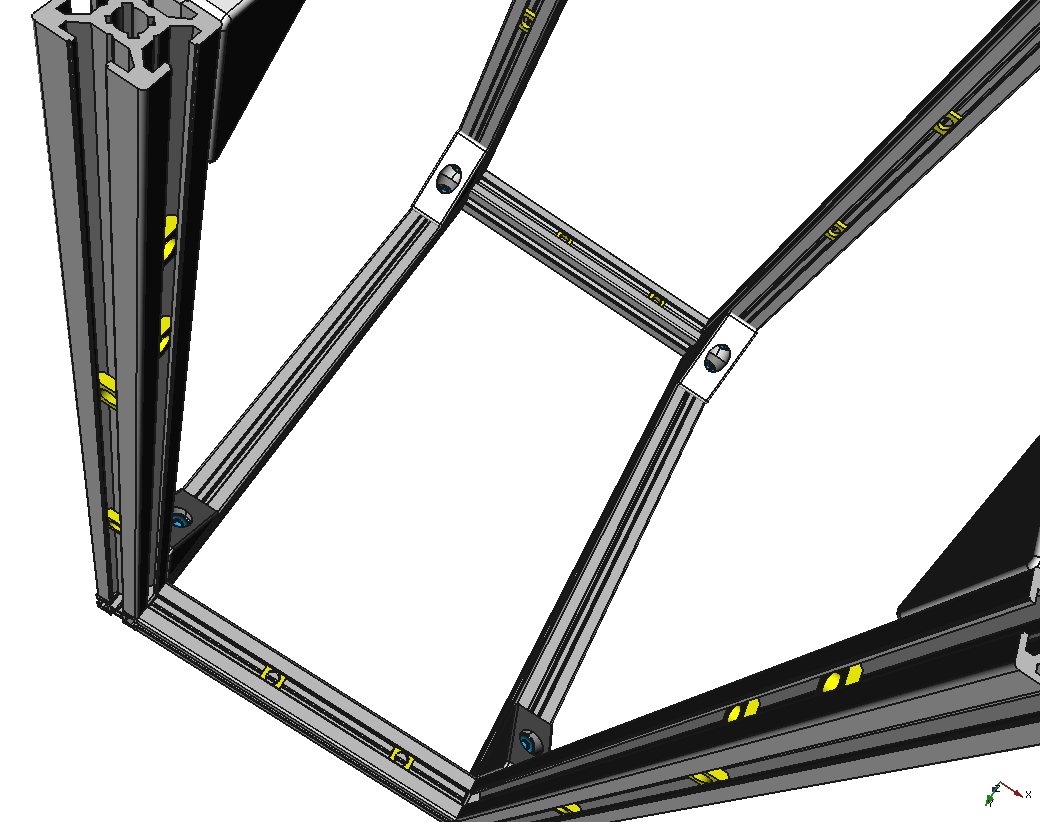
boxframe/buildinstructional/rawframe/junction14.png
