CollectiveOpenSourceHardware/LibreSolarBox/boxframe/buildinstructional/rawframe/junction15.png

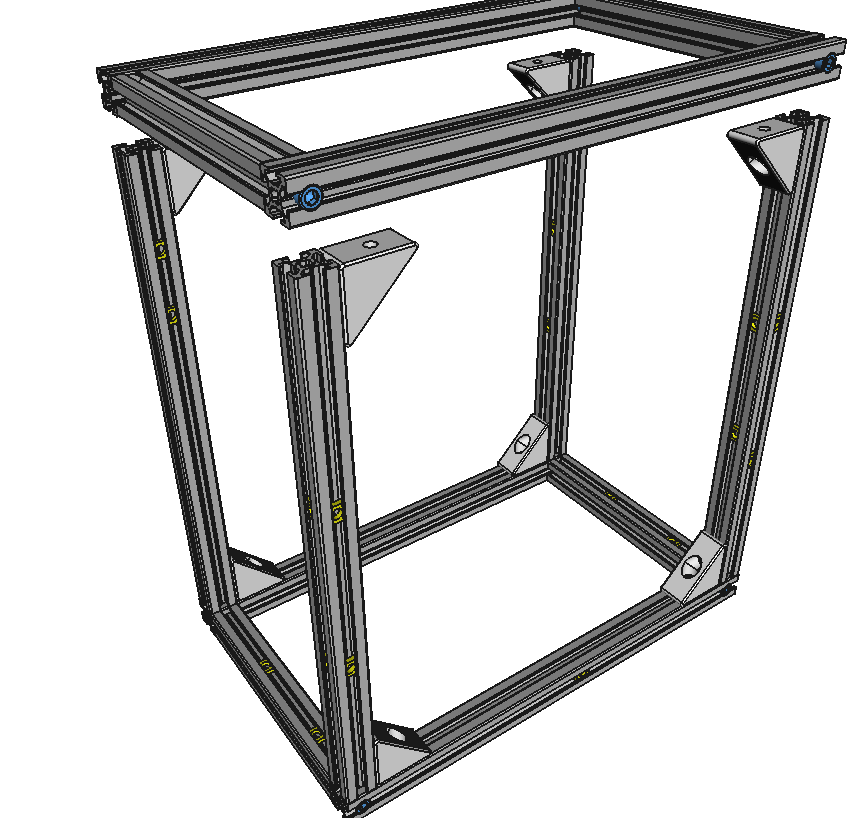
boxframe/buildinstructional/rawframe/junction15.png
