CollectiveOpenSourceHardware/LibreSolarBox/boxframe/buildinstructional/rawframe/junction15b.png

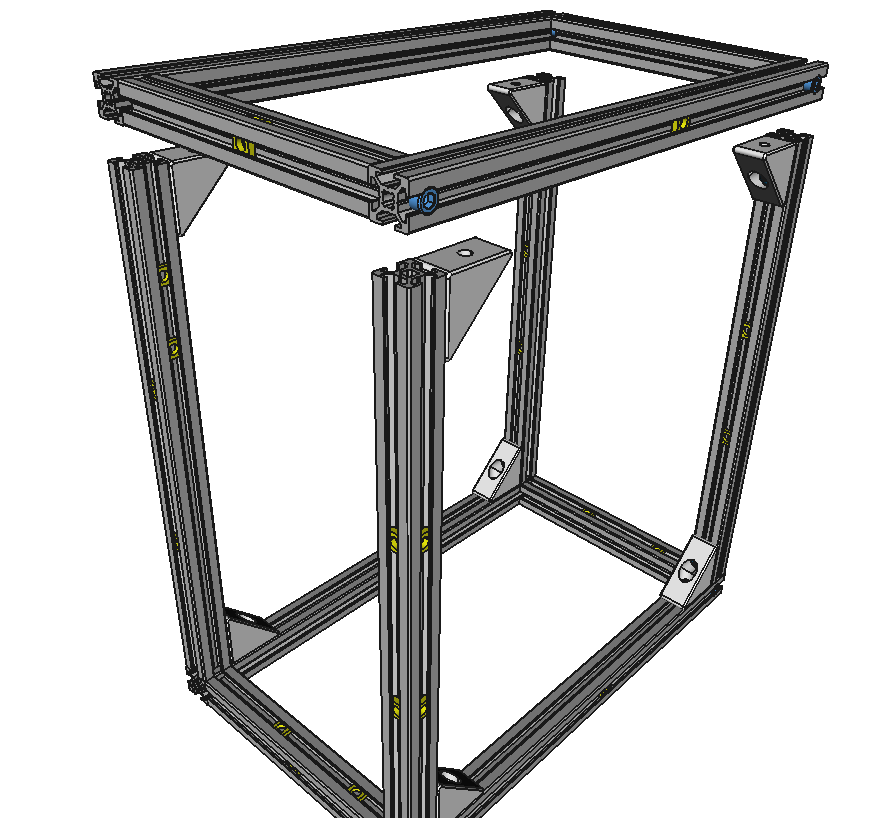
boxframe/buildinstructional/rawframe/junction15b.png
