CollectiveOpenSourceHardware/LibreSolarBox/boxframe/buildinstructional/rawframe/junction16.png

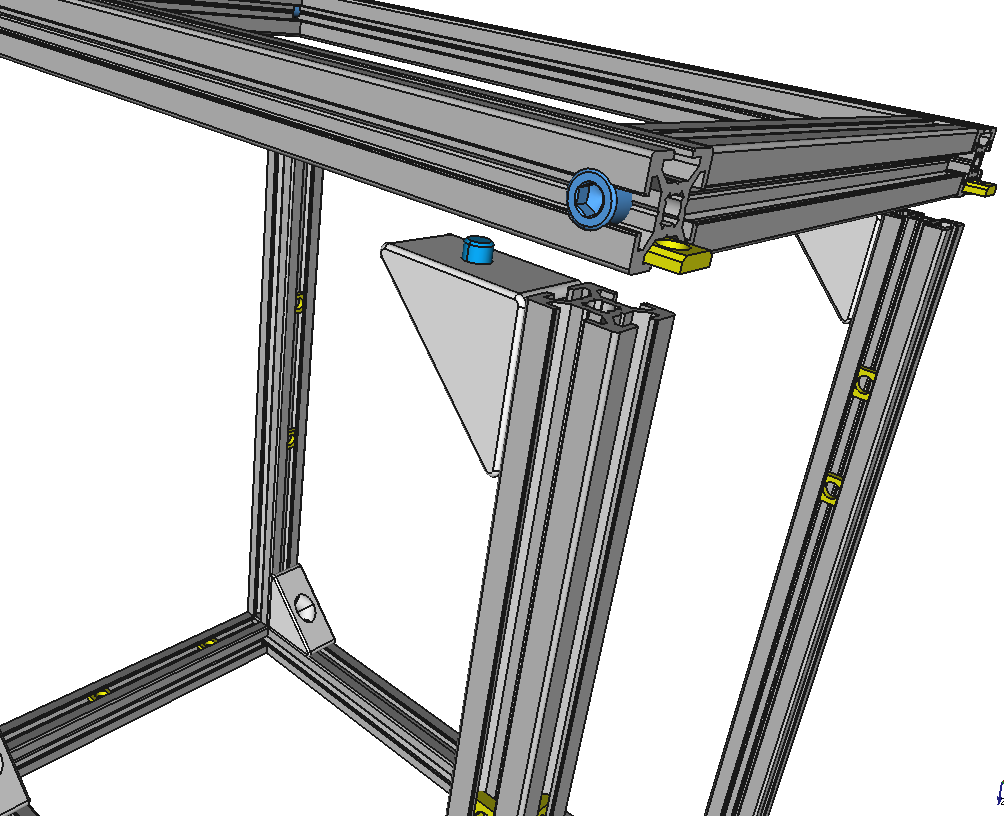
boxframe/buildinstructional/rawframe/junction16.png
