CollectiveOpenSourceHardware/LibreSolarBox/boxframe/buildinstructional/rawframe/junction16b.png

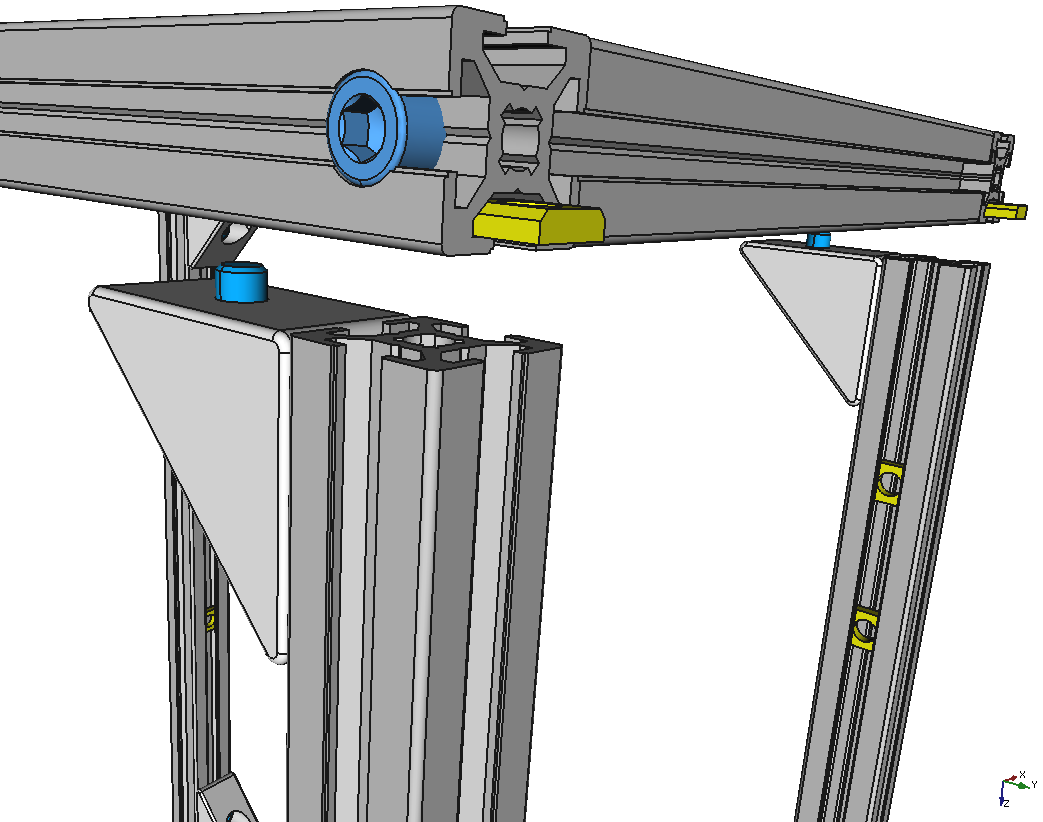
boxframe/buildinstructional/rawframe/junction16b.png
