CollectiveOpenSourceHardware/LibreSolarBox/boxframe/buildinstructional/rawframe/junction16c.png

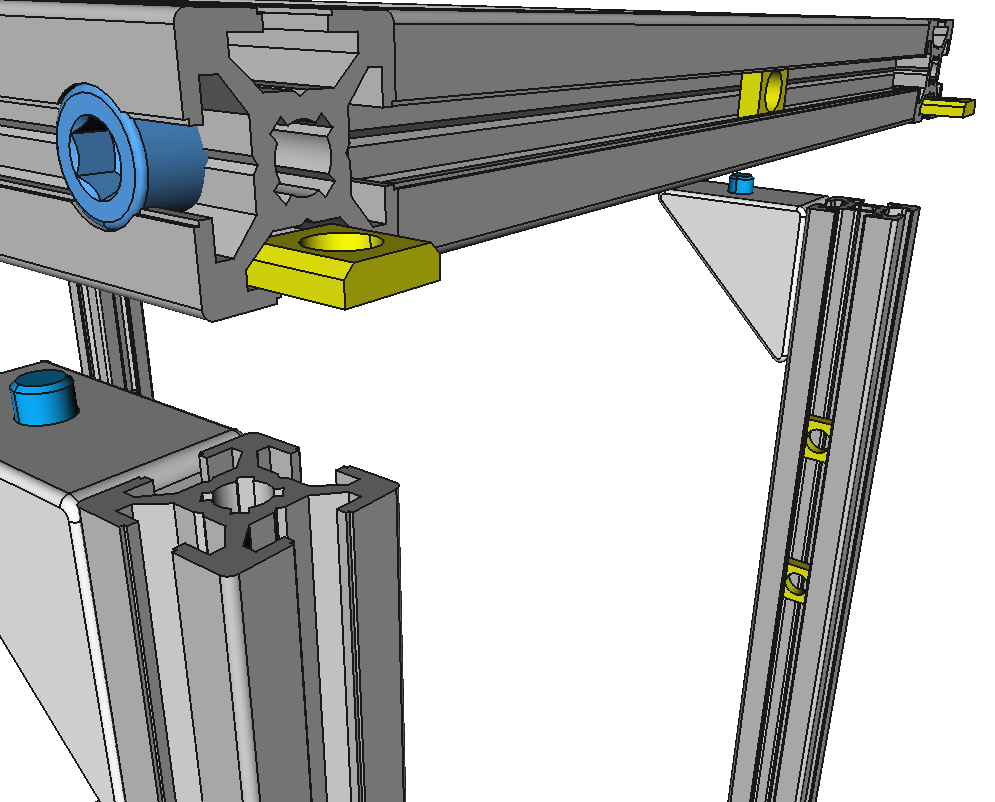
boxframe/buildinstructional/rawframe/junction16c.png
