CollectiveOpenSourceHardware/LibreSolarBox/boxframe/buildinstructional/rawframe/junction17.png

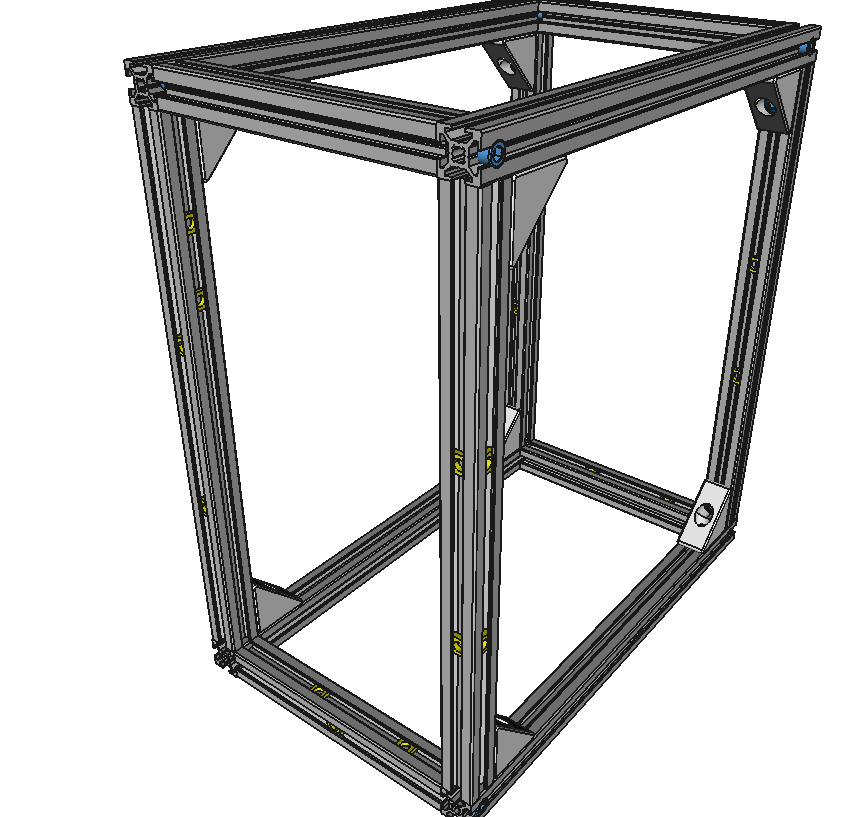
boxframe/buildinstructional/rawframe/junction17.png
