CollectiveOpenSourceHardware/LibreSolarBox/boxframe/buildinstructional/rawframe/junction17b.png

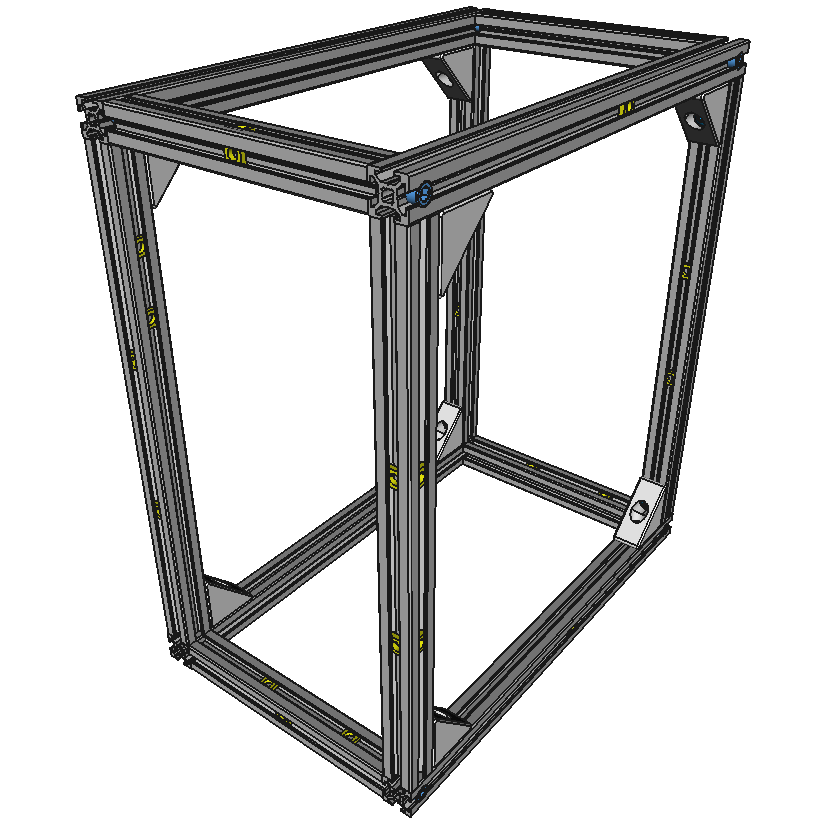
boxframe/buildinstructional/rawframe/junction17b.png
