CollectiveOpenSourceHardware/LibreSolarBox/boxframe/buildinstructional/upper_frame/corner_junction1.png

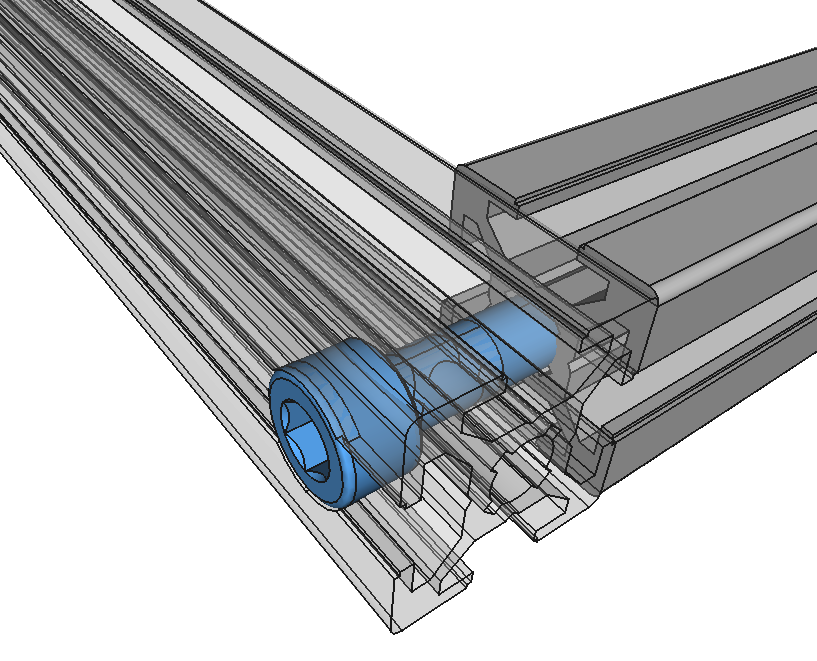
boxframe/buildinstructional/upper_frame/corner_junction1.png
