CollectiveOpenSourceHardware/LibreSolarBox/boxframe/buildinstructional/upper_frame/corner_junction2.png

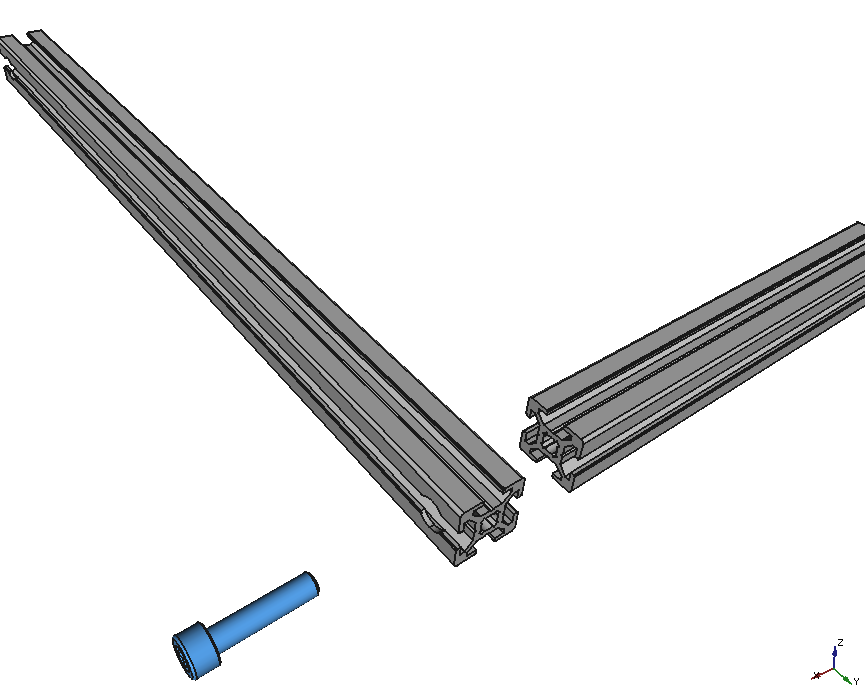
boxframe/buildinstructional/upper_frame/corner_junction2.png
