CollectiveOpenSourceHardware/LibreSolarBox/boxframe/buildinstructional/upper_frame/frame1.png

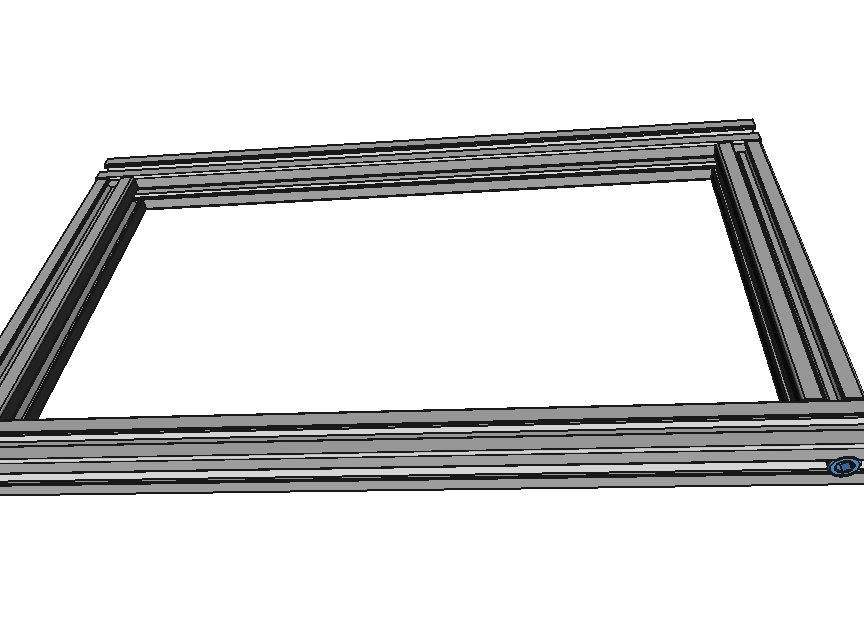
boxframe/buildinstructional/upper_frame/frame1.png
