CollectiveOpenSourceHardware/LibreSolarBox/boxframe/buildinstructional/upper_frame/frame2.png

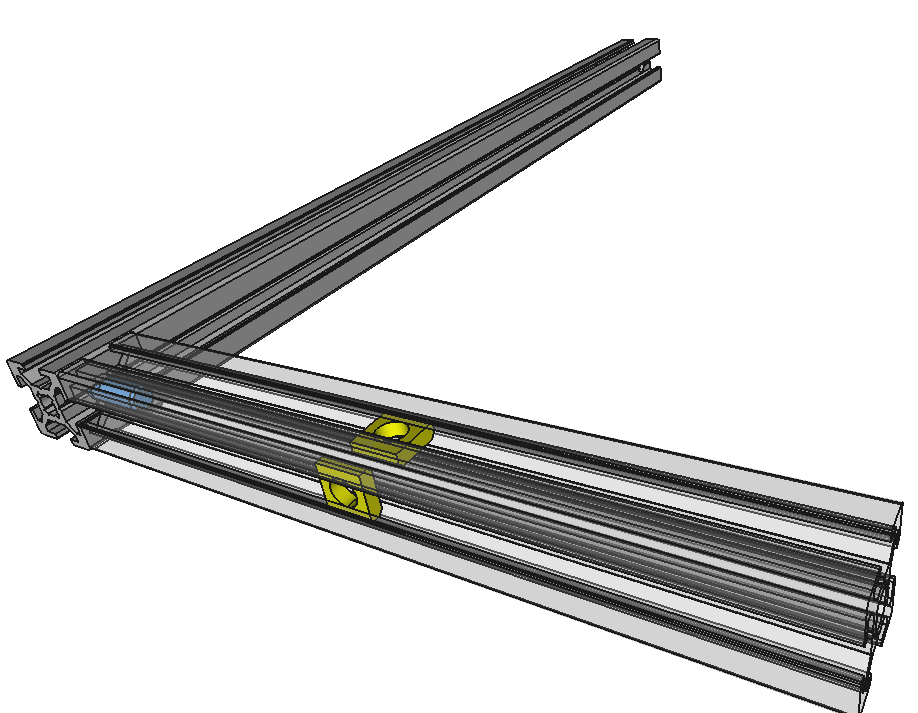
boxframe/buildinstructional/upper_frame/frame2.png
