CollectiveOpenSourceHardware/LibreSolarBox/boxframe/buildinstructional/upper_frame/frame3.png

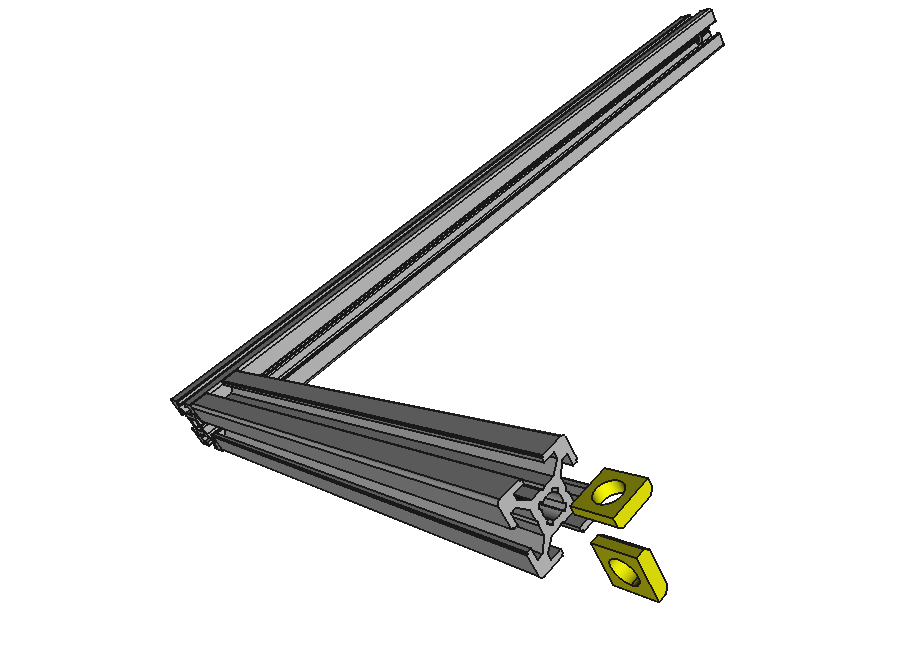
boxframe/buildinstructional/upper_frame/frame3.png
