CollectiveOpenSourceHardware/LibreSolarBox/boxframe/buildinstructional/upper_frame/frame4.png

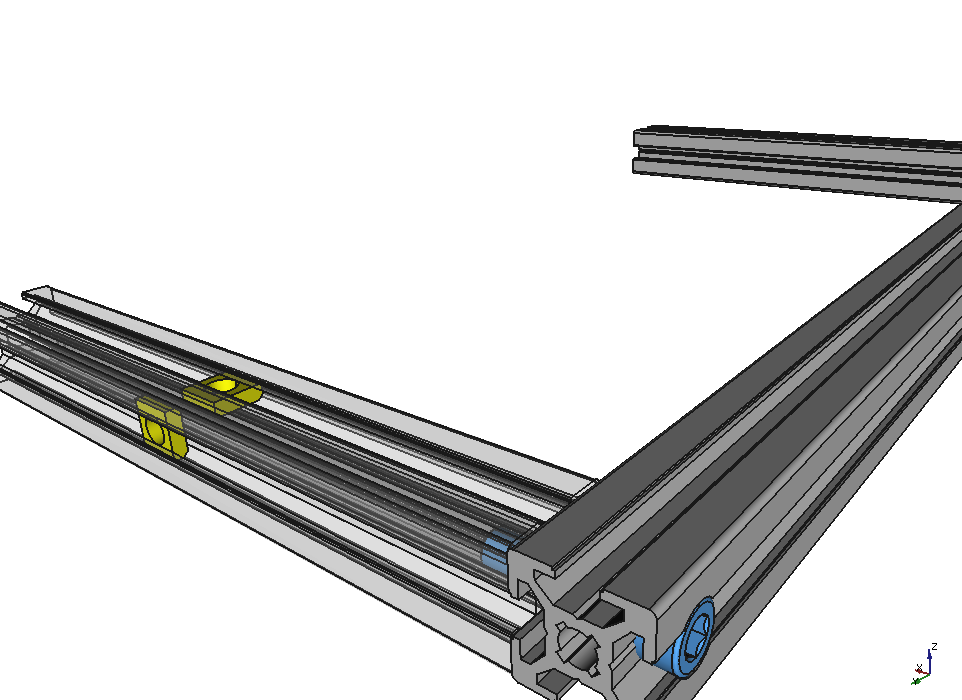
boxframe/buildinstructional/upper_frame/frame4.png
