CollectiveOpenSourceHardware/LibreSolarBox/boxframe/buildinstructional/upper_frame/frame5.png

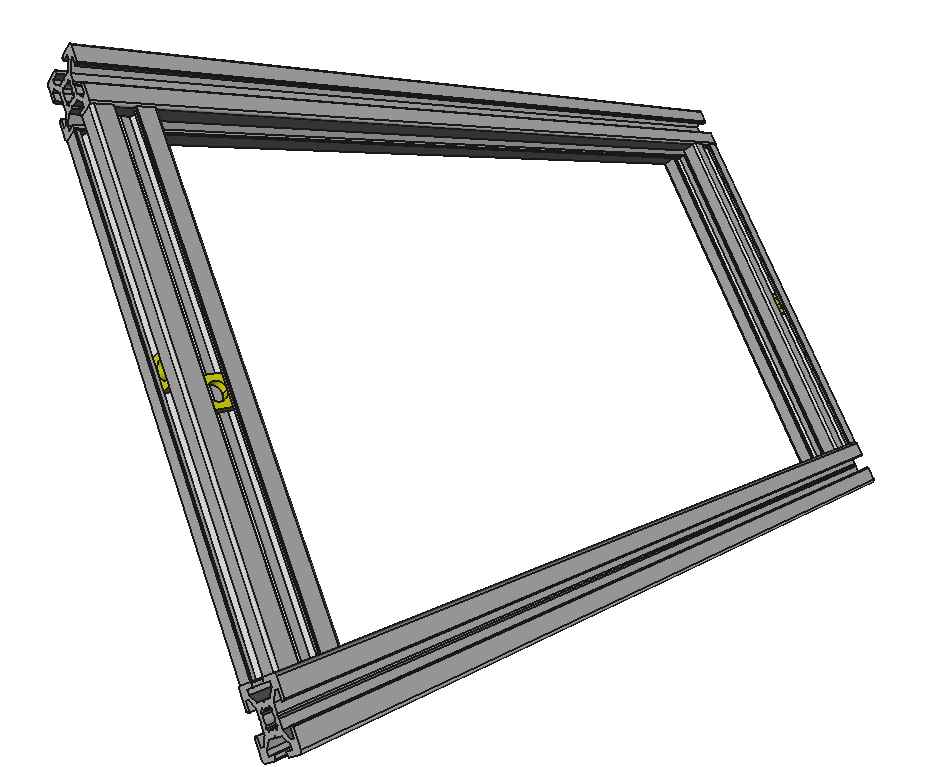
boxframe/buildinstructional/upper_frame/frame5.png
