CollectiveOpenSourceHardware/LibreSolarBox/boxframe/buildinstructional/upper_frame/frame7.png

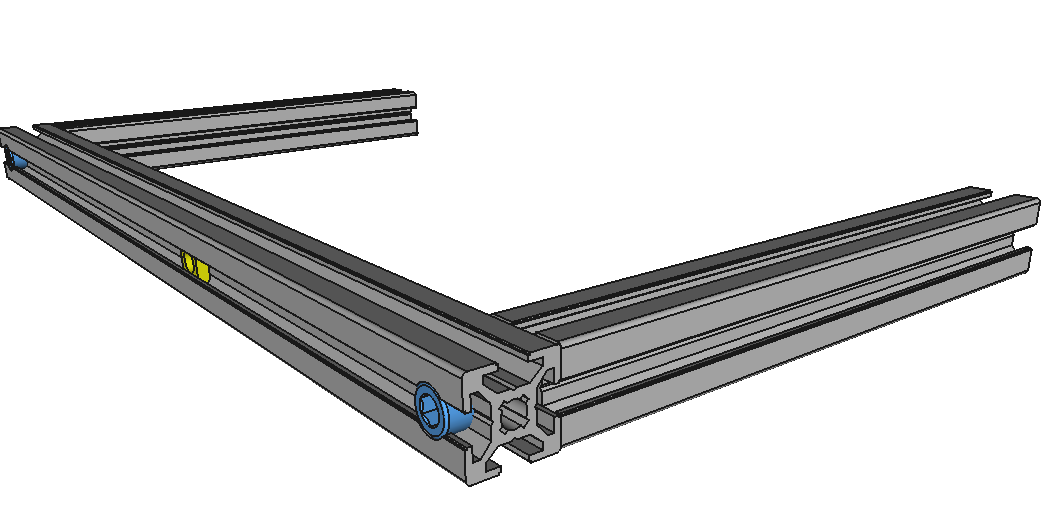
boxframe/buildinstructional/upper_frame/frame7.png
