CollectiveOpenSourceHardware/LibreSolarBox/boxframe/buildinstructional/upper_frame/frame8.png

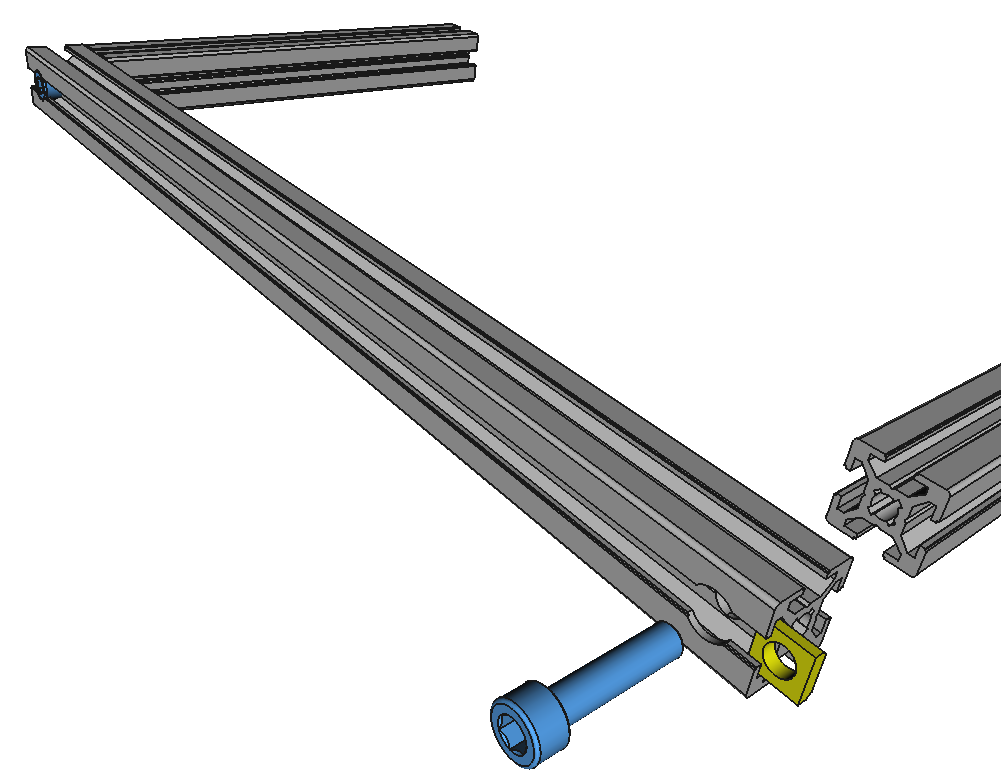
boxframe/buildinstructional/upper_frame/frame8.png
