CollectiveOpenSourceHardware/LibreSolarBox/boxframe/buildinstructional/upper_frame/frame9.png

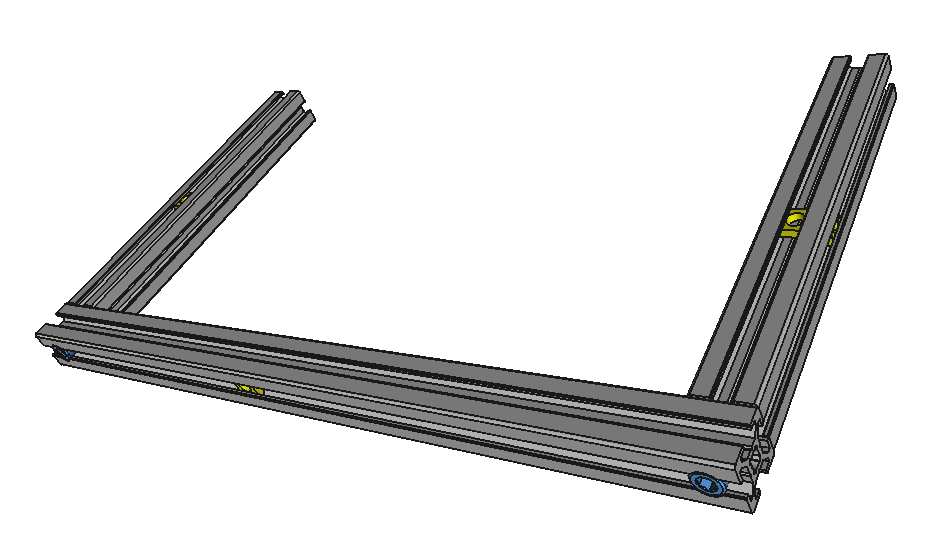
boxframe/buildinstructional/upper_frame/frame9.png
