CollectiveOpenSourceHardware/LibreSolarBox/boxframe/buildinstructional/upper_frame/frame10.png

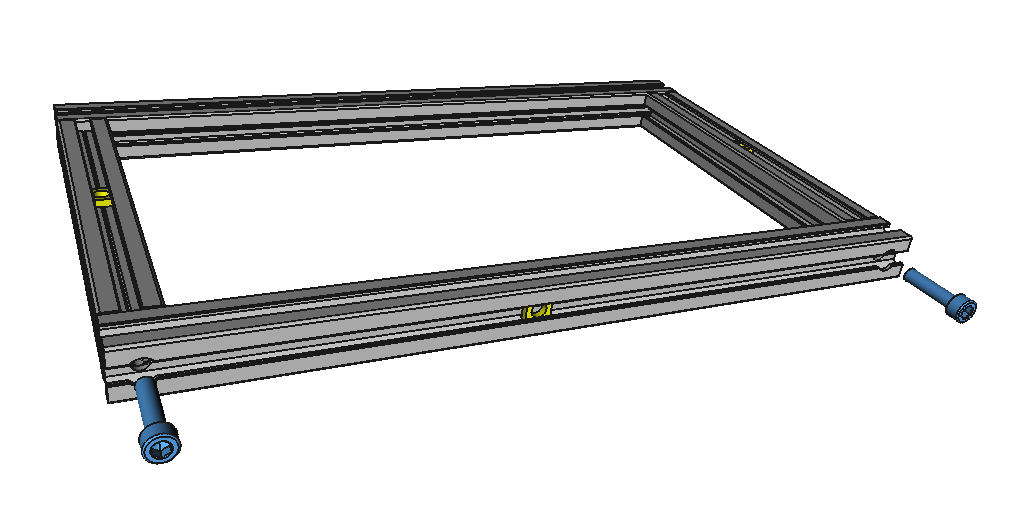
boxframe/buildinstructional/upper_frame/frame10.png
