CollectiveOpenSourceHardware/LibreSolarBox/boxframe/buildinstructional/upper_frame/frame11.png

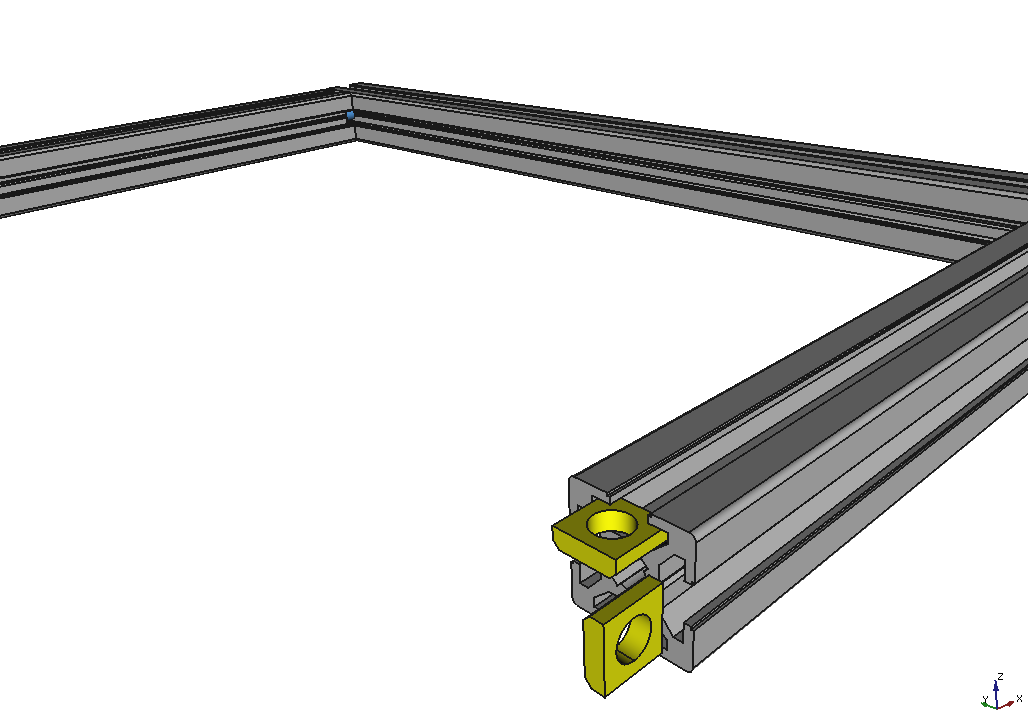
boxframe/buildinstructional/upper_frame/frame11.png
