CollectiveOpenSourceHardware/LibreSolarBox/boxframe/buildinstructional/upright/corner1.png

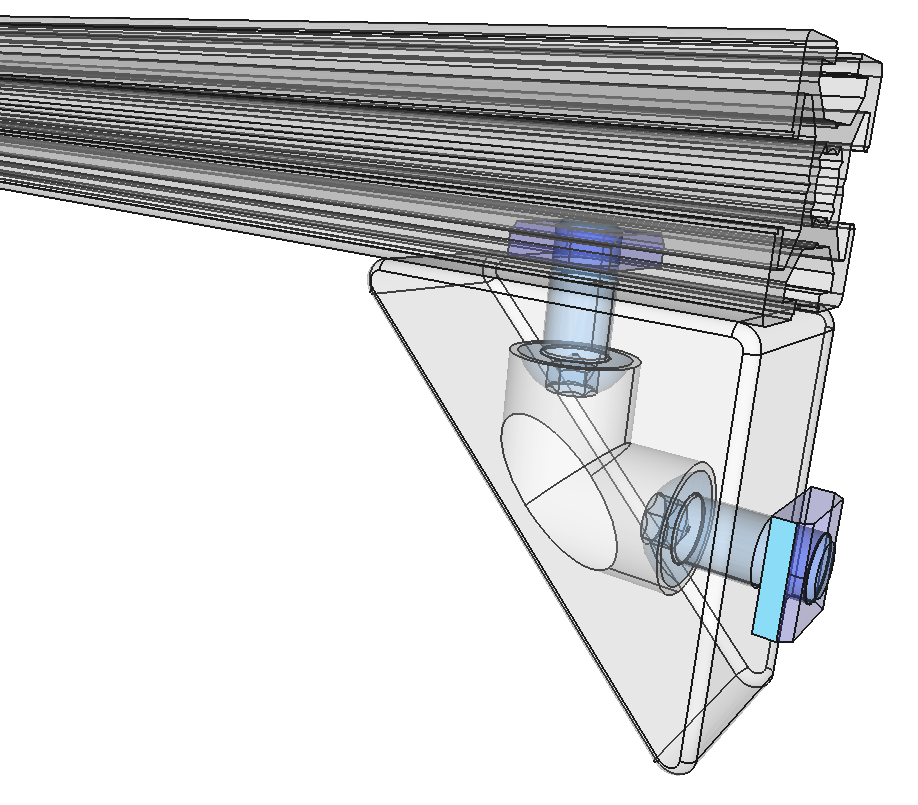
boxframe/buildinstructional/upright/corner1.png
