CollectiveOpenSourceHardware/LibreSolarBox/boxframe/buildinstructional/upright/corner3.png

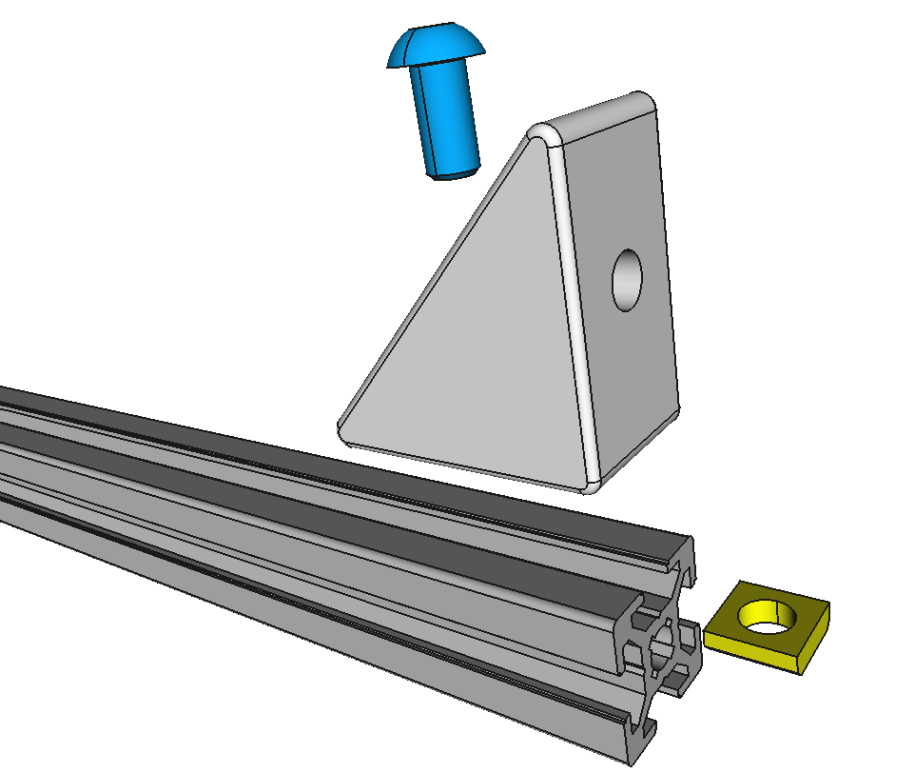
boxframe/buildinstructional/upright/corner3.png
