CollectiveOpenSourceHardware/LibreSolarBox/boxframe/buildinstructional/upright/corner4.png

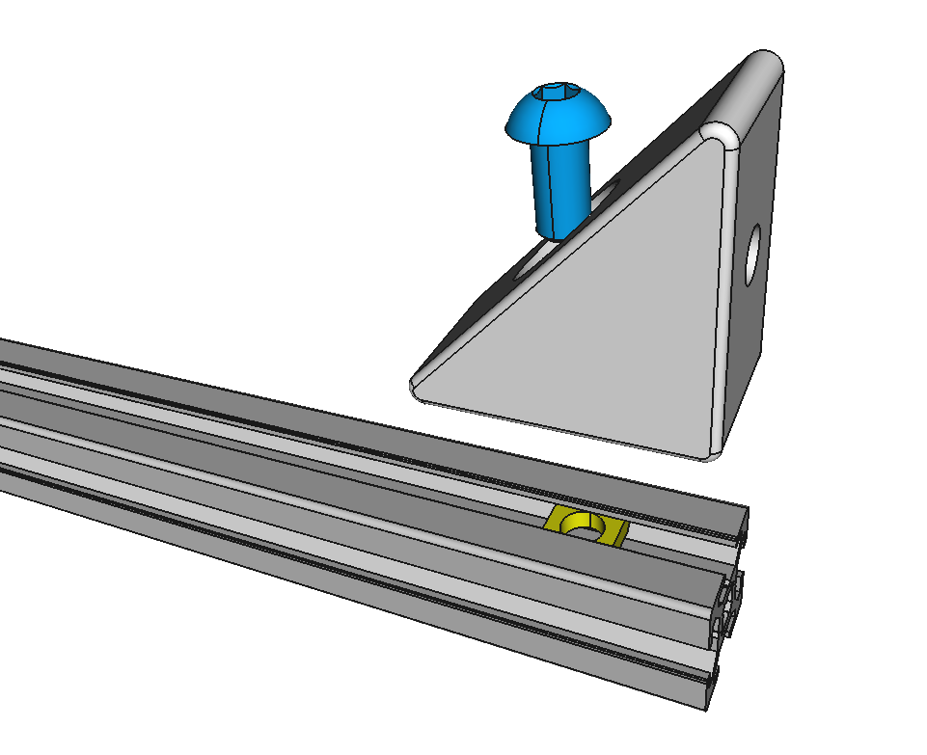
boxframe/buildinstructional/upright/corner4.png
