CollectiveOpenSourceHardware/LibreSolarBox/boxframe/buildinstructional/upright/corner5.png

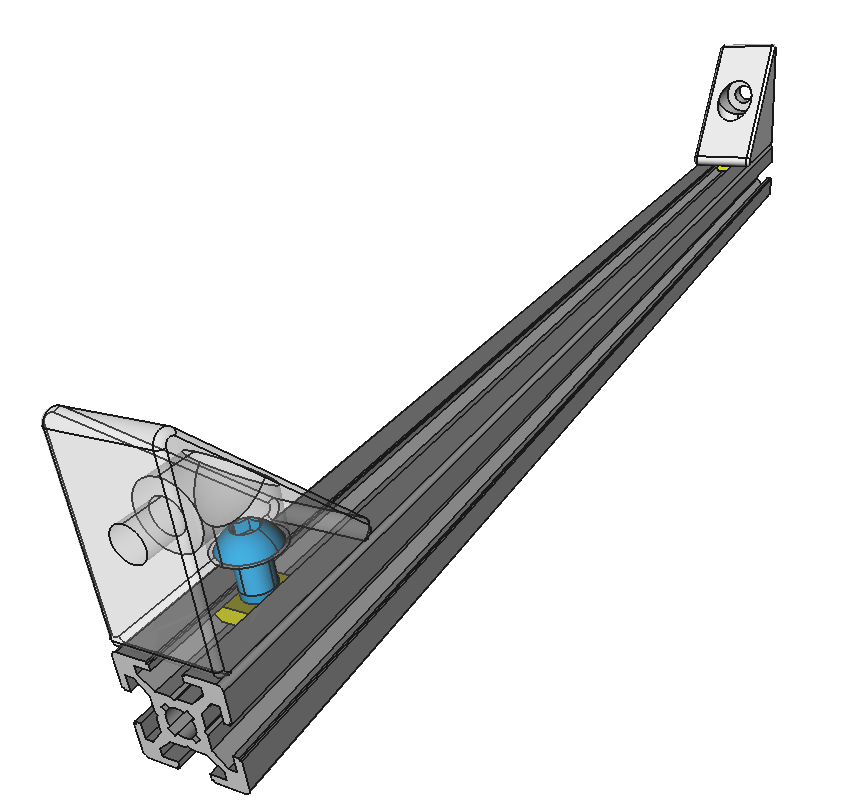
boxframe/buildinstructional/upright/corner5.png
