CollectiveOpenSourceHardware/LibreSolarBox/boxframe/buildinstructional/upright/corner6.png

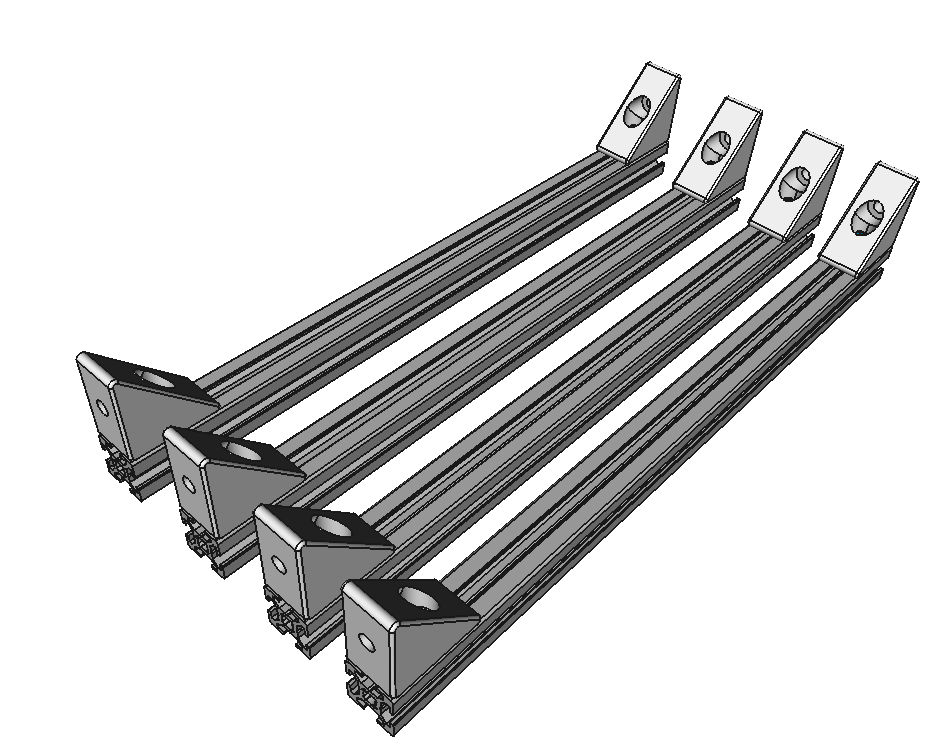
boxframe/buildinstructional/upright/corner6.png
