CollectiveOpenSourceHardware/LibreSolarBox/boxframe/buildinstructional/upright/corner7.png

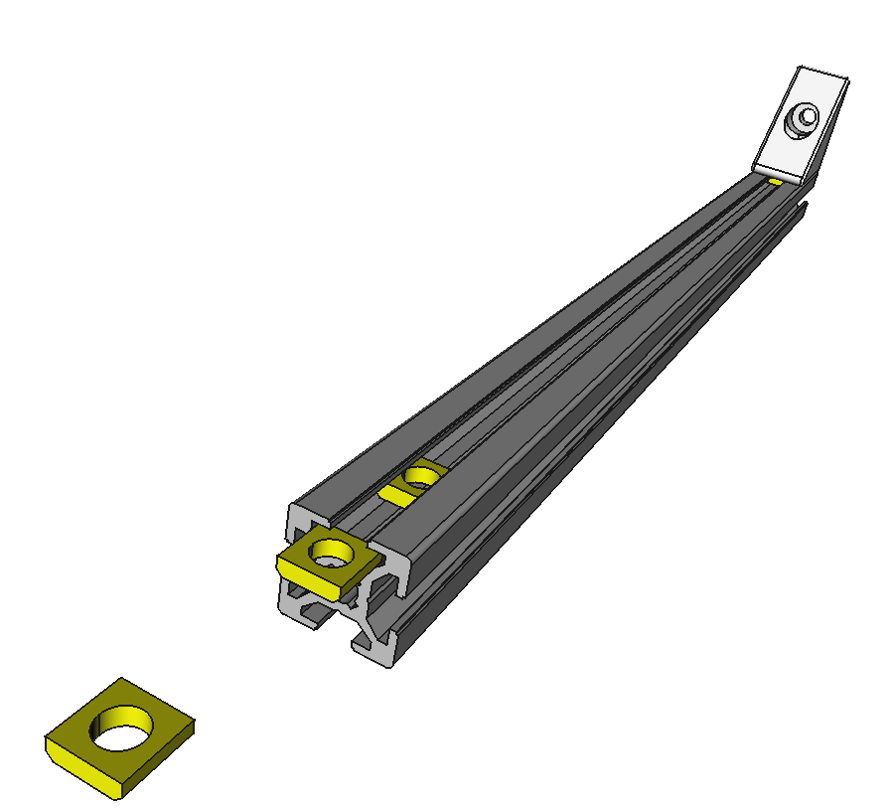
boxframe/buildinstructional/upright/corner7.png
