CollectiveOpenSourceHardware/LibreSolarBox/boxframe/buildinstructional/upright/corner8.png

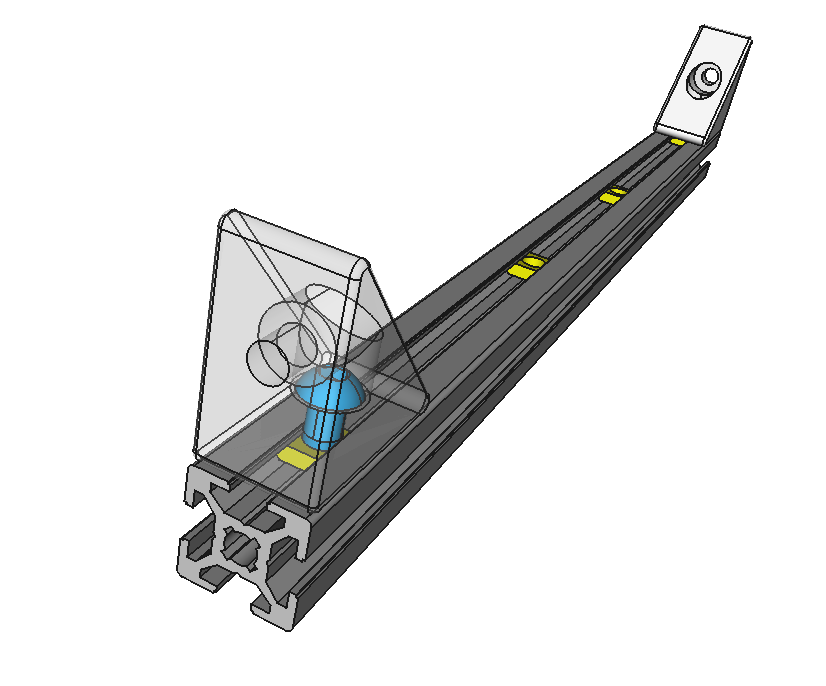
boxframe/buildinstructional/upright/corner8.png
