CollectiveOpenSourceHardware/LibreSolarBox/boxframe/buildinstructional/upright/corner8b.png

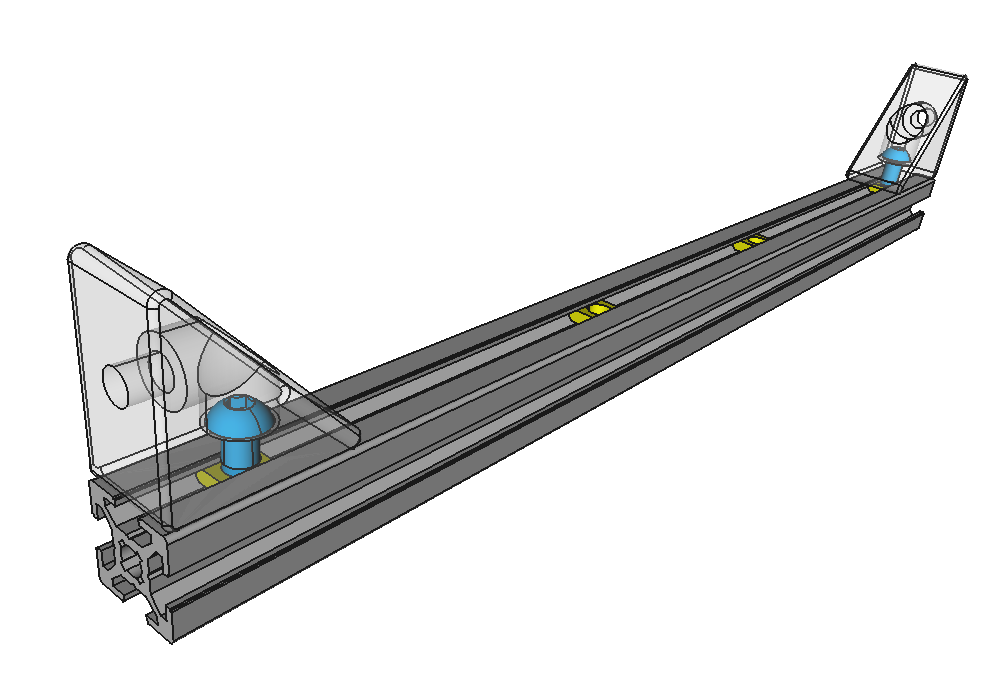
boxframe/buildinstructional/upright/corner8b.png
