CollectiveOpenSourceHardware/LibreSolarBox/boxframe/buildinstructional/upright/corner9.png

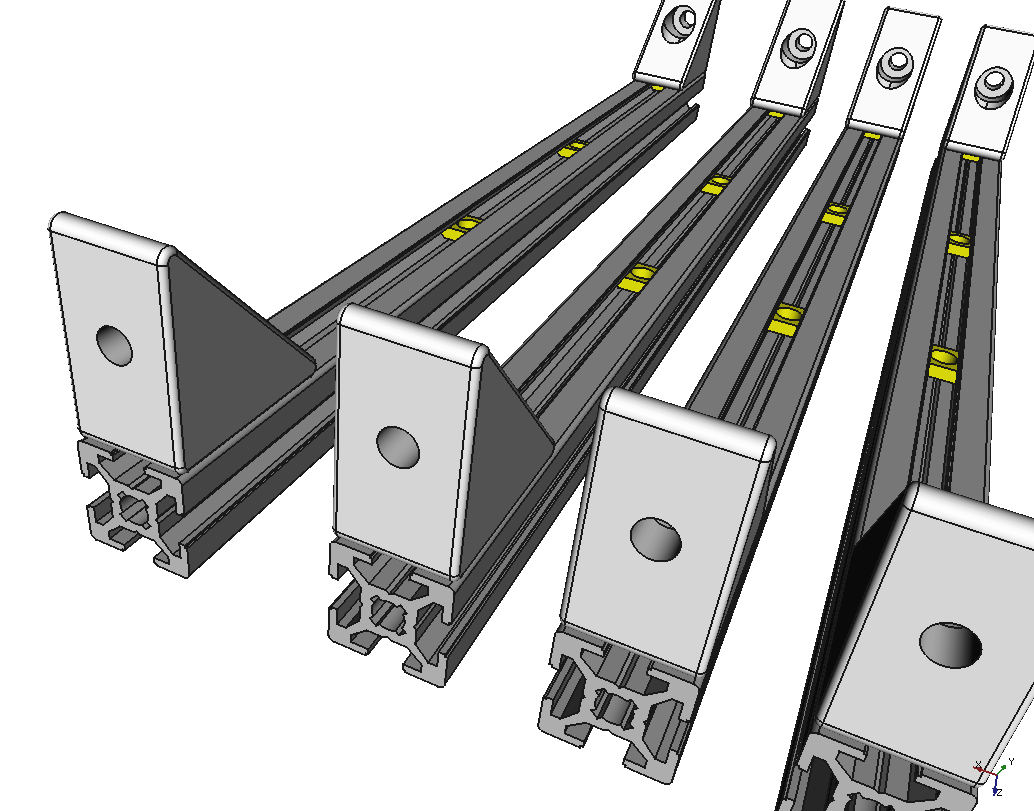
boxframe/buildinstructional/upright/corner9.png
