CollectiveOpenSourceHardware/LibreSolarBox/boxframe/buildinstructional/upright/corner9b.png

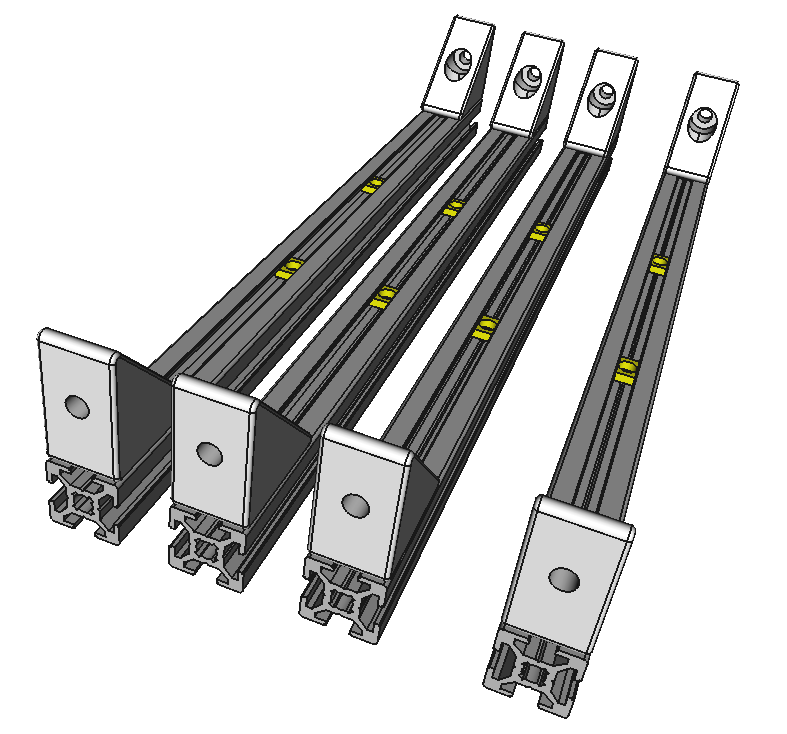
boxframe/buildinstructional/upright/corner9b.png
