CollectiveOpenSourceHardware/LibreSolarBox/upklib_v2/schraubenmuttern/images/m6nutplate_measure.png

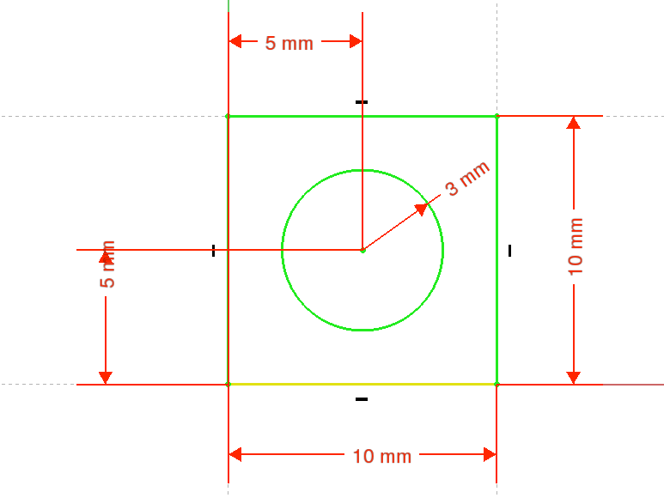
upklib_v2/schraubenmuttern/images/m6nutplate_measure.png
