CollectiveOpenSourceHardware/LibreSolarBox/upklib_v2/verbinder/images/lcon_measure.png

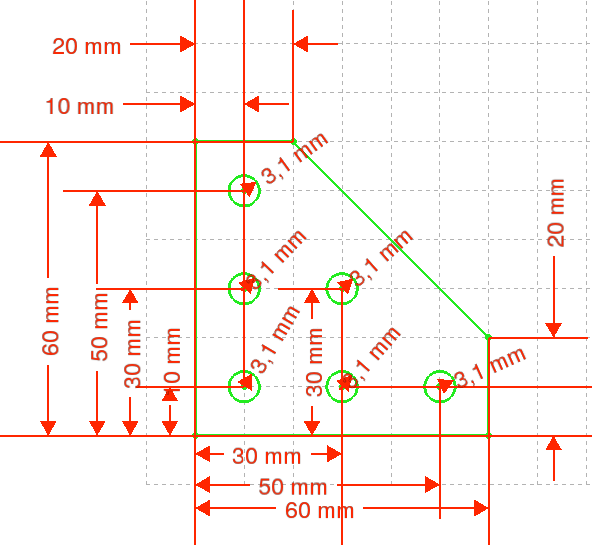
upklib_v2/verbinder/images/lcon_measure.png
