CollectiveOpenSourceHardware/LibreSolarBox/upklib_v2/verbinder/images/tcon_measure.png

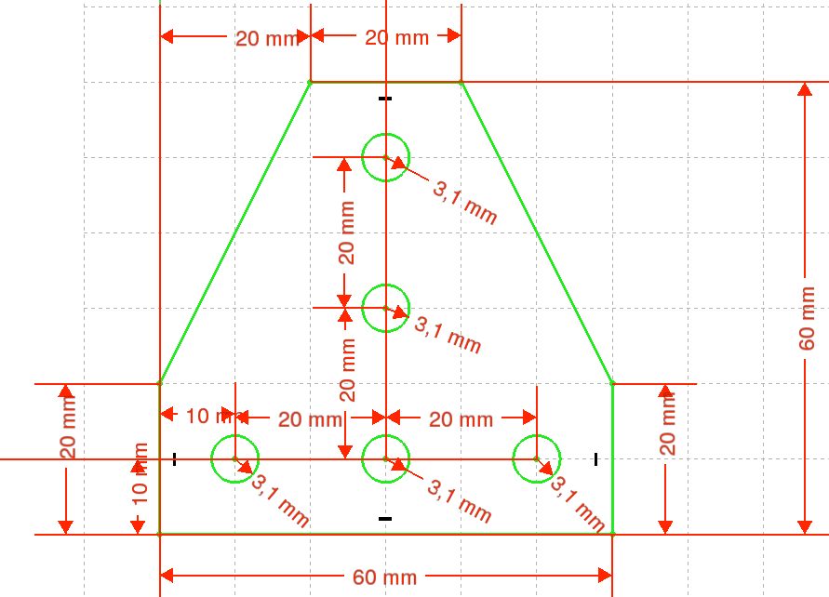
upklib_v2/verbinder/images/tcon_measure.png
